bretbouchard/kicad-agent/.planning/phases/233-swift-schematic-svg-renderer/233-01-PLAN.md

---
phase: 233
plan: 01
title: Swift-native schematic SVG renderer
type: execute
wave: 1
depends_on: []
autonomous: true
files_modified:
  - macos-app/Sources/Volta/Rendering/
  - macos-app/Sources/Volta/Views/InlineRendering/SchematicPreviewView.swift
must_haves:
  - Swift SVG renderer emits valid SVG for any .kicad_sch
  - Live preview updates as user edits (no kicad-cli dependency)
  - Renders symbols, wires, labels, power symbols
---

# Plan 233-01: Swift Schematic SVG Renderer

<objective>
Replace the kicad-cli-dependent SVG export with a Swift-native renderer.
The macOS app should be able to render any schematic entirely on-device,
without shelling out to kicad-cli. Required for App Store sandbox
compatibility (gap F1 in GAP-ANALYSIS-CURRENT.md).

## Approach

1. Audit existing `macos-app/Sources/Volta/Views/InlineRendering/SwiftSVGRenderer.swift`
2. Confirm coverage: symbols, wires, labels, power symbols, hierarchy
3. Wire into `SchematicPreviewView` for live preview
4. Add regression tests for representative schematics
5. Verify no kicad-cli subprocess calls in renderer path

## Status

SwiftSVGRenderer.swift exists from Phase 238 sweep. Audit + wire-up
work is small.
