bretbouchard/kicad-agent/.planning/phases/237-safe-sync-pcb-from-schematic/237-01-PLAN.md

---
phase: 237
plan: 01
type: execute
wave: 1
depends_on: []
files_modified:
  - macos-app/Sources/Volta/Parsing/VoltaEngineRemaining.swift
  - macos-app/Sources/Volta/Parsing/PCBParser.swift
  - macos-app/Sources/Volta/State/OpJournal.swift
autonomous: true
requirements:
  - SYNC-01
  - SYNC-02
  - SYNC-03
must_haves:
  truths:
    - safe_sync_pcb_from_schematic diffs the schematic against the PCB and replays changes
    - Footprint additions, removals, moves, and value updates propagate from .kicad_sch to .kicad_pcb
    - Op journal records the sync as a single transaction with one-shot rollback
  artifacts:
    - path: macos-app/Sources/Volta/Parsing/VoltaEngineRemaining.swift
      provides: "safe_sync_pcb_from_schematic returns a real diff + replay, not a stub message"
    - path: macos-app/Sources/Volta/Parsing/SchematicPcbDiffer.swift
      provides: "Diff algorithm matching components by reference, applying net/footprint changes"
  key_links:
    - from: SchematicPcbDiffer
      to: PCBParser
      via: "reads current PCB, compares to schematic, emits mutation ops"
    - from: VoltaEngineRemaining.swift
      to: OpJournal
      via: "journals sync as a transaction so the user can undo one-shot"

<threat_model>
## Trust Boundaries
| Boundary | Description |
|---|---|
| local filesystem | KiCad files are user-owned; no trust boundary |
| LLM-emitted op sequence | Sync may be triggered by a chain of chat ops; no new attack surface |

## STRIDE Threat Register
| Threat ID | Category | Component | Disposition | Mitigation Plan |
|---|---|---|---|---|
| T-237-01 | Tampering | PCB diff emit | Mitigate | Verify footprint placement bounds before applying move |
| T-237-02 | Repudiation | sync transaction | Mitigate | Journal records before/after SHA for audit |

## Stupid-Proof Verification
- User-stupid: undo is one-shot (no partial-rollback damage)
- Magic-stupid: chat-driven sync produces a visible before/after diff
</threat_model>

<context>
## Why this exists
Gap A2 from GAP-ANALYSIS-CURRENT.md. `safe_sync_pcb_from_schematic` is currently a stub returning a placeholder message (VoltaEngineRemaining.swift:933-942). Without a working sync, the iterate loop is broken: the user can edit the schematic but the PCB stays stale. This kills the "describe → refine → ship" flow.

## Background
Phase 235 was marked Complete on 2026-07-14 but did not actually implement this op. The current op just parses the PCB and returns a message saying "full sync requires schematic+PCB pair."

## Scope (in)
- A diff algorithm that takes (schematicIR, pcbIR) and emits a sequence of atomic PCB mutations
- Mutate: footprint add/remove/move (by ref), net rename, value update
- Journal the whole sync as one transaction (one-shot undo)
- Wire into VoltaEngineRemaining.swift's safe_sync_pcb_from_schematic

## Scope (out)
- Hierarchical sheet sync (Phase 2 follow-up)
- Annotation re-numbering sync (already in `safe_annotate`)
- DRC re-validation post-sync (the user runs DRC explicitly)
</context>

<tasks>

### Task 1: SchematicPcbDiffer
**Files:**
- `macos-app/Sources/Volta/Parsing/SchematicPcbDiffer.swift` (new, ~200 LOC)

**Implementation:**
- Inputs: `SchematicIR` (components + nets) and `PCBIR` (footprints + tracks + vias)
- Match components by reference designator
- For each mismatch, emit one of:
  - `.addFootprint(ref, footprint, position, value)` if schematic has it but PCB doesn't
  - `.removeFootprint(ref)` if PCB has it but schematic doesn't
  - `.moveFootprint(ref, position)` if positions differ
  - `.updateValue(ref, value)` if values differ
  - `.updateNet(pin, net)` if pin-to-net mapping changed
- Output: `[DifferOp]`

**Tests:** Property tests with synthetic (schematic, pcb) pairs.

### Task 2: Sync executor
**Files:**
- `macos-app/Sources/Volta/Parsing/SchematicPcbSync.swift` (new, ~150 LOC)

**Implementation:**
- Open a journal transaction
- Apply each `DifferOp` via the existing op registry (`add_footprint`, `move_footprint`, etc.)
- On any failure: roll back the transaction, return the error
- On success: return the diff summary `{added, removed, moved, valueUpdated, netUpdated}`

### Task 3: Wire into safe_sync_pcb_from_schematic
**Files:**
- `macos-app/Sources/Volta/Parsing/VoltaEngineRemaining.swift:933-942`

**Implementation:**
- Replace the stub `execute` body with: read schematic + PCB, run Differ, run Sync, return summary
- Make sure the fileURL points at the PCB and params include `schematic_path` for the schematic file

### Task 4: Tests
**Files:**
- `macos-app/Tests/VoltaTests/SchematicPcbDifferTests.swift` (new)
- `macos-app/Tests/VoltaTests/SchematicPcbSyncTests.swift` (new)

**Coverage target:** 80% on the new files.
</tasks>

<verification>
## Success Criteria
1. Chat-driven op: "I changed R1 to 4.7k in the schematic" → `safe_sync_pcb_from_schematic` updates the PCB R1 footprint's value field, returns `{valueUpdated: 1}`
2. Sync is journaled as one transaction: `undo` reverts the entire sync atomically
3. Test coverage ≥80% on the new files
4. No regressions in existing op tests
</verification>
