bretbouchard/kicad-agent/.planning/phases/233-swift-schematic-svg-renderer/233-01-SUMMARY.md

# Phase 233 — Swift Schematic SVG Renderer Summary

**Date:** 2026-07-15
**Plan:** 233-01-PLAN.md
**Status:** PLANNED

## Status

Plan created. SwiftSVGRenderer.swift exists from Phase 238 sweep; needs
audit + wire-up work. Estimated 1-2 days.

## Next steps

- Audit SwiftSVGRenderer.swift for coverage
- Wire into SchematicPreviewView for live preview
- Add regression tests
- Verify no kicad-cli subprocess calls

## Resolution state

PLANNED — ADDED-AS-PHASE
