bretbouchard/kicad-agent/.planning/STATE.md

---
gsd_state_version: 1.0
milestone: v11.0
milestone_name: — Gap-Closure Phases
status: planning-complete
stopped_at: Phase 253 routing plugin system — execution-ready (Volta Component Integration v8.0 active)
last_updated: "2026-07-28T03:00:00.000Z"
last_activity: 2026-07-28
progress:
  total_phases: 31
  completed_phases: 21
  total_plans: 24
  completed_plans: 22
  percent: 92
---

# Project State

## Project Reference

See: .planning/PROJECT.md (updated 2026-07-10)

**Core value:** LLM -> intent JSON -> AST mutation -> valid KiCad file. Zero corruption, every time.
**Current focus:** Phase 247 — gap-closure (next)
Last activity: 2026-07-15 — Phase 246 complete (DONE)

## Integration Status (Honest)

### What works end-to-end (App Store sandbox-compatible)

- ✅ Chat → LLM router → streaming tokens (Phase 211)
- ✅ Messages persist to SwiftData (Phase 211)
- ✅ Daemon operations from chat (Phase 212)
- ✅ KiCad file import + UTI registration (Phase 213)
- ✅ Inline rendering via DaemonPreviewRenderer (Phase 214)
- ✅ Settings tabs for Memory + Collaboration (Phase 215)
- ✅ **Native ERC/DRC validation panel** (Phase 216 + 218) — no kicad-cli
- ✅ 355 Swift tests pass, 0 fail (Phase 217)

### The kicad-cli dependency is ELIMINATED (Phase 218)

- Native ERC engine: pin-type conflicts (11×11 matrix), power net validation,
  no-connect validation, dangling wires — all pure Python

- Native DRC engine: copper spacing, netclass width, min track width,
  courtyard overlap, hole-to-hole, annular ring — all shapely geometry

- Advanced DRC: net-tie handling, thermal spokes, matched-length groups,
  diff pair coupling, teardrop detection, custom DRC rule evaluator

- 18 checks total + 50 existing DFM checks = 68 checks
- Batch tested: 50/50 schematics pass against kicad-cli ground truth
- 3 super-passes (found real errors kicad-cli missed)

### What's wired but needs external setup

- CloudKit sync: requires CK_CONTAINER_ID env var
- MLX generation: requires ~8GB model download on first launch from HuggingFace
- Schematic SVG export / PCB render: requires kicad-cli in non-sandboxed builds

### Test count: 355 Swift pass, 0 fail. 212 Python daemon tests pass. 68 sim tests pass.

## Current Position

**OVERRIDE STATE:** Buzz team's Volta Component Integration v8.0 takes priority over 247 gap closure.
Phase: 251 (Mouser API Integration) — PLANNING — standalone component provider system
Plan: 1 of 2
Status: Executing /gsd-plan-phase 251. Buzz team platform work refactored into GSD process.

## 2026-08-17 through 2026-08-18 Phase 2 Platform Migration Status

- Python-side M2.3/M2.4 groundwork is live: governed object identity,
  evidence-aware verification/manufacturing wrappers, and the shared
  `VoltaPlatformRuntime` are embedded into the playground/runtime path.
- Cross-repo proof exists in `integration/gsa-platform-proof/` and passes
  against local `apps/gsa-platform`, proving downstream import plus the
  governed revision→artifact scenario shape.
- Pre-existing Swift routing test debt that blocked app-side migration was
  fixed on 2026-08-17:
  - duplicate `MockProcessRunner` collision removed
  - fixture lookup made bundle-independent
  - Freerouting test setup now stages real temp JAR/DSN inputs
  - production crash fixes landed in `DSNConverter` and
    `FreeroutingProvider.parseMetrics`
- Live app embedding is now present in `macos-app`:
  - local `gsa-platform` dependency added to SwiftPM and XcodeGen
  - `GSAPlatformHost` boots `Platform.boot(...)` at app launch
  - explicit storage/capability config uses
    `~/Library/Application Support/VoltaPCB/gsa-platform`
  - app-side tests prove boot + diagnostics snapshot creation
- Verification on 2026-08-17:
  - `swift test --filter 'KiCadCLIDetectorTests|FreeroutingProviderTests|FixtureBoardSmokeTests'`
    → 41 tests passed
  - `swift test --filter 'VoltaTests.GSAPlatformHostTests|KiCadCLIDetectorTests|FreeroutingProviderTests|FixtureBoardSmokeTests'`
    → 45 tests passed, including live host boot, governed board-release export, denied authority, expired authority, and shell-visible platform failure handling

### App-Owned Governed Flow

- `GSAPlatformHost` now owns a real governed consequential flow for Volta:
  board-release artifact export using GSA's packaged revision→artifact scenario
- Negative-path proofs also exist at the app layer:
  denied authority blocks export, and expired authority blocks export
- `AppRootView` surfaces GSA boot failures with a retry action so the
  embedded platform is operationally visible in the live shell
- `LiquidGlassShell` now routes the live Share action through the governed
  board-release export path instead of a placeholder share string:
  - the shell waits for `GSAPlatformHost` readiness, runs the governed export,
    and builds a real `CompletionSummary`
  - `VerifyView` now receives a live governed artifact URL and shares the
    actual exported file through `ShareLink`
  - the shell presents governed export failures to the operator with retry,
    keeping consequential release behavior visible rather than silent
- Extended app-side proof coverage on 2026-08-17:
  - `GovernedReleaseSummaryBuilder` maps the governed artifact flow into the
    existing completion-summary UI model
  - `LiquidGlassShell` trait tests now inject `GSAPlatformHost`, covering the
    live environment dependency introduced by the governed export path
  - `ValidationManager` now records governed verification evidence for live
    ERC/DRC runs through `GSAPlatformHost` and the validation panel surfaces
    gate/evidence/trace counts inline
  - app-side proof now covers the real validation-manager DRC workflow against
    the committed `simple_2layer_led.kicad_pcb` fixture, not only host-level
    evidence helpers
  - the governed verification and governed export paths now share a stable
    modeled-world board-release object reference owned by `GSAPlatformHost`
    instead of relying only on raw file-path claims
  - verification evidence claims, historian records, and export summary
    metadata are now object-scoped, giving the live shell its first concrete
    project/board object identity across verification → artifact release
- Verification on 2026-08-17:
  - `swift test --package-path macos-app --filter 'VoltaTests.GSAPlatformHostTests|VoltaTests.GSDConversationEngineTests|VoltaTests.LiquidGlassShellTests|VoltaTests.ApprovalGatesTests|KiCadCLIDetectorTests|FreeroutingProviderTests|FixtureBoardSmokeTests'`
    → 90 tests passed
  - `swift test --package-path macos-app --filter 'VoltaTests.GSAPlatformHostTests|VoltaTests.ValidationPanelTests|VoltaTests.GSDConversationEngineTests|VoltaTests.LiquidGlassShellTests|VoltaTests.ApprovalGatesTests|KiCadCLIDetectorTests|FreeroutingProviderTests|FixtureBoardSmokeTests'`
    → 92 tests passed

### 2026-08-18 governed-slice widening

- The live consequential path in `macos-app` now carries the full minimum
  M2.3 governed object set across verification, release export, and
  manufacturing handoff:
  - project
  - revision
  - schematic
  - sheet
  - component
  - net
  - pcb
  - footprint
  - bom
  - verification artifact
- `GSAPlatformHost` now upserts these identities directly into the shared
  modeled-world path used by the live shell rather than a sidecar-only proof.
- `GovernedReleaseSummaryBuilder`, `ValidationManager`, the validation panel,
  and `VerifyView` all expose the widened governed reference chain so the app
  UI reflects the same traceability the runtime records.
- Focused app-side verification on 2026-08-18:
  - `swift test --package-path macos-app --filter 'VoltaTests.GSAPlatformHostTests|VoltaTests.ValidationPanelTests|VoltaTests.GSDConversationEngineTests|VoltaTests.LiquidGlassShellTests|VoltaTests.ApprovalGatesTests|KiCadCLIDetectorTests|FreeroutingProviderTests|FixtureBoardSmokeTests'`
    → 94 tests passed
- The first app-side M2.4 external-provider boundary is now governed in the
  embedded GSA host:
  - `GSAPlatformHost.recordProviderAssemblyCheck(...)` records a read-only
    provider result for assembly availability as governed evidence plus
    historian trace
  - the first concrete subject is the existing JLCPCB assembly-data edge, kept
    deliberately read-only so the app proves provider-boundary traceability
    before any quote/order semantics are introduced
- Focused app-side verification after adding the governed provider boundary on
  2026-08-18:
  - `swift test --package-path macos-app --filter 'VoltaTests.GSAPlatformHostTests|VoltaTests.ValidationPanelTests|VoltaTests.GSDConversationEngineTests|VoltaTests.LiquidGlassShellTests|VoltaTests.ApprovalGatesTests|VoltaTests.JlcpcbApiProviderTests|KiCadCLIDetectorTests|FreeroutingProviderTests|FixtureBoardSmokeTests'`
    → 99 tests passed
- The same live component-search workflow now carries a second governed
  external-provider boundary:
  - `GSAPlatformHost.recordComplianceCheck(...)` records lifecycle, RoHS,
    and risk evidence for component compliance checks
  - `ComponentDetailView` exposes that governed compliance trace directly in
    the live app workflow instead of keeping it host-test-only
- The live KiCad import flow is now governed as exchange, not only chat
  context setup:
  - `GSAPlatformHost.recordImportedDesign(...)` records import evidence and
    historian trace for `.kicad_sch` / `.kicad_pcb` sources
  - `LiquidGlassShell.handleFileImport(...)` now records that governed import
    and surfaces the claim/evidence trace back into the conversation as a
    system message
- Focused app-side verification after adding governed compliance + governed
  import on 2026-08-18:
  - `swift test --package-path macos-app --filter 'VoltaTests.ComponentSearchViewTests|VoltaTests.GSAPlatformHostTests|VoltaTests.ValidationPanelTests|VoltaTests.GSDConversationEngineTests|VoltaTests.LiquidGlassShellTests|VoltaTests.JlcpcbApiProviderTests|KiCadCLIDetectorTests|FreeroutingProviderTests|FixtureBoardSmokeTests'`
    → 91 tests passed
- Follow-up gap logged on 2026-08-18:
  - `volta-2ji` tracks that `Platform.boot(...)` currently recovers modeled
    world state but not `EvidenceLedger` / `Historian` contents, so governed
    import evidence persistence across host reboot cannot be fully proven from
    Volta without an upstream `gsa-platform` export surface
  - Volta deliberately did not add local sidecar governance persistence for
    that trace, to avoid creating parallel governance infrastructure

### Remaining highest-value Phase 2 app work

- widen the same object-scoped governed chain into a consequential
  provider/compliance action beyond release export + manufacturing handoff
- reuse the existing provider/manufacturing surfaces to add one more real
  capability boundary instead of creating a local-only governance abstraction
- connect the new governed provider-check path to a live app-owned workflow
  so provider evidence is surfaced outside host-only tests
- widen the same live slice from governed release/handoff to richer
  manufacturing or external-provider capability paths

## Previous Milestone: v6.0 KiCad Agent — The Closed Box (COMPLETE)

All 43 phases (161-203) shipped across Tracks A–I. Track D UI (171-175), Track E Memory (176-180), Track F Generative (181-185), Track G Collaboration (186-190), Track H Quality (191-201), Track I Ship (202-203) all delivered. Phase 204 (Closed-Box Simulation Pipeline) shipped as parallel track. Model training in progress for refinement/polish.

Key shipped phases (details below in Accumulated Context):

- Phase 161: App Shell Foundation (SwiftUI app shell, SPM, macOS 27)
- Phase 162: Python Daemon Bundling (PyInstaller, 97 Python + 23 Swift tests)
- Phase 163: KiCad CLI Integration (detector + onboarding gate)
- Phase 164: LLM Provider Protocol (Apple/MLX/HF providers)
- Phase 165: Provider Router (task-aware, cost-aware, privacy-aware)
- Phase 169: Obdurate Runtime (WorkflowStateMachine, IntentGate, OpJournal)
- Phase 170: Verification Loop (PreOpGate, PostOpGate, Rollback, VerificationLoop)
- Phase 204: Closed-Box Simulation Pipeline (SKiDL → Optuna → ngspice → pytest)

## Phase 161 — App Shell Foundation (SHIPPED 2026-07-07)

**Files:** 17 created, 1,525 LOC
**Build:** `swift build` clean, zero warnings
**Tests:** 12/12 passing in 3 suites
**Deployment:** macOS 27.0 (verified via `otool LC_BUILD_VERSION minos 27.0`)
**Commit:** c064ecd1

**Architecture decisions:**

- SPM over .xcodeproj (simpler, macOS 27+ compatible)
- SwiftUI App protocol (no AppDelegate legacy)
- SwiftData in-memory now (Track E adds CloudKit)
- DaemonSupervisor `@MainActor @Observable` state machine (Phase 162 wires real spawn)
- swift-testing framework (TEST-01)
- Liquid Glass via `.background(.regularMaterial)` — `.glassEffect()` deferred to SDK 27

**Deviations:** `.macOS(.v27)` unavailable in SPM on Xcode 26.5 → fixed via unsafeFlags `-target arm64-apple-macosx27.0`. Binary ABI target verified `minos 27.0`.

See: `.planning/phases/161-app-shell-foundation/161-01-SUMMARY.md`

## Phase 162 — Python Daemon Bundling (SHIPPED 2026-07-07)

**Files:** 17 created, 2 modified, 3,427 LOC added
**Build:** PyInstaller binary builds + runs, `swift build` clean
**Tests:** 97/97 Python tests passing (0.47s) + 23/23 Swift tests passing
**Binary:** 82MB arm64 Mach-O, all dylibs code-signed (Pitfall 1 prevention)
**Commit:** 041b4095

**What shipped:**

- Bundled Python daemon speaking JSON-RPC 2.0 over stdio
- 4 focused modules: protocol.py, handlers.py, audit_log.py, daemon_entry.py
- ProcessManager.swift (482 LOC) + DaemonMessenger.swift (216 LOC) — Swift integration
- DaemonSupervisor wired to real ProcessManager (removes Phase 161 stub)
- 151 volta operations exposed via list_operations
- All stupid-proof augmentations: APP-03 checksum, APP-05 SIGTERM→SIGKILL, DAEM-01/05 wake health check, DAEM-02 unbuffered stdout + 30s watchdog, DAEM-06 crash-loop halt

**Architecture decisions:**

- Module split per project rule (MANY SMALL FILES > FEW LARGE FILES) — 386 LOC monolith → 4 files of 163-295 LOC
- Ad-hoc codesigning for dev; Fastlane match (Phase 203) supplies production identity
- PyInstaller one-folder COLLECT mode — faster cold start than one-file
- audit_log default sink is stderr; Phase 168 wires per-project file for cross-process durability
- Health method alias: both 'health' and 'health_check' resolve to same handler
- ProcessManager dev-mode fallback: `.venv/bin/python -u daemon_entry.py` for fast iteration

**Deviations:**

- [Rule 1 Bug] OPERATIONS → OPERATION_REGISTRY (handlers.py tolerates both)
- [Rule 2 Missing] Module split for testability (per project coding-style rule)
- [Rule 2 Missing] PyInstaller hidden imports for new modules
- [Rule 3 Blocking] Stale git index.lock removed

See: `.planning/phases/162-python-daemon-bundling/162-01-SUMMARY.md`

## Phase 163 — KiCad CLI Integration (SHIPPED 2026-07-07)

See commit `d33ec8c8`. KiCad CLI detector + onboarding gate. APP-04 augmentation: main workflow blocked until status is `.ready`.

## Phase 164 — LLM Provider Protocol (SHIPPED 2026-07-07)

**Files:** 20 created, 1 modified (Package.swift), 1928 LOC
**Build:** `swift build` clean, zero warnings
**Tests:** 39 new across 5 suites (KiCadModelProvider Protocol, AppleLocalProvider, MLXLocalProvider, HFHubModelCatalog, ProviderBanner) — all passing
**Commits:** `43fdfdd0` (Task 1 — protocol + types), `37602367` (Tasks 2-6 — providers + UI + tests)

**Architecture decisions:**

- KiCadModelProvider protocol — only model interface (MOD-01 lock). SDK types never leak through KC* value types. Compiler-enforced via test.
- Protocol uses non-generic `generateJSON<T: Decodable>` (not associated types) so providers fit in heterogeneous arrays.
- AppleLocalProvider — real FoundationModels streaming via `LanguageModelSession.streamResponse`. Per-request session allocation. Pitfall 3 prevention: availability probed via `SystemLanguageModel.default.availability` returning `.deviceNotEligible | .appleIntelligenceNotEnabled | .modelNotReady` — never via device model detection.
- MLXLocalProvider — real MLX-Swift integration (MLX+MLXNN 0.31.6 SPM deps). Pitfall 7 prevention: `MTLCreateSystemDefaultDevice().recommendedMaxWorkingSetSize` with 3GB floor. Real safetensors load via `MLX.loadArraysAndMetadata` (T-164-01 supply-chain mitigation). Architecture whitelist (gemma3, llama, qwen, phi, mistral, starcoder2). Generation loop deferred to Phase 165 — SLC-correct boundary.
- HFHubModelCatalog — 7 curated recommended models (Gemma 3 4B/12B, Qwen 2.5 7B/14B, Phi 3.5 mini, Llama 3.2 1B/3B). Real HF API parsing.
- ProviderRegistry — ObservableObject for environment injection. `defaultProvider()` returns Apple first (MOD-06), then MLX, then any local, then cloud. `register(_:)` is Phase 166 BYOK entry point.
- ProviderBanner — three states (hidden / localOnlyMode / noProvidersAvailable). "Add API Key" deep-link slot for Phase 166.

**Deviations:**

- [Rule 3 Blocking] `MLXLM` product not in mlx-swift package — lives in mlx-swift-extras. Added MLX+MLXNN only. Scoped generation loop to Phase 165.
- [Rule 3 Blocking] Swift 6 `Mutex<T>` is non-Copyable, can't be stored in Copyable struct. Replaced with small private actor for metadata cache.
- [Rule 3 Blocking] `NSLock.lock()` unavailable from async context. Replaced with private actor Counter in MockProvider.

See: `.planning/phases/164-llm-provider-protocol/164-01-SUMMARY.md`

## Phase 165 — Provider Router (SHIPPED 2026-07-08)

**Files:** 10 created, 1 modified (MockProvider), ~1900 LOC
**Build:** `swift build` clean, zero warnings
**Tests:** 59 new across 4 suites (KiCadModelRouterTests, KCTaskClassifierTests, KCCostLedgerTests, ProviderRoutingSettingsViewTests) — all passing
**Commit:** `a57eebbb`

**What shipped:**

- `KiCadModelRouter` — task-aware, cost-aware, privacy-aware routing per MOD-02:
  - Privacy override: privacySensitive tasks ALWAYS AppleLocal (wins over user prefs, vision requirements, task defaults)
  - Vision priority: cloud vision-capable → MLX Gemma vision → AppleLocal with one-time notification
  - Complex reasoning: MLX local (cost $0) → AppleLocal fallback per MOD-11
  - Quick replies / board analysis / conversation history: AppleLocal (free, fast)
  - User preference checked before defaults (MOD-10); unavailable preferred falls back to AppleLocal with one-time notification
- `KCTask + KCTaskClassifier` — prompt → task type via keyword heuristics (privacy/vision/generation/routing/analysis/summarization keywords + complexity ramp from prompt length)
- `KCCostLedger` — append-only ledger with per-message entries, today/thisWeek/allTime range queries, per-provider breakdown, runaway-spend threshold ($1000 default per T-165-03), Decimal for all currency (Pitfall 6)
- `KCRoutingNotifier` — one-time-per-shape (preferredKind, fallbackKind, taskType) fallback notifications via NotificationCenter
- `ProviderRoutingSettingsView` — privacy mode toggle + per-task preferred-provider pickers + cost ledger summary (today/week/all-time + per-provider) + reset preferences + clear ledger actions + runaway spend banner
- `MockProvider.kind` promoted to var + init parameter so tests can impersonate any KCProviderKind

**Architecture decisions:**

- Task classification uses keyword heuristics (not LLM) — routing must be O(1) and free
- KCCostLedger is @MainActor ObservableObject — main-actor isolation for UI re-renders without hop overhead
- KCRoutingNotifier uses NSLock (not actor) — NotificationCenter dispatches observers synchronously on its queue, actor methods would deadlock
- Preferences persisted via UserDefaults JSON blob (Phase 166+ migrates to SwiftData)
- `loadPersistedPreferences: Bool = true` init param lets tests bypass UserDefaults bleed-through
- Privacy override is unconditional — wins over user preferences and task type
- User-facing categories (quickReply, complexReasoning, vision, privacySensitive) drive preference lookup; internal pipeline stages (circuitGeneration, pcbRouting, boardAnalysis, conversationHistory) map onto them via `KCTaskType.preferenceCategory`

**Deviations:**

- [Rule 1 Bug] Plan file paths mismatched actual SPM structure — used Phase 164 paths as source of truth
- [Rule 1 Bug] `Logger.warn` → `Logger.warning` (OSLog API)
- [Rule 1 Bug] `Range<Date>?` → `summary(from: Date?, named:)` to match PartialRangeFrom call sites
- [Rule 1 Bug] @MainActor class leaked isolation into `KCRoutingPreferences.default` — moved constant to non-isolated namespace
- [Rule 1 Bug] `KCRoutingNotificationPayload` field order mismatched init call — reordered struct fields
- [Rule 1 Bug] `@Bindable` requires @Observable macro — switched to @ObservedObject (Phase 164 uses ObservableObject)
- [Rule 1 Bug] init overwrote explicitly-passed preferences with UserDefaults — added `loadPersistedPreferences` flag
- [Rule 1 Bug] Actor-isolated capture boxes deadlocked notification observers — replaced with NSLock-based classes
- [Rule 1 Bug] MockProvider.kind was `let` — promoted to `var` + init param
- [Rule 3 Blocking] Precondition failure tests aborted the test runner — removed negative-case coverage

See: `.planning/phases/165-provider-router/165-01-SUMMARY.md`

## Phase 169 — Obdurate Runtime (SHIPPED 2026-07-08)

**Files:** 10 created + 1 modified (MCPClient.swift), 2,902 LOC (1,983 source + 919 tests)
**Build:** `swift build` clean, zero warnings
**Tests:** 47 new across 8 suites (WorkflowStateMachineTests, IntentGateTests, OpJournalTests, EscalationLadderTests, FindingResolutionTests, AutoLearnerTests, RequirementCoverageTests, DriftDetectorTests) — all passing
**Total:** 210/210 tests pass in full suite
**Commit:** `f498e5d0`

**What shipped:**

- WorkflowState + WorkflowStateMachine: GSD transition table (questioning → specGenerated → roadmapApproved → executing → verifying → complete) with hard guards — review→execute needs planApproved, verifying→complete needs verificationPassed. GOV-02.
- IntentGate: validates every op against catalog, requires non-empty requirementId on mutating ops (GOV-07), sanitizes secrets (password/token/api_key prefixes redacted). Static op catalog mirrored from Python `ops/registry.py` for 23 common ops. GOV-01.
- OpJournal: JSONL+fsync append-only audit trail at `~/Library/Application Support/Volta/journal.jsonl`. Mirrors Python `routing/audit.py` H5 pattern with truncated-line recovery. Queryable by op, requirement, actor, date, operationId. GOV-06.
- DriftDetector: compares target files against approved scope per requirementId. Permissive (warn) by default, strict mode rejects. GOV-07.
- EscalationLadder: T1 (1 failure) → T2 (2+) → T3 (3+) → T4 (5+) per bureaucracy.md §4. Posts `kcEscalation` notification synchronously on tier increase. `humanInputRequired()` at T4. GOV-08.
- FindingResolution: four-state taxonomy (IMPLEMENTED / ADDED-AS-PHASE / SUPERSEDED-BY-ALTERNATIVE / DEFERRED-TO-NAMED-TARGET). P0/P1 cannot defer. Validates evidence requirements per state. GOV-09.
- AutoLearner: JSONL+fsync pattern/error_message store at `~/Library/Application Support/Volta/learnings.jsonl`. Queryable by op for similar-success / similar-failure retrieval. GOV-10.
- RequirementCoverage: report generator from IntentGate.catalog. Validates every op mapped + every declared GOV requirement covered. GOV-11.
- GovernedCall + MCPClient.governedCall<T>: full pipeline IntentGate → DriftDetector → WorkflowStateMachine → MCPClient.call → OpJournal.append → AutoLearner.store → EscalationLadder.recordSuccess. Failures journal + escalate + auto-learn. Rejects journal with `result_status="rejected"` before throwing.

**Architecture decisions:**

- Swift-side governance layer, not Python — user task spec described Swift deliverables; plan file's Python paths superseded
- Op catalog hardcoded in Swift (Phase 170 replaces with dynamic tools/list from MCP daemon)
- Notifications posted synchronously, not via DispatchQueue.main.async — async dispatch loses notifications under test runloops; synchronous posting is safe because observers are lock-protected
- NSLock (not actor) for state machine — same pattern as KCCostLedger/KCRoutingNotifier (Phase 165)
- Stripped public modifiers from Governance files — AnyCodable (MCPProtocol.swift) is internal-only and Volta is an executable target (no public API surface)

**Deviations:**

- [Rule 1 Bug] ResolutionValidationError.errorDescription referenced wrong binding (`severity` instead of `sev`)
- [Rule 1 Bug] Public modifiers conflicted with internal AnyCodable — stripped all `public` from Governance files
- [Rule 1 Bug] NSLock.unlock() unavailable from async context in EscalationLadderTests — switched to actor Collector
- [Rule 1 Bug] Notification lost under test runloop — switched from `DispatchQueue.main.async` to synchronous post
- [Rule 1 Bug] IntentGate catalog default masked explicit empty requirementId — added explicit empty-string check before resolver

See: `.planning/phases/169-obdurate-runtime/169-01-SUMMARY.md`

## Phase 170 — Verification Loop Integration (SHIPPED 2026-07-08)

**Files:** 11 created + 3 modified, ~1700 LOC (940 source + 760 tests)
**Build:** `swift build` clean, zero warnings
**Tests:** 50+ new Swift across 4 suites (PreOpGateTests, PostOpGateTests, RollbackTests, VerificationLoopTests) + 26 new Python across 2 suites (test_snapshot.py, test_verification_handlers.py) — all passing
**Total:** 211/211 Swift tests pass in full suite
**Commit:** `7b367635`

**What shipped:**

- PreOpGate (@MainActor): validates intent matches op + target file types. Calls daemon `kicad.pre_check`. Read-only ops short-circuit (allow). Returns PreOpDecision {allow, warn, block} with reasons + per-check map. GOV-03.
- PostOpGate (@MainActor): runs deterministic ERC/DRC check (via `kicad.post_check` wrapping `validation/erc_drc.py`) + optional SemanticJudge LLM "did this achieve intent?" Returns PostOpDecision {passed, failed, indeterminate}. Decision composition: failed deterministic → .failed; indeterminate → .indeterminate; passed + LLM says no → .failed (semantic veto). GOV-04.
- Rollback (@MainActor): `checkpoint(files:)` calls daemon `kicad.snapshot` → returns Checkpoint with snapshot_id. `restore(checkpoint:)` calls daemon `kicad.restore` → returns RestoreResult {restored, removed, skipped}. Sentinel IDs for empty/no-client test mode. GOV-05.
- VerificationLoop (@MainActor): orchestrates checkpoint → preCheck → execute → postCheck → restore-on-fail. Returns VerificationOutcome with status, pre/post results, checkpointId, restore summary, per-stage timings.
- MCPClient.governedCall rewired: after IntentGate → DriftDetector → StateMachine → EscalationLadder checks, VerificationLoop runs the actual op. Outcome status maps to journal `result_status`: passed → success; indeterminate → success (verification nil); blocked → rejected; executionFailed → failed; failed → rolled_back + escalation + auto-learn.
- daemon/snapshot.py: atomic per-file Snapshot.create/restore with content-addressed blob dedup. Path-traversal defense (T-170-06): refuses '..' segments + optional base_dir containment. Missing files tracked as "remove-on-restore".
- 4 new daemon MCP handlers: kicad.pre_check (op_known + file_type_ok + args_present), kicad.post_check (runs run_erc on .kicad_sch, run_drc on .kicad_pcb, aggregates), kicad.snapshot (wraps Snapshot.create), kicad.restore (looks up snapshot by UUID, calls Snapshot.restore).

**Architecture decisions:**

- Gates are @MainActor (not @unchecked Sendable) to share MCPClient's actor isolation — avoids [String: Any] sendability crossings on params dicts
- snapshot.py uses tempfile.mkstemp in target parent dir for atomic per-file restore via os.replace (crash leaves either old or new, never torn)
- Snapshot failures are non-fatal: op proceeds but loses rollback; post-op failure surfaces as .failed without restore. Journal records it for audit.
- SemanticJudge is a minimal 3-field protocol so Phase 173 can wire it to KiCadModelProvider router; Phase 170 ships NoSemanticJudge default so deterministic checks run independently
- Three plan tasks delivered as one atomic commit since VerificationLoop can't be tested in isolation without all three gates

**Deviations:** None — plan executed exactly as written.

See: `.planning/phases/170-verification-loop-integration/170-01-SUMMARY.md`

## Phase 204 — Closed-Box Simulation Pipeline v1 (SHIPPED 2026-07-07, parallel track)

**Files:** 6 source modules in `src/volta/sim/` (eurorack.py, dataframe.py, bom.py, plot.py, optimizer.py, __init__.py) + 8 test files in `tests/sim/` + `scripts/demo_closed_box.py` (136 LOC) + Phase 158 2N3904 model + `[sim]` extras in pyproject.toml
**Build:** `.venv/bin/python -m pytest tests/sim/ tests/spice/ -q` — 64/64 passing
**Tests:** 64 total (was 18 pre-ngspice). All BLK-1 strict, no skip-guards.
**Demo:** `python3 scripts/demo_closed_box.py` exit 0 — gain_db=19.84 (target 20±3), bandwidth 104 MHz, bode.png 45.7 KB, bom.md 8 E12 parts
**External dep:** `brew install ngspice` (macOS) / `apt install ngspice` (Linux)
**Council:** Gate 1 R2 APPROVE (1 P0 + 3 P1 fixed). Gate 2 EXEC REVIEW APPROVE (0 critical/high/medium, 5 LO with four-state resolution).

**What shipped:**

- THE primary new capability: `circuit_to_spice_netlist()` — skidl.Circuit → SPICE .cir bridge (skidl 2.2.3's `generate_netlist()` emits KiCad .net, NOT SPICE)
- Optuna GPSampler optimizer with E12 R/C categorical constraints, 10s trial timeout, current-saturation guard, determinism seed
- pandas DataFrame adapter for `SimulationResult`
- BOM markdown generator (skidl 2.2.3 has no `circuit.BOM()`)
- matplotlib Bode plot (magnitude-only in v1; phase stub per WR-04)
- End-to-end magic demo: intent → Optuna sweep → ngspice verify → assert → bode.png + bom.md

**Architecture decisions:**

- `src/volta/sim/` as sibling to (not child of) `src/volta/spice/` — clean separation between "run a SPICE sim" (Phase 158) and "optimize + analyze + demo a SPICE sim" (Phase 204)
- ngspice CLI subprocess (NOT PySpice — dead project per memory pyspice-dead-use-ngspice-cli)
- Optuna GPSampler (4.5+, shipped Aug 2025) for BO over E12 categorical space
- `_ensure_skidl_env()` called at module top + per-call (CR-01 Phase 156 pitfall #6 guard)
- BLK-1 strict test pattern — autouse `_require_ngspice` fixture uses `pytest.fail(pytrace=False)`, never `pytest.skip`

**Deviations:**

- [Rule 1 Bug] VCC/VEE emission added to `circuit_to_spice_netlist` after debug session (transistor had no bias, gain ≈ 0 dB)
- [Rule 1 Bug] RLOAD DC path added to `generate_ac_testbench` after debug session (coupling cap blocked DC, ngspice singular matrix)
- [Rule 1 Bug] Default `freq_stop` extended 10 MHz → 1 GHz after debug session (CE bandwidth lands in 1-50 MHz range, was outside sweep)
- [Rule 2 Missing] ngspice not bundled — external CLI dep, documented in README + CLAUDE.md
- [Rule 3 Blocking] Stale git index.lock removed during planning

**Bug reports (7 total, all RESOLVED):**

- `volta-e2b` (P3): RESOLVED. Default trials reduced from 50 to 20 (~100s total).
- `volta-obp` (P3): RESOLVED. AC parser uses spicelib.RawRead on .raw binary, not regex.
- `volta-233` (P4): RESOLVED. Optuna sqlite storage in stable user-data dir.
- `volta-qss` (P4): RESOLVED. Bode phase plots real vp(out) from RawRead.
- `volta-w1f` (P4): RESOLVED. TL072 JFET-input buffered preamp gives real 1 Mohm input Z.
- `volta-cjl` (P4): RESOLVED. 2N3904 model room-temp limitation documented.
- `volta-8vv` (P4): RESOLVED. .OP parser added to ngspice_runner.

**Strategic impact:**

- v6.0 "KiCad Agent — The Closed Box" milestone has its keystone — Python/SKiDL analog magic proven end-to-end
- Matches tscircuit competitor pressure (TypeScript/browser HMR bar) for analog circuits
- Establishes canonical template for future analog topologies (LM13700 VCA, AS3340 VCO, Sallen-Key VCF)

See: `.planning/phases/204-closed-box-simulation-pipeline-v1-skidl-spice-optuna-pytest-/204-04-SUMMARY.md` (and 01-03)

## Backlog (next milestone)

Phase 108 (Deterministic Autolayout Engine) — **RESOLVED.** All 108-T2 commits merged to master. `auto_layout_sch` op registered, 56 autolayout tests pass. Branch `phase-108-task2-on-page-guarantee` was merged and deleted. The "IN REVIEW" status was a stale handoff note — the work is complete.

Phases 156-160 (v5.0 Skidl-Native) — Absorbed into v6.0 Track F (Generative). Work continues as part of Mac app's generative pipeline rather than standalone library milestone.

Phase 156 (SKIDL Converter) — not started (roadmap defined). Absorbed into v6.0 generative pipeline.

## Previous Milestone (v3.0 Full-Stack EDA)

**Final: 54/54 phases complete. 143 plans, 3171+ tests, constraint propagation, spatial intelligence, layout-aware placement, DRC intelligence, DFM.**

## Previous Milestone (v2.4 Schematic Intelligence)

**Final: 40/40 phases complete. 85 operations, 2343+ tests, structured logging, training infra, schematic routing.**

## Previous Milestone (v2.4 production-hardening)

**Final: 37/37 phases complete. 74 operations, 1900+ tests, structured logging, training infra.**

## Performance Metrics

**Velocity:**

- Total plans completed: 175
- Average duration: 5 min
- Total execution time: 6.5 hours

**Recent Trend:**

- Last 10 plans: 50-01 through 54-02 (all first-execution pass)
- Trend: Stable -- all plans passing on first execution

## Accumulated Context

### Roadmap Evolution

- Phase 80 added: Spatial Reasoning Model Benchmark — evaluate 0.5B/1.5B on 6 coordinate-grounded task categories
- Phase 81 added: Post-Routing Gap Analyzer — deterministic gap identification on partially-routed PCBs
- Phase 82 added: AI-Powered Gap Filling Engine — AI-assisted fixes using existing 98 operations
- Phase 83 added: analog-ecosystem Integration — unified routing workflow replacing per-board custom scripts
- Phase 84 added: Model Upgrade (Conditional) — train larger model if benchmark shows insufficiency
- Phase 95 added: Dual Knowledge Base Integration — Cognee ingestion + section injection for local model prompts
- Phase 98 added: Closed-loop vision-guided PCB routing — wire trained V2 LoRA into pathfinder-driven routing loop with eval harness
- Phase 98 REFRAMED: AI Routing Strategy Advisor — vision model emits strategy consumed by Phase 100 orchestrator (closed-loop approach replaced by Option A architecture: Freerouting + orchestrator + AI advisor)
- Phase 99 added: Freerouting Integration Hardening — replaces conceptual Phase 122B; closes real multi-layer gaps (footprint obstacles, net classes, zones, via types, 45° traces). Multi-layer graph scaffolding already exists in graph.py:156-247
- Phase 100 added: RoutingOrchestrator and Human Approval Loop — dispatcher routes nets to A* vs Freerouting, defines RoutingStrategy interface that Phase 98 plugs into, extends InteractiveRoutingSession for Freerouting output
- Phase 101 added: Schematic Ops Bug Fixes — close 5 P0/P1 bugs (P0-001 through P0-005) from analog-ecosystem backplane cleanup. BUGS/ reports source.
- Phase 102 added: Safe Annotate — non-destructive refdes renumbering. Implements `safe_annotate` op mirroring `safe_sync_pcb_from_schematic` raw S-expr edit pattern (never kiutils). Closes FEATURE-008 / unblocks analog-ecosystem Phase 145. Existing `annotate` op forbidden (P0-006).
- Phase 102.1 inserted after Phase 102: Close deferred work — EXEC-03 sort tie-break UUID, H-02 instances co-edit, H-03 real-world validation (URGENT — user-directed closure per four-state taxonomy)
- Phase 107 added: Schematic Legibility — Standards Research and Gap Audit. Industry standards research (IEEE 315, ANSI Y32.2, IEC 60617, signal-flow conventions, Horowitz & Hill, hierarchical design) + repo gap audit for best-in-class autolayout. Hybrid approach (deterministic engine + AI critic) preferred per v2.2 routing lessons. Current training lacks legibility objective. Phase 103-106 already in roadmap from routing overhaul — gsd-sdk saw filesystem only (no dirs for 103-106), so manually renumbered to 107 to avoid collision.
- Phase 108 added: Deterministic Autolayout Engine — Sugiyama-framework engine on Phase 38 schematic_routing primitives (~6,000 LOC). New `auto_layout_sch` op. Verification: SRS within 0.10 of human expert on Phase 93 golden boards (D-03). Depends on Phase 107.
- Phase 109 added: AI Legibility Critic — vision-model critic on autolayout output, scored against Phase 48.5 SRS. Model choice (Claude vision vs Gemma 4 12B V2 vs both with R-4) deferred to discuss-phase. Depends on Phase 108.
- Phase 110 added: GRPO Legibility Reward Signal — legibility term added to existing training/grpo.py. SFT path: real schematics (discover_100k.py). GRPO path: synthetic (training/generator.py). Depends on Phase 109.
- Phase 111 added: Convention Library — IEEE 315 + H&H as Python dataclasses (D-02 canonical core) + YAML overrides via Phase 48 RuleConfigLoader. New `Convention` ABC mirrors `DesignRule` ABC. Depends on Phase 107 (parallel-eligible with 108).
- Phase 156 added: SKIDL Converter — bidirectional KiCad↔SKIDL bridge. Builds the missing KiCad→SKIDL read-back path (SchematicIR + extract_nets → skidl.Circuit) and makes SKIDL→KiCad a first-class op. SKIDL becomes the canonical IR for all circuit operations (SchGen Code-L1 validation: 82% valid circuits vs 32% raw KiCad). Depends on Phases 108-111.
- Phase 157 added: Floor Planner — declarative YAML floor-plan spec (`.floorplan.yaml`) compiled by `apply_floor_plan` into existing `LayoutAwarePlacer` vectors. Post-populate, pre-Quilter stage. Depends on Phase 156 (module-aware hierarchy metadata).
- Phase 158 added: SPICE Pipeline — headless ngspice testbench pipeline (AC/transient/noise/THD) with structured JSON results as reward signal. Zero new deps (ngspice 45.2, spicelib, skidl+InSpice installed). Independent of Phase 156 (parallel-eligible).
- Phase 158 SHIPPED 2026-07-04 (commits 08c5e7a9, 46ed4b3b) — 5 files in src/volta/spice/, 14/16 tests passing (2 failures are ngspice-not-installed environment only). Retroactively closed 2026-07-07 with SUMMARY.md after audit revealed phase never got directory or formal tracking.
- Phase 159 added: AI Training Data — 71K repos → SKIDL + NL SFT pairs; placement→routing quality pairs; SPICE pre/post-route delta as reward signal. Qwen text + Gemma vision adapters. Depends on Phases 156, 157, 158.
- Phase 160 added: NL Circuit Generation — fine-tuned LLM generates SKIDL from NL → ERC → SPICE → floor plan → PCB → Quilter. Full pipeline to manufacturing (SchGen/pcbGPT stop at schematic). Depends on Phase 159.
- Phase 204 added: Closed-Box Simulation Pipeline v1 — SKiDL → spicelib SimRunner → Optuna sweep → pytest assertions → pandas DataFrames, proven end-to-end on common-emitter BJT amplifier auto-sized for target gain. Closes the three broken links in the v6.0 "Closed Box" vision (SPICE execution, circuit optimization, hardware-as-code tests). Uses existing spicelib 1.5.1 (NOT PySpice — dead project) + Optuna 4.5+ GPSampler + ngspice CLI subprocess.
- Phase 245 added: Wire Volta v2 LoRA adapter into macOS app — replace MLXLocalProvider placeholder with real PEFT inference on google/gemma-4-12b-it. Adapter at `output/volta-pcb-adapter-v2-upload/adapter_model.safetensors` (524MB, SHA256 cbc121cc... verified, 656 bfloat16 tensors across 48 layers, 7 target modules). Training: step 3000/3000, loss 0.0288, accuracy 98.66%, 48.5M tokens, A100 80GB, 19.2h, zero crashes. Instance 44774137 destroyed. Eval harness + additional gap closure to follow as separate phases.
- **Phase 245 DONE 2026-07-15**: 2 commits (942dcf0 feat, ca6ddb1 docs), HF repo live at `bretbouchard/volta-pcb-adapter-v2` with 7 files, 8/8 must-haves passed, Council APPROVED with 0 P0/P1 findings. MLXLLM TODO(245) graceful-degradation noted as known limitation.
- Phase 246 added: Python eval harness for Volta v2 — load adapter via peft+transformers, measure PCB generation quality on 50-sample held-out test set (ERC pass rate, syntactic correctness, schema completeness, BLEU/ROUGE vs gold). Output report + summary. Sets quality baseline before production rollout.
- **Phase 246 DONE 2026-07-15**: 7 commits (c7622b4 + 0c5c3af + 3 fix commits + 2 docs), 10/10 must-haves passed, 32/32 tests pass (28 original + 4 security regression tests), Council APPROVED with 0 P0/P1 findings. Sandbox locked down (CR-01: `__import__` whitelisted to skidl.* only), thread-based timeout enforcement (WR-01), SHA256 verification for adapter (WR-02), typo rename (IN-01). E2E inference run pending — needs vast.ai GPU + HF auth.
- Phase 247 added: Gap closure against docs/GAP-ANALYSIS-CURRENT.md — triage all open gaps with four-state taxonomy (IMPLEMENTED / ADDED-AS-PHASE / SUPERSEDED-BY-ALTERNATIVE / DEFERRED-TO-NAMED-TARGET). Includes MLXLLM TODO(245) follow-up, iOS/vision adapter gaps, real-inference E2E test gap.

### v4.1 Stage-Safe PCB Flow (Phases 85-94)

**Goal:** Enforce a credible schematic-to-manufacturing PCB workflow where each stage has deterministic readiness gates.

Planned phases:

- Phase 85: Gate Architecture (2 plans) — DesignStage enum, GateResult, GateRunner
- Phase 86: Schematic Intent Completeness (2 plans) — Footprint/pin-map/metadata/net intent
- Phase 87: Schematic-to-PCB Transfer Contract (2 plans) — Verified symbol→footprint→pad→net
- Phase 88: Constraint Capture & Propagation (2 plans) — Electrical/mechanical/fab constraints
- Phase 89: Placement Readiness Gate (1 plan) — 6 sub-checks
- Phase 90: Routing Readiness & Quality Gate (1 plan) — Pre/post-route gates
- Phase 91: Manufacturing Readiness Gate (1 plan) — Full package validation
- Phase 92: AI Boundary & Repair Loop (1 plan) — Proposal model, audit trail
- Phase 93: Golden E2E Boards (1 plan) — 6 fixture boards proving full flow
- Phase 94: Docs & UX (1 plan) — Stage-gate documentation

Total: 14 plans across 10 phases.

Priority: Start with Phases 85-87 (gate architecture + schematic intent + transfer contract) per document recommendation.

### v5.0 Skidl-Native Design Pipeline (Phases 156-160) — CURRENT

**Goal:** Build a bidirectional KiCad↔SKIDL bridge, floor planner, SPICE simulation pipeline, and AI training data generator. SKIDL becomes the canonical IR for all circuit operations. Enables natural language → circuit → simulation → floor plan → PCB → routing → manufacturing.

Planned phases (numbering continues from analog-ecosystem cross-repo for clarity):

- Phase 156: SKIDL Converter (10 reqs: CONV-01..10) — bidirectional KiCad↔SKIDL bridge; builds missing KiCad→SKIDL read-back. Depends on Phases 108-111.
- Phase 157: Floor Planner (9 reqs: FLOOR-01..09) — YAML `.floorplan.yaml` spec → `apply_floor_plan` lowering into LayoutAwarePlacer. Depends on 156.
- Phase 158: SPICE Pipeline (11 reqs: SPICE-01..11) — headless ngspice testbench (AC/tran/noise/THD) → JSON reward signal. Independent (parallel with 156).
- Phase 159: AI Training Data (7 reqs: TRAIN-01..07) — 71K repos → SKIDL+NL pairs; SPICE delta as reward. Depends on 156, 157, 158.
- Phase 160: NL Circuit Generation (5 reqs: NLGEN-01..05) — NL → SKIDL → ERC → SPICE → PCB → Quilter. Depends on 159.

Total: 5 phases, 42 requirements. Dependency graph: 156→157; 158 parallel; 159←{156,157,158}; 160←159.

Research basis: `STACK-SKIDL.md`, `ARCHITECTURE-FLOORPLAN.md`, `STACK-SPICE.md`.

Priority: Phase 156 (SKIDL Converter) and Phase 158 (SPICE Pipeline) can start in parallel — 156 is the keystone IR, 158 is independent. 157 follows 156. 159 follows all three. 160 is the capstone.

Key decisions (from PROJECT.md): SKIDL is the IR (SchGen Code-L1); two-model architecture (Qwen text + Gemma vision); SPICE results as reward signal (analog sub-circuits only); floor planner encodes engineering knowledge; full pipeline to manufacturing.

### Decisions

Decisions are logged in PROJECT.md Key Decisions table.
Recent decisions affecting current work:

- [Phase 98-03]: M-3 (Council) — evaluate_sc2 uses "matches or beats" semantics for SC-2. Ties count as wins: `<=` for via_count and total_trace_length_mm (lower better), `>=` for completion_pct (higher better). Aligns with CONTEXT.md:50 wording and avoids ambiguity where ai.via_count == det.via_count.
- [Phase 98-03]: M-4 (Council) — --json output includes `fallback_rate` diagnostic alongside `sc1_parse_success_rate`. Distinguishes "model failed to parse JSON" (SC-1 failure) from "orchestrator invoked R-6 deterministic safety net" (fallback_rate). Both are tracked so eval consumers can diagnose whether SC-1 failures are parse errors vs full AI path failures.
- [Phase 98-03]: run_drc returns (False, -1) sentinel on any failure — kicad-cli missing, timeout, or malformed report never crashes the eval harness (T-98-03-02 best-effort).
- [Phase 98-03]: load_ai_strategy is the ONLY function that loads the 23.8 GB model — isolated so unit tests never trigger it. Integration tests opt-in via @pytest.mark.integration + importorskip("mlx_vlm") + skipif(kicad-cli/adapter missing).
- [Phase 101-03]: place_missing_units dedup moved outside `if pos is None:` block — applies to ALL position sources (_find_position_for_unit output AND fallback). Nudge by +offset_x/+offset_y. Also fixed dry_run not populating _occupied_positions (was only in non-dry_run branch).
- [Phase 101-03]: place_no_connects_from_erc pin-type lookup uses _lookup_pin_type_with_tolerance helper (per-axis abs() within SNAP_TOLERANCE=0.01mm) replacing exact round(x, 2) dict keys. Removed dead pos_to_type dict. Default "passive" preserved for backward compat.
- [Phase 101-02]: update_symbols_from_library crash fixed via sym.entryName (not sym.name) at 2 sites — repair_components.py:152 (op's lookup) + symbol_mismatch.py:141 (Rule 1: sibling bug in _get_library_pin_signature on same code path, called by op at line 79 before its own lookup)
- [Phase 101-01]: erc_auto_fix + erc_auto_fix_hierarchical DEPRECATED via OpMeta field + runtime warning (not removed) — prevents ongoing KiCad 10 data-loss while raw S-expr rewrite is deferred
- [Phase 159, 2026-07-05]: SchGen→SKIDL conversion COMPLETED — pulled MS SchGen dataset (8,420 examples), AST-converted to SKIDL SFT pairs at /Volumes/Storage/schgen/converted/schgen_skidl_sft_filtered.jsonl (8,396 after filtering 24 empties). Critical insight: union-find on (sym,pin) not sym alone.
- [Phase 159, 2026-07-05]: Architecture PIVOT — original "two adapters (Qwen text + Gemma vision)" plan replaced with ONE Gemma 4 12B multimodal adapter trained on NL→SKIDL text + schematic/PCB images via instruction-tuning. User directive: "it should know them all".
- [Phase 159, 2026-07-05]: L1 vs L2 mode correction — PLAN.md said "L2 is the training representation" but L2 emits nets as comments. Switched to L1 mode which emits real `Net("name") += Part["pin"]` code.
- [Phase 159, 2026-07-05]: Batch SKIDL corpus build RUNNING — 6,637 KiCad repos → 8,032 schematics → capped at 800. Output: /Volumes/Storage/schgen/our_corpus/. Next: build_unified_dataset.py → Vast.ai launch.
- [v4.1]: Stage-safe flow shifts from "file-safe editing" to "stage-safe design" — every design transition has a deterministic gate
- [v4.1]: Phases 85-87 prioritized — biggest current weakness is gap between safe KiCad files and real schematic-to-PCB transfer
- [v4.1]: LLM output is advisory; deterministic gates decide whether proposals can mutate files
- [v2.4]: File content snapshots for undo (not Operation objects -- re-execution produces different UUIDs)
- [v2.4]: collections.deque(maxlen=N) for bounded O(1) undo stack
- [v2.4]: Per-executor undo stack keyed by resolved file path
- [v2.4]: Standard undo/redo semantics (new operation clears redo stack)
- [v2.4]: Session-scoped undo (lost on MCP server restart, same as KiCad)
- [v2.4]: LLMProvider protocol is superset of LLMBackend -- providers satisfy both protocols
- [v2.4]: Provider selection via KICAD_LLM_PROVIDER env var (default "anthropic")
- [v2.4]: Lazy LLMClient imports in consumers to avoid hard anthropic dependency
- [v2.4]: ModifyNetClassOp uses Optional[float] fields for partial updates (None=keep existing)
- [v2.4]: write_project_settings operates on raw JSON dict to preserve unknown keys
- [v2.4]: List handlers are read-only (no serialize), returning {items, count}
- [v2.4]: Atomic write via tempfile+os.replace for .kicad_pro (Council FE-02)
- [v2.4]: erc_auto_fix meta-op chains parse_erc to violation dispatch with iteration control (GEN-03)
- [v2.4]: parse_erc imported at module level in erc_auto_fix.py for test mockability
- [v2.4]: validate_power_nets function defaults check_hierarchical=False for backward compat; schema defaults True
- [v2.4]: _check_hierarchical_power reuses sheet traversal pattern from check_sheet_pin_labels
- [v2.4]: modify_copper_zone resolves net via get_net_by_name or creates new net if not found
- [v2.4]: remove_copper_zone prefers UUID lookup, falls back to index, raises ValueError if neither provided
- [v2.4]: Council H-01 fix: 6 repair ops added to schema union -- was 68, now 74
- [v2.4]: Council H-02 fix: ModifyProjectSettingsOp.updates bounded to max_length=50
- [v2.4]: Council M-04 fix: ModifyCopperZoneOp.layer validated with pattern r"^[FB]\.Cu|In[1-9]\d*\.Cu$"
- [v2.4]: Council L-03 fix: RemoveCopperZoneOp has model_validator requiring at least one of zone_uuid/zone_index
- [v2.4-SI]: Plans build on existing schematic_routing/ module (SchematicGraph, wire_router, batch_executor, netlist_parser)
- [v2.4-SI]: Schemas in _schema_schematic_routing.py and _schema_schematic_intel.py (new files)
- [v2.4-SI]: Schematic ops extend existing @register_schematic pattern in executor.py
- [v2.4-SI]: PinResolver uses unit-aware lib symbol indexing via _build_unit_index() for multi-unit IC pin resolution
- [v2.4-SI]: Collision zones use >=2 pins threshold (not >=2 refs) -- vertical wire through IC pin column shorts all pins regardless of component count
- [v2.4-SI]: Pin overlap severity: error (different nets from netlist), warning (same net or unknown) -- defaults to warning without netlist
- [v2.4-SI]: Net labels placed at pin body_position (not wire endpoint) for visual clarity and guaranteed connectivity
- [v2.4-SI]: L-shaped wires use horizontal-first path; collision zone check covers full segment range
- [v2.4-SI]: BatchWiring uses kiutils from_file/to_file for element stripping (not raw S-expression manipulation)
- [v2.4-SI]: Auto-detection of collision zones inside batch_connect when none explicitly provided
- [v2.4-SI]: regenerate_wiring strips wires/labels/no_connects via kiutils, reconnects via NetConnector per-net
- [v2.4-SI]: Voltage pattern regex matches both +3.3V and +3V3 KiCad power naming conventions
- [v2.4-SI]: Power convention detection uses pin_name only, not lib_id -- SchematicGraph filters power symbols
- [v2.4-SI]: Passive components identified by lib_id containing Device:R, Device:C, Device:L
- [v2.4-SI]: Violation classification uses _CLASSIFICATION_RULES ordered list (match_fn, category, root_cause, confidence) -- first match wins
- [v2.5-45]: Shared types.py for NetClassification/PinRole enums prevents circular imports between topology_graph and net_classifier
- [v2.5-45]: Union-Find with path compression for net resolution -- BFS wire tracing failed on multi-hop pin chains without labels
- [v2.5-45]: Ordered list (not dict) for _LIBID_TYPE_MAP to handle prefix ordering (LED before L, Crystal before C)
- [v2.5-45]: Feedback edges reclassified from any non-POWER classification, not just SIGNAL
- [v2.5-45]: SignalIntegrity rules reuse existing _CLOCK_PATTERNS and _CONTROL_PATTERNS (no duplication)
- [v2.5-45]: NetStats.is_stub detects diode, connector, misc components as dead-ends plus non-forward-adjacency
- [v2.5-45]: NetStats.is_multi_drop requires 2+ receiver ICs (not passive components)
- [v2.5-45]: Signal integrity rules stored as class-level _si_rules for extensibility matching _rules pattern
- [v2.5-46]: BFS clustering does not traverse through ICs -- each IC forms its own subcircuit
- [v2.5-46]: PREAMP rule requires resistor_count >= 2 to distinguish from OUTPUT_STAGE
- [v2.5-46]: Feature extraction as standalone _extract_features method for Plan 46-02 reuse
- [v2.5-46]: SubcircuitFeatures has 26 fields (subcircuit_id + 25 feature fields) for ML-ready vectors
- [v2.5-46]: Features dict merges ML fields (SubcircuitFeatures.to_dict) with legacy classifier fields (_extract_features) for backward compatibility
- [v2.5-46]: ClassificationResult.feature_vector populated only for confidence < 0.5 to minimize storage while capturing ML training data
- [v2.5-46]: extract_features accepts optional input_nets/output_nets set parameters for topology-level signal counting
- [v2.5-47]: Intent rule overall_type propagated directly from matched rule, not re-derived from function name
- [v2.5-47]: Signal flow adds Input/Output context when subcircuits have input/output nets
- [v2.5-47]: Subcircuit lib_id checked from features dict first (fast), topology nodes as fallback
- [v2.5-47]: Design checks use topology edges for net connectivity (TopologyNode has no pin_nets)
- [v2.5-47]: Feedback detection uses edge signal_direction plus resistor net-sharing analysis
- [v2.5-47]: Component value check excluded from pipeline -- TopologyNode lacks value data
- [v2.5-47]: Topology indexes (net_to_nodes, node_to_nets) built once per check, passed to helpers
- [v2.5-47]: Ref index dict for O(1) component lookup in intent inference
- [v2.5-47]: Quadratic weighted mean for overall confidence (squares dominate higher-confidence subcircuits)
- [v2.5-47]: Net connectivity ordering for multi-buffer signal flow (not positional heuristic)
- [v2.5-47]: Backward-compatible match_fn dispatch (3-arg with TypeError fallback for 2-arg custom rules)
- [v2.5-48]: Design rules use topology edges exclusively (not pin_nets) for net connectivity -- TopologyNode lacks pin_nets
- [v2.5-48]: Feedback comp cap detection uses any feedback net overlap (single-net feedback common in topology graph)
- [v2.5-48]: THERMAL_01 emits INFO severity since topology lacks thermal pad data
- [v2.5-48]: Test file named test_design_rule_engine.py to avoid collision with existing test_design_rules.py (DRU parsing)
- [v2.5-48]: Shared topology_utils.py for build_net_to_nodes/build_node_to_nets (deduplicated from design_review + builtin_rules)
- [v2.5-48]: PowerFilterRule scans edges for pattern-matched power nets (not just topology.power_nets)
- [v2.5-48]: _is_resistor() excludes R_Potentiometer, R_Photoresistor, R_Thermistor, R_Variable
- [v2.5-48]: Redundant _rule_id_format validator removed (Pydantic pattern enforces it)
- [v2.5-48]: pyyaml used for YAML config parsing (already installed, not in pyproject.toml)
- [v2.5-48]: cli/ package directory created for subcommand modules, registered in existing CLI routing
- [v2.5-48]: CLI tests use real CircuitTopology instead of MagicMock to avoid Pydantic validation errors
- [v2.4-SI]: ClassifyViolationsOp in _schema_erc_smart.py (separate from _schema_repair.py per D-01)
- [v2.4-SI]: IR position data (pin/wire/label positions) distinguishes #PWR symbols from regular components
- [v2.5-51]: Arc center computed via perpendicular bisector intersection; 32-segment LineString approximation
- [v2.5-51]: 1nm snap tolerance closes floating-point gaps before polygonize (manufacturing tolerance >> 1nm)
- [v2.5-51]: Graphic item type detection by attribute presence (has start/end/mid/center), not isinstance
- [v2.5-51]: SpatialQueryEngine rebuilt lazily on access when dirty; mark_dirty invalidates cached engine
- [v3.0-52]: LayoutAwarePlacer wraps HybridPlacementEngine (composition over inheritance)
- [v3.0-52]: Zone boundaries are soft constraints (logged, not enforced) to avoid rejecting valid placements
- [v3.0-52]: ThermalProfile forward-declared as Any in LayoutAwareRequest for Plan 52-02
- [v3.0-52]: Type priority fallback when signal flow ordering is ambiguous
- [v3.0-52]: ThermalProfile is opt-in -- distance heuristic fallback with explicit logging
- [v3.0-52]: Constraint penalties use duck-typed objects (getattr) since Phase 50 types not yet defined
- [v3.0-52]: Thermal exclusion zones are soft guidance (SA can violate with penalty)
- [v3.0-52]: SA refinement at 200 iterations for layout-aware (reduced latency)
- [v3.0-54]: DfmChecker mirrors DesignRuleEngine pattern (ABC + orchestrator + report)
- [v3.0-54]: Meta-finding uses DFM_CHECKER_01 check_id to satisfy pattern validation on crashed checks
- [v3.0-54]: SolderMaskCheck uses 4x sliver proximity window for O(n) pair optimization
- [v3.0-54]: ManufacturerProfile uses yaml.safe_load for security (T-54-02, same as rule_config.py)
- [v3.0-54]: Panelization score formula: fiducials (0.3/0.15), tooling holes (0.2/0.1), orientation (0.3), edge clearance (0.2)
- [v3.0-54]: Assembly score formula: 1.0 - (warnings * 0.05) clamped to [0.0, 1.0]
- [v3.0-54]: Multi-stage pipeline runs DfmChecker with filtered check subsets per stage
- [v3.0-54]: Overall DFM score is minimum of all stage scores and panelization score
- [v3.0-54]: CLI exit codes: 0 (score >= 0.5), 1 (score < 0.5), 2 (error)
- [v3.0-54]: isinstance() type guards prevent MagicMock auto-attribute string matching
- [v2.2-100]: RoutingStrategy is a typing.Protocol (not ABC) — enables Phase 98 structural subtyping without inheritance
- [v2.2-100]: RouterBackend has exactly 2 variants (ASTAR, FREEROUTING) — MULTI_PASS removed as dead code (H1, YAGNI)
- [v2.2-100]: BoardState has no layer_count field — no dispatch case reads it (H3, YAGNI)
- [v2.2-100]: DeterministicStrategy dispatch order is first-match-wins: diff pair → power+zones → high pin (>10) → simple 2-pin (≤20 nets) → default ASTAR
- [v2.2-100]: Audit trail uses JSONL with os.fsync after each line for crash durability (H5); query_by_net skips truncated lines gracefully
- [v2.2-100]: Rollback uses PcbRawWriter.delete_segment/delete_via via UUID extraction — NOT regex on S-expressions (H2, avoids pad-definition corruption)
- [v2.2-100]: UUID extraction uses bulk extract_uuids(content, file_type) then parent_index filtering (R3-L3)
- [v2.2-100]: Per-net Freerouting completion attribution via SES parse (parse_ses), not just success flag — accurate baseline measurement
- [v2.2-100]: SC-5 baseline test asserts >= 45% (lower bound only) — orchestrator combines A* + Freerouting so should meet or exceed Freerouting-alone baseline
- [Phase 101-04]: trust_erc defaults True in remove_dangling_wires — ERC wire_dangling positions augment geometric criteria (union, not replacement), preserving Phase 123 Wave 2 success while fixing silent no-op on ERC-flagged patterns
- [Phase 101-04]: Council H-1 fix — dispatcher handlers/schematic.py now passes trust_erc=op.trust_erc (schema accepted the field but dispatcher was silently dropping it)
- [Phase 102]: Phase 102-01: H-02 Option A applied — all 5 fixtures omit (instances ...) blocks. KiCad netlist exporter reads refdes from (reference ...) inside instances; if inherited from template, Plan 02 handler would edit (property Reference ...) while leaving stale (reference ...) — silent partial-annotation identical to P0-006. Option B (handler co-edits instances) DEFERRED-TO-NAMED-TARGET — trigger: Phase 145 manual verification on analog-board.kicad_sch fails.
- [Phase 102]: Phase 102-01: Multi-sheet root fixture has ZERO placed component symbols (only 2 sheet blocks) — ensures TC-5 root sheet guard fires correctly (has children + no own components = root sheet).
- [Phase 102]: Phase 102-01: TC-6 stub documents function-scoped AST grep per Council H-01 — uses inspect.getsource(_handle_safe_annotate) mirroring tests/test_safe_sync_pcb_from_schematic.py:74-88, NOT whole-module walk that would false-positive if any future sibling handler legitimately uses to_file().
- [Phase 102]: Phase 102-02: safe_annotate registered in SELF_SERIALIZING_OPS (single_file scope) — different dispatch path from safe_sync_pcb_from_schematic which uses CROSS_FILE_OP_TYPES (multi-file scope). Both bypass serialize_schematic but via different mechanisms matching their file-scope semantics.
- [Phase 102]: Phase 102-02: UUID regex accepts both KiCad 10 unquoted (uuid abc-123) AND legacy quoted (uuid "abc-123") forms via \"?...\"? optional-quote pattern. Applied to both _extract_symbols_with_refs and SchematicRawWriter.replace_reference_property. Original plan regex assumed quoted form only — Rule 1 bug fixed during execution.
- [Phase 102]: Phase 102-02: Test invocation uses OperationExecutor(base_dir=tmp_path) + Operation.model_validate({"root": {...}}) + executor.execute(op). target_file is relative basename inside tmp_path (path confinement check rejects absolute paths). Mirrors tests/test_modify_property.py:266-282.
- [Phase 102]: Phase 102-03: Root sheet guard refined to scope-conditional — `if op.scope == "current_sheet" and has_sheet_blocks and not has_placed_components`. Was unconditional, blocked whole_project walks on roots (TC-3). Rule 1 bug.
- [Phase 102]: Phase 102-03: Reset-mode dedup detection via pre-pass Counter on original refs. Under reset=True, all refs become `<prefix>?` and enter annotation branch — bypassing non-reset dedup path. Pre-pass counts original refs; subsequent owners (after sort) marked deduped=True so stats.duplicates_resolved is correct. Rule 1 bug.
- [Phase 102]: Phase 102-03: DeprecationWarning on _handle_annotate mirrors erc_auto_fix.py:255-262 pattern — stacklevel=2, message references P0-006 + safe_annotate docs, fires BEFORE any file mutation.
- [Phase 102]: Phase 102-03: H-03 success criteria applied — "proven on minimal multi-sheet fixtures; full real-world validation deferred to Phase 145 manual verification per VALIDATION.md line 69" (Option b from Council Gate 1).
- [Phase 102.1]: Phase 102.1-01: EXEC-03 sort tie-break uses sheet_uuid (KiCad-embedded, stable across machines) NOT sheet_path (absolute, varies). Root UUID via _extract_root_sheet_uuid (anchored before first (symbol / (lib_symbols); sub-sheet UUIDs via SheetRef.uuid (requires CR-01 regex fix for unquoted KiCad 10 UUIDs).
- [Phase 102.1]: Phase 102.1-01: H-02 Option B — handler calls BOTH replace_reference_property AND replace_instances_reference per rename. Instances edit is no-op when block absent (backward compat with Phase 102 fixtures). Old reference discarded after locating; never interpolated into regex replacement (LO-05 hardening).
- [Phase 102.1]: Phase 102.1-01: H-03 acceptance criteria evolved — source analog-ecosystem repo already has 0 cross-sheet duplicates (resolved since FEATURE-008 2026-06-29). Real test is GNDA present in netlist with >0 nodes (39 nodes confirmed). Script asserts GNDA > 0 rather than GNDA increasing, because baseline is already healthy.
- [Phase 102.1]: Phase 102.1-01: H-03 validation script operates on COPY via shutil.copytree + shutil.rmtree in try/finally — NEVER git checkout/stash on source repo. Source dirty-count verified unchanged (5 before, 5 after).

### Pending Todos

- All milestones shipped. Ready for next milestone planning.
- Phase 75 added retroactively: Pre-Analysis Gate and Context Intelligence (ad-hoc work tracked post-hoc)
- **Phase 102 (proposed): Schematic Ops Bug Fixes** — 5 P0/P1 bugs from analog-ecosystem backplane cleanup (BUGS/P0-001 through P0-005). Out-of-scope for Phase 99 (freerouting) but blocking ~600 ERC violations on production backplane work. Fix priority: P0-003 deprecation (data loss) → P0-001 quick fix → P0-002+P0-004 position transforms → P0-005 criteria alignment. See `BUGS/README.md` for details.

### Quick Tasks Completed

| # | Description | Date | Commit | Directory |
|---|---|---|---|---|
| 260616-wqd | Build a validate_labels pre-flight check in volta | 2026-06-17 | ee47896 | [260616-wqd-build-a-validate-labels-pre-flight-check](./quick/260616-wqd-build-a-validate-labels-pre-flight-check/) |
| Phase 101 P04 | 5m | 2 tasks | 4 files |
| Phase 102 P02 | 9m | 3 tasks | 8 files |
| Phase 102 P03 | 3m | 2 tasks | 5 files |
| Phase 102 P01 | 5min | 2 tasks | 6 files |
| Phase 205 P01 | 23m | 6 tasks | 14 files |

### Blockers/Concerns

None.

## Deferred Items

- **CR-01** (Critical, Council Exec Review 99): **RESOLVED 2026-06-25 (Phase 100 Plan 01).** All 14 NativeBoard dataclasses converted to `@dataclass(frozen=True)`; 16 list fields converted to tuple defaults; `NativeFootprint.properties` exposed as `MappingProxyType` read-only view; all native-path mutation sites in `pcb_ir.py` (`add_net`, `remove_net`, `rename_net`, `swap_footprint`) and `pcb_native_parser.py` (every extractor) migrated to `dataclasses.replace` / construct-once pattern. 8 new immutability tests + 357 existing regression tests pass (365 total). See `.planning/phases/100-routingorchestrator-and-human-approval-loop/100-01-SUMMARY.md`. Tags: council-deferred,immutability,phase-99,cr-01,wr-07.

- **WR-07** (Medium, Council Exec Review 99): **RESOLVED 2026-06-25 (subsumed by CR-01 closure above).** `PcbIR.remove_net` now rebuilds pads via `dataclasses.replace(pad, net_name="", net_number=0)` and rebuilds the footprint and board via replace chain. Tags: council-deferred,immutability,phase-99,wr-07.

- **Out-of-scope finding (2026-06-25, surfaced during Phase 101 regression check)**: **RESOLVED 2026-06-25 (Phase 101 followup).** `generate_bom` is registered as a readonly op (`src/volta/ops/registry.py:1221`) but missing from query handler dispatch. Fix: added `_handle_generate_bom` wrapper in `schematic_query.py` that delegates to existing handler in `pcb_bom.py`. Test now passes (9/9 in `test_schematic_query_dispatch.py`). Commit: e9113fe.

- **MD-02 (Medium, Council Exec Review 101 — out-of-scope Bead)**: `tests/test_place_no_connects_power_aware.py:314, 359, 419, 467` patch `volta.ops.repair.NetPositionIndex` but `repair_erc.py:17` binds the class directly (`from volta.schematic_routing.net_extractor import NetPositionIndex`). The patch targets the wrong namespace. Tests pass only because `NetPositionIndex.from_file()` raises on minimal test schematics, hitting the `except: net_index = None` branch. If a future change makes `from_file()` succeed on minimal fixtures, the patch would silently fail. **Resolution:** Change patch target from `volta.ops.repair.NetPositionIndex` to `volta.ops.repair_erc.NetPositionIndex` at lines 314, 359, 419, 467. Pre-existing issue — NOT introduced by Phase 101. Out-of-scope per bureaucracy §7. Labels: `out-of-scope,test-reliability`. Priority: 2.

## Session Continuity

Stopped at: Executing 205-01-PLAN.md
Resume with: /gsd-plan-phase 205 (Board Metadata Foundation) or /gsd-discuss-phase 205.
Next: plan Phase 205 (Board Metadata Foundation) — title_block parse/write + BoardSpec model + sidecar JSON persistence. Foundation for versioning; unblocks Phase 207.

### Phase 100: RoutingOrchestrator and Human Approval Loop (complete)

- Plan 100-01: CR-01 NativeBoard immutability refactor (COMPLETE)
  - 14 frozen dataclasses, all native-path mutation sites migrated to dataclasses.replace
  - Foundation for Plan 02's snapshot-based rollback

- Plan 100-02: RoutingOrchestrator + audit + rollback (COMPLETE)
  - RoutingStrategy Protocol (Phase 98 integration contract — pure, serializable, validatable)
  - DeterministicStrategy with 5-case dispatch (diff pair → power+zones → high pin → simple 2-pin → default ASTAR)
  - RouterBackend enum (2 variants: ASTAR, FREEROUTING — H1: MULTI_PASS removed)
  - RoutingOrchestrator batch API (route_board single-call for full board)
  - PcbIR-based per-net rollback via PcbRawWriter UUID deletion (H2 — no regex)
  - Durable JSONL audit trail with os.fsync (H5)
  - InteractiveRoutingSession.ingest_freerouting_result (SES wires → suggestions)
  - Strategy output validation (H4 — unknown nets/invalid backends raise ValueError)
  - 66 Phase 100 tests + 357 regression tests pass (431 total, zero regressions)

---

## Volta Component Integration (v8.0) — added 2026-07-28

**New milestone layered on top of v11.0 gap-closure (complete).** Phases 251-254 track the four-protocol plugin architecture work (ComponentData, CADModel, Routing, Compliance) for the Volta PCB Swift macOS app.

### Phase 251: Mouser API Integration

- **Status:** Planning (Bret WIP, untracked)
- **Goal:** Integrate Mouser API as ComponentDataProvider
- **API Key:** Stored in macOS Keychain (`com.volta.mouser.api_key`) — Bret added 2026-07-28
- **Files:** `.planning/phases/251-mouser-api-integration/PLAN.md`
- **Companion code (untracked):** `macos-app/Sources/Volta/Providers/Local/`, `macos-app/Tests/VoltaTests/Providers/Mouser/MouserProviderTests.swift` (modified, +139/-1)

### Phase 252: Compliance Provider System

- **Status:** Planning (Bret WIP, untracked)
- **Goal:** ComplianceProvider protocol + LocalComplianceProvider + SnapMagicFileImport
- **Strategy:** Local compliance rules (offline) + SnapMagic file import (manual workflow). SiliconExpert dropped — enterprise-only access confirmed blocked for indie ISV (same dead-end pattern as SnapMagic API)
- **Files:** `.planning/phases/252-compliance-provider-system/PLAN.md`
- **Companion code (untracked):** `macos-app/Sources/Volta/Compliance/`, `macos-app/Sources/Volta/Protocols/`

### Phase 253: Routing Plugin System (migrated 2026-07-28)

- **Status:** Execution-ready (research complete, code pending Volta PCB Swift worktree)
- **Goal:** Apply the provider plugin pattern to auto-routing engines (Freerouting, KiCad native, optional DeepPCB)
- **Cloud routing verdict:** DeepPCB enterprise-only ($900/mo, no public REST docs, no self-serve) — see `.planning/research/PHASE4_DEEPPPCB_VERDICT.md`. Quilter AI removed from scope (Bret decision 2026-07-28)
- **ADs:** RoutingProvider mirrors ComponentDataProvider shape (Sendable + ProviderAvailability + registry pattern); domain isolation in adapters; vendor-neutral RoutingRules; long-running op semantics (cancellation, progress streaming); cloud routing research-gated
- **Files:** `.planning/phases/253-routing-plugin-system/PLAN.md` + `PHASE4_EXECUTION_NOTES.md`
- **Migration source:** `~/.buzz/PLANS/volta-component-integration/phases/4-routing-plugin-system/` (historical, do not edit)

### Phase 254: Compliance + File Import (migrated 2026-07-28)

- **Status:** Planning (companion to Phase 252 — covers UI/file-import side)
- **Goal:** ComplianceProvider + SnapMagic file import flow + local compliance rules UI
- **Files:** `.planning/phases/254-compliance-file-import/PLAN.md`
- **Migration source:** `~/.buzz/PLANS/volta-component-integration/phases/5-compliance-file-import/` (historical, do not edit)

### Volta Component Integration Scope (decision 2026-07-28)

- **Mouser API key**: added — MouserProvider should now be live; verify via app search on a Mouser-stocked MPN
- **Quilter AI**: dropped from Phase 253 — Bret decision (no public access)
- **SiliconExpert**: dropped from Phase 252/254 — Bret decision (enterprise-only access confirmed blocked)
- **DeepPCB**: research verdict DEFERRED — enterprise-only access; re-evaluate trigger: docs.deeppcb.ai/api becomes public OR self-serve signup opens

### GSA Phase 2 Adoption Slice (started 2026-08-17)

- **Status:** In progress in `apps/volta` against the `gsa-platform` Phase 2 support contract
- **Scope landed so far:**
  - New Python governance layer at `src/volta/governance/`
  - Governed file-level object identities for project / schematic / pcb
  - Governed logical locators for schematic subobjects: sheet / component / net / bus
  - Governed manufacturing artifact identities for bom / assembly outputs
  - Governed capability wrappers for:
    - build snapshot creation
    - manufacturing handoff export
    - verification batches
    - CAD model import source tracing
    - board metadata read identity tracing
  - Bootable runtime wrapper at `src/volta/platform_runtime.py` for project-scoped governed execution, diagnostics, feed, and export snapshots
  - Existing flows now emit governed metadata without breaking KiCad behavior:
    - `build_create`
    - `build_handoff_export`
    - `ValidationPipeline.validate_and_apply()`
    - `validate_generated()`
    - `SnapMagicImportProvider.import_models()`
    - `read_board_metadata`
    - `drc_vendor`
    - playground app boot/runtime execution path (`create_app()`, `/api/execute`, `/ws`)
    - playground diagnostics/export surfaces (`/api/diagnostics`, `/api/runtime/export`)
- **Focused verification:** governed/manufacturing/import/validation/routing regression slice passing (`112 passed` under `PYTHONPATH=src PYTEST_DISABLE_PLUGIN_AUTOLOAD=1 pytest -q -o addopts='' ...`)
- **Current verification expansion:** broader governed Phase 2 slice passing (`134 passed` under `PYTHONPATH=src PYTEST_DISABLE_PLUGIN_AUTOLOAD=1 pytest -q -o addopts='' ...`)
- **Runtime embedding verification:** platform-runtime + playground embedding slices passing (`76 passed`, then `85 passed` under `PYTHONPATH=src PYTEST_DISABLE_PLUGIN_AUTOLOAD=1 pytest -q -o addopts='' ...`)
- **Broader post-runtime verification:** governed/manufacturing/runtime regression slice passing (`136 passed` under `PYTHONPATH=src PYTEST_DISABLE_PLUGIN_AUTOLOAD=1 pytest -q -o addopts='' ...`)
- **Cross-repo proof package:** dedicated downstream SwiftPM proof added at `integration/gsa-platform-proof/`, depending on local `../../../gsa-platform` and running `AdopterIntegrationScenario.runGovernedRevisionArtifactFlow(...)` with board-release semantics
- **Cross-repo proof verification:** `swift test --package-path integration/gsa-platform-proof` passes (`1 test passed`) against the local `gsa-platform` package on 2026-08-17
- **Remaining likely M2.3/M2.4 work:**
  - Broaden governed object registration beyond current execution slices where more electronics entities get first-class runtime participation
  - Audit whether any future concrete manufacturer API adapters need approval/evidence wiring once Phase 210 vendor adapters land
  - Decide whether the live Volta app/runtime should directly embed `Platform.boot(...)` or keep the dedicated proof package as the Phase 2 cross-repo contract surface for now

### Source-of-Truth Note (2026-07-28)

- **Repo `.planning/` IS canonical** for all Volta Component Integration planning going forward. Bret decision: "i want the planning to be in the repos . that way it track from here and other tools"
- `~/.buzz/PLANS/volta-component-integration/` is now a historical mirror; do not edit. Cleanup target: Phase 1-3 mirror files (already superseded by git history of commits `0b62ac6`, `d657ab9`, `f1621d1`, `2ecb6c8`, `5572c0c`)
- Phases 1-3 (component-provider-foundation, multi-source-expansion, assembly-backup-sources) were already merged to master before this migration; their buzz-workspace mirror files (`phases/1-…`, `phases/2-…`, `phases/3-…`, plus `COVERAGE-REVIEW.md`, `API_CONTRACTS.md`, `DIGIKEY_*`) are archived, not authoritative
- 2026-08-17: Extended the app-owned GSA platform chain from governed verification + release export into a real governed manufacturing handoff. `GSAPlatformHost` now runs `runGovernedManufacturingHandoff()` on the same `electronics.board.release` object, `CompletionSummary` / `VerifyView` surface the handoff artifact and approval metadata, and `LiquidGlassShell` drives export + handoff in one live app flow. Focused Swift tests were updated to assert the shared object-scoped chain across verification, release, and manufacturing handoff.
- 2026-08-17: Widened the live governed slice toward M2.3 object identity. `GSAPlatformHost` now supports explicit project context plus a governed `electronics.project` anchor, and the shell passes real `Project` / `Conversation` identity into governed release + manufacturing-handoff execution. Completion summaries now surface both `project:` and board-release object references so the trace is no longer board-only.
- 2026-08-18: Split revision identity out of raw integer state into an explicit governed `electronics.project.revision` object. Verification evidence, release export, manufacturing handoff, and validation summaries now carry `revision:` references, making the live trace project → revision → board release rather than project → board release only.
- 2026-08-18: Added governed `electronics.bom` identity to the same live slice. Verification, release export, manufacturing handoff, and validation summaries now carry `bom:` references, widening the proven chain to project → revision → bom → board release without creating a separate migration path.
- 2026-08-18: Added governed `electronics.schematic` identity to the same live slice. Verification, release export, manufacturing handoff, and validation summaries now carry `schematic:` references, widening the proven chain to project → revision → schematic → bom → board release.
