bretbouchard/kicad-agent/.planning/VOLTA_DEEP_PLAN.md

# Volta Deep Implementation Plan

## 🎯 Current Status Assessment

**Repository**: Volta (apps/volta)  
**Current Focus**: KiCad-based PCB design and electronics workflows  
**Planning Status**: ✅ Active GSD structure exists  
**GSA Integration**: ❌ Not integrated - migration pending Phase 1 completion

## 🔄 Two-Track Strategy

**Track A: Continue Current Work** (Don't block on GSA)
- KiCad PCB design workflows
- Hardware projects (channel strip, demo boards)
- Component library management
- PCB verification and testing

**Track B: Prepare for GSA Migration** (Parallel preparation)
- Identify platform code to migrate
- Design GSA integration points
- Prepare migration infrastructure
- Document current architecture

## 📋 Immediate Work Queue (Next 2 Weeks)

### Week 1: Current Work + GSA Analysis

**Priority 1: Unblocking Work** (P0)
- Fix any critical build/verification issues
- Continue active hardware projects
- Address component library issues

**Priority 2: GSA Preparation** (P1)
- **Analyze current codebase** for platform vs. domain separation
- **Map current features** to GSA specification requirements
- **Identify migration candidates** (code that should move to GSA)
- **Document current KiCad workflow dependencies**

### Week 2: Architecture + Planning

**Priority 1: Current Work** (P0)
- Continue PCB design and verification
- Component library maintenance
- Manufacturing workflow improvements

**Priority 2: Migration Planning** (P1)
- **Create detailed migration plan** for Volta → GSA
- **Design integration architecture** for how Volta will use GSA services
- **Set up testing strategy** for migration verification
- **Identify migration risks** and mitigations

## 🏗️ Deep Implementation Plan

### Phase 1: Current Work Completion (Weeks 1-12)

#### 1.1 KiCad Workflow Enhancement (Weeks 1-6)
**Current Focus**: Electronics design and verification

**Tasks**:
- ✅ KiCad project management
- ✅ Schematic capture workflows
- ✅ PCB layout and design rules
- ⏳ BOM generation and management
- ⏳ Design rule checking (DRC/ERC)
- ⏳ Manufacturing file generation (Gerber, etc.)

**GSA Considerations**:
- Design projects with GSA-compatible object identities
- Create hooks for future GSA integration (governed changes for project state, etc.)
- Document KiCad workflow assumptions for eventual migration

**Deliverables**:
- Working KiCad-to-verification pipeline
- Stable PCB project management
- BOM generation with component tracking
- Design rule verification

**Evidence Required**:
- Integration tests showing KiCad → verification flow
- Rule check verification tests
- BOM accuracy validation
- Manufacturing file format validation

#### 1.2 Component Library System (Weeks 1-8)
**Current Focus**: Component management and supply chain

**Tasks**:
- **Component registry** implementation
- **Symbol and footprint libraries**
- **Component metadata management**
- **Supply chain tracking**
- **Alternate component management**

**GSA Considerations**:
- Design component objects with GSA-compatible identities
- Plan for governed changes to component library
- Create hooks for evidence collection (verification results, etc.)

**Deliverables**:
- Working component library system
- Symbol/footprint association
- Component metadata storage
- Supply chain status tracking

**Evidence Required**:
- Component library consistency tests
- Symbol-footprint association verification
- Supply chain data accuracy tests
- Component lookup performance tests

### Phase 2: GSA Migration Preparation (Weeks 5-12)

#### 2.1 Architecture Analysis (Weeks 5-6)
**Tasks**:
- **Inventory platform code** duplicated from GSA responsibilities:
  - Planning/scheduling logic for PCB projects
  - Policy/permission systems for design reviews
  - Object persistence models for projects
  - Event/change tracking for design state
  - Evidence collection systems for verification
- **Map electronics domain logic** that should stay in Volta:
  - Electronics ontology (schematics, PCBs, components, etc.)
  - KiCad integration and file handling
  - Design rule checking logic
  - Manufacturing workflow management
  - Supply chain tracking
- **Identify integration points** where Volta will call GSA:
  - Object lifecycle management
  - Governed change execution
  - Capability invocation (file I/O, manufacturing services, etc.)
  - Evidence verification
  - Policy checks

**Deliverables**:
- Complete codebase inventory (what belongs where)
- Dependency map between Volta and GSA
- Risk assessment for migration complexity
- Migration candidate prioritization

#### 2.2 Migration Design (Weeks 7-8)
**Tasks**:
- **Design object model migration**:
  - How current Project/Schematic/PCB objects map to GSA base objects
  - How to preserve current object identities
  - Version compatibility strategy for KiCad files
- **Design capability integration**:
  - Which operations become GSA Capabilities (manufacturing, verification, etc.)
  - How current KiCad operations route through Capabilities
  - Performance considerations for capability calls
- **Design evidence integration**:
  - What evidence needs to be collected for electronics operations
  - How to integrate verification results as evidence
  - Quality Bar definitions for electronics workflows

**Deliverables**:
- Detailed migration architecture document
- Integration API designs (Volta ↔ GSA)
- Performance impact analysis for KiCad operations
- Testing strategy for migration verification

### Phase 3: GSA Foundation Integration (Weeks 9-16)

#### 3.1 Object Model Adoption (Weeks 9-12)
**Tasks**:
- **Adopt GSA base objects** for electronics entities:
  - Project inherits from GSA GovernedObject
  - Schematic, PCB, Component inherit appropriately
  - Preserve stable IDs (migration strategy for KiCad IDs)
- **Integrate with Modeled World**:
  - Register electronics domain objects with GSA Modeled World
  - Create projections for electronics-specific views
  - Handle object lifecycle through GSA runtime
- **Maintain KiCad compatibility**:
  - Ensure current KiCad file formats still work
  - Preserve existing workflows during transition
  - Support gradual migration of projects

**Deliverables**:
- Electronics domain objects using GSA base model
- Working integration with GSA Modeled World
- Compatibility layer for existing KiCad projects
- Tests showing object identity preservation

#### 3.2 Capability Integration (Weeks 13-16)
**Tasks**:
- **Identify Capabilities to register**:
  - Manufacturing service operations (PCB fabrication, assembly, etc.)
  - Verification operations (rule checks, testing, etc.)
  - File I/O operations (KiCad file import/export, etc.)
  - Supply chain operations (component sourcing, etc.)
- **Create Capability adapters**:
  - Wrap existing operations in Capability framework
  - Maintain KiCad workflow performance during migration
  - Handle capability versioning
- **Integrate policy checks**:
  - Add Obdurate policy checks before operations
  - Handle authorization and approval flows
  - Maintain engineer experience while adding governance

**Deliverables**:
- All external operations using GSA Capabilities
- KiCad workflow performance maintained within acceptable bounds
- Policy checks integrated without breaking workflows
- Evidence collection for all electronics Capabilities

### Phase 4: Complete Migration (Weeks 17-24)

#### 4.1 Planning Integration (Weeks 17-20)
**Tasks**:
- **Migrate to GSD planning** for electronics project planning:
  - Use GSD for PCB project planning
  - Integrate existing project planning with GSD
  - Handle replanning when design requirements change
- **Evidence collection**:
  - Collect evidence for electronics operations
  - Verify quality bars for PCB features
  - Handle verification results as evidence
- **Complete traceability**:
  - Trace all electronics features to requirements
  - Maintain traceability through implementation
  - Generate evidence-based completion reports

**Deliverables**:
- Electronics planning using GSD framework
- Verification evidence collection operational
- Complete traceability for electronics features
- Quality bar enforcement working for electronics

#### 4.2 Migration Completion (Weeks 21-24)
**Tasks**:
- **Remove duplicated platform code**:
  - Delete planning logic replaced by GSD
  - Remove policy systems replaced by Obdurate
  - Clean up redundant object models
- **Performance optimization**:
  - Optimize GSA integration overhead for KiCad workflows
  - Cache frequently accessed design data
  - Minimize capability call overhead
- **Complete validation**:
  - All KiCad workflows working with GSA
  - Design verification performance maintained
  - Manufacturing workflows operational
  - Evidence collection complete

**Deliverables**:
- Clean codebase with no platform duplication
- Optimized GSA integration for electronics workflows
- Complete validation and testing
- Production-ready GSA integration for KiCad workflows

## 🎯 Flexible Execution Plan

### How to "Just Grind" - Clear Task Flow

#### Daily Workflow:
1. **Check Beads** (`bd ready`) - See what's ready to work on
2. **Pick Track A or B** based on current priority:
   - **Track A** (Current Work): Claim a KiCad or component library task
   - **Track B** (GSA Prep): Claim a migration prep task
3. **Execute** - Work the task with clear acceptance criteria
4. **Evidence** - Collect required verification/tests
5. **Complete** - Mark task done when evidence satisfied

#### Priority Decision Tree:
```
Is GSA Platform Ready (Phase 1 complete)?
├── NO → Focus on Track A (Current Work) + Track B (Migration Prep)
└── YES → Focus on Track C (GSA Integration)

Is there a P0 blocker in current work?
├── YES → Do Track A (Unblocking work)
└── NO → Can do Track A or Track B

Is migration preparation complete?
├── NO → Do Track B (Migration prep)
└── YES → Wait for GSA Platform + plan Track C
```

#### Task Categories for Easy Selection:

**🔥 P0 - Unblocking Current Work** (Always do these first)
- Critical build/verification failures
- Blocking KiCad workflow issues
- Component library blockers
- Manufacturing workflow issues

**⚡ P1 - Core Feature Work** (Main development)
- KiCad workflow improvements
- PCB design projects
- Component library enhancements
- Verification and testing features

**🔧 P1 - Migration Preparation** (Parallel to above)
- Architecture analysis
- Migration design
- Integration planning
- Risk assessment

**📊 P2 - Infrastructure** (Background work)
- Testing infrastructure
- Documentation
- Tooling improvements
- Performance analysis

### Weekly Rhythm:

**Monday**: Planning + Prioritization
- Review上周 completed PCB/electronics work
- Plan本周 objectives
- Check GSA Platform status
- Adjust Track A/B mix based on dependencies

**Tuesday-Thursday**: Execution
- Focus on selected tasks from beads
- Collect verification evidence as you go
- Update task status regularly

**Friday**: Review + Evidence
- Complete weekly objectives
- Ensure verification/tests collected
- Update beads with progress
- Plan下周 priorities

## 📊 Success Metrics

### Current Work Success (Track A):
- ✅ KiCad workflows stable and operational
- ✅ Component library system functional
- ✅ PCB projects completing successfully
- ✅ Verification pipelines working

### Migration Success (Track B):
- ✅ Complete electronics architecture analysis documented
- ✅ Migration plan designed and validated
- ✅ KiCad integration points clearly identified
- ✅ Risks assessed and mitigated

### Integration Success (Track C):
- ✅ Volta using GSA services for electronics workflows
- ✅ KiCad workflows maintained during migration
- ✅ Verification performance within acceptable bounds
- ✅ Evidence collection operational for electronics operations

## 🚨 What to Do When

### When GSA Platform Completes Phase 1:
1. **Stop Track B** (migration prep complete)
2. **Start Track C** (GSA integration)
3. **Continue Track A** (keep current KiCad work going)
4. **Re-balance** to 70% Track A, 30% Track C

### When Current Work Hits Blocker:
1. **Check if GSA-related** (would GSA help unblock?)
2. **If yes** → Accelerate Track B (migration prep may help)
3. **If no** → Focus on Track A (unblock current work)

### When Migration Prep Complete:
1. **Review migration plan** with team
2. **Validate assumptions** about GSA Platform readiness
3. **Create detailed Track C plan** (GSA integration)
4. **Wait for GSA Platform Phase 1** signal

## 🎯 Next Actions (This Week)

### Immediate (Today):
1. **Claim highest priority bead** from `bd ready` in Volta
2. **Set up weekly planning** rhythm for electronics work
3. **Update existing plan** with deep structure

### This Week:
1. **Complete at least 2 P0 tasks** (unblocking work)
2. **Make progress on P1 task** (core KiCad features)
3. **Start migration analysis** (Track B begins)

### Next Week:
1. **Review migration prep progress**
2. **Adjust Track A/B balance** based on GSA Platform status
3. **Plan for Track C** if GSA Platform progressing well

---

**Key Principle**: You can keep grinding on electronics/KiCad work while preparing for GSA migration. No need to wait - both tracks proceed in parallel until GSA Platform is ready.

**Status**: ✅ Deep plan created, ready to execute  
**Flexibility**: High - clear task priorities, easy to adjust based on dependencies  
**Next Step**: Claim first Volta task and start grinding!
