bretbouchard/kicad-agent/docs/COUNCIL-OF-RICKS-REVIEW.md

# Council of Ricks — volta Full Review

**Date:** 2025-05-24
**Reviewers:** 5 specialists (ML Pipeline, Architecture, KiCad Domain, Code Quality, User Experience)
**Total Findings:** 47 (7 CRITICAL, 14 HIGH, 26 MEDIUM/LOW)

---

## Executive Summary

volta is a well-structured Python library for AI-safe KiCad file editing with 142 source files, 92 test files, and solid transaction/rollback safety. The Council identified three systemic themes:

1. **Routing engine is disconnected** — architecturally impressive but can't write results to PCB files
2. **GRPO training is circular** — reward model = policy model, no generative LM, trains nothing
3. **CLI is for developers only** — 35 operation types but only `collect` is exposed as a subcommand

---

## CRITICAL Findings (7)

| ID | Source | Finding | File |
|----|---|---|---|
| C1 | ML Pipeline | **GRPO does not perform actual policy gradient optimization** — trains reward model via supervised learning, calls it "policy" | `grpo.py`, `pipeline.py` |
| C2 | ML Pipeline | **KL divergence hardcoded to 0.01**, never computed — `compute_kl_penalty` exists but is never called | `grpo.py:356,376` |
| C3 | ML Pipeline | **Reward model = policy model = ref model** — circular training, model chases own predictions | `pipeline.py:231-238` |
| C4 | Architecture | **Monolithic 300-line if/elif dispatch** with duplicate `add_net` branches in executor | `executor.py` |
| C5 | Architecture | **No IR abstraction** — tight coupling to kiutils internals, raw S-expression manipulation in IR layer | `pcb_ir.py:278-429` |
| C6 | Architecture | **Routing engine disconnected from IR** — computes paths but can't write track segments to PCB | `routing/`, `pcb_ir.py` |
| C7 | UX | **CLI requires raw JSON** — no human-friendly subcommands, unusable by PCB designers | `cli.py` |

### Root Cause Analysis

- **C1-C3** share one root cause: **the system lacks a generative language model**. The `RewardModel` is a 4-layer transformer encoder that outputs 3 scalar scores — it cannot generate text. `generate()` does best-of-N selection from template chains, not autoregressive generation. Fix: integrate a pre-trained causal LM or reframe as supervised reward model training.
- **C4-C5** are abstraction debt — the IR layer is a thin wrapper, not a true abstraction over kiutils.
- **C6** is an integration gap — routing operates on abstract coordinates with no bridge to the serializer.
- **C7** is a UX gap — the library is complete but inaccessible.

---

## HIGH Findings (14)

### ML Pipeline

| ID | Finding | File |
|----|---|---|
| H1 | Reward model is a classifier (encoder), not a generative model (decoder) | `reward_model.py` |
| H2 | `generate()` uses best-of-N from templates, not learned generation — action space limited to 5 fixed outputs | `reward_model.py:223-259` |
| H3 | No validation monitoring during GRPO training, no early stopping | `grpo.py`, `pipeline.py` |
| H4 | Optimizer recreated every `train_step()`, losing AdamW momentum; LR schedule computed but never applied | `grpo.py:284` |
| H5 | Real-world 213-sample dataset never flows into training — `RealBoardSample` incompatible with `MazeSample` | `real_dataset.py` |
| H6 | No data augmentation on synthetic samples (rotation, reflection, noise) | `dataset.py` |

### KiCad Domain

| ID | Finding | File |
|----|---|---|
| H7 | **No zone fill operation** — ground pours created but never validated, potential disconnected islands | `pcb_ops.py`, `schema.py` |
| H8 | **No hierarchical schematic support** — multi-sheet designs have incomplete connectivity | `schematic_parser.py` |
| H9 | **Design rules (.kicad_dru) disconnected from routing** — generic 0.25mm traces for everything | `constraints.py`, `design_rules.py` |
| H10 | **UUID re-injection is fragile** — sequential positional matching breaks if kiutils reorders | `uuid_reinjector.py` |
| H11 | **Routing graph is single-layer** — no via support, no multi-layer routing | `graph.py` |

### Architecture

| ID | Finding | File |
|----|---|---|
| H12 | No event/observer system — IR mutations don't trigger connectivity/propagation updates | Multiple |
| H13 | Training pipeline hard-coupled to maze domain — can't train for placement, routing, ERC | `pipeline.py` |
| H14 | No batch/multi-file operation support — "add bypass cap" needs 4 separate operations | `schema.py` |

### Code Quality

| ID | Finding | File |
|----|---|---|
| H15 | ReDoS-vulnerable regex `r'^(\t+\(net )'` on externally-sourced content | `pcb_parser.py:39-44` |
| H16 | 14 redundant `import re` inside helper functions | `pcb_ir.py:472-722` |
| H17 | `snap_to_node` O(n) fallback with up to 500K nodes | `graph.py:252-263` |
| H18 | Multi-net routing doesn't mark routed traces as obstacles — potential short circuits | `pathfinder.py:103-140` |
| H19 | Direct disk writes without backup/atomic write in `update_footprint_from_library` | `pcb_ir.py:409-411` |
| H20 | No token validation at API boundary for `run_pipeline(token)` | `real_dataset.py:320` |
| H21 | f-string interpolation into S-expressions without escaping quotes/backslashes | `pcb_ir.py:595-614` |

### User Experience

| ID | Finding | File |
|----|---|---|
| H22 | Bus operations (`add_bus`/`remove_bus`) are stubs — return success but do nothing | `executor.py:285-289` |
| H23 | Skill SKILL.md references `volta.executor.execute_operation` — ImportError | `skills/SKILL.md:59` |
| H24 | No undo/redo — only rollback via Transaction, no user-facing history | System-wide |
| H25 | Export, ERC/DRC, Placement not exposed as CLI commands or operations | Multiple |
| H26 | Schematic `add_wire` requires exact coordinates — no pin-to-pin routing | `operations/` |
| H27 | Routing results not written back to PCB file | `routing/` |
| H28 | Placement engine disconnected from operation pipeline | `placement/engine.py` |

---

## MEDIUM Findings (13)

| ID | Finding | File |
|----|---|---|
| M1 | Character-level fallback tokenizer destroys semantic structure | `reward_model.py:48-68` |
| M2 | Chain synthesis produces low-diversity templated text | `chains.py` |
| M3 | Reward conflates formatting keywords with reasoning quality | `reward.py` |
| M4 | Corrupted chains have easily exploitable signatures | `chains.py:219-443` |
| M5 | Evaluation only tests discrimination on one corruption type | `evaluation.py:150` |
| M6 | `run_ablation` is a no-op | `evaluation.py:206-220` |
| M7 | MPS device skips attention mask, corrupting pooling | `reward_model.py:145` |
| M8 | No text variable/field substitution support | `project_file.py` |
| M9 | No complex board outline (arcs, cutouts, slots) | `pcb_ops.py` |
| M10 | Broad `except Exception` swallows MemoryError in graph_builder | `graph_builder.py:443` |
| M11 | Global IR registry prevents concurrent execution | `ir/base.py:33` |
| M12 | `pcb_ir.py` (732 lines) and `schematic_ir.py` (734 lines) approaching 800-line limit | Both IR files |
| M13 | Error messages reference Pydantic jargon, not domain language | `handler.py` |

---

## LOW Findings (13)

| ID | Finding |
|----|---|
| L1 | Board dimensions always 0.0 for real PCBs |
| L2 | No gradient accumulation for small batches |
| L3 | Deterministic split without shuffling |
| L4 | macOS-only default library resolver paths |
| L5 | No type narrowing for IR union types |
| L6 | Duplicated `to_shapely`/`to_json` pattern in spatial primitives |
| L7 | No CLI for routing, spatial analysis, or training |
| L8 | Crawler has no persistence/resume on interruption |
| L9 | Cross-file diff has no semantic comparison |
| L10 | PyTorch not listed as dependency in pyproject.toml |
| L11 | No caching in library resolver |
| L12 | Connectivity graph rebuilt from scratch, not incremental |
| L13 | README says 19 operations, schema has 35 |

---

## Top 3 Recommendations (by impact)

### 1. Bridge routing engine to PCB writes
The routing engine (A*, differential pairs, interactive sessions) is the most architecturally sophisticated subsystem but is completely disconnected. Adding a `RoutingResult → (segment ...) → PCB file` bridge unlocks the core value proposition.

**Effort:** ~2-3 files, ~200 lines of bridge code.

### 2. Fix GRPO training pipeline
Either:
- **(A)** Integrate a pre-trained causal LM (e.g., Qwen2.5-0.5B, Phi-3-mini) as the policy model with actual autoregressive generation, or
- **(B)** Reframe honestly as **supervised reward model training** and drop the GRPO framing — the current reward model architecture is actually good for this.

**Effort:** (A) = significant (new model, generation loop, real KL); (B) = minimal (rename, remove circular references, fix optimizer).

### 3. Add human-friendly CLI subcommands
Expose the 35 operations, ERC/DRC, export, and placement as subcommands:
```
volta erc board.kicad_sch
volta drc board.kicad_pcb
volta export gerber board.kicad_pcb
volta context /path/to/project
```

**Effort:** ~1 file modification, ~100 lines of argparse additions.

---

## Individual Review Reports

Full text of each specialist review is available at:
- `/tmp/council_ml_pipeline.md` — 18 findings (3C, 6H, 7M, 3L)
- `/tmp/council_architecture.md` — 24 findings (3C, 6H, 8M, 4L) + 6 missed capabilities + 4 optimizations
- `/tmp/council_kicad_domain.md` — KiCad domain gaps (layer stackup, zone fill, hierarchical schematics, DRU integration)
- `/tmp/council_code_quality.md` — 7 HIGH + 4 MEDIUM code quality issues
- `/tmp/council_user_experience.md` — 5 CRITICAL adoption blockers + 6 HIGH UX gaps
