bretbouchard/kicad-agent/docs/index.md

# volta

AI-safe structural editing of KiCad schematic, PCB, symbol library, and footprint files.

**LLM -> JSON intent -> AST mutation -> valid KiCad file. Zero corruption, every time.**

## Key Features

- **Zero-corruption editing** -- Every mutation goes through validation gates before commit
- **19 operations** -- Add, remove, move, modify components, nets, buses, references, and footprints
- **ERC/DRC gates** -- Validation runs via kicad-cli after every edit with automatic rollback
- **4 file types** -- Schematic (.kicad_sch), PCB (.kicad_pcb), Symbol Library (.kicad_sym), Footprint (.kicad_mod)
- **CLI interface** -- Schema export, dry-run validation, verbose output
- **AI generation** -- Template board generation with LLM-driven design critique
- **LTspice integration** -- Parse .asc files, inject simulation commands, analyze waveforms
- **GRPO training** -- Reinforcement learning pipeline with neural reward model

## Quick Install

```bash
pip install volta
```

Requires Python 3.11+ and KiCad 10+ (for ERC/DRC validation).

## Quick Start

```bash
# Print the operation JSON Schema
volta --schema

# Add a component
volta '{"root": {"op_type": "add_component", "target_file": "board.kicad_sch", "library_id": "Device:R_Small_US", "position": {"x": 50.0, "y": 30.0}}}'

# Validate without executing
volta --dry-run operation.json
```

## Documentation

- [Getting Started](getting-started.md) -- Installation and first operation
- [CLI Reference](cli.md) -- Complete command-line documentation
- [API Reference](api/index.md) -- Auto-generated API docs from source
- [Examples](examples/basic-operations.md) -- Walkthroughs with complete JSON operations
- [KiCad Schematic Editor Reference](kicad_docs.md) -- Full KiCad 10.99 docs from PDF
- [KiCad Agent Reference](volta_reference.md) -- Agent-centric distilled reference for schematic editing
- [KiCad PCB Editor Agent Reference](pcb_editor_reference.md) -- Agent-centric distilled reference for PCB editing
- [KiCad GerbView Agent Reference](gerbview_reference.md) -- Agent-centric distilled reference for Gerber viewing

## Links

- [GitHub Repository](https://github.com/bretbouchard/volta)
- [PyPI Package](https://pypi.org/project/volta/)
- [Issue Tracker](https://github.com/bretbouchard/volta/issues)
