bretbouchard/kicad-agent/docs/pcb_editor_reference.md

# KiCad PCB Editor Agent Reference

**Distilled from:** KiCad 10.99 PCB Editor Reference Manual

Agent-centric reference for programmatic KiCad PCB editing. This document contains
the technical details an AI agent needs when creating, modifying, or validating KiCad
PCB files through the volta operation system. Covers board setup, layer
configuration, design rules and constraints, footprints, pads, zones, routing,
teardrops, backdrills, net classes, DRC, and manufacturing outputs.

GUI navigation, hotkeys, toolbar descriptions, mouse/keyboard shortcuts, display
settings, color themes, and viewport controls are excluded — agents interact with
KiCad files programmatically, not through the GUI.

---

## Board editor layers

Board editor layers
The Board Editor Layers page lets you rename layers, disable non-copper layers that will not be used in the
design, and add additional user-defined layers for documentation or other purposes. For example, if you will
not use a back silkscreen on the design, uncheck the box next to the B.Silkscreen layer. Some layers, like
copper layers, courtyard layers, and Edge.Cuts , are required layers and therefore cannot be disabled.

NOTE

Copper layers can be designated as signal, power plane, mixed, or jumper in the Board
Editor Layers section. This designation is intended as a guide for the user only. Tracks and
zones can be routed on any copper layer, no matter what the type is configured to in this
dialog.

You can add additional user-defined layers ( User.1 , User.2 , etc.) by clicking the Add User Defined Layer…
button in the top right. User-defined layers can’t be used for routing, but they can contain arbitrary graphics

or other information. By default, user layers are auxiliary layers, meaning that whatever information they
contain does not correspond to either the front or back of the board. User layers can instead be set to Offboard, front or Off-board, back, in which case they correspond to the selected side of the board. Items on
such layers can be flipped from front to back in the same way as objects on physical front/back layers.
Adjacent front/back layers are treated as paired: if User.2 is defined as a front layer and User.3 is defined
as a back layer, flipping an object on User.2 will move it to User.3 , and vice versa.

---

## Physical stackup

Physical stackup
The Physical Stackup page controls the board layers that are part of the PCB layer stackup: copper layers,
dielectric layers, solder mask, and silkscreen.
NOTE

Use the Board Editor Layers page to add non-physical layers, configure names for all
layers, and enable or disable optional layers.

Set the number of copper layers in the upper left corner and then enter the physical parameters of the
stackup if desired. These parameters may be left at their default values, but note that the board thickness
value will be used when exporting a 3D model of the board, and layer thicknesses will be included in net
length calculations for any nets that include vias. If you plan to use these features, it is a good idea to ensure
that the stackup thickness is correct. Dielectric, soldermask, and silkscreen layers can have colors assigned
to them, which affects the board’s appearance in the 3D viewer and in 3D model exports.

NOTE

KiCad currently only supports stackups with an even number of copper layers. To create
designs with an odd number of layers (for example, flexible printed circuits or metal-core
printed circuits), simply choose the next highest even number and ignore the extra layer.

The Board thickness from stackup value at the bottom of the page is automatically calculated based on the
stackup parameters in the table. You can automatically adjust the thickness of dielectric layers by pressing
the Adjust Dielectric Thickness button and entering an overall thickness for the PCB. The thickness of the
dielectric layers will be adjusted to meet the overall PCB thickness. Any dielectric layers that are locked (the
column is checked) will not be adjusted.

---

## Board finish

Board finish
The Board Finish section has settings for defining the copper finish and special features such as castellations
or edge plating. Note that these settings only impact the board attributes output as part of Gerber job files at
this time.

---

## Solder mask/paste

Solder mask/paste
The Solder Mask/Paste section allows global adjustment of the clearance (positive or negative) between
solder mask / solder paste shapes and the copper shapes of the parent pads. These values are global settings,
but they will be superseded by any clearance overrides set on individual footprints or pads. Positive
clearance values will result in the shape of the solder mask or paste opening being larger than the copper
shape. Negative clearance values will result in the opening being smaller than the copper shape.

WARNING

Most commercial PCB fabricators expect these values to be zero and make their own
adjustments to solder mask and paste openings as part of their CAM process. It is usually
best to leave these values at their default of zero unless you are making the PCB yourself
or have specific advice from your fabricator to use different values.

Solder mask expansion is a global setting to specify the size of a solder mask opening relative to the
parent pad size. If it is 0 , solder mask openings will be the same size as the pad. Positive values mean
solder mask openings will be larger than pads. Negative values mean solder mask openings will be
smaller than pads. This global value is overridden by expansion settings in individual footprints or pads.
Solder mask minimum web width is the minimum width of webs between solder mask openings, or in
other words, the minimum distance between solder mask openings. Any solder mask openings that are
closer than this minimum distance will be plotted as a single merged opening.
Solder mask to copper clearance is the minimum distance between a solder mask opening and copper
with a different net than the opening’s parent copper. Distances smaller than this minimum will result in
a DRC error.
Allow bridged solder mask apertures between pads within footprints controls whether a DRC
violation occurs when multiple pads in the same footprint share a single solder mask opening. This
situation can occur when multiple solder mask openings are merged due to the minimum solder mask
web width setting.
Tent vias controls whether vias are tented (covered with solder mask) on the top and bottom layers of
the board. Front and back tenting can be controlled independently. Individual vias can override this
setting in their via properties.
Solder paste clearance is a global setting to specify the solder paste shape relative to the parent pad
size (the size difference between the pad shape and the aperture shape on the F.Paste and B.Paste
layers). This can be specified as an absolute offset from the pad edge (e.g. -0.1mm ), a value relative to the
pad dimension (e.g. -5% ), or both (e.g. -0.1mm - 5% ). If it is 0 or blank, the solder paste aperture will be
the same size as the pad. Positive values mean solder paste aperture larger than the pad. Negative values

mean solder paste aperture smaller than the pad. This global value is overridden by paste clearance
settings in individual footprints or pads.

---

## Zone hatch offsets

Zone hatch offsets
The Zone Hatch Offsets page lets you configure default per-layer offsets for zone hatch patterns. X and Y
offsets can be configured separately. Per-layer hatch offsets can be used to force the hatching grid to be
offset from one layer to another, which is required in some applications. You can override these defaults for
individual zones in the Properties dialog for the zone.

---

## Configuring text and graphics

Configuring text and graphics
The Text & Graphics section contains formatting settings for text objects, graphic shapes, and dimension
objects. It also allows configuring project text variables.

Defaults

---

## Defaults

Defaults
The Defaults section of the Board Setup dialog is used to configure the properties that will be used for new
text and graphic shapes that are placed on the board.

Line thickness, text size, and text appearance can be configured for the six different categories of layers
shown in the dialog. These default settings are automatically applied to new text and graphic objects based
on the new object’s layer. These settings can be overridden on a per-object basis in that object’s properties,
however.
Additionally, the default properties for dimension objects can be configured for all layers. For more details
about dimension properties, see the dimensions section.
The Defaults page also contains default settings for new zones. The settings configured here are applied to
newly-created zones, but can be overridden on a per-zone basis in the zone’s properties.

---

## Formatting

Formatting
The Formatting section contains controls for how to format certain board items.

The Dashed Line section controls the appearance of dashed lines. Dash length controls the length of dashes,
while Gap length controls the spacing between dashes and dots. The dash and gap lengths are relative to the
line width: a gap length of 2 means twice the width of the line.
The checkboxes at the bottom of the page control how the settings from the Defaults page are automatically
applied to footprints that are added to the board.
Apply board defaults to footprint fields: if checked, default settings will be applied to footprint fields.
Apply board defaults to footprint text: if checked, default settings will be applied to footprint text
objects.
Apply board defaults to non-copper footprint shapes: if checked, default settings will be applied to
graphic shapes on non-copper layers in footprints. Graphic shapes on copper layers will not be modified.
Apply board defaults to footprint dimensions: if checked, default settings will be applied to footprint
dimensions.
Apply board defaults to footprint barcodes: if checked, default settings will be applied to footprint
barcodes.

Text variables
Project text variables can be created in the Text Variables section. KiCad will substitute the variable name
with the text string assigned to the variable. This substitution happens anywhere the variable name is used
inside the variable replacement syntax of ${VARIABLENAME} .

For example, you could create a variable named VERSION and set the text substitution to 1.0 . Now, in any
text object on the PCB, you can enter ${VERSION} and KiCad will display this as 1.0 . If you change the value
to 2.0 , every text object that includes ${VERSION} will be updated automatically. You can also mix regular
text and variables. For example, you can create a text object with the text Version: ${VERSION} which will
be displayed as Version: 1.0 .
Text variables can also be created in Schematic Setup. Text variables are project-wide; variables created in
the schematic editor are also available in the board editor, and vice versa.
There are also a number of built-in system text variables.

---

## Design rules overview

Configuring design rules
Design rules control the behavior of the interactive router, the filling of copper zones, and the design rule
checker. Design rules can be modified at any time, but we recommend that you establish all known design
rules at the beginning of the board design process.

---

## Constraints

Constraints
Basic design rules are configured in the Constraints section of the Board Setup dialog. Constraints in this
section apply to the entire board and should be set to the values recommended by your board manufacturer.
Any minimum value set here is an absolute minimum and cannot be overridden with a more specific design
rule. For example, if you need the copper clearance on part of a board to be 0.2mm and in the rest 0.3mm,
you must enter 0.2mm for the minimum copper clearance in the Constraints section and use a net class or
custom rule to set the larger 0.3mm clearance.

In addition to setting minimum clearances, a number of features can be configured here:

Setting

Description

Arc/circle approximated

In some situations, KiCad must use a series of straight line segments to

by segments

approximate round shapes such as those of arcs and circles. This setting
controls the maximum error allowed by this approximation: in other words,
the maximum distance between a point on one of these line segments and the
true shape of the arc or circle. Setting this to a lower number than the default
value of 0.005mm will result in smoother shapes, but can be very slow on
larger boards. The default value typically results in arc approximation error
that is not detectable in the manufactured board due to manufacturing
tolerances.

Allow fillets outside

Zones can have fillets (rounded corners) added in the Zone Properties dialog.

zone outline

By default, no zone copper, including fillets, is allowed outside the zone
outline. This effectively means that inside corners of the zone outline will not
be filleted even when a fillet is configured. By enabling this setting, inside
corners of the zone outline will be filleted even though this results in copper
from the zone extending outside the zone outline.

Minimum thermal relief

This sets the minimum acceptable number of thermal relief spokes connecting

spoke count

a pad to a zone. A DRC violation will be generated if this constraint is violated.

Include stackup height

By default, the length tuner uses the height of the stackup to calculate the

in track length

additional length of a track that travels through vias from one layer to

calculations

another. This calculation relies on the board stackup height being correctly
configured. In some situations, it is preferable to ignore the height of vias and
just calculate the track length assuming that vias add no length. Disabling this
setting will exclude via length from length tuner track length calculations.

Pre-defined sizes
The Pre-defined Sizes section allows you to define the track and via dimensions you want to have available

---

## Net classes

Net classes
The Net Classes section allows you to configure routing and clearance rules for different classes of nets.
More than one net class can be assigned to a net. For nets with multiple net classes assigned, an effective
aggregate net class is formed, taking any net class properties from the highest priority net class which has
that property set. Net class priority is determined by the ordering in the Schematic or Board Setup dialogs.
The Default net class is used as a fallback for any missing properties after all explicit net classes have been
considered; this means that nets may be part of the Default net class even if they have other net classes
explicitly assigned.
Net classes may be created and edited in either the Schematic or Board Setup dialogs.

The upper portion of the Net Classes section contains a table showing the net classes in the design and the
design rules that apply to each net class. Some columns in the table may be hidden or scrolled to the side.
You can show or hide columns in the table by right-clicking on the table header and checking or unchecking
columns in the menu.
Every class has values for copper clearance, track width, via sizes, and differential pair sizes. These values
will be used when creating tracks and vias unless a more specific rule overrides them (see Custom Rules

below).

NOTE

No rule may override the minimum values set in the Constraints section of Board Setup.
For example, if you set a net class clearance to 0.1 mm , but the Minimum Clearance in the
Constraints section is set to 0.2 mm , nets in that class will have a clearance of 0.2 mm .

The track widths and via sizes defined for each net class are used when the track width and via size controls
are set to "use netclass values" in the PCB editor. These widths and sizes are considered the default, or
optimal, sizes for that net class. They are not minimum or maximum values. Manually changing the track
width or via size to a different value from that defined in the Net Classes section will not result in a DRC
violation. To restrict track width or via size to specific values, use Custom Rules.
You can assign a tuning profile to a net class in the Tuning Profile column. This assigns per-layer track
geometry (track width and differential pair gap) and propagation delays for tracks and vias belonging to
that net class. Like other net class values, the interactive router uses these values for routing tracks. The
length tuner also uses the propagation delays from the tuning profile when tuning tracks in time-domain
mode. DRC violations can optionally be generated for tracks that don’t match their tuning profile’s geometry
by setting the severity of the "Tuning profile track geometries" violation to either Warning or Error.
Each net class can also have a color assigned to it using the PCB Color column. Depending on how net colors
are configured in the appearance panel, net class colors can override the default color for ratsnest lines or
copper objects. In addition to arbitrary colors for each net class, you can set all net classes to use the same
color as configured for them in the schematic editor by clicking the Import colors from schematic button.
To use a layer’s default color instead of overriding it with a custom net class color, set the net class color to
transparent.
The lower portion of the Net Classes section lists pattern-based net class assignments. Working with patternbased net class assignments is explained in the Schematic Editor documentation; pattern-based assignments
can be edited in either the Board or Schematic Setup windows.
Note that pattern-based assignments can be created directly from the PCB editing canvas by right clicking a
copper track or zone and clicking Assign netclass…. Net classes can also be assigned in the schematic using
net class directives or labels instead of pattern-based assignments.

Component classes
The Component Classes section allows you to create rules that automatically assign components to
component classes. In addition to these automatic assignments, you can manually assign component classes
in the Schematic Editor.
Component classes are named groupings of components: they are assigned to symbols in the schematic or to
footprints in the board, but however they are assigned they apply to both the symbols and the
corresponding footprints. They can be used to group symbols into channels for multichannel designs and
can also be used to group footprints in custom DRC rules. Components can have more than one class.

Enabling the Assign component class per sheet will create a component class for every sheet in the
schematic and assign each component in the sheet to that sheet’s component class.
You can add a rule for assigning a component class by clicking the Add Custom Assignment button. Enter
the name of the component class you want to assign in the Component class textbox, then add a condition
for when to assign the class by pressing the

button and selecting a type of condition from the menu that

appears.
The following types of conditions are available:
Reference: matches by footprint reference designator. More than one reference designator can be given
as a comma-separated list. The reference field support wildcards: * matches any number of any
characters, including none, and ? matches any single character. Pressing the

button uses the selected

footprints' reference designators in the condition.
Footprint: matches by footprint library and identifier. The footprint field support wildcards: * matches
any number of any characters, including none, and ? matches any single character. Pressing the
button opens a window to choose a footprint from your libraries.
Side: matches by side of the PCB (front, back, or any).
Rotation: matches by footprint rotation angle.
Footprint Field Value: matches by the value of a specified footprint field. The field name and value
support wildcards: * matches any number of any characters, including none, and ? matches any single
character.
Sheet: matches by the name of the schematic sheet containing the footprint’s linked symbol.

Custom Expression: matches by a custom DRC rule condition clause, which matches footprints that
satisfy the clause. For example, A.intersectsArea('some_area_name') matches any footprints that
intersect the named area some_area_name .
You can add multiple conditions to a single rule. If Match all is selected, the component class will be
assigned to any components that match all of the conditions. If Match any is selected, the component class
will be assigned to components that match any of the conditions.
You can test a component class rule by pressing the

button, which highlights all footprints that match the

rule in the editing canvas.
To delete a condition, press the
press the

button next to the condition. To delete a rule and all of its conditions,

button next to the component class name.

Understanding component classes
A component class is a named label attached to one or more footprints. Unlike net classes, which apply to
nets and affect electrical characteristics like clearance and track width, component classes apply to
footprints and are used for organizational and rule-scoping purposes.
Common uses for component classes include:
Defining channels in multichannel designs
Scoping custom DRC rules to specific groups of components
Organizing components by function, voltage domain, thermal requirements, or any other design-specific
criteria

Where component classes are defined
Component classes can be defined in the schematic editor or in the PCB editor’s Board Setup.
Definition Method

Editor

Description

Component Class field

Schematic

Assigns the class to all symbols within the rule

on a directive label in a

area. See Schematic Editor: Component Classes.

rule area
Component Class

Schematic

symbol field
Assignment rules in

Assigns the class directly to an individual symbol
by adding a Component Class field to its properties.

PCB

Board Setup

Assigns classes to footprints based on conditions
such as reference designator, footprint identifier,
board side, rotation, field values, sheet
membership, or custom DRC expressions. These
are configured in Board Setup → Design Rules →
Component Classes.

Automatic sheet-based
classes

PCB

When Assign component class per sheet is
enabled in Board Setup, a component class is
automatically created for each schematic sheet and
assigned to all components on that sheet.

Schematic-defined classes are carried to the PCB during Update PCB from Schematic. They persist in the
board file and do not change unless the schematic is modified and the PCB is updated from the schematic.
PCB-defined classes come from the assignment rules in Board Setup and are re-evaluated whenever the
board state changes, for example when a footprint is moved to the other side of the board.

How multiple classes combine
A footprint can belong to more than one component class. When it does, all of the footprint’s class names are
sorted alphabetically and displayed as a comma-separated list. For example, a footprint belonging to both
Power_Stage and Channel_A is shown as Channel_A, Power_Stage .

You can check a footprint’s component class by selecting it and viewing the Component Class field in the
Properties Panel or the status bar.

TIP

In custom DRC rules, use A.hasComponentClass('ClassName') to test whether a footprint
belongs to a specific named class, regardless of what other classes the footprint may also
belong to.

Schematic-defined and PCB-defined classes
Component class assignments fall into two categories:
Schematic-defined classes come from Component Class fields on symbols or directive labels in the
schematic. These assignments are transferred to the PCB during Update PCB from Schematic and
persist in the board file. They do not change unless the schematic is modified and the PCB is updated
from the schematic.
PCB-defined classes come from the assignment rules configured in Board Setup → Design Rules →
Component Classes. These rules are re-evaluated whenever the board state changes (for example, when
a footprint is moved to the other side of the board, or when the board is updated from the schematic).
PCB-defined classes are not stored per-footprint; they are computed on demand.
A footprint’s effective class is the union of all its schematic-defined and PCB-defined class assignments. For
example, if a footprint has the schematic-defined class Analog_Frontend and also matches a Board Setup
rule that assigns High_Speed , its component class will be Analog_Frontend, High_Speed .

Assignment rule details
Each assignment rule in the Component Classes panel of Board Setup consists of:

1. A component class name — the class that will be assigned to matching footprints.
2. One or more conditions — criteria that footprints must satisfy.
3. A match operator — either Match all (AND logic: all conditions must be true) or Match any (OR logic:
at least one condition must be true).
The following table summarizes the available condition types:

Condition Type

Parameters

Reference

Comma-separated list of reference designators (wildcards * and ?
supported)

Footprint

Library-qualified footprint name (wildcards supported)

Side

Front , Back , or Any

Rotation

Rotation angle in degrees, or Any

Footprint Field

Field name and value (wildcards supported for both)

Sheet

Schematic sheet name

Custom Expression

Arbitrary DRC expression

Each condition is compiled into a DRC expression that is evaluated against every footprint. If the built-in
condition types are not sufficient to capture your desired conditions, you can use the Custom Expression
type to directly specify your condition as a DRC expression. The table below lists the DRC expression
generated for each built-in condition type. You can use these expressions as a starting point for writing
custom conditions.
Condition Type

Generated DRC Expression

Reference

A.Reference == 'R1' || A.Reference == 'R2'

Footprint

A.Library_Link == 'Resistor_SMD:R_0402_1005Metric'

Side

A.Layer == 'F.Cu' or A.Layer == 'B.Cu'

Rotation

A.Orientation == 90 deg

Footprint Field

A.getField('Voltage') == '3.3V'

Sheet

A.memberOfSheet('SheetName')

When multiple conditions are combined with Match all, they are joined with && (logical AND). When
combined with Match any, they are joined with \|\| (logical OR).

Assignment rule examples
The following examples illustrate common assignment rule patterns.
Example 1: Assign by reference designator
To assign all bypass capacitors (C1, C2, C3) to a Bypass_Caps class:
Component class: Bypass_Caps
Condition: Reference = C1,C2,C3
Example 2: Assign by footprint with wildcards

To assign all 0402-sized resistors to a Small_Passives class:
Component class: Small_Passives
Condition: Footprint = Resistor_SMD:R_0402*
Example 3: Assign by board side and rotation
To create a class for all components on the back side at 90-degree rotation:
Component class: Back_Rotated
Match all (both conditions must apply)
Condition 1: Side = Back
Condition 2: Rotation = 90
Example 4: Assign by footprint field value
To group all components with a Voltage field set to 3.3V :
Component class: 3V3_Domain
Condition: Footprint Field = Field name: Voltage , Value: 3.3V
Example 5: Assign by sheet membership
To assign all components from a specific hierarchical sheet:
Component class: ADC_Channel
Condition: Sheet = /ADC
Example 6: Assign using a custom DRC expression
To assign all footprints that intersect a named rule area:
Component class: Critical_Region
Condition: Custom Expression = A.intersectsArea('high_density_zone')

How classes update
When you run Update PCB from Schematic (Tools → Update PCB from Schematic… or

F8

), component

classes are re-transferred from the schematic to the PCB. For each footprint, classes that were deleted in the
schematic are removed, and new classes from the schematic are added. Each footprint’s schematic-defined
class assignments are then combined with PCB-defined assignments from Board Setup to form the
footprint’s effective component class.

NOTE

The Component Class field that appears on footprints in the PCB editor is read-only. It
reflects the combination of schematic-defined and PCB-defined class assignments. To
change a schematic-defined class, edit the corresponding symbol in the schematic and
update the PCB.

Using component classes in custom DRC rules
Component classes can be referenced in custom design rules to scope constraints to specific groups of
components. The primary mechanism is the hasComponentClass() expression function, which returns true
if a footprint belongs to the named class. You can also use the graphical design rule editor to create rules that
reference component classes.
For example, to enforce a minimum clearance on all items belonging to footprints in the Power_Stage class:
(rule "Power component clearance"
(condition "A.hasComponentClass('Power_Stage')")
(constraint clearance (min 0.3mm))
)

To enforce courtyard clearance between two component classes:
(rule "Keep analog away from digital"
(condition "A.hasComponentClass('Analog') && B.hasComponentClass('Digital')")
(constraint courtyard_clearance (min 2mm))
)

See Custom Design Rules for the full expression language reference and additional examples.

---

## Custom rules

Custom rules
The Custom Rules section contains a text editor for creating design rules using the custom rules language.
Custom rules are used to create specific design rule checks that are not covered by the basic constraints or
net class settings.
Custom rules will only be applied if there are no errors in the custom rules definitions. Use the Check Rule
Syntax button to test the definitions and fix any problems before closing Board Setup.
See Custom Design Rules in the Advanced Topics chapter for more information on the custom rules language
as well as example rules.

Violation severity
The Violation Severity section allows you to configure the severity of each type of design rule check. Each
rule may be set to create an error marker, a warning marker, or no marker (ignored).

NOTE

Individual rule violations may be ignored in the Design Rule Checker. Setting a rule to
Ignore in the Violation Severity section will completely disable the corresponding design
rule check. Use this setting with caution.

For descriptions of each violation type, and how to ignore individual violations without disabling all
violations of that type, see the DRC documentation.

Embedding files
External files can be embedded within a board file. Embedding a file stores a copy of the file inside the board
file. The design can then refer to the embedded copy of the file instead of the external file, which makes the
project more portable as it doesn’t rely on an external file. Fonts, datasheets, drawing sheets, SPICE models,
and footprint 3D models can be embedded and used within KiCad. Other arbitrary files can also be
embedded to store them in the project for later export, but they are not used by any KiCad functionality.
Files embedded in a board necessarily increase the board’s file size, although files are compressed before
being embedded to minimize the space required.

Embedded files are managed in the Embedded Files section of Board Setup. All files embedded in a board
are shown here. To embed a file inside a board, click the

button and select the file. The file is then

embedded inside the PCB and is listed in the embedded files list along with its embedded reference. The
embedded reference is a unique identifier for the embedded file that begins with kicad-embed:// . You can
use the embedded reference elsewhere in the Board Editor to refer to the embedded file as if it were an
external file path. You can copy the embedded reference by right clicking and selecting Copy Embedded
Reference. To remove an embedded file, click the

button. Any remaining links to the removed file will

become invalid.

NOTE

3D models and drawing sheets can be embedded directly using the file browser when you
add them to a footprint (3D models) or to a board (drawing sheets) by enabling the
Embed Files option in the file browser. This is a single-step shortcut for adding the files in
Board Setup and then referring to them by their embedded reference; the result is the
same.

To embed any fonts used in a board, check the Embed fonts checkbox. All fonts used in the board design will
be embedded, so text using that font can be edited on any computer regardless of whether the font file is
installed.
You can also embed files in a footprint, either in the board copy of a footprint or in a library. Such files will
be available within the footprint instance but not within the larger board design or within other footprints.
Files embedded in a footprint are deduplicated when the footprint is added to a board: if a file is embedded
in a footprint, and multiple instances of that footprint are added to the board, only one copy of the file will
be embedded, and all of the footprint instances will refer to the same embedded file.

As an example, to embed a 3D model in a project and use it within several footprints, you could embed the
model using the Board Setup dialog, copy the internal reference, and paste the internal reference as a 3D
model path in each footprint that uses that model. Alternatively, you could embed the model within a single
footprint, either in the board or in the source footprint library. In this case, the footprint itself is portable if
you export the footprints from the board, and the model embedding is managed in the footprint’s
properties rather than Board Setup. A more convenient way to achieve the same thing, however, is to open
the footprint’s properties dialog, add a 3D model file, and enable the Embed File option in the file browser.
Again, this could be done for a footprint in the board or for a footprint in the source footprint library.

NOTE

You can embed all of your board’s footprints at once using Tools → Collect and Embed 3D
Models. This takes every external 3D model referenced by the board’s footprints and
embeds the models in the board. The 3D model references in each footprint are replaced
by references to the corresponding embedded files.

Files can also be embedded in schematics.

Importing settings
You can import part or all of the board setup from an existing board. This technique can be used to create a
"template" board that has the settings you want to use on multiple designs, and then importing these
settings from the template board into each new board rather than entering them manually.
TIP

If you are frequently importing settings from a specific board, consider making a template
project from that design.

To import settings, click the Import Settings from Another Board… button at the bottom of the Board
Setup dialog and then choose the kicad_pcb file you want to import from. Select which settings you want to
import and the current settings will be overwritten with the values from the chosen board.
The settings that are available to import are:
Board layers and physical stackup
Solder mask/paste defaults
Zone hatched fill offsets
Text and graphics default properties
Text & graphics formatting
Design rule constraints
Predefined track & via dimensions
Teardrop defaults
Length-tuning pattern defaults
Net classes
Component classes

Tuning Profiles
Custom rules
Violation severities

Editing a board

---

## Board outlines (Edge Cuts)

Board outlines (Edge Cuts)
KiCad uses graphical objects on the Edge.Cuts layer to define the board outline. The outline must be a
continuous (closed) shape, but can be made up of different types of graphical object such as lines and arcs, or
be a single object such as a rectangle or polygon. If no board outline is defined, or the board outline is
invalid, some functions such as the 3D viewer and some design rule checks will not be functional.
KiCad displays closed board outlines with a shaded interior, which is called the board area shadow. The
shadow is only drawn for closed outlines, so you can use the shadow to check that the board outline is
properly closed. It also indicates which regions are solid, as opposed to cutouts. You can adjust the color of
the board area shadow, or hide it entirely, in the Objects tab of the Appearance panel.

For the board outline to be considered valid, the endpoints of any shapes in the outline must coincide
exactly. If any endpoints are not coincident with another endpoint, the outline will not be considered closed.
Outline shapes also cannot intersect each other or overlap. In such cases, DRC will report a "Board has
malformed outline" violation that points to the problematic parts of the outline.
NOTE

You can use the grid or the snapping tools to ensure outline endpoints exactly coincide.
The Heal Shapes tool can also be used to fix small gaps between endpoints.

If there are multiple closed shapes on the Edge.Cuts layer, each shape acts as an independent board outline.
When an outline shape completely encloses another outline, the outermost shape is considered the outside
edge of the board. Any closed shapes inside the outer shape are considered interior cutouts in the board.
Each closed outline cannot intersect or overlap with other outlines.
Zones only fill when they are within the board outline. Any portion of a zone that is outside of the board
outline, including inside an interior cutout, will not be filled.

---

## Working with footprints

Working with footprints
Adding footprints to the board
Footprints are automatically added to the board when the PCB is updated from the schematic. The footprint
associated with each schematic symbol is added to the board if it is not already present, and each footprint
pad is associated with the corresponding symbol pin’s net. Symbol pins are matched to footprint pads by
pin/pad number.
When footprints are added to the board after an update from the schematic, they are clustered by schematic
sheet and by geographical location in the schematic. They are initially attached to the cursor; you can place
them by clicking in the desired location.
You can also add footprints to the board manually using the Add Footprint tool ( A or the

NOTE

button).

Footprints added in this way will not be automatically associated with a symbol or have
nets assigned to their pads, and subsequent updates from the schematic will remove these
unassociated footprints unless the footprint is locked or the Delete footprints with no
symbols option is unchecked in the Update PCB From Schematic dialog. For these
reasons, it is usually recommended to avoid manually adding footprints to the board.
Manually adding footprints is necessary for PCB-only workflows, and can also be useful
for adding logos or other footprints that do not need a corresponding schematic symbol.

Placing and moving footprints
Once footprints have been added to the board, you can reposition them in many ways.
The Move command ( M ) moves a footprint or a selection of footprints, ignoring any connected track
segments that are not selected. No DRC checking is done when moving footprints with the Move command,
although any footprint courtyards that collide with the moved footprint’s courtyard will be highlighted.
There is a reference point for the move operation, which is the point in the footprint which attaches to the
cursor and therefore the point in the footprint that snaps to the grid and to other objects. The reference
point during a move is determined by the location of the cursor when the Move command is initiated. If the
cursor is over a pad, the pad’s center will be used as the reference point. If the cursor is not over a pad, the
footprint’s anchor (coordinate origin point) will be used. To select an arbitrary snapping point, you can use

the Move With Reference command instead of the regular Move command (right click → Move with
Reference). After initiating the command, click on the desired reference point; KiCad will then begin the
move with that point as the reference.
You can also use the Drag command ( D ) to move the selected footprint using the interactive router,
maintaining all track connections to the footprint. Dragging footprints behaves like the Highlight Collisions
router mode: obstacles will not be avoided or shoved, only highlighted. Ordinarily the router will prevent
you from dragging a footprint into a position that violates DRC: when you click to commit a drag in a
position that violates DRC, the footprint will return to its original position. To force a drag to be committed
even if it violates DRC,

Ctrl

-click to commit the drag. Like the Move command, colliding courtyards are

highlighted.

NOTE

Only tracks that end at the origin of the footprint’s pads will be dragged. Tracks that
simply pass through the pad or that end on the pad at a location other than the origin will
not be dragged.

You can move a footprint to the opposite side of the board with the Flip command ( F ). Any parts of the
footprint on a front layer will be swapped to the corresponding back layer, and vice versa.
Footprints can be rotated counter-clockwise using the

R

hotkey, or clockwise using Shift + R . By default,

footprints are rotated by 90 degrees every time the rotate command is used, but you can configure the
rotation angle step in Preferences → PCB Editor → Editing Options.
You can directly set a footprint’s exact absolute position, rotation angle, and PCB side using either the
Footprint Properties dialog or the Properties panel.
To reposition a footprint relative to its current position, use the Move Exactly tool ( Shift + M or right click
→ Position → Move Exactly…). The dialog lets you specify an X and Y translation, as well as a rotation, that
will be applied to the footprint. The rotation can be performed relative to either the footprint’s anchor, the
local coordinate origin, or the drill/place origin. You can also use polar coordinates instead of Cartesian
coordinates.

To position a footprint relative to another object, you can use the Position Relative tool ( Shift + P or right
click → Position → Position Relative To…). With this tool, you select a reference point for the move and
specify an offset. The footprint is moved to the specified offset relative to the reference point. The reference
point can be one of the following:
The local origin, which is set to the cursor position when you press

Space

.

The grid origin, which is configured in the Grids dialog.
The location of an arbitrary item on the board, such as a specific pad in a footprint. After clicking the
Select Item…button, click on the desired board item in the canvas to set the reference point.
An arbitrary point in the canvas. After clicking the Select Point…button, click at the desired location to
set the reference point. You can use object snapping to select a specific point in an object, such as the end
of a graphic line.

To position a footprint such that an arbitrary point in the footprint is positioned a certain distance from
another arbitrary reference point, you can use the Interactive Offset tool (right click a footprint → Position
→ Interactive Offset Tool…).
This tool lets you interactively select two points that form the start and end of a position vector. The first
point is a reference point in the footprint, and will move along with the footprint. The second point is a fixed
reference that will remain stationary when the footprint is moved. The vector from the first point to the
second point is shown graphically in the editing canvas. You can then give new X and Y (or polar) dimensions
for the vector, which will move the footprint reference relative to the fixed reference such that the fixed
reference is the specified distance from the footprint reference point. The dialog initially contains the vector
dimensions before any move is performed, or in other words the initial distance between the footprint
reference point to the fixed reference.

You can swap the position of two selected footprints using the Swap command ( Alt + S ). The first footprint
is assigned the location, rotation, and board side of the second footprint, and vice versa. If there are more
than two footprints selected, the locations are cycled: the last footprint gets the position of the first
footprint, the first footprint gets the location of the second, and so on.

There are several convenience features that make it easier to find, select, and move specific footprints or
footprints related to another footprint.
The Get and Move Footprint command ( T ) prompts you to choose a footprint from a list or by typing a
reference designator. KiCad then attaches the chosen footprint to your cursor for a move operation.
There are two commands to select other footprints that need to be connected to the selected footprint but
don’t yet have routed connections. The Select All Unconnected Footprints command ( O ) selects all
footprints that have ratsnest lines to the currently selected footprints. The command can be executed
repeatedly to further expand the selection based on the newly selected items. The Grab Nearest
Unconnected Footprint command ( Shift + O ) selects the closest footprint with ratsnest lines to the
currently selected footprint, and additionally begins to move it. If there are multiple footprints initially
selected, the command will act like the Move Individually command described below, individually moving
the closest unconnected footprint for each of the initially selected footprints.
You can select footprints based on their schematic sheet using the right click → Select → Items in Same
Hierarchical Sheet command, which selects all other footprints that are in the same schematic sheet as the
originally selected footprint.
If you want to move multiple selected footprints in sequence, use the Move Individually command ( Ctrl +
M ). After triggering the command, KiCad will begin moving the first selected footprint. After you click to

place the footprint, KiCad will immediately start moving the next footprint, in the same order that you
selected the footprints. You can skip moving a footprint by pressing

Tab

, commit the current move and skip

any remaining moves by double-clicking, or cancel all moves (including those already completed) by
pressing

Esc

.

If you want to move a collection of footprints at once into one area, the Pack and Move Footprints command
( P ) closely packs the selected footprints together and moves them as a block.

TIP

Move Individually and Pack and Move Footprints are useful in combination with other
selection convenience features, such as cross-selection from the schematic or the
advanced footprint selection features described above. For example, you could select a
group of bypass capacitors in the Schematic Editor, switch to the PCB Editor where the
corresponding footprints are now selected, and then use Move Individually to quickly
place all of the bypass capacitor footprints close to their respective ICs. Alternatively, you
could use one of the other selection tools, such as Select All Unconnected Footprints, to
select many footprints from all over the board, then use Pack and Move Footprints to
quickly put them all into a small area.

Finally, KiCad can automatically place footprints onto the board. The auto-place function attempts to
optimally place footprints to simplify ratsnest connections to other footprints. You can auto-place the
selected footprints with Place → Auto-Place Footprints → Place Selected Footprints, or auto-place all
footprints outside of the board outline with Place → Auto-Place Footprints → Place Off-Board Footprints.

Editing Footprints
Footprints in the board can be individually edited, both in terms of their properties (fields, attributes,
clearance settings, etc.) and in terms of their physical pads and graphics. Editing a footprint in the board only
affects that particular instance of the footprint; it does not affect any other copies of that footprint in the
board, and it does not affect the library footprint.

To edit the properties of a footprint in the board, open its properties dialog ( E )

The majority of the settings in this dialog are the same as in the footprint editor. You can edit the footprint’s
fields, attributes, clearance and zone connection settings, 3D models, and embedded files, as in the footprint
editor. However, here you can also set the footprint’s position, orientation, and side. You can also update the
footprint from the library, exchange it for a different footprint, or edit the footprint itself in the footprint
editor.
To edit the footprint’s physical form, i.e. its pads and graphics, you need to use the footprint editor. There
are two buttons for opening a footprint in the editor, depending on whether you want to edit a single copy
of a footprint in the board or a footprint’s source copy in the library.
Edit Footprint… will open the specific instance of the footprint in the footprint editor. Editing this
footprint will only affect this one instance of the footprint in the board. It will not affect other instances
of the footprint in the board, and it will not affect the library copy of the footprint. You can also open a
board footprint in the footprint editor by right clicking the footprint in the board and selecting Open in
footprint editor ( Ctrl + E ).
Edit Library Footprint… will open the library copy of the footprint in the footprint editor. Editing the
library copy of the footprint will edit the footprint in the footprint library, but will not immediately
affect any instances of that footprint in the board. To update footprints in the board with changes to the

library footprint, use the Update Footprint from Library…tool. Editing the library footprint in this way
is equivalent to opening the footprint editor, opening the appropriate footprint in its library, and editing
it.
The Update Footprint from Library… button is used to update the board’s copy of the footprint to match
the copy in the library. The Change Footprint… button is used to swap the current footprint to a different
footprint in the library. These functions are described later.

Editing footprint fields
An individual symbol text field can be edited directly with the

E

hotkey (with a field selected instead of a

footprint) or by double-clicking on the field.

The options in this dialog are the same as those in the full Footprint Properties dialog, but are specific to a
single field.
Only footprint fields can be edited this way in the board editor. Unlike fields, Footprint text is a graphic
object that can only be edited or moved in the footprint editor.

NOTE

In versions of KiCad before version 8.0, footprint fields did not exist. Instead, footprint
text could be edited directly in the board editor. Since KiCad 8.0, footprint text is not
editable in the board editor and can only be edited in the footprint editor.

Updating and exchanging footprints
When a footprint is added to the board, KiCad embeds a copy of the library footprint in the board so that the
board is independent of the system libraries. Footprints that have been added to the board are not
automatically updated when the library changes. Library footprint changes are manually synced to the
board so that the board does not change unexpectedly.
NOTE

You can use the Compare Footprint with Library tool to inspect the differences between a
footprint in a board with its corresponding library footprint.

To update footprints in the board to match the corresponding library footprint, use Tools → Update
Footprints from Library…, or right click a footprint and select Update Footprint…. You can also access the

tool from the footprint properties dialog.

The top of the dialog has options to choose which footprints will be updated. You can update all footprints
on the board, update only the selected footprints, or update only the footprints that match a specific
reference designator, value, or library identifier. The reference designator and value fields support
wildcards: * matches any number of any characters, including none, and ? matches any single character.
The middle of the dialog has options to control what parts of the footprint will be updated. You can select
specific fields to update or not update, which properties of the fields to update (text content, visibility, size
and style, and position), and how to handle fields that are missing or empty in the library footprint. You can
also choose whether to update clearance overrides and footprint attributes, such as footprint type, not in
schematic, exclude from position files / bill of materials, exempt from courtyard requirement, and do
not populate.
The bottom of the dialog displays messages describing the update actions that have been performed.
To change an existing footprint to a different footprint, use Edit → Change Footprints…, or right click an
existing footprint and select Change Footprint…. This dialog is also accessible from the footprint properties

dialog.

The options for the Change Footprints dialog are very similar to the Update Footprints from Library dialog.

Match pad positions
The Match pad positions option will automatically attempt to compensate for changes in the footprint
origin and orientation in the library. This can happen, for example, if the library changes a part, or you
switch to a library with different zero-orientation conventions.
When this option is off, the update process will not adjust the position of the new footprint. This may result
in disconnected tracks if the library part has changed.
When this option is on, it will attempt to update the position and rotation for minimal impact on the layout.
If a minority of pads have changes position, the footprint will be positioned so as to keep as many
connections as possible untouched. If a majority of pads are moved, the footprint will be positioned so as to
minimise the offsets on average.

Comparing footprints between board and library
When a footprint in a board diverges from the corresponding footprint in the original footprint library, you
can use the Compare Footprint with Library tool to inspect the differences between the two versions of the
footprint. Run the tool using Inspect → Compare Footprint With Library.

The Summary tab shows the name of the footprint, including its library and board reference designator,
and provides a list of the differences between the board and library versions of the footprint.

The Visual tab shows a visual comparison of the board and library versions of the footprint. This can be
used as a visual diff tool.
By default, the comparison displays both versions of the footprint superimposed on each other. To see the
changes more easily, you can drag the slider at the bottom of the tab to the right to emphasize the library
version of the footprint in the superimposed view (making the board version of the footprint more
transparent) or drag it to the left to emphasize the board version (making the library version more
transparent). At the far right and left ends of the slider, the board and library versions of the footprint,
respectively, are fully hidden. It may be helpful to drag the slider back and forth to see the changes more
clearly.
You can press the A/B button, or use the

/

hotkey, to quickly toggle back and forth between the board and

library versions.
The Update Footprint from Library… button opens the Update Footprint from Library tool to update the
footprint to match the library.
The screenshot above shows a visual comparison with the board version of the footprint deemphasized.
Looking at pad 1 on the left, you can see a large, partially transparent pad (from the board footprint)
surrounding a fully opaque, smaller pad (from the library footprint). This indicates that the pad was
enlarged in the board version of the footprint, or shrunk in the library version of the footprint.

---

## Working with pads

Working with pads
The properties of each individual pad of a footprint can be inspected and edited after placing the footprint
on the board. In other words, it is possible to override the design of an individual footprint pad in a specific
instance of the footprint on the board, if the footprint design in the library is not appropriate. For example,
you may wish to remove the solder paste aperture for a pad that needs to remain unsoldered in a specific
design, or you may wish to move the location of a through-hole pad for an axial-lead resistor in order to fit a
specific design.

NOTE

By default, the position of all footprint pads are locked, so it is possible to edit the pad
properties but not move the pad’s location relative to the rest of the footprint. Pads may
be unlocked to allow free movement, which can be useful for certain applications (such as
through-hole footprints with varying lead positions) but is generally never recommended
for surface-mount footprints.

The pad properties dialog is opened through the context menu or default hotkey

E

when a pad is selected.

Note that KiCad assumes that if you click near a pad, you are probably trying to select the entire footprint
rather than a single pad. To select a single pad, make sure to click inside the pad area, or turn off the
Footprints setting in the selection filter (and make sure the Pads setting is turned on) to prevent accidental
selection of the entire footprint rather than a specific pad.

This dialog lets you edit the physical properties of the pad, including size and shape. You can also modify
how the pad connects to other objects on the board, including clearance properties, teardrops, and thermal
reliefs.

This dialog is the same as the pad properties dialog in the footprint editor, except that here you can also
manually assign a net to a pad using the net name selector. The remaining options are explained in the
Footprint Editor documentation.

NOTE

While you can manually assign nets to pads in the PCB editor, this is not a typical
workflow. Usually net-to-pad connections are defined by the schematic and then
transferred to the PCB editor.

---

## Working with zones

Working with zones
Copper zones, also sometimes called copper pours or fills by other EDA tools, are solid or hatched areas of
copper assigned to a particular net that automatically keep clearance from other copper objects. Zones are
commonly used to fill in all free space on a board layer (or a portion of a layer) in order to create ground and
power planes, carry high currents, or to provide shielding.
NOTE

Some EDA tools have separate tools for creating "plane layers" and for creating copper
zones on signal layers. In KiCad, the Copper Zone tool is used for both these applications.

Zones are defined by a polygonal outline that defines the maximum extent of the filled copper area. This
outline does not represent physical copper and will not appear in exported manufacturing data. The actual
copper areas of the zone must be filled each time the outline, or any objects inside the outline, are modified.
Typically all zones in a board are filled at once (default hotkey

B

), but you can also run the filling process

on individual zones (right click → Zones → Draft Fill Selected Zone(s)). Zones may be unfilled (default
hotkey Ctrl + B ) to improve performance and reduce visual clutter while editing large boards.

NOTE

By default, zone filling is a manual process rather than occurring every time an object
changes that would result in a change to the zone copper. This is because zone filling can
be a slow process on older computers or very large designs. It is important to make sure
zone fills are up-to-date before generating outputs. KiCad will check that zones have been
updated and warn you before generating outputs or running DRC when zones have not
yet been refilled. You can optionally enable automatic zone-filling in the Preferences
dialog (PCB Editor → Editing Options → Miscellaneous → Automatically refill zones).

A zone fill occupies any unused space within the zone outline, automatically maintaining a specified
clearance to board edges, holes, and copper objects on different nets. Zones do not fill outside of the board
outline or within interior cutouts.
Each zone also has a priority. Zone priority determines the order in which multiple zones on a single layer
are filled. The highest priority level zone on a given layer will be filled first. Lower-priority zones will keep
clearance to the filled areas of higher-priority zones.
The main way to set zone priorities is by adjusting the relative ordering of zones in the Zone Manager
dialog. Zones that are higher in the list have higher priority than zones lower in the list. As a shortcut, you
can adjust a zone’s priority by right clicking it and choosing the appropriate action from the Zones → Zone
Priority submenu. You can also directly set a zone’s priority by changing the Priority value in properties
panel for the zone.

Drawing zones
To draw a zone, click the Add Filled Zone tool (

) on the right toolbar, or use default hotkey Ctrl + Shift +

Z . Click to choose the first point of the zone outline. The Zone Properties dialog will appear, allowing you

to choose the zone net and other properties. These properties may be edited at any time, so it is not critical
to choose them all correctly at first. Accept the dialog and continue placing points to define the zone outline.
To finish the zone, double-click to set the last point.
NOTE

You can configure default properties for new zones on the Defaults page of Board Setup.

To modify an existing zone outline, select it, then drag its editing handles to change the shape. Moving a
handle at the corner of a zone will move that corner, displaying the angle of that corner and the two
adjacent corners. Moving a handle on the edge of a zone will move that edge in a direction perpendicular to
the edge. Normally, dragging an edge maintains the angles of the corners adjacent to the edge while allowing
the edge’s length to vary. Holding

Ctrl

instead holds the edge’s length constant and allows the adjacent

corner angles to vary.
To precisely position a corner, right click the corner’s handle and choose Shape Modification → Move
Corner To…, then enter new X and Y coordinates for the corner. You can also edit the coordinates of every
outline corner by right clicking the zone and choosing Shape Modification → Edit Corners…. This opens a
floating dialog with a table containing the coordinates of every corner. Editing the coordinates of a corner
immediately updates the zone outline.

NOTE

You can also create zones by converting an existing graphic shape to a zone. This can be
useful, for example, for creating a zone with a shape that would otherwise be difficult to
draw with the zone tool, such as a circle. To convert a shape to a zone, right click the
shape, then select Create from Selection → Create Zone from Selection….

Several other tools for editing zones are available in the Zones submenu of the right click context menu.
You can also add keyboard shortcuts to these actions in Preferences.
You can merge two zones by selecting both zones, right clicking, and choosing Zones → Merge Zones.
When zones are merged, their outlines are combined into a single outline. The merged zone’s priority is

taken from the highest priority of the zones you started with. In order to be merged, the zones must
overlap, be on the same layers, and be assigned to the same net.
You can add a cutout to a zone by selecting the zone, right clicking, and choosing Zones → Add a Zone
Cutout. You can then draw the outline of the cutout. When the zone is filled, the cutout region will
remain unfilled.
To copy a zone an existing zone, you can right click a zone and choose Zones → Duplicate Zone onto
Layer…. This creates a copy of the existing zone and allows you to change the new zone’s properties,
including its layers.

NOTE

If you want to add a layer to an existing zone without changing any other properties, you
can also achieve this by editing the existing zone’s properties and enabling the desired
layer in addition to the existing layers.

You can draw a new zone with the same settings as an existing zone by right clicking a zone and choosing
Zones → Add a Similar Zone, then drawing the outline of the new zone. The new zone’s settings will be
taken from the original zone.

NOTE

Layers

In previous versions of KiCad, zone priority (the order in which multiple zones on a single
layer are filled) was determined by a number assigned to each zone in the Zone Properties
dialog. In KiCad 10 and later, zone priority is set by the relative ordering of zones in the
Zone Manager. You can also set an explicit priority value for each zone in the properties
panel.

A single zone object can create filled copper on one or more copper layers. Check the box next to each
copper layer that this zone outline should fill on. The copper on each layer will be filled independently,
but all layers will share the same net.
Zone name
You can optionally assign a specific name to a zone. This name can be used to refer to the zone in custom
DRC rules.
Net name
Select the electrical net that the zone copper should be connected to. It is possible to create zones with no
net assignment. Zones with no net will keep clearance from any copper objects on any net.
Locked
Controls whether or not the zone outline object is locked. Locked objects may not be manipulated or
moved, and cannot be selected unless the Locked Items option is enabled in the Selection Filter panel.
Corner smoothing
Controls the behavior of the filled copper areas at corners of the outline. Corners can be smoothed by a
chamfer or fillet, or can extend all the way to the outline corner if smoothing is disabled. The chamfer or
fillet size is configurable when those modes are selected.

NOTE

By default, chamfers and fillets are not added to inside corners of the zone outline,
because this would result in filled copper extending outside the outline. If smooth inside
corners are desired, enable the Allow fillets outside zone outline option in the
Constraints section of the Board Setup dialog.

Remove islands
Controls the behavior of isolated copper areas, also called islands, after the initial zone fill. When this is
set to always, isolated areas inside the zone are removed. When set to never, isolated areas are left
alone, and will result in copper areas that are not connected to the rest of the net. When set to below area
limit, a minimum island size can be specified, and islands below this threshold will be removed.

NOTE

Regardless of the remove islands setting, islands are never removed from zones that are
electrically unconnected. In other words, islands are only removed from zones that have
at least one electrical connection.

Open Zone Manager…
Clicking this button opens the Zone Manager dialog. The Zone Manager can be used to view and edit all
zones on the board, as well as configure zone priorities.

Clearances & pad connections
Clearance
Controls the minimum clearance the filled areas of this zone will keep from other copper objects. Note
that if two clearance values are in conflict, the larger clearance value will be used. For example, if a zone is
set to use 0.2mm clearance but its netclass is set to use 0.3mm clearance, the result will be an 0.3mm
clearance.

Minimum width
Controls the minimum size of narrow necks of copper created inside the zone. Any copper areas that
would be below this minimum width are removed during the filling process.
Pad connection
Controls the way that the filled zone areas will connect to footprint pads on the same net. Solid
connections will result in the copper completely overlapping the pads. Thermal reliefs will result in
small copper spokes connecting the pad to the rest of the copper zone, increasing the thermal resistance
between the pad and the rest of the zone. This can be useful for hand soldering. Reliefs for PTH will apply
thermal reliefs to plated through-hole pads and use solid connections for surface mount pads. None will
result in the zone not connecting to any pads on the same net.
Thermal relief gap
Controls the distance maintained between any pad and the copper zone when the pad connection mode is
set to generate thermal reliefs.
Thermal spoke width
Controls the width of the "spokes", or short copper segments connecting the pad to the rest of the copper
zone.

Display overrides
Outline display
Controls how the zone outline is drawn on screen. In Line mode, only the border lines of the outline are
drawn. In Hatched mode, hatch lines are drawn on the inside of the outline border for a short distance, to
make the zone outline more apparent. In Fully Hatched mode, hatch lines are drawn across the entire
inside of the zone outline.
Outline hatch pitch
Controls the spacing between hatch lines in the Hatched and Fully Hatched outline display modes.

Hatched fill
Hatched fill
When enabled, the zone is filled with a hatched pattern instead of solid copper. A hatched fill contains less
copper than a solid fill. This can be useful for flexibile printed circuits and other specialty applications.
Orientation
Controls the angle of the hatch pattern lines. An orientation of 0 degrees will result in the hatch pattern
using horizontal and vertical lines.
Hatch width
Controls the width of each line in the hatch pattern.
Hatch gap
Controls the distance between each line in the hatch pattern.
Smoothing effort

Controls the style of smoothing applied to the hatch pattern. A value of 0 will result in no smoothing, and
a value of 3 will result in the finest smoothing. Higher values will result in longer processing time and
larger Gerber files.
Smoothing amount
A ratio that controls the size of the smoothing chamfers or fillets that are generated when smoothing
effort is set to a value other than 0. An amount of 0.0 results in no smoothing, and a value of 1.0 results in
maximum smoothing (in other words, a chamfer or fillet equal to half of the hatch gap).
Hatch offset overrides
This table allows you to configure specific hatch pattern offsets for individual layers. X and Y offsets can
be configured separately. Per-layer hatch offsets can be used to force the hatching grid to be offset from
one layer to another, which is required in some applications.

NOTE

You can configure default hatch offsets for each layer in the Zone Hatch Offsets page of
Board Setup.

Zone manager
Instead of editing a single zone with the Zone Properties dialog, you can use the Zone Manager tool to you
view, edit, and prioritize all zones in the board at once. To run the Zone Manager, click Tools → Zone
Manager.

Zone list
The left side of the dialog shows a list of all zones in the board, displaying the name (if any), net, and layers
for each zone.

The order of the zones in the list reflects the priority of each zone: higher priority zones are higher in the
list. To change the priority of a zone, drag it to a new position in the list, or use the
move it up or down in the list. Use the

and

and

buttons to

buttons to move it to the very highest or lowest priority.

To automatically assign a priority to each zone, press the

button. This tool uses an algorithm to choose an

appropriate priority for each zone. For each pair of zones that overlap each other, the tool assigns a higher
priority to the zone with more connected pads or vias in the overlap region. If the two zones in the pair
have approximately the same number of connected items in the overlapping region, the smaller zone gets a
higher priority.
You can filter the list of zones by typing into the filter box. The filter matches against the zones' name and/or
net, depending on which filter options are enabled. You can also filter the list by zone layer using the Layer
dropdown menu.

Zone preview
Selecting a zone in the list shows a preview of that zone in the bottom right. The preview can be zoomed and
panned using the same controls as the PCB Editor canvas.
TIP

You can reset the preview to show the entire zone by right clicking the preview and
choosing Zoom to Fit.

If the selected zone spans multiple layers, each layer is shown individually. You can preview each layer by
clicking the appropriate layer tab above the preview.

Zone settings
The right side of the dialog shows the settings for the selected zone, which are explained above.
You can preview the new settings by clicking the Update Displayed Zones button, which updates the zone
preview without affecting the board. Changing the properties of a zone in the Zone Manager will not update
the board until you press OK.
If the Refill zones option is enabled, all zones will be refilled when you accept the dialog. If Refill zones is
not enabled, zones will not be refilled until you manually refill them.

---
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
