bretbouchard/kicad-agent/plans/routing-overhaul-phases-103-106.md

# Routing Overhaul: Placement-Aware Diagnosis, Negotiation, and Model Repoint

**Date:** 2026-07-01
**Status:** Council Review Pending
**Authors:** Bret Bouchard + ZCode
**Phases:** 103 (Foundation), 104 (Diagnosis), 105 (Negotiation), 106 (Placement-Advisor)
**Dependency chain:** 103 → 104 → 105 (sequential); 106 ∥ 105 (parallel, data from 104)
**Predecessors:** Phase 99 (Freerouting Integration Hardening), Phase 100 (RoutingOrchestrator), Phase 98 (AI Routing Strategy Advisor — to be repointed)

---

## 1. Problem Statement

Our routing stack is a **two-backend hybrid** (Freerouting Java router + in-house grid A*) with a strategy layer on top. It works, but it is **open-loop**: failures are recorded as booleans, not diagnosed. When routing fails on a dense board, we know *that* a net failed, not *why*, not *where*, and not *what to move\*. The verifier (`kicad-cli pcb drc`) runs post-hoc as a gate; its output never drives regeneration.

Three structural gaps block improvement:

1. **No failure signal.** `route_net` returns `None` on failure — the A\* search frontier (the true "dead end") is discarded at the `networkx.astar_path` boundary. The audit trail records `{net_name, dispatch_reason}` with no coordinates, no blocker identity, no violation type.
2. **No negotiation loop.** We have per-net rollback and retry-with-coarser-grid, but no PathFinder-style rip-up-and-reroute with escalating congestion cost. The verifier's rich DRC signal is wasted.
3. **The model is pointed at the wrong task.** `AiRoutingStrategy` asks Gemma 4 12B for per-net astar-vs-freerouting dispatch JSON — a low-value decision (a hand-coded rule makes it adequately) that the model was **never trained on** (training was maze-solving coordinate chains + spatial Q&A). The model's _actual_ trained capability — coordinate-grounded spatial reasoning, obstacle identification, "which fix is correct" counterfactuals — is exactly what placement-aware blocker diagnosis needs. It is wired to the wrong task.

**The core insight:** the model's trained capability is almost exactly what placement-aware blocker diagnosis needs. The current dispatch task is _both_ low-value _and_ out-of-distribution. The repoint is a move _toward_ the training distribution, not away from it.

---

## 2. Design Principle: Reverse-Perspective Blocker Diagnosis

The connective idea across all four phases: **when routing hits a dead end, look from the dead end's perspective. Find what blocks its path. That blocker is the thing to move.**

This is **negotiation-based rip-up-and-reroute** (foundational paper: [McMurchie & Ebeling, PathFinder 1995](https://dl.acm.org/doi/pdf/10.1145/201310.201328)), enhanced with **targeted diagnosis** (closer to [SATRoute](http://www.cse.cuhk.edu.hk/~byu/papers/J166-TCAD2026-SATRoute.pdf) and [RL-based rip-up selection](https://openreview.net/pdf?id=jjdngaZiwVb)). Plain PathFinder is blind — it globally penalizes congested nodes and hopes the router wanders elsewhere. This design is **targeted**: identify the exact blocker, classify it (trace / own-trace / movable-component / fixed-component / contested), and act on _that specific_ obstacle.

The diagnostic step is the leverage point. It powers all three downstream loops:

| Loop | Without diagnosis | With diagnosis |
| --- | --- | --- |
| Close orchestrator loop | "Failed net, retry coarser" (blind) | "Failed net → diagnose blocker → rip up _that_ → reroute" (targeted) |
| DRC as reward | Binary pass/fail (weak) | "Failed _because of clearance-to-net-M_ at point P" (rich, typed) |
| Learned policy | Learn to route from scratch (huge space) | Learn _which blocker to rip up first_ (small decision space) |

A binary "it failed" teaches nothing. A typed "it failed because component U3's courtyard blocks the corridor at (x,y)" is a _training signal_ and a _negotiation decision_ at the same time. Build the diagnostic once, feed it to all three.

---

## 3. Evidence Base (all claims codebase-verified)

Every architecture decision below is grounded in verified facts about the current codebase. Council reviewers can verify each against the cited file:line.

### 3.1 Router frontier recovery is feasible

- `RoutingGraph.graph` is a public read-only property exposing the underlying networkx Graph (`src/volta/routing/graph.py:336-339`).
- `route_net` (`pathfinder.py:63-118`) catches `nx.NetworkXNoPath` at line 109 and returns `None`, discarding the search frontier. The `src_node`/`tgt_node` are in scope (lines 92-96) before the try block.
- `nx.single_source_dijkstra_path_length(graph.graph, src_node)` recovers the reachable component (DRC-weighted) after the failure — same complexity class as the failed A\* (`O(V+E)`), bounded by `max_nodes = 500_000` (`constraints.py:65`, raises `ValueError` if exceeded at `graph.py:171-176`).
- networkx's `astar_path` does **not** expose its closed set (verified). Post-failure reachable-component query is the cleanest recovery method.
- Scale check: at 0.25mm grid on 100×100mm board, ~160k nodes/layer. BFS over source's component is at most the cost of the failed search. **Not prohibitively slow.**

### 3.2 The legacy handler is the canonical production path

- `_handle_auto_route` (`src/volta/ops/handlers/pcb.py:513`) is reached via CLI (`cli.py:441`), MCP server (`mcp/edit_server.py:730,1248`), and handler dispatch (`ops/executor.py:49,64` → `__init__.py:9,22`).
- `RoutingOrchestrator.route_board` (`orchestrator.py:157`) is **only** called from `scripts/phase98_eval.py:112` and `tests/test_phase100_*.py`. **Zero production wiring.**
- The orchestrator's `_dispatch_astar` (`orchestrator.py:349-412`) is a **feature subset**: `obstacles=[]` (empty), no power-net filtering, 2-pin only (no multi-pin Steiner), no retry loop. The legacy handler has all of these.

**Implication:** Foundation work must target the legacy handler to have production effect. Borrow the orchestrator's audit-trail patterns.
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
