bretbouchard/kicad-agent/plans/stage-safe-pcb-flow-upgrade.md

# Stage-Safe PCB Flow Upgrade

Date: 2026-06-11

## Purpose

This plan captures the recommended upgrades from the volta review so another agent can expand them into the existing GSD workflow, write detailed phase plans, and run review gates.

The core shift is from "file-safe KiCad editing" to "stage-safe PCB design." Every major design transition should have a deterministic gate:

- Schematic to PCB
- PCB setup to placement
- Placement to routing
- Routing to manufacturing

LLM output should propose intent and repairs. Deterministic tool gates should decide whether a design can move forward.

## Needed Areas
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
