bretbouchard/kicad-agent/.planning/phases/207-versioned-build-system/207-01-PLAN.md

---
phase: 207
plan: 01
title: "Versioned Build System — Build record, manifest serialization, build_create/list/show ops"
wave: 0
depends_on: []
autonomous: true
requirements:
  - BUILD-01
  - BUILD-02
  - BUILD-03
  - BUILD-04
  - BUILD-05
  - BUILD-06
  - BUILD-07
  - BUILD-08
  - BUILD-09
  - BUILD-10
files_modified:
  - src/volta/validation/gates/manufacturing_manifest.py
  - src/volta/manufacturing/build.py
  - src/volta/ops/_schema_pcb.py
  - src/volta/ops/schema.py
  - src/volta/ops/registry.py
  - src/volta/ops/handlers/build.py
  - src/volta/ops/handlers/__init__.py
  - tests/test_build_system.py
  - tests/test_registry.py
  - .gitignore
---

# Phase 207 Plan 01 — Versioned Build System

<phase_goal>
User can create a versioned build that snapshots source files, records git SHA + board revision, and serializes a manifest with SHA256-hashed artifacts to disk. One plan, five tasks, ten BUILD requirements.
</phase_goal>

<phase_context>
Phase 205 shipped `NativeTitleBlock.rev` (frozen dataclass at `pcb_native_types.py:344`). Phase 206 shipped `drc_vendor`/`list_vendor_drc_profiles` as query ops. Phase 207 builds the `Build` record model, promotes `ManufacturingManifest` with serialization, and adds three query ops (`build_create`, `build_list`, `build_show`) that create side-effect artifacts in `builds/` without touching the `.kicad_pcb` source.

**Key design decisions (from 207-CONTEXT.md + 207-RESEARCH.md):**
1. All three ops are `category: "query"`, `is_readonly: True` — NOT CROSS_FILE_OP_TYPES (IP-4 deviation, CONTEXT.md:87-89). The handler creates `builds/` artifacts; `execute_query` never serializes the target `.kicad_pcb`.
2. Registry count 156 → 159 (+3 ops). `test_readonly_operations_count` asserts an exact frozenset — must add all 3 ops.
3. Handler must re-parse via `NativeParser.parse_pcb(file_path)` for `board_rev` (dual-path issue: query path has `_native_board = None`, same as Phase 205/206).
4. `ManufacturingManifest`/`ManufacturingArtifact` are frozen dataclasses — add explicit `to_json/save/load` (manifest) and `to_dict/from_dict` (artifact). `dataclasses.asdict` is one-way; load must reconstruct tuples explicitly.
5. `build_show` accepts optional `diff_build_id` for diffing — NOT a separate op (keeps registry at +3, not +4). Diff logic lives in `diff_builds()` utility.
6. Manifest serialization uses `atomic_write` (same as Phase 205 `save_board_spec`).
7. Validation is simplified for v1: `build_create` default produces `BuildStatus.DRAFT` (PCB parses check). Full `ManufacturingReadinessGate` requires context (DRC/DFM/exports) that Phase 208's handoff orchestrator provides. DRAFT status is honest (avoids Pitfall 5 false confidence).
8. Single-file on disk: `manifest.json` carries the full Build envelope (build_id, git_sha, status, source_files, build_dir + manifest fields). Success criterion #3 requires "reloading reproduces the build record exactly."
</phase_context>

<must_haves>
1. `Build` frozen dataclass in `manufacturing/build.py` with all BUILD-02 fields (build_id, board_rev, source_files, git_sha, created_at, status, artifacts, manifest_path, build_dir)
2. `BuildStatus` enum: DRAFT, VALIDATED, EXPORTED, HANDED_OFF with `transition_to` via `dataclasses.replace` (BUILD-03)
3. `ManufacturingManifest.to_json/save/load` + `ManufacturingArtifact.to_dict/from_dict` round-trip lossless (BUILD-05)
4. `build_create` op creates `builds/v{rev}_{timestamp}/` with manifest + source snapshots (BUILD-01, BUILD-06)
5. `build_create` returns error + NO build dir if PCB fails to parse (BUILD-04: no partial state)
6. `build_list` op returns all builds for a project (BUILD-07)
7. `build_show` op returns build details by build_id (BUILD-08)
8. `diff_builds()` utility comparing two Build records (BUILD-10)
9. `builds/` added to `.gitignore` (BUILD-09)
10. Registry count assertion updated 156 → 159; readonly set updated +3 ops (IP-1, IP-2)
11. Target `.kicad_pcb` byte-identical after `build_create` (defends `is_readonly: True` contract)
</must_haves>

<threat_model>
**Attack surface for Phase 207:**

1. **Build directory creation (path traversal via project_dir):** `build_create` resolves `project_dir` from `op.project_dir` (user-controlled string) and creates `builds/v{rev}_{timestamp}/` under it. If `project_dir` contains `../` sequences, an attacker could write the build dir outside the intended project root.
   - **Mitigation:** Reject `project_dir` values containing `..` path segments. The schema field `project_dir` should validate that the resolved path stays within a reasonable bound (or at minimum reject obvious traversal). The handler should use `Path.resolve()` and verify the resulting `build_dir` is within the resolved `project_dir`. Board rev used in directory name comes from `title_block.rev` (also user-controlled via the PCB file) — sanitize it to `[A-Za-z0-9._-]` only before interpolating into the path.

2. **Git SHA capture (subprocess injection via project_dir):** `subprocess.run(["git", "rev-parse", "HEAD"], cwd=str(project_dir))` passes `project_dir` as `cwd`. Since the command is a fixed argument list (NOT a shell string), shell injection is not possible. However, a malicious `project_dir` pointing to an attacker-controlled directory runs `git` in their context.
   - **Mitigation:** Use the same `project_dir` validation as build dir creation. The argument-list form (no `shell=True`) prevents command injection. Wrap in `try/except (subprocess.SubprocessError, OSError)` returning `"unknown"` — never raises.

3. **Manifest JSON serialization (injection via board name/project name):** `ManufacturingManifest` fields (`project_name`, `board_name`) come from the PCB file or project. These flow into `manifest.json` via `json.dumps`. Since `json.dumps` escapes all special characters, JSON injection is not possible. However, if these values are later rendered into a readme (Phase 208), they need HTML escaping then — NOT a Phase 207 concern.
   - **Mitigation:** `json.dumps` handles serialization safely. No additional escaping needed for Phase 207. Board rev used in directory names is sanitized (see #1).

4. **Source file snapshot (copying files outside project dir):** `shutil.copy2` copies `.kicad_pcb`, `.kicad_sch`, `.kicad_pro` with the same stem as the target file. Discovery is stem-based within `project_dir` — it cannot copy arbitrary files outside the project because the candidates are constructed as `project_dir / f"{stem}{ext}"`.
   - **Mitigation:** The stem-based discovery is inherently bounded. Validate that resolved candidate paths are within `project_dir` (defense in depth). Never follow symlinks out of the project dir.
</threat_model>

---

## Task 1: Build model + manifest serialization

**Req:** BUILD-02, BUILD-03, BUILD-05
**Wave:** 0

<read_first>
- `src/volta/validation/gates/manufacturing_manifest.py` (full file — `ManufacturingArtifact` line 19, `ManufacturingManifest` line 45, `from_file` line 30, `generate_manifest` line 60)
- `src/volta/training/manifest.py` lines 27-124 (`DataManifest` frozen dataclass with `save`/`load` round-trip + `replace` for transitions — the strongest analog)
- `src/volta/manufacturing/board_spec.py` lines 17-24, 75-83 (`SurfaceFinish(str, Enum)` pattern + `atomic_write` usage in `save_board_spec`)
- `src/volta/io/atomic_write.py` (full file — `atomic_write(file_path, content)` signature)
- `src/volta/parser/pcb_native_types.py` lines 344-356 (`NativeTitleBlock.rev` field)
- `.planning/phases/207-versioned-build-system/207-PATTERNS.md` FILE 1 + FILE 4 sections
</read_first>

<action>
**MODIFY `src/volta/validation/gates/manufacturing_manifest.py`** — add serialization to existing frozen dataclasses (no change to existing fields, constructors, `from_file`, `generate_manifest`, `validate_manifest`):

1. Add `import json` at top (after existing `import hashlib`).
2. Add `from volta.io.atomic_write import atomic_write` import.
3. Add to `ManufacturingArtifact`:
   - `to_dict(self) -> dict` — explicit field mapping (name, path, sha256, size_bytes, generated_by, timestamp). Do NOT use `dataclasses.asdict` (RESEARCH RQ1: one-way transform).
   - `@staticmethod from_dict(d: dict) -> ManufacturingArtifact` — reconstruct via `ManufacturingArtifact(**{...})` with explicit field extraction.
4. Add to `ManufacturingManifest`:
   - `to_json(self) -> str` — `json.dumps` with `indent=2`, converting `artifacts` tuple → list of dicts via `to_dict()`. JSON structure matches CONTEXT.md lines 64-75 (project_name, board_name, fab_profile, artifacts, bom_rows, total_components, generated_at).
   - `save(self, path: Path) -> None` — `path.parent.mkdir(parents=True, exist_ok=True)` then `atomic_write(path, self.to_json())`. Mirrors `board_spec.save_board_spec`.
   - `@classmethod load(cls, path: Path) -> ManufacturingManifest` — `json.loads(path.read_text(encoding="utf-8"))` then reconstruct: `artifacts = tuple(ManufacturingArtifact.from_dict(a) for a in data.get("artifacts", []))`, then `cls(project_name=..., board_name=..., fab_profile=..., artifacts=artifacts, bom_rows=data.get("bom_rows", 0), total_components=data.get("total_components", 0), generated_at=data.get("generated_at", ""))`.

**CREATE `src/volta/manufacturing/build.py`** — core build data model:

1. `BuildStatus(str, Enum)` with values: `DRAFT = "draft"`, `VALIDATED = "validated"`, `EXPORTED = "exported"`, `HANDED_OFF = "handed_off"` (mirrors `SurfaceFinish` pattern in `board_spec.py:17`).
2. `@dataclass(frozen=True) class Build` with fields (CONTEXT.md:41-53):
   - `build_id: str` (UUID4 string)
   - `board_rev: str`
   - `source_files: tuple[str, ...]` (relative paths)
   - `git_sha: str`
   - `created_at: str` (ISO 8601)
   - `status: BuildStatus`
   - `artifacts: tuple[ManufacturingArtifact, ...]`
   - `manifest_path: str` (relative path)
   - `build_dir: str` (relative path)
3. `Build.transition_to(self, new_status: BuildStatus) -> Build` — validate allowed transitions (DRAFT→VALIDATED→EXPORTED→HANDED_OFF, forward only) and return `dataclasses.replace(self, status=new_status)`. Raise `ValueError` on disallowed transitions.
4. `_ALLOWED_TRANSITIONS: dict[BuildStatus, frozenset[BuildStatus]]` mapping each status to its valid successors.
5. `Build.to_dict(self) -> dict` — serialize all fields including `status.value`, `[a.to_dict() for a in self.artifacts]`.
6. `Build.save(self, path: Path) -> None` — `atomic_write(path, json.dumps(self.to_dict(), indent=2))`.
7. `@classmethod Build.load(cls, path: Path) -> Build` — reconstruct from JSON, converting `status` string back to `BuildStatus`, artifacts list back to tuple via `ManufacturingArtifact.from_dict`.
8. `def _get_git_sha(project_dir: Path) -> str` — `subprocess.run(["git", "rev-parse", "HEAD"], cwd=str(project_dir), capture_output=True, text=True, timeout=10)`. Return `result.stdout.strip()` on `returncode == 0` and non-empty stdout. Catch `(subprocess.SubprocessError, FileNotFoundError, OSError)` and return `"unknown"`. Never raises (RESEARCH RQ5).
9. `@dataclass(frozen=True) class BuildDiff` with fields: `source_files_added: tuple[str, ...]`, `source_files_removed: tuple[str, ...]`, `artifacts_added: tuple[str, ...]`, `artifacts_removed: tuple[str, ...]`, `status_changed: bool`, `git_sha_changed: bool`, `board_rev_changed: bool`.
10. `def diff_builds(a: Build, b: Build) -> BuildDiff` — set arithmetic on `source_files` and `artifact.name` sets. Return tuples sorted for determinism (RESEARCH RQ8).

**CREATE `tests/test_build_system.py`** — first test class `TestBuildModel` covering:
- `test_build_status_transition_allowed` — `DRAFT → VALIDATED` returns new frozen Build with status=VALIDATED.
- `test_build_status_transition_disallowed` — `HANDED_OFF → DRAFT` raises ValueError.
- `test_git_sha_unknown_when_not_a_repo` — `_get_git_sha(tmp_path)` returns `"unknown"`, never raises.
- `test_git_sha_from_repo` — guarded by `pytest.mark.skipif(not shutil.which("git"))`; `git init` in tmp_path, commit, assert SHA prefix matches.
- `test_manifest_to_json_round_trip` — construct `ManufacturingManifest` with 2 artifacts, `save(tmp_path/"m.json")`, `ManufacturingManifest.load(...)`, assert `==` original.
- `test_artifact_to_from_dict` — `ManufacturingArtifact.from_dict(a.to_dict()) == a`.
- `test_manifest_load_missing_file_raises` — `load(nonexistent)` raises `FileNotFoundError`.
- `test_build_to_dict_round_trip` — `Build.save` then `Build.load` produces equal Build (status enum survives round-trip).
- `test_diff_builds_detects_changes` — two Builds differing in source_files, artifacts, status, git_sha, board_rev → correct `BuildDiff` flags.
- `test_diff_builds_identical` — same Build → all empty tuples, all `*_changed=False`.
</action>

<acceptance_criteria>
- `grep -n "def to_json" src/volta/validation/gates/manufacturing_manifest.py` returns a match
- `grep -n "def save" src/volta/validation/gates/manufacturing_manifest.py` returns a match
- `grep -n "def load" src/volta/validation/gates/manufacturing_manifest.py` returns a match
- `grep -n "def to_dict\|def from_dict" src/volta/validation/gates/manufacturing_manifest.py` returns matches for both methods on ManufacturingArtifact
- `grep -n "class BuildStatus" src/volta/manufacturing/build.py` returns a match
- `grep -n "class Build" src/volta/manufacturing/build.py` returns a match
- `grep -n "def transition_to" src/volta/manufacturing/build.py` returns a match
- `grep -n "def _get_git_sha" src/volta/manufacturing/build.py` returns a match
- `grep -n "class BuildDiff" src/volta/manufacturing/build.py` returns a match
- `grep -n "def diff_builds" src/volta/manufacturing/build.py` returns a match
- `.venv/bin/python -m pytest tests/test_build_system.py::TestBuildModel -x -q -o addopts="" -o pythonpath="src tests"` passes (0 failures)
- `.venv/bin/python -m pytest tests/test_manufacturing_gate.py -x -q -o addopts="" -o pythonpath="src tests"` passes (no regressions from manifest changes)
</acceptance_criteria>

---

## Task 2: Schema + registry + handler wiring (3 new query ops)

**Req:** BUILD-01, BUILD-06 (partial — schema/registry plumbing for all 3 ops)
**Wave:** 0
**Depends on:** Task 1

<read_first>
- `src/volta/ops/_schema_pcb.py` lines 1269-1280 (`ListVendorDrcProfilesOp` — minimal readonly op pattern with `op_type` Literal + `target_file: TargetFile`)
- `src/volta/ops/_schema_pcb.py` lines 1238-1266 (`DrcVendorOp` — readonly op with extra fields + pattern validation)
- `src/volta/ops/schema.py` lines 275-285 (import block ending), 555-568 (union ending with `ListVendorDrcProfilesOp,`), 770-785 (`__all__` ending)
- `src/volta/ops/registry.py` lines 1442-1462 (Phase 206 entries + `_RAW_CATALOG` closing `}` + `OPERATION_REGISTRY` dict comprehension)
- `src/volta/ops/handlers/__init__.py` (full file — merge pattern: `_FILL_ZONES_HANDLERS` import + `_PCB_HANDLERS.update(...)`)
- `src/volta/ops/handlers/pcb_fill_zones.py` lines 27-35 (`_FILL_ZONES_HANDLERS` dict + `register_fill_zones` decorator — the analog for `_BUILD_HANDLERS`)
- `.planning/phases/207-versioned-build-system/207-PATTERNS.md` FILE 5, FILE 6, FILE 7, FILE 8 sections
</read_first>

<action>
**MODIFY `src/volta/ops/_schema_pcb.py`** — add 3 Op classes after `ListVendorDrcProfilesOp` (line 1280) under a `# Phase 207: Build system ops` comment:

```python
class BuildCreateOp(BaseModel):
    op_type: Literal["build_create"] = "build_create"
    target_file: TargetFile
    project_dir: Optional[str] = Field(default=None, description="Project root (defaults to target_file parent)")
    skip_validation: bool = Field(default=False, description="Skip validation (for testing / quick drafts)")

class BuildListOp(BaseModel):
    op_type: Literal["build_list"] = "build_list"
    target_file: TargetFile
    project_dir: Optional[str] = Field(default=None)

class BuildShowOp(BaseModel):
    op_type: Literal["build_show"] = "build_show"
    target_file: TargetFile
    build_id: str = Field(min_length=1, max_length=64, pattern=r"^[A-Za-z0-9-]+$", description="UUID of the build to show")
    diff_build_id: Optional[str] = Field(default=None, min_length=1, max_length=64, pattern=r"^[A-Za-z0-9-]+$", description="Optional second build_id to diff against")
    project_dir: Optional[str] = Field(default=None)
```

**MODIFY `src/volta/ops/schema.py`** — 3 edits (FILES 5+6+7 must land together per PATTERNS integration order):
1. Import block (after line 284 `ListVendorDrcProfilesOp,`): add `BuildCreateOp,`, `BuildListOp,`, `BuildShowOp,` before the closing `)`.
2. Union (line 566): change `| ListVendorDrcProfilesOp,` to `| ListVendorDrcProfilesOp | BuildCreateOp | BuildListOp | BuildShowOp,` (trailing comma on last item, then `Field(discriminator="op_type"),`).
3. `__all__` (after line 781 `"ListVendorDrcProfilesOp",`): add `# Phase 207 build system ops`, `"BuildCreateOp"`, `"BuildListOp"`, `"BuildShowOp"`.

**MODIFY `src/volta/ops/registry.py`** — add 3 entries to `_RAW_CATALOG` before the closing `}` (after `list_vendor_drc_profiles` at line 1461). Each entry: `category: "query"`, `description`, `file_types: [".kicad_pcb"]`, `is_readonly: True`, `scope: "single_file"`, `requires: []`, `conflicts: []` (exact pattern of `drc_vendor` at registry.py:1444).

**CREATE `src/volta/ops/handlers/build.py`** — the handler module (handlers implemented in Task 3; this task creates the module skeleton + `_BUILD_HANDLERS` dict + `register_build` decorator so Task 8 merge works):
```python
_BUILD_HANDLERS: dict[str, Callable] = {}

def register_build(op_type: str) -> Callable:
    def decorator(fn: Callable) -> Callable:
        _BUILD_HANDLERS[op_type] = fn
        return fn
    return decorator
```
Then add the three handler stubs (full implementations in Task 3, but stubs must exist so import doesn't fail):
- `@register_build("build_create")` def `_handle_build_create(op, ir, file_path) -> dict`
- `@register_build("build_list")` def `_handle_build_list(op, ir, file_path) -> dict`
- `@register_build("build_show")` def `_handle_build_show(op, ir, file_path) -> dict`

**MODIFY `src/volta/ops/handlers/__init__.py`** — 3 edits (mirroring `_FILL_ZONES_HANDLERS` merge pattern):
1. Import (after line 18 `from .query import ...`): `from .build import _BUILD_HANDLERS, register_build`.
2. Merge (after line 31 `_PCB_HANDLERS.update(_STITCH_HANDLERS)`): `_QUERY_HANDLERS.update(_BUILD_HANDLERS)  # Phase 207 build handlers are query handlers`.
3. `__all__` (after `register_query` entry ~line 57): add `"_BUILD_HANDLERS"`, `"register_build"`.

**MODIFY `tests/test_registry.py`** — 2 edits:
1. Line 26 count: change `== 156` to `== 159`, update comment to `# Phase 207: 159 ops (was 156 after Phase 206; +3: build_create, build_list, build_show).`
2. `expected_readonly` set (lines 114-155): add `"build_create"`, `"build_list"`, `"build_show"` alphabetically (after `analyze_*` entries, before `classify_violations`).

Verify `validate_registry_completeness` passes — the 3 new ops must appear in BOTH schema union AND `_RAW_CATALOG` so they don't land in `missing_from_registry` or `extra_in_registry`.
</action>

<acceptance_criteria>
- `grep -n "class BuildCreateOp" src/volta/ops/_schema_pcb.py` returns a match
- `grep -n "class BuildListOp" src/volta/ops/_schema_pcb.py` returns a match
- `grep -n "class BuildShowOp" src/volta/ops/_schema_pcb.py` returns a match
- `grep -n "BuildCreateOp" src/volta/ops/schema.py` returns at least 3 matches (import, union, __all__)
- `grep -n '"build_create"' src/volta/ops/registry.py` returns a match
- `grep -n '"build_list"' src/volta/ops/registry.py` returns a match
- `grep -n '"build_show"' src/volta/ops/registry.py` returns a match
- `grep -n "_BUILD_HANDLERS" src/volta/ops/handlers/__init__.py` returns at least 2 matches (import + merge)
- `grep -n "_QUERY_HANDLERS.update(_BUILD_HANDLERS)" src/volta/ops/handlers/__init__.py` returns a match
- `grep -c "build_create\|build_list\|build_show" tests/test_registry.py` returns at least 3 (count assertion + readonly set)
- `.venv/bin/python -m pytest tests/test_registry.py -x -q -o addopts="" -o pythonpath="src tests"` passes with count==159 and readonly set updated
- `.venv/bin/python -c "from volta.ops.handlers import _QUERY_HANDLERS; assert 'build_create' in _QUERY_HANDLERS and 'build_list' in _QUERY_HANDLERS and 'build_show' in _QUERY_HANDLERS"` exits 0
</acceptance_criteria>

---

## Task 3: build_create handler implementation

**Req:** BUILD-01, BUILD-04, BUILD-06
**Wave:** 0
**Depends on:** Task 1, Task 2

<read_first>
- `src/volta/ops/handlers/query.py` lines 88-127 (`drc_vendor` handler — re-parses via `NativeParser.parse_pcb(file_path)`, the structural analog for `build_create`)
- `src/volta/ops/handlers/query.py` lines 17-29 (`register_query` decorator + handler signature `(op, ir, file_path) -> dict`)
- `src/volta/validation/gates/manufacturing_manifest.py` lines 30-42 (`ManufacturingArtifact.from_file` — hashes + sizes + timestamps)
- `src/volta/parser/pcb_native_parser.py` lines 259-289 (`NativeParser.parse_pcb` classmethod returning NativeBoard)
- `src/volta/ops/execution.py` lines 193-230 (`execute_query` — confirms query path does NOT write target file after handler returns; target must exist)
- `src/volta/ops/handlers/build.py` (the skeleton created in Task 2)
- `src/volta/manufacturing/build.py` (the model created in Task 1)
- `tests/test_board_metadata_ops.py` lines 12-63 (autouse `_clear_ir_registry` fixture + `_build_ir` helper + inline PCB fixture — the handler test pattern)
- `.planning/phases/207-versioned-build-system/207-PATTERNS.md` FILE 2 section (handler steps), FILE 3 section (test patterns)
</read_first>

<action>
**MODIFY `src/volta/ops/handlers/build.py`** — implement `_handle_build_create` (replace the stub from Task 2):

Use `@register_build("build_create")`. Lazy imports inside the handler body (avoids import cycles). Steps (all per CONTEXT.md:91-101 + PATTERNS FILE 2):

1. **Resolve project_dir:** `project_dir = Path(op.project_dir) if op.project_dir else Path(file_path).parent`. Validate no `..` segments in `op.project_dir` (threat model #1): `if op.project_dir and ".." in Path(op.project_dir).parts: return {"success": False, "error": "Invalid project_dir: path traversal forbidden"}`.

2. **Read board_rev (re-parse for dual-path safety):** `from volta.parser.pcb_native_parser import NativeParser`; `board = NativeParser.parse_pcb(file_path)`; `board_rev = board.title_block.rev if board.title_block and board.title_block.rev else "unknown"`. This is REQUIRED — the query-path `ir` has `_native_board = None` (CRITICAL CONTEXT #4, same as `drc_vendor`).

3. **Sanitize board_rev for directory name:** `safe_rev = re.sub(r"[^A-Za-z0-9._-]", "_", board_rev)[:64]` (threat model #1 — rev comes from PCB file, user-controlled).

4. **Capture git SHA:** `from volta.manufacturing.build import _get_git_sha`; `git_sha = _get_git_sha(project_dir)`.

5. **Generate build_id + timestamps:** `import uuid`; `build_id = str(uuid.uuid4())`; `from datetime import datetime, timezone`; `now = datetime.now(timezone.utc)`; `created_at = now.isoformat()`; `dir_timestamp = now.strftime("%Y%m%d_%H%M%S")`.

6. **Create build dir:** `build_dir_name = f"v{safe_rev}_{dir_timestamp}"`; `builds_root = project_dir / "builds"`; `build_dir = builds_root / build_dir_name`; `builds_root.mkdir(parents=True, exist_ok=True)`; `build_dir.mkdir(parents=True, exist_ok=False)`. If `FileExistsError` (sub-second collision), append short UUID: `build_dir = builds_root / f"{build_dir_name}_{build_id[:8]}"`; `build_dir.mkdir(parents=True, exist_ok=False)`.

7. **Validation (simplified v1):** The PCB parse in step 2 already validates the board parses. If `skip_validation` is False and the parse raised, return error + rmtree the partial build dir (BUILD-04: no partial state). Wrap steps 2-6 so ANY failure triggers `shutil.rmtree(build_dir, ignore_errors=True)` in the except block BEFORE returning the error dict. Status defaults to `BuildStatus.DRAFT` (CRITICAL CONTEXT #6 — full ManufacturingReadinessGate deferred to Phase 208).

8. **Snapshot source files:** Discover `.kicad_pcb`, `.kicad_sch`, `.kicad_pro` with same stem as `file_path` in `project_dir`:
   ```python
   stem = Path(file_path).stem
   source_files = []
   for ext in (".kicad_pcb", ".kicad_sch", ".kicad_pro"):
       candidate = project_dir / f"{stem}{ext}"
       if candidate.exists() and candidate.resolve().is_relative_to(project_dir.resolve()):
           rel = str(candidate.relative_to(project_dir))
           dest = build_dir / candidate.name
           shutil.copy2(candidate, dest)  # copy2 preserves metadata (RESEARCH RQ7)
           source_files.append(rel)
   ```
   Each copy becomes a `ManufacturingArtifact` via `ManufacturingArtifact.from_file(name=candidate.name, path=str(dest), generated_by="snapshot")`.

9. **Create manifest:** `from volta.validation.gates.manufacturing_manifest import ManufacturingManifest, ManufacturingArtifact`; construct `manifest = ManufacturingManifest(project_name=stem, board_name=stem, fab_profile="unknown", artifacts=tuple(artifacts), bom_rows=0, total_components=0, generated_at=created_at)`.

10. **Create Build record:** `from volta.manufacturing.build import Build, BuildStatus`; `build = Build(build_id=build_id, board_rev=board_rev, source_files=tuple(source_files), git_sha=git_sha, created_at=created_at, status=BuildStatus.DRAFT, artifacts=tuple(artifacts), manifest_path=str(build_dir / "manifest.json"), build_dir=str(build_dir))`.

11. **Serialize:** `build.save(build_dir / "build.json")` AND `manifest.save(build_dir / "manifest.json")`. Store both — `manifest.json` is the manufacturing manifest (BUILD-05), `build.json` is the full Build envelope (build_id, git_sha, status — needed for `build_show` round-trip per success criterion #3).

12. **Return:** `{"success": True, "build_id": build_id, "board_rev": board_rev, "git_sha": git_sha, "status": BuildStatus.DRAFT.value, "build_dir": str(build_dir.relative_to(project_dir)), "manifest_path": "manifest.json", "source_files": source_files, "artifacts": [a.to_dict() for a in artifacts]}`.

**ADD tests to `tests/test_build_system.py`** — class `TestBuildCreate`:
- `test_build_create_creates_directory` — `skip_validation=True`, assert `builds/v*_*/` exists with `manifest.json` + `build.json` + snapshot copy of `.kicad_pcb`. Use the `_create_pcb_with_title_block` + `_build_ir` helper pattern from `test_board_metadata_ops.py`.
- `test_build_create_reads_board_rev` — PCB with `rev "2.3"` → `result["board_rev"] == "2.3"`.
- `test_build_create_records_git_sha` — assert `result["git_sha"]` is a string (either a SHA or `"unknown"`).
- `test_build_create_skip_validation_creates_draft` — `skip_validation=True` → `result["status"] == "draft"`.
- `test_build_create_snapshots_source_files` — assert `.kicad_pcb` copied; re-hash the copy and compare to artifact `sha256`.
- `test_build_create_no_partial_state_on_parse_failure` — pass a malformed PCB path (or corrupt content that NativeParser rejects); assert `result["success"] == False` AND no `builds/` directory created. (If parse can't be easily forced to fail, test the error path by pointing target at a non-PCB file.)
- `test_build_create_target_file_unchanged` — hash the `.kicad_pcb` before and after `build_create`; assert byte-identical + check mtime unchanged (defends `is_readonly: True` contract per RESEARCH RQ3 caveat).
- `test_build_create_rejects_path_traversal` — `project_dir="../../../etc"` → `result["success"] == False` with traversal error.
- `test_build_create_generates_uuid` — assert `result["build_id"]` matches UUID4 format (36 chars with hyphens).
</action>

<acceptance_criteria>
- `grep -n "def _handle_build_create" src/volta/ops/handlers/build.py` returns a match
- `grep -n "NativeParser.parse_pcb" src/volta/ops/handlers/build.py` returns a match (board_rev re-parse)
- `grep -n "shutil.copy2" src/volta/ops/handlers/build.py` returns a match (source snapshot)
- `grep -n "_get_git_sha" src/volta/ops/handlers/build.py` returns a match
- `grep -n "BuildStatus.DRAFT" src/volta/ops/handlers/build.py` returns a match
- `grep -n 'path traversal' src/volta/ops/handlers/build.py` returns a match (threat model mitigation present)
- `.venv/bin/python -m pytest tests/test_build_system.py::TestBuildCreate -x -q -o addopts="" -o pythonpath="src tests"` passes (0 failures)
- `.venv/bin/python -c "from volta.ops.handlers import _QUERY_HANDLERS; h=_QUERY_HANDLERS['build_create']; print('ok')"` exits 0
</acceptance_criteria>

---

## Task 4: build_list + build_show handlers + diff integration

**Req:** BUILD-07, BUILD-08, BUILD-10
**Wave:** 0
**Depends on:** Task 3

<read_first>
- `src/volta/ops/handlers/build.py` (the `build_create` handler from Task 3 — reuse project_dir resolution + Build.load)
- `src/volta/manufacturing/build.py` (Task 1 — `Build.load`, `diff_builds`, `BuildDiff`)
- `src/volta/validation/gates/manufacturing_manifest.py` (Task 1 — `ManufacturingManifest.load`)
- `.planning/phases/207-versioned-build-system/207-PATTERNS.md` FILE 2 `build_list`/`build_show` sections
- `.planning/phases/207-versioned-build-system/207-RESEARCH.md` RQ8 (Build Diffing)
</read_first>

<action>
**MODIFY `src/volta/ops/handlers/build.py`** — implement `_handle_build_list` and `_handle_build_show` (replace stubs from Task 2):

**`@register_build("build_list")` `_handle_build_list(op, ir, file_path)`:**
1. Resolve `project_dir` (same as build_create, including `..` traversal check).
2. `builds_root = project_dir / "builds"`. If `not builds_root.is_dir()`: return `{"builds": [], "count": 0}`.
3. Scan `builds_root.glob("v*_*")` for subdirectories. For each subdir where `(subdir / "build.json").is_file()`:
   - Load via `Build.load(subdir / "build.json")`. Wrap in try/except — skip corrupt dirs with a warning (never crash the whole list on one bad dir, per PATTERNS FILE 2).
   - Collect build summary dict: `{"build_id", "board_rev", "git_sha", "created_at", "status": build.status.value, "build_dir": str(subdir.relative_to(project_dir))}`.
4. Sort builds by `created_at` descending (most recent first).
5. Return `{"builds": [...], "count": len(builds)}`.

**`@register_build("build_show")` `_handle_build_show(op, ir, file_path)`:**
1. Resolve `project_dir` (same traversal check).
2. Scan `builds_root.glob("v*_*")` for the build whose `build_id` matches `op.build_id`. Load each `build.json` until match found. If none: return `{"success": False, "error": f"build not found: {op.build_id}"}`.
3. Load the primary build's manifest via `ManufacturingManifest.load(build_dir / "manifest.json")` (wrap in try/except — if manifest missing/corrupt, still return build details with `manifest: None`).
4. Build response dict: `{"success": True, "build_id", "board_rev", "git_sha", "created_at", "status": build.status.value, "source_files": list(build.source_files), "build_dir": ..., "manifest": manifest.to_dict() if manifest else None, "artifacts": [a.to_dict() for a in build.artifacts]}`.
5. **Diff integration (BUILD-10):** If `op.diff_build_id` is set, find the second build by that id (same scan). Load it. Call `diff_builds(build_a, build_b)` and include `"diff": diff.__dict__` (or `dataclasses.asdict(diff)`) in the response. If diff_build_id not found: include `"diff_error": "build not found: {diff_build_id}"` but still return the primary build details.

**ADD tests to `tests/test_build_system.py`** — classes `TestBuildList` and `TestBuildShow`:
- `test_build_list_returns_builds` — create 2 builds via `build_create`, list → `count == 2`, both build_ids present.
- `test_build_list_empty_when_no_builds` — no `builds/` dir → `count == 0`, `builds == []`.
- `test_build_list_skips_corrupt_dir` — create a valid build + a dir with corrupt `build.json`; list → count==1 (corrupt skipped, no crash).
- `test_build_show_returns_details` — create a build, show by build_id → `success == True`, `status == "draft"`, artifacts present.
- `test_build_show_not_found` — unknown build_id → `success == False`, error mentions the id.
- `test_build_show_round_trip_manifest` — create then show → `manifest` is not None, `manifest["artifacts"]` length matches source file count.
- `test_build_show_with_diff` — create 2 builds (second with different board_rev if possible, or different git_sha), show build_1 with `diff_build_id=build_2` → response includes `diff` with correct change flags.
- `test_build_show_diff_not_found` — show with `diff_build_id` pointing to unknown id → primary build returned + `diff_error` present.
- `test_diff_builds_unit` — (already in Task 1, but verify here end-to-end via the handler).
</action>

<acceptance_criteria>
- `grep -n "def _handle_build_list" src/volta/ops/handlers/build.py` returns a match
- `grep -n "def _handle_build_show" src/volta/ops/handlers/build.py` returns a match
- `grep -n "glob" src/volta/ops/handlers/build.py` returns at least 2 matches (list + show scanning)
- `grep -n "diff_build_id" src/volta/ops/handlers/build.py` returns a match (BUILD-10 integration)
- `grep -n "diff_builds" src/volta/ops/handlers/build.py` returns a match
- `.venv/bin/python -m pytest tests/test_build_system.py::TestBuildList tests/test_build_system.py::TestBuildShow -x -q -o addopts="" -o pythonpath="src tests"` passes (0 failures)
- `.venv/bin/python -c "from volta.ops.handlers import _QUERY_HANDLERS; assert 'build_list' in _QUERY_HANDLERS and 'build_show' in _QUERY_HANDLERS"` exits 0
</acceptance_criteria>

---

## Task 5: .gitignore + full verification

**Req:** BUILD-09, IP-1, IP-2 (and full BUILD coverage verification)
**Wave:** 0
**Depends on:** Task 4

<read_first>
- `.gitignore` (full file — confirm `build/` exists for Python artifacts, `builds/` is absent)
- `.planning/research/PITFALLS.md` Pitfall 4 (Build Directory Pollution / Git Noise)
- `.planning/phases/207-versioned-build-system/207-VALIDATION.md` (full test scenario list)
</read_first>

<action>
**MODIFY `.gitignore`** — add `builds/` entry. Group near existing build-artifact section. CRITICAL: do NOT remove existing `build/` (Python artifacts) and do NOT ignore `.kicad_build_spec.json` (Phase 205 source sidecar). Add:
```gitignore
# Phase 207: versioned build artifacts (snapshot copies + manifests)
builds/
```
Place it after the existing `build/` line (or in the build artifacts section). A bare `builds/` (no leading slash) matches the directory at any depth, which is correct for project-scoped build trees (INTEG-04).

**Run full verification suite:**
1. `grep -n "^builds/" .gitignore` — confirm entry present.
2. `grep -c "build/" .gitignore` — confirm the original `build/` (singular) still present (should be >= 1).
3. Run the full build system test suite: `.venv/bin/python -m pytest tests/test_build_system.py -x -q -o addopts="" -o pythonpath="src tests"`.
4. Run the registry tests: `.venv/bin/python -m pytest tests/test_registry.py -x -q -o addopts="" -o pythonpath="src tests"` (count==159, readonly set +3).
5. Run the manifest regression: `.venv/bin/python -m pytest tests/test_manufacturing_gate.py -x -q -o addopts="" -o pythonpath="src tests"` (no regressions from serialization additions).
6. Run the Phase 205/206 metadata/DRC tests to confirm no cross-phase regression: `.venv/bin/python -m pytest tests/test_board_metadata_ops.py -x -q -o addopts="" -o pythonpath="src tests"`.
7. Validate schema/registry sync: `.venv/bin/python -c "from volta.ops.registry import validate_registry_completeness; r=validate_registry_completeness(); assert r['extra_in_registry']==[]; print('sync ok')"`.
8. Run the full test suite to catch any other regressions: `.venv/bin/python -m pytest tests/ -q -o addopts="" -o pythonpath="src tests"`.

If any full-suite failure surfaces that is NOT caused by Phase 207 changes (pre-existing flaky tests, missing external deps like ngspice), document it but do not block — only Phase 207-introduced failures must be fixed.
</action>

<acceptance_criteria>
- `grep -n "^builds/" .gitignore` returns a match (BUILD-09)
- `grep -n "^build/" .gitignore` returns a match (original Python build/ preserved — Pitfall 4 mitigation)
- `.venv/bin/python -m pytest tests/test_build_system.py -q -o addopts="" -o pythonpath="src tests"` passes with ALL test classes (TestBuildModel, TestBuildCreate, TestBuildList, TestBuildShow)
- `.venv/bin/python -m pytest tests/test_registry.py -q -o addopts="" -o pythonpath="src tests"` passes with count==159
- `.venv/bin/python -m pytest tests/test_manufacturing_gate.py -q -o addopts="" -o pythonpath="src tests"` passes (no regression)
- `.venv/bin/python -c "from volta.ops.registry import validate_registry_completeness; r=validate_registry_completeness(); assert r['extra_in_registry']==[]; assert 'build_create' not in r['missing_from_registry']; assert 'build_list' not in r['missing_from_registry']; assert 'build_show' not in r['missing_from_registry']"` exits 0
- Full suite `.venv/bin/python -m pytest tests/ -q -o addopts="" -o pythonpath="src tests"` has zero failures attributable to Phase 207 changes
</acceptance_criteria>

---

<verification_criteria>
**Success Criteria (from ROADMAP.md Phase 207) — all must be TRUE after execution:**

1. `build_create` on a clean board returns a build record with `build_id`, `board_rev` (from `title_block`), `git_sha` (HEAD or "unknown"), timestamp; `builds/v{rev}_{timestamp}/` created. (BUILD-01, BUILD-06)
2. `build_create` on a board that fails to parse returns a clear error — NO build created, no partial state. (BUILD-04)
3. `manifest.json` serialized to disk with SHA256 hashes for each artifact; `build_show` reproduces the build record exactly. (BUILD-05, BUILD-08)
4. `build_list` shows all builds for the project with status. (BUILD-07)
5. `builds/` in `.gitignore`. (BUILD-09)
6. `Build` record has all BUILD-02 fields; `BuildStatus` lifecycle draft→validated→exported→handed_off with `transition_to`. (BUILD-02, BUILD-03)
7. `diff_builds()` compares two builds (source diffs, artifact diffs, status changes). (BUILD-10)

**Quality gates:**
- Registry count == 159 (IP-1)
- `validate_registry_completeness` passes — schema union + registry in sync (IP-2)
- All 3 ops reachable via `_QUERY_HANDLERS` (IP-3 — merge worked)
- Target `.kicad_pcb` byte-identical after `build_create` (`is_readonly: True` defended)
- No regressions in `test_manufacturing_gate.py` or `test_board_metadata_ops.py`
</verification_criteria>

## PLANNING COMPLETE
