bretbouchard/kicad-agent/.planning/phases/208-manufacturer-handoff-package/208-01-PLAN.md

---
phase: 208
plan: 01
slug: manufacturer-handoff-package
title: "Manufacturer Handoff Package — one-call zip bundle with proof of manufacturability"
requirements: [HANDOFF-01, HANDOFF-02, HANDOFF-03, HANDOFF-04, HANDOFF-05, HANDOFF-06, HANDOFF-07, HANDOFF-08, HANDOFF-09]
depends_on: [205, 206, 207]
created: 2026-07-11
status: draft
---

# Phase 208 Plan 01 — Manufacturer Handoff Package

**Goal:** One call (`build_handoff_export`) produces a complete zip bundle with all manufacturing artifacts + readme + manifest, with a pre-handoff validation gate that blocks incomplete bundles (no zip on DRC/ERC failure). Generalizes the hard-coded JLCPCB BOM into a profile-driven formatter. Embeds DRC/ERC results in the manifest as proof of manufacturability.

**Phase source dir:** `.planning/phases/208-manufacturer-handoff-package/`

## Threat Model

| # | Attack surface | Threat | Mitigation (task) |
|---|---|---|---|
| TM-1 | `project_dir` on `BuildHandoffExportOp` | Path traversal via `..` segments writing zip outside project | Task 5: reject `".." in Path(op.project_dir).parts` before any disk write (mirror `build.py:66-71`) |
| TM-2 | `zipfile.write(filepath, arcname)` | Zip-slip via crafted `arcname` containing `../` | Task 3: arcname is always `artifact_file.name` (basename only) — never a path. Assert in tests no arcname contains a path separator |
| TM-3 | `vendor` field on `BuildHandoffExportOp` | Profile-name injection / file-path escape (`vendor="../../etc/passwd"`) | Task 5: `pattern=r"^[a-z0-9_]+$"` on the Pydantic field (same as `DrcVendorOp.vendor`); `load_profile` resolution rejects unknown keys |
| TM-4 | readme.md generation | XSS / markdown injection via board name/title/company from `title_block` (user-controlled PCB content) | Task 4: readme is plain markdown written via `atomic_write`; never rendered as HTML by this codebase. Document that the readme is data, not a trusted executable context |
| TM-5 | BOM column injection | CSV formula injection via component `Value`/`Reference` fields (=cmd, @cmd) reaching vendor CSVs | Task 2: prefix any cell starting with `=`, `+`, `-`, `@`, `\t`, `\r` with a single quote `'` when writing vendor BOM CSVs (defensive; recorders in the wild) |
| TM-6 | Export file paths | Export wrappers write into `build_dir`; symlink-following could escape | Task 3: `build_dir` created with `mkdir(parents=True, exist_ok=False)` under resolved `project_dir`; wrappers receive absolute `build_dir` paths |

## Must Haves (from phase goal)

1. `build_handoff_export` op exists and is registered (HANDOFF-01)
2. One call produces: gerbers, drill, BOM, pick-and-place, STEP (optional), netlist, schematic PDF (if sch), PCB PDF (HANDOFF-02)
3. Everything bundled into a single `handoff.zip` with manifest.json + readme.md, streamed (no memory blow-up on large STEP) (HANDOFF-03, Pitfall 7)
4. readme.md contains board name, rev, date, company, layer count, dimensions, surface finish, copper weight, mask/silk color, impedance requirements, DRC/ERC results (HANDOFF-04)
5. BOM formatting is profile-driven via `ManufacturerProfile` output fields — handoff orchestrator NEVER calls `export_jlcpcb_bom` directly (HANDOFF-05, Pitfall 3)
6. Pre-handoff validation gate: DRC fail / ERC fail / vendor DRC fail → NO zip created, clear error (HANDOFF-06, Pitfall 5)
7. STEP/render inclusion configurable via `include_step` / `include_render` (HANDOFF-07)
8. `build_handoff_export(vendor="jlcpcb")` produces JLCPCB-formatted BOM/CPL via the profile (HANDOFF-08)
9. `manifest.json` includes `drc_passed`, `erc_passed`, `vendor_drc_passed`, `drc_violation_count`, `erc_violation_count` (HANDOFF-09)

---

## Task 1 — Extend data models (ManufacturerProfile output spec + ManufacturingManifest validation fields)

**Requirements:** HANDOFF-05 (model side), HANDOFF-09 (model side)

**Why first:** Every later task depends on these fields existing on the two models. Adding them with backward-compatible defaults touches nothing at runtime.

<read_first>
- `src/volta/dfm/profiles.py` (lines 26-57 for `ManufacturerProfile`, 112-144 for `_JLCPCB_STANDARD` literals)
- `src/volta/validation/gates/manufacturing_manifest.py` (lines 1-160 for `ManufacturingManifest`, `to_json`, `save`, `load`)
- `.planning/phases/208-manufacturer-handoff-package/208-PATTERNS.md` FILE 4 (profiles.py edit) and FILE 5 (manifest edit)
- `.planning/phases/208-manufacturer-handoff-package/208-RESEARCH.md` RQ5 (profile fields) and RQ8 (manifest fields)
</read_first>

<action>
1. In `dfm/profiles.py`, add 4 fields to `ManufacturerProfile` immediately after `drc_rules_path` (after line 57). Exact field definitions:
   ```python
   bom_columns: tuple[str, ...] | None = Field(default=None, description="BOM column names for vendor-specific CSV format. None = generic default.")
   bom_filename_pattern: str | None = Field(default=None, description="BOM filename pattern with {stem} placeholder. None = generic default.")
   cpl_filename_pattern: str | None = Field(default=None, description="Pick-and-place filename pattern with {stem} placeholder.")
   include_step_by_default: bool = Field(default=True, description="Whether STEP 3D model is included in handoff by default.")
   ```
2. Set the new fields on `_JLCPCB_STANDARD`:
   `bom_columns=("Comment", "Designator", "Footprint", "LCSC")`, `bom_filename_pattern="{stem}_JLCPCB-BOM.csv"`, `cpl_filename_pattern="{stem}_JLCPCB-CPL.csv"`.
   Do NOT modify `_PCBWAY_STANDARD`, `_OSH_PARK`, `_GENERIC_CONSERVATIVE`, `_ADVANCED_CIRCITS`, or any `_AISLER_*` profile — they inherit `None` defaults (generic format).
3. In `validation/gates/manufacturing_manifest.py`, add 5 fields to `ManufacturingManifest` after `generated_at`:
   `drc_passed: Optional[bool] = None`, `erc_passed: Optional[bool] = None`, `vendor_drc_passed: Optional[bool] = None`, `drc_violation_count: int = 0`, `erc_violation_count: int = 0`.
   `Optional` is already imported (`from typing import Any, Optional` at line 17).
4. Update `to_json()` to add the 5 keys to the `data` dict (after `"generated_at"`).
5. Update `load()` classmethod to read the 5 keys with `.get(key, default)` for backward compatibility with Phase 207 manifests that lack them.
</action>

<acceptance_criteria>
- `grep -n "bom_columns: tuple" src/volta/dfm/profiles.py` returns 1 match
- `grep -n "include_step_by_default: bool" src/volta/dfm/profiles.py` returns 1 match
- `grep -n 'bom_columns=("Comment", "Designator", "Footprint", "LCSC")' src/volta/dfm/profiles.py` returns 1 match (on `_JLCPCB_STANDARD`)
- `grep -n "drc_passed: Optional\[bool\]" src/volta/validation/gates/manufacturing_manifest.py` returns 1 match
- `grep -c "drc_violation_count" src/volta/validation/gates/manufacturing_manifest.py` returns >= 3 (field decl + to_json + load)
- `.venv/bin/python -c "from volta.dfm.profiles import load_profile; p=load_profile('jlcpcb'); assert p.bom_columns==('Comment','Designator','Footprint','LCSC'); assert p.bom_filename_pattern=='{stem}_JLCPCB-BOM.csv'"` exits 0
- `.venv/bin/python -c "from volta.dfm.profiles import load_profile; p=load_profile('generic'); assert p.bom_columns is None"` exits 0 (generic unaffected)
- `.venv/bin/python -m pytest tests/test_build_system.py -q -o addopts="" -o pythonpath="src tests"` passes (Phase 207 manifest round-trip still works with new fields)
</acceptance_criteria>

---

## Task 2 — Profile-driven BOM formatter (`export_bom_profile`)

**Requirements:** HANDOFF-05 (formatter), Pitfall 3 prevention

<read_first>
- `src/volta/export/bom.py` (lines 1-50 imports + result types, 76-167 `export_bom`, 168-242 `parse_bom_csv`/`enrich_with_lcsc`, 311-375 `export_jlcpcb_bom`)
- `.planning/phases/208-manufacturer-handoff-package/208-PATTERNS.md` FILE 3 (bom.py edit with full `export_bom_profile` skeleton)
- `.planning/phases/208-manufacturer-handoff-package/208-RESEARCH.md` RQ2 (column mapping, alias table)
- `src/volta/dfm/profiles.py` (after Task 1 — `ManufacturerProfile` now has `bom_columns` etc.)
</read_first>

<action>
1. Add `export_bom_profile(sch_path: Path, output_dir: Path, profile: ManufacturerProfile | None = None) -> BomResult` to `export/bom.py`.
2. Logic:
   - If `profile is None` OR `profile.bom_columns is None` → call `export_bom(sch_path, output_path=output_dir / f"{sch_path.stem}-BOM.csv")` and return its result unchanged (generic default).
   - If `profile.bom_columns` is set: call `export_bom(sch_path, output_path=<temp>)` to get the standard CSV, parse it via `parse_bom_csv`, enrich with LCSC if any target column requires it (use `enrich_with_lcsc` when `"LCSC"` in `profile.bom_columns`), then rewrite via `csv.DictWriter` with `profile.bom_columns` as fieldnames.
   - Source-to-target column mapping (alias table, built inside the function): `Comment`←`Value` (fallback `Comment`), `Designator`←`Reference`, `Footprint`←`Footprint`, `LCSC`←`LCSC` (from enrichment). Any target column with no known source is written as empty string.
   - Apply CSV formula-injection defense (TM-5): prefix cell values starting with `=`, `+`, `-`, `@`, `\t`, `\r` with a leading `'`.
   - If `profile.bom_filename_pattern` is set, format it with `{stem=sch_path.stem}` to derive the output filename; otherwise use `f"{sch_path.stem}-BOM.csv"`.
3. Add import at top of `bom.py`: `from volta.dfm.profiles import ManufacturerProfile` (inside the function body to avoid any import-cycle risk if profiles imports from export — verify profiles.py does NOT import from export/bom.py before promoting to module top).
4. Do NOT change `export_bom` or `export_jlcpcb_bom` signatures. Optionally refactor `export_jlcpcb_bom` to delegate to `export_bom_profile(schematic_path, schematic_path.parent, load_profile("jlcpcb"))` — verify the JLCPCB test still passes before and after.
</action>

<acceptance_criteria>
- `grep -n "def export_bom_profile" src/volta/export/bom.py` returns 1 match
- `grep -n "from volta.dfm.profiles import ManufacturerProfile" src/volta/export/bom.py` returns >= 1 match
- New test `tests/test_handoff.py::test_bom_profile_generic_columns` (or a dedicated `tests/test_export_bom.py` addition) asserts: calling `export_bom_profile(sch, out_dir, profile=None)` produces a CSV with kicad-cli default columns (or with `monkeypatch` stubbing kicad-cli, produces a generic CSV with `Reference`/`Value` headers).
- New test `tests/test_handoff.py::test_bom_profile_jlcpcb_columns` asserts: calling with `load_profile("jlcpcb")` produces a CSV whose header row is exactly `Comment,Designator,Footprint,LCSC`.
- `.venv/bin/python -m pytest tests/test_export_bom.py -q -o addopts="" -o pythonpath="src tests"` passes (no regression on existing BOM tests; if kicad-cli absent, existing skip mark applies).
- `grep -rn "export_jlcpcb_bom" src/volta/manufacturing/` returns 0 matches (handoff code never calls the hard-coded function — Pitfall 3)
</acceptance_criteria>

---

## Task 3 — Handoff orchestrator (`manufacturing/handoff.py`) + `HandoffResult`/`HandoffValidation`

**Requirements:** HANDOFF-01, HANDOFF-02, HANDOFF-03, HANDOFF-06, HANDOFF-07, HANDOFF-09 (orchestrator side)

**Why after Task 1+2:** Depends on `ManufacturerProfile` output fields and `export_bom_profile`.

<read_first>
- `src/volta/ops/handlers/build.py` (lines 34-170 — `_handle_build_create` pipeline skeleton: project_dir resolution, NativeParser re-parse, build dir creation, manifest serialization, no-partial-state cleanup)
- `src/volta/ops/handlers/query.py` (lines 88-150 — `_handle_drc_vendor` defensive DRC call pattern, NativeParser re-parse for vendor DRC)
- `src/volta/validation/erc_drc.py` (lines 58-122 result classes, 171-210 `run_erc`, 322-360 `run_drc`)
- `src/volta/manufacturing/vendor_drc.py` (lines 31-53 `VendorDrcResult`, line 89 `run_vendor_drc`)
- `src/volta/export/gerber.py` (lines 30 `ExportResult`, 101 `_run_kicad_export`, 136 `export_gerber`, 206 `export_drill`)
- `src/volta/export/general.py` (lines 59 `export_position`, 122 `export_netlist`, 176 `export_step`, 241 `export_schematic_pdf`, 298 `get_board_statistics`)
- `src/volta/export/render.py` (line 296 `export_pcb_pdf`)
- `src/volta/validation/gates/manufacturing_manifest.py` (lines 33-45 `ManufacturingArtifact.from_file`)
- `src/volta/io/atomic_write.py` (lines 15-43 `atomic_write`)
- `src/volta/manufacturing/board_spec.py` (lines 67-72 `load_board_spec`)
- `.planning/phases/208-manufacturer-handoff-package/208-PATTERNS.md` FILE 1 (handoff.py skeleton), FILE 1b (streaming zip), FILE 1c (result dataclasses)
- `.planning/phases/208-manufacturer-handoff-package/208-RESEARCH.md` RQ1 (wrapper signatures + failure behavior), RQ3 (streaming zip), RQ4 (ERC/DRC tri-state), Validation Architecture section
</read_first>

<action>
1. Create `src/volta/manufacturing/handoff.py`.
2. Define two frozen dataclasses (per PATTERNS FILE 1c):
   - `HandoffValidation(drc_passed: bool|None, erc_passed: bool|None, vendor_drc_passed: bool|None, drc_violations: int, erc_violations: int, vendor_drc_violations: int)`
   - `HandoffResult(success: bool, zip_path: str, manifest: ManufacturingManifest, build: Build|None, validation: HandoffValidation, error_message: str = "")`
3. Define `export_handoff(pcb_path: Path, sch_path: Path|None, project_dir: Path, vendor: str|None=None, include_step: bool=True, include_render: bool=False, skip_validation: bool=False) -> HandoffResult`.
   Import the export wrappers it calls at module top so tests can monkeypatch them on the `handoff` module namespace (e.g. `from volta.export.gerber import export_gerber, export_drill`, `from volta.export.general import export_position, export_step, export_netlist, export_schematic_pdf, get_board_statistics`, `from volta.export.render import export_pcb_pdf`, `from volta.export.bom import export_bom_profile`).
4. Pipeline (11 steps, in order):
   - **Step 1:** Schematic discovery — if `sch_path is None`, try `pcb_path.with_suffix(".kicad_sch")`; if not a file, `sch_path = None` (PCB-only mode).
   - **Step 2:** Parse PCB via `NativeParser.parse_pcb(pcb_path)` → `NativeBoard` (needed for title_block + vendor DRC geometry; same dual-path as `build_create`). Read `title_block` (rev/title/date/company) defensively (may be None).
   - **Step 3 — Validation gate** (unless `skip_validation`): run `run_drc(pcb_path)`, `run_erc(sch_path)` (if sch), `run_vendor_drc(board, profile)` (if vendor, after `load_profile(vendor)`). For each, map tri-state via `error_message` (set → `None`/inconclusive; `not passed` with no error_message → `False` → BLOCK; `passed` → `True`). If ANY check is `False` → return `HandoffResult(success=False, zip_path="", manifest=<empty>, build=None, validation=<partial>, error_message="pre-handoff validation failed: DRC|ERC|vendor DRC")` with NO zip created (HANDOFF-06, Pitfall 5). Inconclusive (`None`) does NOT block (graceful degradation per CONTEXT.md). Build the `HandoffValidation` from these results.
   - **Step 4:** Create build dir `project_dir / "builds" / f"handoff_{datetime.now(timezone.utc).strftime('%Y%m%d_%H%M%S')}"` via `mkdir(parents=True, exist_ok=False)` (handle sub-second collision by appending a short uuid suffix, mirroring `build_create` lines 99-104).
   - **Step 5 — Run exports** into `build_dir`. Note the `output_dir` vs `output_path` divergence (RQ1): pass the correct kwarg per wrapper. Critical exports (gerbers, drill, bom-if-sch, cpl) failing blocks the handoff (return `success=False` and rmtree the build dir). Non-critical (step, render, schematic PDF if sch, PCB PDF) failures are logged and tolerated. For BOM use `export_bom_profile(sch_path, build_dir, profile)` — NEVER `export_jlcpcb_bom`. For vendor DRC, pass the loaded `profile`. Collect all produced file paths.
   - **Step 6:** Build `ManufacturingArtifact.from_file(name=<category>, path=str(f), generated_by=<command>)` for each exported file (iterate `result.files` for multi-file results; single-file for step/pdf).
   - **Step 7:** Generate readme.md (Task 4 function) and write via `atomic_write(build_dir / "readme.md", readme_content)`.
   - **Step 8:** Construct `ManufacturingManifest(project_name=stem, board_name=title, fab_profile=vendor or "generic", artifacts=tuple(artifacts), bom_rows=<count>, total_components=<count>, generated_at=<iso>, drc_passed=..., erc_passed=..., vendor_drc_passed=..., drc_violation_count=..., erc_violation_count=...)` and `manifest.save(build_dir / "manifest.json")`.
   - **Step 9 — Streaming zip** (Pitfall 7, TM-2): `zip_path = build_dir / "handoff.zip"`; `with zipfile.ZipFile(zip_path, "w", zipfile.ZIP_DEFLATED) as zf:` loop over `build_dir.iterdir()` files (excluding `handoff.zip` itself) and `zf.write(artifact_file, arcname=artifact_file.name)`. Arcname is ALWAYS the basename (never a path) — TM-2 mitigation.
   - **Step 10:** Wrap the whole pipeline in try/except; on ANY exception, `shutil.rmtree(build_dir, ignore_errors=True)` and return `HandoffResult(success=False, ...)` (no partial state — mirror `build_create:162-170`).
   - **Step 11:** Return `HandoffResult(success=True, zip_path=str(zip_path.relative_to(project_dir)), manifest=manifest, build=None, validation=validation)`.
5. Include a module docstring documenting the threat-model mitigations (TM-1 through TM-6).
</action>

<acceptance_criteria>
- `test -f src/volta/manufacturing/handoff.py` passes
- `grep -n "def export_handoff" src/volta/manufacturing/handoff.py` returns 1 match
- `grep -n "class HandoffResult\|class HandoffValidation" src/volta/manufacturing/handoff.py` returns 2 matches
- `grep -n "ZIP_DEFLATED" src/volta/manufacturing/handoff.py` returns 1 match (streaming zip, Pitfall 7)
- `grep -n "arcname=" src/volta/manufacturing/handoff.py` returns >= 1 match where the arcname expression uses `.name` (basename only — TM-2)
- `grep -n "shutil.rmtree" src/volta/manufacturing/handoff.py` returns >= 1 match (no-partial-state cleanup)
- `grep -n "export_bom_profile" src/volta/manufacturing/handoff.py` returns >= 1 match AND `grep -n "export_jlcpcb_bom" src/volta/manufacturing/handoff.py` returns 0 matches (Pitfall 3)
- `grep -n 'NativeParser.parse_pcb' src/volta/manufacturing/handoff.py` returns >= 1 match (vendor DRC needs NativeBoard)
- `tests/test_handoff.py::test_handoff_creates_zip` (stub export wrappers via monkeypatch, `skip_validation=True`) asserts: `result.success is True`, `result.zip_path` is non-empty, and the zip file exists on disk under `builds/handoff_*/handoff.zip`.
- `tests/test_handoff.py::test_handoff_blocks_on_drc_failure` asserts: with a stubbed `run_drc` returning `DrcResult(passed=False, file_path=..., error_message=None)`, `result.success is False` AND no `handoff.zip` exists anywhere under the project dir (HANDOFF-06).
- `tests/test_handoff.py::test_handoff_includes_all_artifacts` asserts the zip contains filenames matching gerber, drill, bom (when sch present), cpl, manifest.json, readme.md.
- `tests/test_handoff.py::test_handoff_step_excluded_when_flag_false` asserts: `include_step=False` → zip contains no `.step` file (HANDOFF-07).
- `tests/test_handoff.py::test_handoff_no_partial_state_on_failure` asserts: after a validation failure, no `builds/handoff_*` directory remains.
- `tests/test_handoff.py::test_handoff_arcname_no_path_separator` asserts: every name in `zipfile.ZipFile(zip_path).namelist()` contains no `/` or `\\` (TM-2).
- `tests/test_handoff.py::test_target_file_unchanged` asserts: `.kicad_pcb` bytes are identical before and after `export_handoff` (read-only guarantee).
- `.venv/bin/python -m pytest tests/test_handoff.py -q -o addopts="" -o pythonpath="src tests"` passes
</acceptance_criteria>

---

## Task 4 — readme.md generation (HANDOFF-04)

**Requirements:** HANDOFF-04

**Why part of Task 3's pipeline but separable for clarity:** The readme pulls from 4 data sources (title_block, BoardSpec, board stats, validation results). Implement it as a private function `_generate_readme(...)` in `handoff.py` called from the orchestrator.

<read_first>
- `src/volta/export/general.py` (lines 298-375 `get_board_statistics` — pure Python, no kicad-cli; returns dict with `layer_count`, `board_width_mm`, `board_height_mm`, `component_count`, `net_count`)
- `src/volta/manufacturing/board_spec.py` (lines 1-72 `BoardSpec` fields: `surface_finish`, `copper_weight_outer_oz`, `copper_weight_inner_oz`, `soldermask_color`, `silkscreen_color`, `impedance_requirements`, `load_board_spec`)
- `.planning/phases/208-manufacturer-handoff-package/208-CONTEXT.md` (lines 119-148 readme template)
- `.planning/phases/208-manufacturer-handoff-package/208-RESEARCH.md` RQ7 (full data-source map)
</read_first>

<action>
1. In `manufacturing/handoff.py`, add private function `_generate_readme(title_block, board_spec, board_stats, validation, vendor, generated_at) -> str`.
2. Build a markdown string from the CONTEXT.md template (lines 119-148) with these sections:
   - Header: `# Manufacturing Handoff: {board_name}` where board_name = `title_block.title or stem`.
   - Metadata block: Revision, Date, Company (from title_block), Generated timestamp.
   - Board Specifications: surface finish, copper weight (outer/inner oz), soldermask color, silkscreen color (from `board_spec` — handle `board_spec is None` gracefully with "not specified"), layer count + dimensions (from `board_stats`).
   - Impedance Requirements: if `board_spec.impedance_requirements` non-empty, a markdown table (net, target ohms, reference layer); else omit the section.
   - Validation Results: DRC (passed/failed/inconclusive + violation count), ERC (passed/failed/N/A), Vendor DRC (vendor name + result).
   - Artifacts: markdown table of all files in the bundle (name, size).
   - Contact: "Designed by: {company}".
3. All values are plain text interpolated into markdown. No HTML, no executable content. TM-4: document in a comment that the readme is data, not a trusted executable context.
4. Call `_generate_readme(...)` from the orchestrator (Task 3 step 7) and write via `atomic_write(build_dir / "readme.md", readme_content)`.
</action>

<acceptance_criteria>
- `grep -n "def _generate_readme" src/volta/manufacturing/handoff.py` returns 1 match
- `tests/test_handoff.py::test_readme_has_board_name` asserts the generated readme contains the board title from `title_block`.
- `tests/test_handoff.py::test_readme_has_surface_finish` asserts that when a `BoardSpec` sidecar exists with `surface_finish="ENIG"`, the readme contains "ENIG".
- `tests/test_handoff.py::test_readme_has_validation_results` asserts the readme contains "DRC" and either "passed"/"failed"/"inconclusive".
- `tests/test_handoff.py::test_readme_has_dimensions` asserts the readme contains the board width/height from `get_board_statistics`.
- `tests/test_handoff.py::test_readme_handles_missing_board_spec` asserts: no sidecar → readme still generates with "not specified" placeholders, no exception.
</acceptance_criteria>

---

## Task 5 — `build_handoff_export` op wiring (schema + registry + handler)

**Requirements:** HANDOFF-01 (op side), HANDOFF-08 (vendor param)

**Why after Task 3:** The handler delegates to `export_handoff`.

<read_first>
- `src/volta/ops/_schema_pcb.py` (lines 1284-1360 Phase 207 build op section: `BuildCreateOp`, `BuildListOp`, `BuildShowOp`; also lines 1258-1262 `DrcVendorOp.vendor` pattern)
- `src/volta/ops/schema.py` (lines 285-287 Build imports, 570-572 Operation union, 789-791 `__all__`)
- `src/volta/ops/registry.py` (lines 1462-1490 Phase 207 build `_RAW_CATALOG` entries; line 1490 is the closing `}` of `_RAW_CATALOG`)
- `src/volta/ops/handlers/build.py` (lines 34-35 `register_build` + signature pattern; lines 255-317 `_handle_build_show` for the dict-assembly pattern)
- `src/volta/ops/handlers/__init__.py` (lines 33-35 `_QUERY_HANDLERS.update(_BUILD_HANDLERS)` — already merges build handlers; NO change needed)
- `.planning/phases/208-manufacturer-handoff-package/208-PATTERNS.md` FILE 6 (schema), FILE 7 (schema.py union), FILE 8 (registry), FILE 9 (handler)
- `.planning/phases/208-manufacturer-handoff-package/208-RESEARCH.md` RQ6 (registry count 159→160, test spots)
</read_first>

<action>
1. In `ops/_schema_pcb.py`, add `BuildHandoffExportOp(BaseModel)` after `BuildShowOp` (with a `# Phase 208` section header). Fields (exact):
   - `op_type: Literal["build_handoff_export"] = "build_handoff_export"`
   - `target_file: TargetFile`
   - `project_dir: Optional[str] = Field(default=None, description="Project root (defaults to target_file parent)")`
   - `vendor: Optional[str] = Field(default=None, min_length=1, max_length=64, pattern=r"^[a-z0-9_]+$", description="Vendor key (jlcpcb, pcbway, etc.) for profile-driven output")` (TM-3)
   - `include_step: bool = Field(default=True, description="Include STEP 3D model in the bundle")`
   - `include_render: bool = Field(default=False, description="Include PCB render image (slow)")`
   - `skip_validation: bool = Field(default=False, description="Skip pre-handoff DRC/ERC validation gate")`
2. In `ops/schema.py`, three edits (mirror the `BuildShowOp` pattern exactly):
   - Add `BuildHandoffExportOp,` to the import block after `BuildShowOp,` (line ~287).
   - Add `| BuildHandoffExportOp,` to the `Operation` union after `| BuildShowOp,` (line ~572).
   - Add `"BuildHandoffExportOp",` to `__all__` after `"BuildShowOp",` (line ~791).
3. In `ops/registry.py`, add the `_RAW_CATALOG` entry after `build_show` (before the closing `}` at line 1490):
   ```python
   "build_handoff_export": {
       "category": "query",
       "description": "Export a complete manufacturer handoff zip: gerbers, drill, BOM, CPL, STEP, PDFs, readme, manifest with DRC/ERC proof",
       "file_types": [".kicad_pcb"],
       "is_readonly": True,
       "scope": "single_file",
       "requires": [],
       "conflicts": [],
   },
   ```
   Note: `scope: "single_file"` and `is_readonly: True` — same as the shipped `build_create` (NOT `CROSS_FILE_OP_TYPES`; build ops use query dispatch via `_QUERY_HANDLERS`).
4. In `ops/handlers/build.py`, add `_handle_build_handoff_export` decorated with `@register_build("build_handoff_export")` after `_handle_build_show`. The handler (per PATTERNS FILE 9):
   - Resolve `project_dir` and reject `".." in Path(op.project_dir).parts` (TM-1) — reuse `_resolve_project_dir` helper (returns Path or error dict); return the dict if traversal error.
   - Call `export_handoff(pcb_path=Path(file_path), sch_path=None, project_dir=project_dir, vendor=op.vendor, include_step=op.include_step, include_render=op.include_render, skip_validation=op.skip_validation)`.
   - Serialize `HandoffResult` to a dict: `success`, `zip_path`, `validation` (via `dataclasses.asdict`), `error_message`, `manifest` (via `result.manifest.to_json()`), `artifact_count` (`len(result.manifest.artifacts)`), plus `build_id`/`build_status` if `result.build` is not None.
5. Do NOT modify `ops/handlers/__init__.py` — the existing `_QUERY_HANDLERS.update(_BUILD_HANDLERS)` (line 35) already merges new build handlers. Do NOT add to `CROSS_FILE_OP_TYPES` in `execution.py` (build ops are single_file query ops).
</action>

<acceptance_criteria>
- `grep -n "class BuildHandoffExportOp" src/volta/ops/_schema_pcb.py` returns 1 match
- `grep -n "pattern=r\"^\[a-z0-9_\]+\$\"" src/volta/ops/_schema_pcb.py` returns >= 1 match (TM-3, vendor field)
- `grep -n "BuildHandoffExportOp" src/volta/ops/schema.py` returns 3 matches (import, union, `__all__`)
- `grep -n '"build_handoff_export"' src/volta/ops/registry.py` returns 1 match
- `grep -n '"is_readonly": True' src/volta/ops/registry.py | wc -l` is consistent with the prior count + 1 (the new entry is readonly)
- `grep -n "_handle_build_handoff_export" src/volta/ops/handlers/build.py` returns 2 matches (def + decorator) 
- `grep -n 'register_build("build_handoff_export")' src/volta/ops/handlers/build.py` returns 1 match
- `grep -n "CROSS_FILE_OP_TYPES\|build_handoff" src/volta/ops/execution.py` does NOT show build_handoff_export added to CROSS_FILE_OP_TYPES (it is single_file scope)
- `.venv/bin/python -c "from volta.ops.schema import Operation, BuildHandoffExportOp; print(BuildHandoffExportOp.__name__)"` exits 0 and prints `BuildHandoffExportOp`
- `.venv/bin/python -c "from volta.ops.registry import OPERATION_REGISTRY; m=OPERATION_REGISTRY['build_handoff_export']; assert m.is_readonly and m.category=='query' and m.scope=='single_file'"` exits 0
- `.venv/bin/python -c "from volta.ops.handlers.query import _QUERY_HANDLERS; assert 'build_handoff_export' in _QUERY_HANDLERS"` exits 0 (handler merged via `_BUILD_HANDLERS`)
</acceptance_criteria>

---

## Task 6 — Update registry test assertions + integration verification

**Requirements:** HANDOFF-01 (registry completeness), IP-1, IP-2

<read_first>
- `tests/test_registry.py` (lines 23-26 `test_registry_has_98_operations` count assertion, 107-160 `test_readonly_operations_count` expected set)
- `src/volta/ops/registry.py` (lines 1492-1500 `OPERATION_REGISTRY` construction + `VALID_CATEGORIES`)
- `.planning/phases/208-manufacturer-handoff-package/208-PATTERNS.md` FILE 10 (test edits)
- `.planning/phases/208-manufacturer-handoff-package/208-RESEARCH.md` RQ6 (count 159→160)
</read_first>

<action>
1. In `tests/test_registry.py`, update `test_registry_has_98_operations`:
   - Line 26: change `assert len(OPERATION_REGISTRY) == 159` → `== 160`.
   - Update the comment (lines 24-25) to: `# Phase 208: 160 ops (was 159 after Phase 207; +1: build_handoff_export).`
2. In `tests/test_registry.py`, update `test_readonly_operations_count`:
   - Add `"build_handoff_export",` to the `expected_readonly` set, alphabetically between `"build_create"` and `"build_list"` (after line 118).
3. Run the full registry + build + handoff test suite and confirm `validate_registry_completeness()` still passes (no schema/registry drift — IP-2).
4. Confirm `test_validate_registry_completeness_passes` `_KNOWN_PREEXISTING_MISSING` set is unchanged (the 3 pre-existing missing ops stay; build_handoff_export is NOT missing).
</action>

<acceptance_criteria>
- `grep -n "assert len(OPERATION_REGISTRY) == 160" tests/test_registry.py` returns 1 match
- `grep -n '"build_handoff_export"' tests/test_registry.py` returns 1 match (in the `expected_readonly` set)
- `.venv/bin/python -m pytest tests/test_registry.py -q -o addopts="" -o pythonpath="src tests"` passes (all registry tests green, including completeness)
- `.venv/bin/python -m pytest tests/test_build_system.py tests/test_handoff.py -q -o addopts="" -o pythonpath="src tests"` passes (no Phase 207 regression, all handoff tests green)
</acceptance_criteria>

---

## Verification (full-suite gate)

After all 6 tasks, run the full suite to confirm zero regressions across the v7.0 milestone:

<action>
`.venv/bin/python -m pytest tests/ -q -o addopts="" -o pythonpath="src tests"`
</action>

<acceptance_criteria>
- Full suite passes (expected ~3000+ tests green).
- No new skips introduced (BLK-1 strict pattern — tests must `pytest.fail(pytrace=False)` on missing kicad-cli, not skip, EXCEPT where the existing `tests/test_export_bom.py` module-level `pytestmark = pytest.mark.skipif` pattern is followed for kicad-cli-dependent export tests; handoff unit tests must use `monkeypatch` stubs, not skips, so they run in CI).
- `.venv/bin/python -c "import volta.manufacturing.handoff; import volta.ops.handlers.build; print('imports clean')"` exits 0.
</acceptance_criteria>

---

## Summary of edit deltas

| File | Action | Est. lines |
|---|---|---|
| `src/volta/manufacturing/handoff.py` | CREATE | ~300-400 |
| `src/volta/dfm/profiles.py` | MODIFY | +4 fields on class, +3 fields on `_JLCPCB_STANDARD` |
| `src/volta/validation/gates/manufacturing_manifest.py` | MODIFY | +5 fields, +5 `to_json` lines, +5 `load` lines |
| `src/volta/export/bom.py` | MODIFY | +50 (`export_bom_profile` + optional delegate) |
| `src/volta/ops/_schema_pcb.py` | MODIFY | +35 (`BuildHandoffExportOp`) |
| `src/volta/ops/schema.py` | MODIFY | +3 (import, union, `__all__`) |
| `src/volta/ops/registry.py` | MODIFY | +10 (`_RAW_CATALOG` entry) |
| `src/volta/ops/handlers/build.py` | MODIFY | +40 (`_handle_build_handoff_export`) |
| `tests/test_handoff.py` | CREATE | ~200-300 |
| `tests/test_registry.py` | MODIFY | count 159→160, +1 readonly entry |

**Files NOT modified** (verified by research): `ops/handlers/__init__.py` (merge already handles it), `ops/execution.py` (build ops are single_file, NOT CROSS_FILE).

## PLANNING COMPLETE
