bretbouchard/kicad-agent/.planning/phases/250-portable-build-setup/250-01-PLAN.md

# Phase 250: Portable build setup (adapter resolution + first-run script)

**Status:** Planned (2026-07-14)
**Priority:** P1
**Effort:** Small-medium (~4-8 hours)
**Plans:** TBD via /gsd-plan-phase 250

## Goal

Make `volta` buildable on any machine (Bret's Mac mini, a fresh CI runner, a teammate's laptop) — not just the machine that has `/Volumes/Storage` mounted with the canonical adapter at a specific path. Add a `scripts/setup_local.py` (or shell equivalent) that detects, resolves, or downloads the canonical Volta v2 adapter, then creates the symlink + verifies the build environment.

## Why

User flagged 2026-07-14: "we don't want this to just work on my computer we need this to build properly". The `volta-12b-v2` symlink is currently hard-coded to `/Volumes/Storage/models/volta/adapters/kicad-vision-v2`. This breaks on:
- Fresh CI runners (no /Volumes/Storage)
- Teammate machines (different mount point or no Storage at all)
- Bret's laptop vs Mac mini (different paths)
- Anyone running `git clone` + `make test`

## Problem Statement

Three portability issues identified during Phase 246/248 work:

1. **Adapter path is hard-coded** — `volta/volta-12b-v2` symlink points to an absolute Storage path
2. **Adapter name divergence** — Storage has `kicad-vision-v2` (legacy name), app expects `volta-pcb-adapter-v2` (HF name)
3. **Build env is implicit** — No first-run script checks Python version, kicad-cli presence, base model availability

## Requirements

- **REQ-250-01:** `scripts/setup_local.py` creates the `volta-12b-v2` symlink at repo root, pointing to whichever local copy of the adapter is resolvable
- **REQ-250-02:** Setup script searches known locations in order: `/Volumes/Storage/models/volta/adapters/kicad-vision-v2` → `~/.cache/huggingface/hub/models--bretbouchard--volta-pcb-adapter-v2/` → local fallback
- **REQ-250-03:** If no local copy found, setup script offers to download from `bretbouchard/volta-pcb-adapter-v2` on HuggingFace
- **REQ-250-04:** Setup script verifies Python 3.11+, kicad-cli 10.0.1, base model `gemma-4-12b-it` availability
- **REQ-250-05:** `.gitignore` excludes the machine-local symlink (`/volta-12b-v2`) — added 2026-07-14
- **REQ-250-06:** Setup script is idempotent
- **REQ-250-07:** Setup script exits non-zero with clear error message if prerequisites missing
- **REQ-250-08:** CLAUDE.md `## Tool Inventory` section documents `scripts/setup_local.py` as the first-run command
- **REQ-250-09:** `bootstrap-project` skill integration — `/bootstrap-project` calls `setup_local.py` as part of its workflow

## Key Work

### 1. Setup script (`scripts/setup_local.py`)

```python
# Pseudocode (TDD-first)
def main():
    # 1. Check Python version (>= 3.11)
    # 2. Search for canonical adapter in known locations
    adapter = find_local_adapter()  # Storage → HF cache → local
    if not adapter:
        if user_consents_to_download():
            adapter = download_from_hf()  # bretbouchard/volta-pcb-adapter-v2
    if not adapter:
        sys.exit("ERROR: No adapter found and download declined")
    # 3. Create / verify symlink at <repo>/volta-12b-v2
    create_symlink(target=adapter, linkpath=Path.cwd() / "volta-12b-v2")
    # 4. Verify kicad-cli 10.0.1
    check_kicad_cli()
    # 5. Verify base model (gemma-4-12b-it) available
    check_base_model()
    # 6. Print summary
    print("Build environment ready. Adapter:", adapter)
```

### 2. Tests (`scripts/test_setup_local.py`)

- `test_find_local_adapter_prefers_storage`
- `test_find_local_adapter_falls_back_to_hf_cache`
- `test_create_symlink_idempotent`
- `test_create_symlink_creates_parent_dir`
- `test_check_kicad_cli_version_10_or_higher`
- `test_check_kicad_cli_missing_exits_nonzero`
- `test_check_python_version_minimum_3_11`
- `test_full_setup_happy_path` (integration)

### 3. .gitignore (DONE 2026-07-14)

```gitignore
# Machine-local symlink to canonical Volta v2 adapter (created by setup script)
# See .planning/phases/250-portable-build-setup/ for portability phase
/volta-12b-v2
```

### 4. Documentation

- `CLAUDE.md` — Add `scripts/setup_local.py` to Tool Inventory, note as first-run command
- `README.md` — Add "First-time setup" section: clone → `python3 scripts/setup_local.py` → `swift test --no-parallel`
- `scripts/setup_local.py --help` — Self-documenting

### 5. bootstrap-project skill integration

- `.claude/skills/bootstrap-project/SKILL.md` — Add step: "Run setup_local.py to configure adapter symlink"

## Out of Scope (deferred to other phases)

- Multi-adapter support (v3, ios-4b) — add when those exist as installable
- Adapter versioning / upgrade flow — add if multiple HF releases
- Automated CI setup — separate CI/ops concern
- Storage mount helper (auto-mount /Volumes/Storage) — system admin

## Files Touched

- `scripts/setup_local.py` (new)
- `scripts/test_setup_local.py` (new)
- `.gitignore` (already updated)
- `CLAUDE.md` (add setup script to Tool Inventory)
- `README.md` (add First-time setup section)
- `.claude/skills/bootstrap-project/SKILL.md` (add setup step)

## Success Criteria

1. Fresh `git clone` on a new machine → `python3 scripts/setup_local.py` → symlink created, build environment ready
2. Running setup script twice produces no errors (idempotent)
3. Setup script refuses to proceed if Python < 3.11 with clear error
4. Setup script downloads adapter from HF when prompted, with progress feedback
5. All `scripts/test_setup_local.py` tests pass
6. `swift test --no-parallel` still passes after setup (no regression)
7. `python3 -m pytest` still passes (no regression)
8. CI workflow can call `python3 scripts/setup_local.py --ci-mode` (non-interactive)

## Risks

- **Low:** Setup script is additive (doesn't break existing builds)
- **Low:** Symlink behavior is well-understood
- **Medium:** HF download could be slow (5-10 min for 921M adapter) — show progress
- **Medium:** HuggingFace auth — need to handle token-required downloads gracefully

## Dependencies

- Phase 248 (volta-12b-v2 naming reconcile) must complete first — establishes canonical path
- `huggingface_hub` Python package (already in deps)
- `kicad-cli` 10.0.1+ (external, must be installed)

## Notes

This phase is small but high-leverage. The setup script is the foundation for:
- Phase 249 (volta → Volta rename) — can rename symlink target
- Future CI setup
- Onboarding new developers
- Running eval harness on remote GPU instances
