bretbouchard/kicad-agent/.planning/phases/203-build-and-ship-automation-fastlane/203-01-PLAN.md

# Phase 203: Build & Ship Automation (Fastlane)

**Phase Number:** 203
**Track:** H — Quality (parallel-executable from Phase 161)
**Plan:** 203-01
**Wave:** 1 (parallel with Foundation)
**Status:** Planning
**Last Updated:** 2026-07-07

## Goal

Establish Fastlane as the single build/test/sign/ship pipeline for the entire v6.0 Mac+iPhone app. Every CI workflow invokes Fastlane lanes — no bespoke xcodebuild shell scripts, no manual Xcode archives, no App Store Connect web UI clicks. Unified `build_daemon` lane orchestrates the PyInstaller binary alongside Swift builds.

## Requirements Addressed

- **TEST-13**: All build/archive/sign/test/ship via Fastlane
- **TEST-14**: Code signing via Fastlane match
- **TEST-15**: TestFlight via Fastlane pilot
- **TEST-16**: App Store submission via Fastlane deliver
- **TEST-17**: Pre-submission validation via Fastlane precheck
- **TEST-18**: PyInstaller binary via Fastlane `build_daemon` lane

## Stupid-Proof Verification

**User-stupid (guardrails):**
- Code signing failures (most common ship-blocker) eliminated — `match` syncs certs automatically
- App Store rejection risks caught in CI via `precheck`, never at submission
- Beta builds always come from main branch (no debug builds shipped)
- All submissions reproducible from git SHA — no "works on my machine"

**Magic-stupid (zero friction):**
- One command ships TestFlight: `fastlane beta`
- One command submits App Store: `fastlane release`
- Code signing invisible — no provisioning profile juggling
- Screenshots auto-generated for all device sizes + languages via `snapshot`

## Dependencies

**Depends on:**
- None — can start in parallel with Phase 161 (Foundation). Needs Phase 162 (Python Daemon Bundling) to fully wire `build_daemon` lane.

**Enables:**
- Phase 200 (CI Coverage Gates) — CI workflows invoke Fastlane lanes
- All TestFlight beta distribution
- App Store submission

## Tasks

### Task 1: Fastlane Project Setup

**Files to create:**
- `fastlane/Fastfile` — lane definitions
- `fastlane/Appfile` — app identifiers, bundle IDs
- `fastlane/Matchfile` — code signing repo config
- `fastlane/Snapfile` — screenshot automation config
- `fastlane/Deliverfile` — App Store submission metadata
- `fastlane/Pluginfile` — optional plugins
- `fastlane/metadata/` — App Store metadata (en-US, descriptions, keywords)
- `fastlane/screenshots/en-US/` — captured screenshots
- `fastlane/report.xml` (generated, gitignored)
- `fastlane/README.md` — usage documentation
- `.env` (gitignored, optional — Fastlane env vars)
- `.fastlane/` (gitignored — credentials cache)

**Appfile content:**
```ruby
app_identifier("com.bretbouchard.volta")  # macOS app
app_identifier("com.bretbouchard.volta.iphone")  # iPhone companion
apple_id(ENV["APPLE_ID"])
team_id(ENV["TEAM_ID"])
itc_team_id(ENV["ITC_TEAM_ID"])
```

**Fastfile lanes (initial):**
```ruby
default_platform(:mac)

platform :mac do
  desc "Build the macOS app (debug)"
  lane :build do
    build_mac_app(
      project: "Volta.xcodeproj",
      scheme: "Volta-macOS"
    )
  end
  
  desc "Build + run tests + check coverage"
  lane :test do
    scan(
      project: "Volta.xcodeproj",
      scheme: "Volta-macOS",
      code_coverage: true,
      output_types: "junit,xcresult",
      clean: true
    )
  end
  
  desc "Build PyInstaller daemon binary"
  lane :build_daemon do
    Dir.chdir("../daemon") do
      sh("pyinstaller --noconfirm volta-daemon.spec")
    end
  end
  
  desc "Build everything (daemon + app)"
  lane :build_all do
    build_daemon
    build
  end
  
  desc "Ship to TestFlight"
  lane :beta do
    build_all
    match(type: "appstore", platform: "macos")
    pilot(
      app_identifier: "com.bretbouchard.volta",
      skip_waiting_for_build_processing: true,
      notify_external_testers: true
    )
  end
  
  desc "Submit to App Store"
  lane :release do
    precheck
    deliver(
      app_identifier: "com.bretbouchard.volta",
      submit_for_review: true,
      automatic_release: true,
      force: true  # skip HTML report verification
    )
  end
  
  desc "Generate screenshots via snapshot"
  lane :screenshots do
    snapshot(
      project: "Volta.xcodeproj",
      scheme: "Volta-macOS-UITests",
      devices: ["Mac"]
    )
  end
end

platform :ios do
  desc "Build iPhone companion"
  lane :build_iphone do
    build_ios_app(
      project: "Volta.xcodeproj",
      scheme: "Volta-iOS"
    )
  end
  
  desc "Ship iPhone to TestFlight"
  lane :beta_iphone do
    build_iphone
    match(type: "appstore", platform: "ios")
    pilot(
      app_identifier: "com.bretbouchard.volta.iphone"
    )
  end
end
```

**Acceptance Criteria:**
- [ ] `fastlane build` produces a signed macOS .app in `~/Library/Developer/Xcode/Archives/`
- [ ] `fastlane test` runs all unit + UI tests, outputs JUnit XML
- [ ] `fastlane build_daemon` produces PyInstaller binary in `daemon/dist/`
- [ ] `fastlane build_all` runs both daemon and app builds sequentially
- [ ] `fastlane screenshots` captures all 4-variant snapshots via XCUITest
- [ ] Fastfile committed, no secrets in repo

### Task 2: Code Signing via match

**Matchfile:**
```ruby
git_url("git@github.com:bretbouchard/certificates.git")
git_branch("master")
storage_mode("git")
type("appstore")  # default, overridden per-lane
app_identifier([
  "com.bretbouchard.volta",
  "com.bretbouchard.volta.iphone"
])
username(ENV["APPLE_ID"])
```

**Setup steps:**
1. Create private GitHub repo `bretbouchard/certificates` (or use existing)
2. Run `fastlane match appstore` to generate certs + profiles (first-time only)
3. Run `fastlane match development` for dev signing
4. Add Apple ID + Team ID to `.env`:
   ```
   APPLE_ID=bret@example.com
   TEAM_ID=ABC123DEF
   ITC_TEAM_ID=987654
   ```
5. Add `MATCH_PASSWORD` to GitHub Secrets (CI uses this to decrypt cert repo)

**Fastlane match nuke (recovery option):**
- `fastlane match nuke appstore` — revoke all certs, recreate (emergency only)
- Document in README when to use

**Acceptance Criteria:**
- [ ] `match appstore` succeeds on clean machine with repo access
- [ ] `match development` succeeds on all developer Macs
- [ ] CI workflow uses `MATCH_PASSWORD` from secrets to decrypt
- [ ] No `.p12` or `.mobileprovision` files tracked in app repo
- [ ] Match repo encrypted at rest (Fastlane handles via openssl)

### Task 3: TestFlight Distribution via pilot

**pilot configuration (in Fastfile):**
```ruby
lane :beta do
  # ... build_all ...
  pilot(
    app_identifier: "com.bretbouchard.volta",
    skip_waiting_for_build_processing: true,
    notify_external_testers: true,
    distribute_external: true,
    changelog: last_git_commit_message,
    testers_file: "fastlane/TestflightTesters.csv"
  )
end
```

**TestflightTesters.csv:**
```csv
First Name,Last Name,Email
Bret,Bouchard,bret@example.com
```

**CI integration (GitHub Actions workflow):**
```yaml
# .github/workflows/testflight.yml
name: TestFlight Beta
on:
  push:
    branches: [main]
jobs:
  beta:
    runs-on: macos-latest
    steps:
      - uses: actions/checkout@v4
      - name: Setup Fastlane
        run: brew install fastlane
      - name: Cache Pods
        uses: actions/cache@v3
        with:
          path: Pods
          key: ${{ runner.os }}-pods-${{ hashFiles('**/Podfile.lock') }}
      - name: Decrypt secrets
        run: |
          echo "${{ secrets.MATCH_REPO_DEPLOY_KEY }}" > /tmp/match_key
          chmod 600 /tmp/match_key
          export GIT_SSH_COMMAND="ssh -i /tmp/match_key"
      - name: Fastlane beta
        env:
          APPLE_ID: ${{ secrets.APPLE_ID }}
          TEAM_ID: ${{ secrets.TEAM_ID }}
          FASTLANE_PASSWORD: ${{ secrets.FASTLANE_PASSWORD }}
          MATCH_PASSWORD: ${{ secrets.MATCH_PASSWORD }}
        run: fastlane beta
```

**Acceptance Criteria:**
- [ ] Every merge to main triggers TestFlight build automatically
- [ ] External testers notified via email within 30 minutes of build processing
- [ ] Build changelog auto-pulled from last git commit message
- [ ] Failed TestFlight uploads alert via Slack/email (or PR check fails)

### Task 4: App Store Submission via deliver

**Deliverfile:**
```ruby
app_identifier("com.bretbouchard.volta")
username(ENV["APPLE_ID"])
submit_for_review(true)
automatic_release(true)
force(true)  # skip HTML report
precheck_include_in_app_purchases(false)

# Metadata files in fastlane/metadata/
# - name.txt
# - subtitle.txt
# - description.txt
# - keywords.txt
# - release_notes.txt
# - support_url.txt
# - marketing_url.txt
# - privacy_url.txt
# - apple_tv_privacy_policy.txt (if applicable)
```

**Submission lane:**
```ruby
lane :release do
  precheck  # catches rejection risks
  deliver(
    app_identifier: "com.bretbouchard.volta",
    metadata_path: "fastlane/metadata",
    screenshots_path: "fastlane/screenshots",
    submit_for_review: true,
    automatic_release: true,
    phased_release: true  # rollout over 7 days
  )
end
```

**Precheck validation list (built-in):**
- ✅ No dummy text in metadata
- ✅ All required fields populated
- ✅ Screenshots meet size requirements
- ✅ App uses allowed URLs only
- ✅ No negative user reviews blockers
- ✅ No reproducible crashes in latest build

**Acceptance Criteria:**
- [ ] `fastlane release` submits the app end-to-end
- [ ] `precheck` runs first, fails fast on rejection risks
- [ ] Phased release enabled (7-day rollout by default)
- [ ] Submit status visible via `fastlane deliver --status`

### Task 5: Snapshot Automation (UI screenshots for App Store)

**Snapfile:**
```ruby
devices([
  "Mac",
  "iPhone 16 Pro",
  "iPhone 16 Pro Max",
  "iPad Pro 12.9"
])

languages([
  "en-US"
])

scheme("Volta-UITests")
output_directory("./fastlane/screenshots")
clear_previous_screenshots(true)
override_status_bar(true)
reinstall_app(true)
dark_mode(true)  # capture both light + dark

# Override screenshots per language
override_status_bar(false)  # iOS only
```

**UITest target for snapshot capture:**
```swift
// Volta-UITests/SnapshotTests.swift
import XCTest

final class SnapshotTests: XCTestCase {
  func testCaptureScreenshots() {
    let app = XCUIApplication()
    app.launchArguments += ["-uiTestMode", "screenshots"]
    app.launch()
    
    // Capture main chat view
    snapshot("01-Chat-Empty")
    
    // Simulate a design conversation
    app.textFields["message-input"].tap()
    app.textFields["message-input"].typeText("Design a distortion pedal for bass")
    app.buttons["send"].tap()
    
    // Wait for response
    let response = app.staticTexts["assistant-response"]
    XCTAssertTrue(response.waitForExistence(timeout: 15))
    
    snapshot("02-Chat-With-Schematic")
    
    // Navigate to Decision Timeline
    app.buttons["timeline-tab"].tap()
    snapshot("03-Decision-Timeline")
    
    // Family Tree
    app.buttons["family-tree-tab"].tap()
    snapshot("04-Family-Tree")
  }
}
```

**Acceptance Criteria:**
- [ ] `fastlane screenshots` generates 4-variant screenshots per device per language
- [ ] Screenshots auto-uploaded with `deliver`
- [ ] Snapshot tests are part of TEST-03 (4-variant snapshot tests per view)
- [ ] Dark + light mode both captured

### Task 6: CI Integration with Xcode Cloud (alternative)

**Xcode Cloud workflow (if using Xcode Cloud instead of GitHub Actions):**
- Connect Xcode project to Xcode Cloud
- Workflow: On push to main → build → test → archive → TestFlight
- Custom CI script (`ci_scripts/ci_post_clone.sh`):
  ```bash
  #!/bin/sh
  brew install fastlane
  cd $CI_PRIMARY_REPOSITORY_PATH
  fastlane beta
  ```

**Acceptance Criteria:**
- [ ] Xcode Cloud workflow configured OR GitHub Actions workflow committed
- [ ] CI uses Fastlane (no bespoke xcodebuild commands)
- [ ] Build artifacts (ipa/pkg) uploaded as artifacts
- [ ] Failed builds block PR merge

## Files Modified/Created

| File | Purpose |
|---|---|
| `fastlane/Fastfile` | Lane definitions (build, test, beta, release) |
| `fastlane/Appfile` | App identifiers, bundle IDs |
| `fastlane/Matchfile` | Code signing repo config |
| `fastlane/Snapfile` | Screenshot automation |
| `fastlane/Deliverfile` | App Store submission config |
| `fastlane/metadata/*.txt` | App Store metadata (name, description, keywords) |
| `fastlane/TestflightTesters.csv` | Beta tester roster |
| `fastlane/README.md` | Usage docs |
| `.env` (gitignored) | APPLE_ID, TEAM_ID, secrets |
| `.github/workflows/testflight.yml` | TestFlight CI workflow |
| `.github/workflows/release.yml` | App Store submission CI workflow |
| `Volta.xcodeproj` | UITests target for snapshot automation |
| `Volta-UITests/SnapshotTests.swift` | XCUITest capturing App Store screenshots |
| `daemon/volta-daemon.spec` (PyInstaller) | Referenced by `build_daemon` lane |

## Test Strategy

### Verification Gates

**Pre-merge (every PR):**
- `fastlane test` runs unit + UI tests
- `fastlane precheck` validates metadata
- Code coverage gate (100% per TEST-02)

**Pre-release (manual trigger):**
- `fastlane beta` ships to TestFlight
- `fastlane release` submits to App Store

### Success Criteria

1. `fastlane build` succeeds on clean machine (no manual Xcode setup)
2. `fastlane test` reports pass to JUnit + xcresult
3. `fastlane beta` uploads to TestFlight, testers notified within 30 min
4. `fastlane screenshots` produces all 4-variant images per device
5. `fastlane release` submits to App Store end-to-end
6. CI workflow runs `fastlane test` on every PR, blocks merge on failure
7. No manual Xcode Archive/Organizer clicks needed for any release
8. `match` syncs certs to any new developer Mac in under 5 minutes

## Threat Model

### Trust Boundaries

| Boundary | Description |
|---|---|
| CI Runner → Match Repo | Semi-trusted (CI has deploy key, repo is encrypted) |
| CI → App Store Connect | Trusted (API key scoped to single app) |
| CI → TestFlight | Semi-trusted (internal testers only pre-release) |
| Local Dev → Match Repo | Trusted (developers have deploy keys) |

### STRIDE Threat Register

| Threat ID | Category | Component | Disposition | Mitigation Plan |
|---|---|---|---|---|
| T-203-01 | Spoofing | Match repo compromise | mitigate | Encrypt at rest via openssl, multi-party access (2+ deployers), branch protection requires review, signed commits enforced |
| T-203-02 | Tampering | CI secret leak | mitigate | Scoped API keys (App Store Connect only, no GitHub repo perms), rotate annually via `match nuke`, GitHub Secrets with 2-person approval, audit log review |
| T-203-03 | Repudiation | Build provenance | mitigate | Git SHA embedded in app version, Fastlane logs commit hash, all builds reproducible from source |
| T-203-04 | Information Disclosure | TestFlight build leak | mitigate | Internal testers only pre-release, TestFlight CSV roster pinned per pilot, external testers require approval, changelog sanitized |
| T-203-05 | Denial of Service | Malicious PR triggers release | mitigate | Required reviews + signed commits for main branch, workflow_dispatch only (no auto-release on push), `precheck` catches rejection risks |
| T-203-06 | Elevation of Privilege | PyInstaller arbitrary code | mitigate | `build_daemon` lane verifies .spec file changes, no unchecked subprocess exec, PyInstaller binary path validated, code signature verification |
| T-203-07 | Elevation of Privilege | Fastlane credential compromise | mitigate | Least-privilege API keys (App Store Connect only), no GitHub repo write access, rotate on employee offboard, audit log monitoring |

### Adversarial Scenario

**Name:** "CI credential theft via malicious PR"

**Scenario:** Attacker submits malicious PR that:
- Modifies `.github/workflows/testflight.yml` to exfiltrate `MATCH_PASSWORD`
- Adds Fastlane lane to upload PyInstaller binary to external server
- Alters `deliver` lane to submit to TestFlight with malicious metadata

**Attack vector:** If PR merges to main, CI workflow runs with elevated credentials, exfiltrates secrets, ships malicious build.

**Mitigation:**
1. Branch protection: Main branch requires 2 reviewers + signed commits (SPOOFING)
2. Workflow audit: PR modifies `.github/workflows/` → auto-block, required admin review (EOP)
3. Secret scoping: `MATCH_PASSWORD` only available to `testflight.yml`, not other workflows (TAMPERING)
4. Binary validation: `build_daemon` lane verifies PyInstaller binary signature before upload (EOP)
5. Pre-check gate: `precheck` runs before `deliver`, catches metadata tampering (REPUDIATION)

All mitigation layers must fail before attacker succeeds. Defense-in-depth prevents single-point compromise.

## Risks & Mitigations

| Risk | Mitigation |
|---|---|
| Match repo access lost (locked out of signing) | Multiple team members have deploy keys; backup passphrase in 1Password |
| Fastlane version drift | Pin Fastlane version in Gemfile (Bundler) |
| App Store API rate limits | Use App Store Connect API key (not Apple ID login) for CI |
| PyInstaller + Fastlane mismatch | `build_daemon` lane verifies binary exists before Swift build |
| Snapshot test flakiness | Frozen time fixtures (TEST-03 augmentation), retry with backoff |
| TestFlight processing delays (Apple side) | `skip_waiting_for_build_processing: true` — testers notified when ready |

## Dependencies on Other Phases

| Phase | Why |
|---|---|
| **161** (App Shell) | Needs .xcodeproj to exist before Fastlane can build |
| **162** (Python Daemon) | Needs PyInstaller .spec file before `build_daemon` lane works |
| **192** (Snapshot Testing) | Snapshot tests via Fastlane `snapshot` command |
| **200** (CI Coverage Gates) | CI workflows invoke Fastlane lanes |

## Implementation Notes

- **Run this phase in PARALLEL with Foundation** — Fastlane setup doesn't depend on any specific feature work
- Start with Task 1 (Fastfile skeleton) as soon as Phase 161 creates the .xcodeproj
- Code signing (Task 2) can be set up before any features work
- TestFlight distribution requires a real build — initially use a "Hello World" build to verify the lane works end-to-end before features land
- App Store metadata (Task 4) can be drafted in parallel; refined as features ship

## Verification

- [ ] `fastlane --version` reports ≥ 2.225 (latest stable)
- [ ] `bundle exec fastlane test` runs all tests in CI
- [ ] `bundle exec fastlane beta` ships TestFlight build from main
- [ ] `bundle exec fastlane release` submits to App Store (sandboxed test first)
- [ ] All Apple Developer Program resources (certs, profiles, identifiers) managed via `match`
- [ ] No `.p12`, `.cer`, or `.mobileprovision` files committed to repo
- [ ] CI uses App Store Connect API key (`APP_STORE_CONNECT_API_KEY`), not Apple ID password

---

**Estimated effort:** 1 week (3 days setup, 2 days CI integration + testing)

**Critical path:** NONE — this phase runs in parallel with everything else

**Next steps:** Execute as soon as Phase 161 (App Shell) creates the .xcodeproj. Don't wait for features to land.
