bretbouchard/kicad-agent/.planning/phases/191-swift-testing-framework/191-01-PLAN.md

---
phase: 191-swift-testing-framework
plan: 01
type: execute
wave: 1
depends_on: []
files_modified: [Package.swift, .github/workflows/ci.yml, Tests/UnitTests/VoltaTests.swift, Tests/UnitTests/Coverage/XCResult.swift]
autonomous: true
requirements: [TEST-01, TEST-02]
user_setup: []
must_haves:
  truths:
    - All new Swift code uses swift-testing framework (not XCTest)
    - 100% line + branch coverage enforced in CI (build fails if below)
    - Coverage reports generated per PR with diff coverage
    - Tests cover all UI views, models, providers, daemon communication
  artifacts:
    - path: Package.swift
      provides: Swift package dependencies including swift-testing
      contains: swift-testing package reference
    - path: .github/workflows/ci.yml
      provides: CI workflow with coverage gates
      exports: coverage enforcement steps
    - path: Tests/UnitTests/VoltaTests.swift
      provides: Example swift-testing tests
      min_lines: 50
  key_links:
    - from: Tests/UnitTests
      to: swift-testing
      via: @Test import
      pattern: import Testing
    - from: .github/workflows/ci.yml
      to: coverage report
      via: coverage threshold enforcement
      pattern: coverage.*100%
---

<objective>
Establish swift-testing framework as the standard for all new Swift code with 100% line+branch coverage enforced in CI. XCTest reserved only for legacy XCUITest.

Purpose: swift-testing provides modern testing APIs (@Test macros, parameterized tests, parallel execution) replacing legacy XCTest. 100% coverage enforced via CI gate prevents code ship-ment without tests.

Output: Package.swift with swift-testing dependency, CI workflow with coverage enforcement blocking builds below 100%, example test suite demonstrating @Test usage, coverage report artifact per PR.
</objective>

<execution_context>
@$HOME/.claude/get-shit-done/workflows/execute-plan.md
@$HOME/.claude/get-shit-done/templates/summary.md
</execution_context>

<context>
@.planning/PROJECT.md
@.planning/ROADMAP.md
@.planning/STATE.md
@.planning/research/v6/STACK.md
@.planning/research/v6/ARCHITECTURE.md
</context>

<interfaces>
<!-- Swift package dependencies from STACK.md -->
From .planning/research/v6/STACK.md:
```swift
// Package.swift testing dependencies
.package(url: "https://github.com/swiftlang/swift-testing", from: "0.10.0")

// swift-testing imports
import Testing
@Test
@Suite
```
</interfaces>

<tasks>

<task type="auto">
  <name>Task 1: Add swift-testing dependency to Package.swift</name>
  <files>Package.swift</files>
  <action>Add swift-testing package to Package.swift dependencies:
```swift
dependencies: [
  .package(url: "https://github.com/swiftlang/swift-testing", from: "0.10.0")
]
```
Also add to target dependencies:
```swift
.target(
  name: "VoltaApp",
  dependencies: [
    .product(name: "Testing", package: "swift-testing")
  ]
)
```
And test target:
```swift
.testTarget(
  name: "VoltaTests",
  dependencies: [
    .target(name: "VoltaApp"),
    .product(name: "Testing", package: "swift-testing")
  ]
)
```
Per STACK.md swift-6.3.2-RELEASE research.</action>
  <verify>swift package resolve completes without errors</verify>
  <done>swift-testing package added to dependencies, test target configured with Testing product</done>
</task>

<task type="auto" tdd="true">
  <name>Task 2: Create example swift-testing suite</name>
  <files>Tests/UnitTests/VoltaTests.swift</files>
  <behavior>
    - Test 1: Example @Test macro usage with basic assertion
    - Test 2: Example @Suite with multiple tests
    - Test 3: Parameterized test example
  </behavior>
  <action>Create Tests/UnitTests/VoltaTests.swift with swift-testing examples:
```swift
import Testing
@testable import VoltaApp

@Suite("Volta Tests")
struct VoltaTests {
    @Test("example test passes")
    func exampleTest() {
        #expect(1 + 1 == 2)
    }
    
    @Test("string concatenation works")
    func stringTest() {
        let greeting = "Hello"
        #expect(greeting + " World" == "Hello World")
    }
}
```
This demonstrates swift-testing APIs per TEST-01 requirement (swift-testing, not XCTest).</action>
  <verify>swift test --parallel runs without errors, all tests pass</verify>
  <done>Example test suite created using @Test macro, swift-test command runs successfully</done>
</task>

<task type="auto">
  <name>Task 3: Configure CI coverage gate with 100% enforcement</name>
  <files>.github/workflows/ci.yml</files>
  <action>Create .github/workflows/ci.yml with swift-testing and coverage enforcement:
```yaml
name: CI
on: [push, pull_request]

jobs:
  test:
    runs-on: macos-26
    steps:
      - uses: actions/checkout@v4
      - name: Run tests with coverage
        run: swift test --enable-code-coverage
      - name: Generate coverage report
        run: xcrun llvm-cov report --instr-profile=.build/debug/codecov/*.profdata --ignore-filename-regex=Tests/.* .build/debug/VoltaApp*.swift
      - name: Enforce 100% coverage
        run: |
          COVERAGE=$(xcrun llvm-cov report --instr-profile=.build/debug/codecov/*.profdata .build/debug/VoltaApp*.swift | grep "Total" | awk '{print $NF}' | sed 's/%//')
          if (( $(echo "$COVERAGE < 100" | bc -l) )); then
            echo "Coverage $COVERAGE% is below 100%"
            exit 1
          fi
```
This enforces TEST-02 requirement (build fails if coverage below 100%). Uses macOS 26 for FoundationModels availability.</action>
  <verify>gh workflow view ci shows workflow file, coverage threshold enforced at 100%</verify>
  <done>CI workflow created with swift-testing execution, coverage generation, and 100% threshold enforcement blocking builds below threshold</done>
</task>

</tasks>

<threat_model>
## STRIDE Threat Register

| Threat ID | Category | Component | Disposition | Mitigation Plan |
|---|---|---|---|---|
| T-191-01 | T | CI coverage gate | mitigate | Use GitHub Actions hardened runner, pin workflow actions to SHAs, validate coverage calculation logic to prevent bypass via percentage manipulation |
| T-191-02 | I | Package.swift dependencies | mitigate | Pin swift-testing to exact version, verify checksums, use SPM audit mode to detect supply chain attacks |
| T-191-03 | D | Test code execution | mitigate | Run tests in sandboxed macOS 26 environment, no network access during test execution, file system writes confined to .build directory |
| T-191-04 | E | Coverage report artifacts | mitigate | Encrypt coverage reports stored as artifacts, sign with GitHub Actions key, verify integrity before parsing threshold values |
| T-191-05 | R | Test infrastructure rollback | accept | Swift Testing is Apple-first-party, minimal rollback risk. Version pinned in Package.swift. |

## Adversarial Scenario

An attacker attempts to bypass the 100% coverage gate by modifying the CI workflow to parse coverage output incorrectly (e.g., always return 100%). Mitigation: pin workflow action versions, require branch protection for CI workflow edits, add coverage report validation step that uses an independent calculation method (xcrun llvm-cov export JSON format parsed with jq). The dual-path validation makes bypass significantly harder.

</threat_model>

<verification>
1. swift package resolve completes without errors
2. swift test --parallel executes all tests successfully
3. CI workflow triggers on push/PR
4. Coverage report shows line + branch percentages
5. Build fails if coverage drops below 100%
6. Example tests demonstrate @Test and @Suite usage
</verification>

<success_criteria>
- swift-testing framework integrated into Package.swift
- CI workflow enforces 100% line+branch coverage (build fails below threshold)
- Example test suite created with swift-testing APIs (@Test, @Suite)
- Coverage reports generated per PR as CI artifacts
- All new code paths covered by tests (zero uncovered lines/branches)
</success_criteria>

<output>
After completion, create `.planning/phases/191-swift-testing-framework/191-01-SUMMARY.md`
</output>
