bretbouchard/kicad-agent/.planning/phases/198-concurrency-testing/198-01-PLAN.md

---
phase: 198-concurrency-testing
plan: 01
type: execute
wave: 1
depends_on: []
files_modified: [Tests/ConcurrencyTests/, VoltaApp/Daemon/, VoltaApp/Collaboration/]
autonomous: true
requirements: [TEST-10]
user_setup: []

must_haves:
  truths:
    - "ThreadSanitizer runs in CI for all tests (zero data races allowed)"
    - "Concurrency tests verify SwiftData thread safety (parallel reads/writes)"
    - "Concurrency tests verify daemon Process thread safety (spawn/kill/restart)"
    - "Concurrency tests verify Group Activities message ordering (no race conditions)"
    - "CI gate blocks merge if ThreadSanitizer detects any data race"
  artifacts:
    - path: "Tests/ConcurrencyTests/"
      provides: "Concurrency test suite with ThreadSanitizer integration"
      min_lines: 60
    - path: ".github/workflows/thread-sanitizer.yml"
      provides: "CI workflow running ThreadSanitizer on all tests"
      exports: ["thread_sanitizer_enabled", "fail_on_data_race"]
  key_links:
    - from: "Tests/ConcurrencyTests/"
      to: "VoltaApp/Daemon/"
      via: "ThreadSanitizer detects data races in Process lifecycle"
      pattern: "ThreadSanitizer.*data race.*DaemonMCPClient"
    - from: "Tests/ConcurrencyTests/"
      to: "VoltaApp/Collaboration/"
      via: "Group Activities message ordering verified under concurrency"
      pattern: "XCTContext.*runActivity.*concurrent.*GroupSessionMessenger"

---

<objective>
Build concurrency test suite with ThreadSanitizer integration. Verify SwiftData thread safety (parallel reads/writes), daemon Process thread safety (spawn/kill/restart), Group Activities message ordering (no race conditions). CI gate blocks merge if ThreadSanitizer detects any data race.

Purpose: Data races are silent corruption bugs. SwiftData concurrent writes cause undefined behavior. Daemon Process spawned/killed simultaneously crashes app. Group Activities message ordering scrambled under concurrency → collaborators see different conversation state. ThreadSanitizer detects races at runtime, catching bugs unit tests miss.

Output: Concurrency test suite with 20+ tests, ThreadSanitizer CI workflow, SwiftData parallel read/write tests, daemon Process race condition tests, Group Activities message ordering tests, zero data races in CI.
</objective>

<execution_context>
@$HOME/.claude/get-shit-done/workflows/execute-plan.md
@$HOME/.claude/get-shit-done/templates/summary.md
</execution_context>

<context>
@.planning/PROJECT.md
@.planning/ROADMAP.md
@.planning/research/v6/STACK.md
@.planning/research/v6/ARCHITECTURE.md
@.planning/research/v6/PITFALLS.md

# Key context for concurrency testing:
# - SwiftData uses thread-safe CloudKit sync but manual ModelContext access is not thread-safe by default
# - Process() spawning/killing requires explicit synchronization (NSConditionLock or DispatchQueue)
# - Group Activities messenger must handle out-of-order message arrival (version per message)
</context>

<tasks>

<task type="auto" tdd="true">
  <name>Task 1: Create ThreadSanitizer CI workflow and test infrastructure</name>
  <files>.github/workflows/thread-sanitizer.yml, Tests/ConcurrencyTests/ThreadSanitizerTests.swift</files>
  <behavior>
    - Test 1: ThreadSanitizer enabled in Xcode build settings
    - Test 2: CI workflow runs all tests with ThreadSanitizer
    - Test 3: Workflow fails if any data race detected
    - Test 4: ThreadSanitizer report uploaded as artifact for debugging
  </behavior>
  <action>Create thread-sanitizer.yml GitHub Actions workflow. Enable ThreadSanitizer via Xcode scheme: Thread Sanitizer = YES (build setting). Add env variable: TSAN_OPTIONS="suppressions=" (no suppressions, fail all races). Run swift test with ThreadSanitizer enabled. Upload ThreadSanitizer report (tsan_report.txt) as artifact on failure. Create ThreadSanitizerTests.swift with smoke test that spawns 2 threads accessing shared variable (verify TSan detects race).</action>
  <verify>gh workflow view thread-sanitizer && swift test --enable-thread-sanitizer --filter ThreadSanitizerTests</verify>
  <done>ThreadSanitizer CI workflow created, detects data races in smoke test, fails on any TSan report</done>
</task>

<task type="auto" tdd="true">
  <name>Task 2: Verify SwiftData thread safety with parallel read/write tests</name>
  <files>Tests/ConcurrencyTests/SwiftDataConcurrencyTests.swift</files>
  <behavior>
    - Test 1: 10 concurrent readers access same ModelContext (no crash)
    - Test 2: 10 concurrent writers insert decisions (no data corruption)
    - Test 3: Mixed read/write workload (10 readers + 10 writers) passes
    - Test 4: ThreadSanitizer detects no data races in SwiftData access
  </behavior>
  <action>Write SwiftDataConcurrencyTests.swift. Use SwiftData with main thread ModelContext. Test parallel reads: dispatch 10 concurrent tasks, each fetches Decision via FetchDescriptor, assert all succeed. Test parallel writes: dispatch 10 concurrent tasks, each inserts unique Decision, verify all 10 persisted. Test mixed workload: 10 readers + 10 writers, verify no deadlocks/crashes. Run with ThreadSanitizer enabled, assert zero data races.</action>
  <verify>swift test --enable-thread-sanitizer --filter SwiftDataConcurrencyTests</verify>
  <done>SwiftData concurrency tests pass with 10 parallel readers/writers, ThreadSanitizer zero races</done>
</task>

<task type="auto" tdd="true">
  <name>Task 3: Verify daemon Process thread safety with spawn/kill/restart tests</name>
  <files>Tests/ConcurrencyTests/DaemonProcessConcurrencyTests.swift, VoltaApp/Daemon/DaemonMCPClient.swift</files>
  <behavior>
    - Test 1: Concurrent spawn attempts (10 threads spawn same daemon) handled gracefully
    - Test 2: Concurrent kill attempts (10 threads kill same daemon) no crash
    - Test 3: Spawn-then-kill race (spawn thread races kill thread) detected
    - Test 4: ThreadSanitizer detects no data races in Process lifecycle
  </behavior>
  <action>Add NSConditionLock to DaemonMCPClient for spawn/kill synchronization. Write DaemonProcessConcurrencyTests.swift. Test concurrent spawn: dispatch 10 threads, each calls daemonClient.spawn(), verify only one daemon actually spawned (single-instance check). Test concurrent kill: spawn daemon, dispatch 10 threads to kill, verify all succeed, no crash. Test spawn-kill race: dispatch thread A to spawn, thread B to kill simultaneously, verify guard prevents use-after-free (if kill wins first, spawn waits; if spawn wins first, kill waits). Run with ThreadSanitizer.</action>
  <verify>swift test --enable-thread-sanitizer --filter DaemonProcessConcurrencyTests && lsof -p <daemon_pid> (verify single instance)</verify>
  <done>Daemon Process concurrency tests pass, NSConditionLock prevents race conditions, ThreadSanitizer zero races</done>
</task>

<task type="auto" tdd="true">
  <name>Task 4: Verify Group Activities message ordering under concurrency</name>
  <files>Tests/ConcurrencyTests/GroupActivitiesConcurrencyTests.swift, VoltaApp/Collaboration/GroupActivitiesSession.swift</files>
  <behavior>
    - Test 1: 10 concurrent messages from same participant arrive in order
    - Test 2: Messages from 4 concurrent participants interleaved correctly
    - Test 3: Out-of-order message handling (version per message) works
    - Test 4: ThreadSanitizer detects no data races in messenger
  </behavior>
  <action>Add versioning to GroupActivitiesSession messages. Write GroupActivitiesConcurrencyTests.swift. Test single-participant ordering: dispatch 10 concurrent broadcastDecision() calls from same participant, verify receiver applies in order (use incrementing counter). Test multi-participant: 4 threads each send 5 messages concurrently, verify all 20 received, order preserved per participant. Test out-of-order: send messages v3 before v2, verify messenger queues v3 until v2 processed (version queue). Run with ThreadSanitizer.</action>
  <verify>swift test --enable-thread-sanitizer --filter GroupActivitiesConcurrencyTests</verify>
  <done>Group Activities concurrency tests pass, message ordering preserved under load, ThreadSanitizer zero races</done>
</task>

<task type="auto" tdd="true">
  <name>Task 5: Add stress test with 100 concurrent operations</name>
  <files>Tests/ConcurrencyTests/ConcurrencyStressTests.swift</files>
  <behavior>
    - Test 1: 100 concurrent SwiftData reads/writes complete without crash
    - Test 2: 100 concurrent daemon spawn/kill cycles stable
    - Test 3: 100 concurrent Group Activities messages delivered correctly
    - Test 4: ThreadSanitizer zero races in stress test
  </behavior>
  <action>Write ConcurrencyStressTests.swift. Stress test SwiftData: 50 parallel reads + 50 parallel writes, assert all 100 succeed, verify data integrity (all 50 writes persisted). Stress test daemon: spawn/kill repeated 50 times concurrently, verify final state (daemon dead). Stress test Group Activities: 4 participants x 25 messages = 100 messages concurrent, verify all 100 delivered in correct order. Run with ThreadSanitizer. This is 5-minute stress test (CI timeout 10m).</action>
  <verify>swift test --enable-thread-sanitizer --filter ConcurrencyStressTests --timeout 10m</verify>
  <done>Concurrency stress test passes (100 ops), ThreadSanitizer zero races, all data integrity checks pass</done>
</task>

<task type="auto" tdd="true">
  <name>Task 6: Add ThreadSanitizer suppressions documentation (empty by default)</name>
  <files>Tests/ConcurrencyTests/THREAD_SANITIZER_SUPPRESSIONS.md</files>
  <behavior>
    - Test 1: Documentation lists why suppressions are discouraged
    - Test 2: Process for adding suppressions documented (requires security review)
    - Test 3: Current suppressions list empty (verify in CI)
    - Test 4: ThreadSanitizer report artifacts retained for 30 days
  </behavior>
  <action>Create THREAD_SANITIZER_SUPPRESSIONS.md documenting policy: suppressions discouraged (data races are bugs). If suppression absolutely required (e.g., third-party framework race), document: (1) Why race is safe (false positive), (2) Third-party library version, (3) Security review approval. Verify CI has zero suppressions: grep TSAN_OPTIONS workflow file, confirm no suppressions= entry. Configure GitHub Actions artifacts retention: 30-day retention for ThreadSanitizer reports. Document how to debug race from report artifact.</action>
  <verify>cat Tests/ConcurrencyTests/THREAD_SANITIZER_SUPPRESSIONS.md && gh api /repos/:owner/:repo/actions/artifacts | grep -i tsan</verify>
  <done>ThreadSanitizer suppressions policy documented, CI has zero suppressions, report artifacts retained 30 days</done>
</task>

</tasks>

<threat_model>
## Trust Boundaries

| Boundary | Description |
|---|---|
| Test Threads → Shared State | Concurrency tests deliberately create data races (test environment only) |
| ThreadSanitizer Report → CI Logs | Tampered report could hide races (CI integrity risk) |

## STRIDE Threat Register

| Threat ID | Category | Component | Disposition | Mitigation Plan |
|---|---|---|---|---|
| T-198-01 | T | False positive data race | mitigate | Review ThreadSanitizer report, verify race is real, fix code (no suppressions) |
| T-198-02 | R | CI workflow bypassed | mitigate | ThreadSanitizer required in main branch protection rules, bypass requires security review |
| T-198-03 | I | Suppressions file tampered | mitigate | Commit suppressions to git, PR review required for changes |
| T-198-04 | D | Test data corrupted by race | accept | Concurrency tests detect races, test data corruption is expected (test crashes) |
| T-198-05 | E | Third-party framework race | mitigate | Document suppression with third-party version, security review approves, reassess on upgrade |

## Adversarial Scenario

Name: Attacker submits PR with hidden data race disguised as optimization. Attacker adds code to DaemonMCPClient that unsafely accesses shared state without lock. Code compiles, unit tests pass (race only triggered under concurrency). PR claims "optimize daemon spawn latency" by removing lock.

Mitigation: CI thread-sanitizer.yml workflow runs all tests with ThreadSanitizer. DaemonProcessConcurrencyTests spawns 10 threads concurrently calling spawn(). ThreadSanitizer detects data race on shared state access. Workflow fails, report uploaded as artifact showing exact line. PR blocked, race visible in logs before merge.
</threat_model>

<verification>
- [ ] thread-sanitizer.yml CI workflow created
- [ ] ThreadSanitizer enabled in Xcode build settings
- [ ] ThreadSanitizerTests.swift smoke test detects intentional race
- [ ] SwiftDataConcurrencyTests.swift passes (10 parallel readers/writers)
- [ ] DaemonProcessConcurrencyTests.swift passes (spawn/kill races)
- [ ] GroupActivitiesConcurrencyTests.swift passes (message ordering)
- [ ] ConcurrencyStressTests.swift passes (100 concurrent ops)
- [ ] ThreadSanitizer zero data races in all tests
- [ ] THREAD_SANITIZER_SUPPRESSIONS.md documented, zero suppressions
- [ ] CI gate blocks merge on ThreadSanitizer failure
</verification>

<success_criteria>
- [ ] Concurrency test suite with 20+ tests
- [ ] ThreadSanitizer runs in CI on all tests (zero data race policy)
- [ ] SwiftData parallel read/write tests pass (no corruption)
- [ ] Daemon Process spawn/kill race conditions handled (NSConditionLock)
- [ ] Group Activities message ordering preserved under concurrency
- [ ] Stress test passes (100 concurrent operations)
- [ ] CI blocks merge if ThreadSanitizer detects any data race
- [ ] Zero suppressions (policy enforced)
</success_criteria>

<output>
After completion, create `.planning/phases/198-concurrency-testing/198-01-SUMMARY.md` with ThreadSanitizer report, concurrency test coverage, and CI gate configuration.
</output>
