bretbouchard/kicad-agent/.planning/phases/206-vendor-drc-profiles/206-VERIFICATION.md

---
phase: 206-vendor-drc-profiles
verified: 2026-07-10
status: passed
requirements: [DRC-01, DRC-02, DRC-03, DRC-04, DRC-05, DRC-06, DRC-07, DRC-08]
---

# Phase 206 Verification — Vendor DRC Profiles

**Phase goal:** User can run DRC against a specific vendor's manufacturing limits as a pre-flight gate, and the system ships verified `.kicad_dru` files for 5+ vendors.

**Result:** PASSED — all 8 requirements satisfied, all 10 must_haves verified, all 4 ROADMAP success criteria met, 86 phase tests green + 38 dfm_checker tests green.

## Per-Must-Have Verification

| # | Must_Have | Status | Evidence |
|---|---|---|---|
| 1 | 9 `.kicad_dru` files exist with attribution headers | ✓ | `ls src/volta/manufacturing/drc_profiles/*.kicad_dru` returns 9 files (pcbway, jlcpcb, aisler_2/4/6/8layer, oshpark, advanced_circuits, generic). Each file has `^# Source:` (count 1) and `^# Last verified:` (count 1). |
| 2 | `ManufacturerProfile` has `drc_rules_path` field | ✓ | `src/volta/dfm/profiles.py:57` — `drc_rules_path: Path \| None = Field(default=None, ...)`. Wired on all 10 profiles (9 DRU-backed + uses `get_drc_profile_path`). |
| 3 | PCBWay annular ring is 0.15mm (DRC-07) | ✓ | `load_profile('pcbway').min_annular_ring_mm == 0.15` confirmed. JLCPCB also 0.15. AISLER 0.2mm (hard limit). |
| 4 | Internal evaluator (`run_vendor_drc`) detects violations | ✓ | `manufacturing/vendor_drc.py` defines `run_vendor_drc(board, profile) -> VendorDrcResult`. Runs all 5 checks (track_width, drill_size, annular_ring, via_diameter, clearance). Silent-pass guard tests pass: `TestTrackWidthCheck::test_track_width_below_limit_violation` and `TestClearanceCheck::test_clearance_below_limit_violation` both assert `passed is False` + specific violation type. |
| 5 | `drc_vendor` op registered (count == 156) | ✓ | `len(OPERATION_REGISTRY) == 156`; `'drc_vendor' in OPERATION_REGISTRY`. |
| 6 | `list_vendor_drc_profiles` op registered | ✓ | `'list_vendor_drc_profiles' in OPERATION_REGISTRY`; both handlers in `_QUERY_HANDLERS`. |
| 7 | `validate_registry_completeness()` passes | ✓ | Returns 3 pre-existing missing ops only (`add_design_note`, `apply_floor_plan`, `place_and_wire_power_units`) — no new gaps introduced by Phase 206. |
| 8 | Handler uses `NativeParser.parse_pcb` (NOT `ir.board`) | ✓ | `src/volta/ops/handlers/query.py:107` — `board = NativeParser.parse_pcb(file_path)`. Handler comment explicitly documents the dual-path re-parse (same as Phase 205 pattern). |
| 9 | No `--custom-rules` invocation anywhere | ✓ | `grep -rn "custom-rules\|custom_rules" src/volta/` — only matches are comments/docstrings explaining the pivot (e.g. `vendor_drc.py:6` "has no `--custom-rules` flag"). Zero subprocess/cmd invocations. |
| 10 | Full test suite green for phase files | ✓ | 86 passed across `test_vendor_drc.py` + `test_drc_vendor_ops.py` + `test_drc_profiles.py` + `test_registry.py`. Plus 38 passed in modified `test_dfm_checker.py`. |

## Per-Requirement Verification

| Req ID | Requirement | Status | Evidence |
|---|---|---|---|
| DRC-01 | `drc_vendor` op runs vendor-specific DRC | ✓ | `Operation.model_validate({'op_type': 'drc_vendor', ..., 'vendor': 'pcbway'})` succeeds. Handler `_handle_drc_vendor` calls `run_vendor_drc`. `test_drc_vendor_ops.py` green. |
| DRC-02 | Ships `.kicad_dru` for PCBWay, JLCPCB, AISLER 2/4/6/8L | ✓ | All 6 files present + verified: `pcbway.kicad_dru`, `jlcpcb.kicad_dru`, `aisler_{2,4,6,8}layer.kicad_dru`. |
| DRC-03 | OSH Park + Advanced Circuits profiles authored from specs | ✓ | `oshpark.kicad_dru` + `advanced_circuits.kicad_dru` present with `# Source: Authored from published numeric specifications` headers. Both loadable via `load_profile()`. |
| DRC-04 | Generic conservative profile works | ✓ | `drc_vendor(vendor="generic")` schema-valid; `load_profile('generic')` resolves with `min_drill_mm=0.4`, `min_trace_width_mm=0.2`. |
| DRC-05 | `ManufacturerProfile.drc_rules_path` field | ✓ | Field defined at `profiles.py:57`; all 10 profiles wire it via `get_drc_profile_path(...)`. |
| DRC-06 | Attribution headers (source, license, last-verified) | ✓ | Every `.kicad_dru` has `# Source:`, `# License:`, `# Last verified:`, `# Vendor:`, `# Capabilities:` lines. Verified via grep (count 1 per file per header). |
| DRC-07 | PCBWay annular ring 0.15mm (not stale 0.25mm) | ✓ | `load_profile('pcbway').min_annular_ring_mm == 0.15`. JLCPCB also corrected to 0.15. |
| DRC-08 | `list_vendor_drc_profiles` lists profiles + capabilities | ✓ | Handler returns count=9; each entry has all capability fields (vendor, display_name, drc_rules_path, min_trace_width_mm, min_clearance_mm, min_drill_mm, min_annular_ring_mm, min_via_diameter_mm, supports_blind_vias, supports_castellated, source, last_verified). |

## ROADMAP Success Criteria

| # | Criterion | Status | Evidence |
|---|---|---|---|
| 1 | `drc_vendor(vendor="pcbway", file="board.kicad_pcb")` returns vendor-specific violations | ✓ | Op schema-valid; evaluator runs all 5 checks against PCBWay profile; `test_vendor_drc.py` proves violations detected. |
| 2 | 5+ verified vendor profiles with source attribution | ✓ | 9 profiles ship (PCBWay, JLCPCB, AISLER 2/4/6/8L, OSH Park, Advanced Circuits, generic) — each with `# Source:` + `# Last verified:` headers. |
| 3 | `drc_vendor(vendor="generic")` gives conservative results | ✓ | Schema accepts `vendor="generic"`; `load_profile("generic")` resolves conservative limits (0.2mm track, 0.4mm drill). |
| 4 | User can list profiles and see capabilities | ✓ | `list_vendor_drc_profiles` handler returns 9 profiles with full capability metadata. |

## Test Results

```
tests/test_vendor_drc.py + tests/test_drc_vendor_ops.py
  + tests/test_drc_profiles.py + tests/test_registry.py
=> 86 passed in 1.96s

tests/test_dfm_checker.py (modified by phase — annular + profile-count assertions)
=> 38 passed in 0.08s

Silent-pass guard tests (explicit re-run):
  TestTrackWidthCheck::test_track_width_below_limit_violation  PASSED
  TestClearanceCheck::test_clearance_below_limit_violation     PASSED
```

## Threat Model Verification

- **Scenario 1 (path traversal):** Blocked at two layers — schema pattern `^[a-z0-9_]+$` rejects `../../etc/passwd` with `ValidationError`; resolver `get_drc_profile_path()` re-validates pattern + checks `path.is_file()`.
- **Scenario 2 (malformed board):** Evaluator uses `getattr` + try/except per feature; `TestCleanBoardAndRobustness` tests pass (empty board + malformed geometry do not crash).

## Gaps Found

**None for Phase 206 scope.** All 8 requirements, all 10 must_haves, and all 4 success criteria verified.

### Notes (out of scope, not phase-blocking)

1. **REQUIREMENTS.md checkboxes unchecked.** All 8 DRC requirements still show `[ ]` in `REQUIREMENTS.md:19-26` despite being implemented. The SUMMARY frontmatter `requirements-completed` correctly lists all 8. This is a documentation-update gap (checkbox state), not a code gap.

2. **Pre-existing full-suite failures (92) unrelated to Phase 206.** Documented in `206-01-SUMMARY.md:145` — failures are in `test_schematic_repair`, `test_undo_stack`, `test_training_eval`, `test_spatial_renderer`, `sim/test_eurorack_circuit`, plus `test_slc_compliance::test_skill_md_operation_count_matches` (stale "149" hardcoded in `skills/SKILL.md`). Zero file overlap with Phase 206 changes.

3. **Registry/schema parity drift (pre-existing).** `validate_registry_completeness()` shows `schema_count=159` vs `registry_count=156` — 3 known pre-existing missing ops unrelated to this phase.

## Files Verified

- `src/volta/manufacturing/drc_profiles/__init__.py` (package + resolver + capabilities registry)
- `src/volta/manufacturing/drc_profiles/*.kicad_dru` (9 DRU files)
- `src/volta/manufacturing/vendor_drc.py` (internal evaluator)
- `src/volta/dfm/profiles.py` (`drc_rules_path` field + corrected annular rings + 5 new profiles)
- `src/volta/ops/_schema_pcb.py` (`DrcVendorOp`, `ListVendorDrcProfilesOp`)
- `src/volta/ops/schema.py` (union + `__all__`)
- `src/volta/ops/registry.py` (`_RAW_CATALOG` entries)
- `src/volta/ops/handlers/query.py` (`_handle_drc_vendor` uses `NativeParser.parse_pcb`; `_handle_list_vendor_drc_profiles`)
- `pyproject.toml` (`[tool.setuptools.package-data]` declares `*.kicad_dru`)
- `tests/test_vendor_drc.py`, `tests/test_drc_vendor_ops.py`, `tests/test_drc_profiles.py`, `tests/test_registry.py`, `tests/test_dfm_checker.py`
