bretbouchard/kicad-agent/.planning/phases/208-manufacturer-handoff-package/208-VERIFICATION.md

---
phase: 208
plan: 01
role: phase-goal-verifier
verifier: ZCode (phase goal verifier)
date: 2026-07-10
verdict: PASS (goal met; 1 partial success criterion)
---

# Phase 208 — Phase Goal Verification (208-VERIFICATION.md)

**Phase goal:** "One call (`build_handoff_export`) produces a complete zip bundle with all
manufacturing artifacts + readme + manifest, with pre-handoff validation preventing incomplete
bundles."

**Method:** Check the plan's 9 must_haves and the ROADMAP's 5 success criteria against the
actual codebase (not the summary). Tests executed; acceptance grep/smoke checks executed.

## A. Must Haves (from 208-01-PLAN.md)

| # | Must Have | Status | Evidence |
|---|---|---|---|
| 1 | `build_handoff_export` op exists and is registered (HANDOFF-01) | PASS | `BuildHandoffExportOp` (`_schema_pcb.py:1368`); registry entry (`registry.py:1491`); `schema.py` import/union/`__all__`; handler in `_QUERY_HANDLERS` (smoke test: `from volta.ops.handlers.query import _QUERY_HANDLERS; 'build_handoff_export' in _QUERY_HANDLERS` -> True). |
| 2 | One call produces gerbers, drill, BOM, P&P, STEP (optional), netlist, sch PDF (if sch), PCB PDF (HANDOFF-02) | PASS | `export_handoff` (`handoff.py:254`) runs all 8 export wrappers (lines 429-507). `test_handoff_includes_all_artifacts` asserts zip contains gerber/drill/bom/cpl/manifest/readme. |
| 3 | Single `handoff.zip` + manifest.json + readme.md, streamed (no memory blow-up) (HANDOFF-03, Pitfall 7) | PASS | Streaming zip `zipfile.ZipFile(zip_path, "w", zipfile.ZIP_DEFLATED)` + `zf.write(path, arcname=name)` (`handoff.py:564-568`); never loads files into memory. `manifest.save()` (line 559); `atomic_write(readme.md)` (line 541). |
| 4 | readme.md has board name, rev, date, company, layer count, dimensions, surface finish, copper weight, mask/silk color, impedance, DRC/ERC results (HANDOFF-04) | PASS | `_generate_readme` (`handoff.py:123-246`) emits all listed fields. 5 readme tests (name, surface_finish via sidecar, validation results, dimensions, missing-board-spec graceful). Impedance section present but conditional (`if board_spec.impedance_requirements`). |
| 5 | BOM formatting profile-driven via `ManufacturerProfile`; orchestrator NEVER calls `export_jlcpcb_bom` (HANDOFF-05, Pitfall 3) | PASS | `export_bom_profile` (`bom.py:328`); orchestrator calls it (`handoff.py:456`). `grep export_jlcpcb_bom src/volta/manufacturing/` -> 0 matches. |
| 6 | Pre-handoff validation gate: DRC/ERC/vendor DRC fail -> NO zip, clear error (HANDOFF-06, Pitfall 5) | PASS | Step 3 gate (`handoff.py:333-384`); hard `False` -> early return before build dir creation. `test_handoff_blocks_on_drc_failure`, `test_handoff_no_partial_state_on_failure`, `test_handoff_vendor_drc_blocks_on_failure`. |
| 7 | STEP/render configurable via `include_step` / `include_render` (HANDOFF-07) | PASS | `include_step` (default True) gates STEP export (`handoff.py:482`); `include_render` accepted (reserved). `test_handoff_step_excluded_when_flag_false`, `test_handoff_step_included_when_flag_true`. |
| 8 | `build_handoff_export(vendor="jlcpcb")` produces JLCPCB-formatted BOM/CPL via the profile (HANDOFF-08) | PARTIAL | BOM: PASS (columns + filename via `load_profile("jlcpcb")`). CPL: the profile field `cpl_filename_pattern` exists but is NOT consulted by the orchestrator; `export_position` emits a generic `{stem}-pos.csv`. BOM-side vendor formatting is fully delivered; CPL-side filename is generic. |
| 9 | `manifest.json` includes `drc_passed`, `erc_passed`, `vendor_drc_passed`, `drc_violation_count`, `erc_violation_count` (HANDOFF-09) | PASS | Fields on `ManufacturingManifest` (`manufacturing_manifest.py:89-93`); populated by orchestrator (`handoff.py:545-558`); serialized in `to_json` (lines 109-113); loaded in `load()` with defaults (lines 145-149). `test_handoff_manifest_has_validation_proof`. |

**Must-haves: 8 PASS + 1 PARTIAL (#8).**

## B. ROADMAP Success Criteria

### SC-1: zip contains Gerbers, drill, BOM, P&P, STEP (if configured), netlist, sch PDF, PCB PDF, manifest.json, readme.md
**STATUS: PASS.** Orchestrator runs all exports; zip iterates `build_dir.iterdir()` and bundles
every produced file plus manifest.json and readme.md (`handoff.py:566-568`).
`test_handoff_includes_all_artifacts` verifies gerber/drill/bom/cpl/manifest/readme presence.
STEP conditional on `include_step`. Schematic PDF conditional on sch presence. Netlist is
non-critical (tolerated if it fails). When all exports succeed, the bundle is complete per SC-1.

### SC-2: readme.md includes board name, rev, date, layer count, dimensions, surface finish, copper weight, colors, impedance, designer contact
**STATUS: PASS.** `_generate_readme` emits every listed field:
- board name (`# Manufacturing Handoff: {display_name}`, line 190)
- rev / date / company / generated timestamp (lines 192-195)
- surface finish, copper weight outer/inner, soldermask, silkscreen (lines 199-202)
- layer count, dimensions (lines 203-204)
- impedance table (conditional, lines 208-215)
- contact: "Designed by: {company}" (line 243)
Tests: `test_readme_has_board_name`, `test_readme_has_surface_finish`, `test_readme_has_dimensions`.

### SC-3: pre-handoff validation blocks incomplete bundles — if DRC, ERC, or manifest validation fails, NO zip is created
**STATUS: PARTIAL -> PASS with caveat.**
- DRC/ERC/vendor-DRC block: PASS (gate returns before build dir creation; no zip possible).
- "manifest validation fails": The `validate_manifest()` function
  (`manufacturing_manifest.py:172-188`) checks for required artifact names {gerbers, drill,
  bom, cpl}, but it is **NEVER CALLED** in the handoff path (grep confirms zero call sites
  across `src/`). Instead, manifest completeness is enforced *structurally*: critical exports
  (gerbers, drill, cpl, bom) failing triggers `_fail_with_cleanup` (rmtree + `success=False`),
  so an incomplete manifest cannot reach the zip step. The net effect satisfies SC-3's intent
  (no incomplete bundle ships), but the mechanism is "critical-export-failure-blocks" rather
  than "manifest-validation-blocks". If a critical export succeeded but produced an artifact
  with a name outside the required set, `validate_manifest` would catch it — but since the
  orchestrator controls all artifact `name=` arguments (hard-coded categories at lines 430,
  438, 446, 464), this cannot happen in practice.
- **Caveat:** the explicit `validate_manifest` call envisioned by the plan/ROADMAP is absent.
  This is a latent gap: if a future change relaxes the critical-export list or renames a
  category, no manifest-level guard would catch it. Recommend wiring `validate_manifest` as a
  final pre-zip gate in a follow-up (defense in depth). Not blocking for v1.

### SC-4: `build_handoff_export(vendor="jlcpcb")` produces JLCPCB-formatted BOM via profile-driven formatter
**STATUS: PASS.** BOM columns (`Comment,Designator,Footprint,LCSC`) and filename
(`{stem}_JLCPCB-BOM.csv`) are driven by `load_profile("jlcpcb")`. `export_jlcpcb_bom` is NOT
called in the handoff path (grep = 0). `test_bom_profile_jlcpcb_columns` confirms the header.
(The ROADMAP text also mentions "CPL file naming" — see must-have #8 PARTIAL.)

### SC-5: Bare-board orders (include_step=False) produce bundle without STEP
**STATUS: PASS.** `include_step=False` skips the `export_step` call (`handoff.py:482-488`).
`test_handoff_step_excluded_when_flag_false` asserts no `.step` file in the zip.

**Success criteria: 4 PASS + 1 PARTIAL (SC-3 caveat: intent met, explicit manifest-validation
gate not wired).**

## C. Phase Goal Verification

> "One call (`build_handoff_export`) produces a complete zip bundle with all manufacturing
> artifacts + readme + manifest, with pre-handoff validation preventing incomplete bundles."

**VERIFIED.**
- **One call:** `build_handoff_export` op -> handler -> `export_handoff()` orchestrator. A
  single op invocation runs the full 11-step pipeline. PASS.
- **Complete zip bundle:** gerbers + drill + BOM + CPL + STEP (optional) + netlist + sch-PDF
  (if sch) + PCB-PDF + readme.md + manifest.json, all streamed into `handoff.zip`. PASS.
- **Pre-handoff validation preventing incomplete bundles:** DRC/ERC/vendor-DRC hard-failure
  returns before any build dir/zip is created; critical-export failure cleans up + fails.
  No incomplete bundle ships. PASS (with SC-3 caveat re: `validate_manifest` not explicitly
  called).

## D. Test Execution

```
pytest tests/test_handoff.py tests/test_registry.py tests/test_build_system.py tests/test_export_bom.py
-> 97 passed in 1.58s
```

Phase 208 acceptance smoke tests (profiles, registry meta, handler merge, imports):
all pass.

## E. Findings Summary

1. **PARTIAL (SC-3 / must-have #6 nuance):** `validate_manifest()` is defined but never called.
   Completeness is enforced structurally (critical-export failure -> cleanup), which satisfies
   the goal's intent. Recommend wiring `validate_manifest` as a defense-in-depth pre-zip gate.
2. **PARTIAL (SC-4 / must-have #8 nuance):** `cpl_filename_pattern` on `ManufacturerProfile`
   is unused; JLCPCB bundle CPL file is generically named. BOM formatting is fully
   vendor-driven. Recommend a follow-up to honour the profile CPL pattern.
3. **INFO (pre-existing, not Phase 208 scope):** SKILL.md operation count (149) lags schema
   (160); `test_slc_compliance.py::test_skill_md_operation_count_matches` is red across v7.0.
   Phase 208 widened the gap by +1.

## Verdict

**PHASE GOAL MET — VERIFICATION PASSED.**

The phase goal is achieved: one call produces a complete zip bundle, and pre-handoff
validation prevents incomplete bundles. 8/9 must-haves fully PASS; 1 (#8) is PARTIAL on a
minor sub-aspect (CPL filename). 4/5 success criteria fully PASS; SC-3 meets its intent via
a structural mechanism rather than the explicit `validate_manifest` call. The partials are
non-blocking and tracked as follow-ups. Phase 208 is ready to proceed to Phase 209 (integration).
```
```
