bretbouchard/kicad-agent/.planning/phases/240-volta-op-registry-tests/240-01-PLAN.md

---
phase: 240
plan: 01
type: execute
wave: 1
depends_on: []
files_modified:
  - macos-app/Tests/VoltaTests/VoltaOpRegistryTests.swift
  - macos-app/Tests/VoltaTests/Fixtures/
  - macos-app/Sources/Volta/Parsing/VoltaOpRegistry.swift
autonomous: true
requirements:
  - TEST-OP-01
  - TEST-OP-02
  - TEST-OP-03
must_haves:
  truths:
    - Every one of the 268 ops has at least one test
    - Test corpus contains at least 20 real .kicad_sch fixtures
    - Property tests verify round-trip stability: apply op, parse, apply op again, get same result
    - Op registry count is asserted in a test
  artifacts:
    - path: macos-app/Tests/VoltaTests/VoltaOpRegistryTests.swift
      provides: "Coverage test that iterates every op type and asserts a test exists"
    - path: macos-app/Tests/VoltaTests/Fixtures/
      provides: "At least 20 .kicad_sch / .kicad_pcb fixtures covering common topologies"
  key_links:
    - from: VoltaOpRegistryTests
      to: VoltaOpRegistry
      via: "iterates the registry's allOpTypes and looks up a test method for each"

<threat_model>
## Trust Boundaries
| Boundary | Description |
|---|---|
| test fixtures | Schematics are public hardware designs (no sensitive data) |
| CI | Tests run sandboxed; no network |

## STRIDE Threat Register
| Threat ID | Category | Component | Disposition | Mitigation Plan |
|---|---|---|---|---|
| T-240-01 | Tampering | test fixture file | Mitigate | Pin fixture SHA256 in test code |

## Stupid-Proof Verification
- User-stupid: adding a new op without a test fails CI
- Magic-stupid: test corpus maintained by a single script
</threat_model>

<context>
## Why this exists
Gap A1 from GAP-ANALYSIS-CURRENT.md. The 268-op Volta registry has zero tests. Every op change risks silent regression. The 50/50 ERC parity test (Phase 218) was a one-shot; we need durable coverage.

## Background
Phases 191-200 set up the Swift testing framework (XCTest, snapshot, property-based, mutation, accessibility, concurrency, daemon, CI gates) but no phase shipped op-level coverage. macos-app/Tests has ~25 files; none iterate the op registry.

## Scope (in)
- Coverage test: iterate the registry, assert each op has a test method
- Property tests for read-only ops (list, count, get)
- Round-trip tests for write ops (add then remove, set then unset)
- 20+ .kicad_sch fixtures covering: LED + R, RC filter, op-amp, 555 timer, voltage regulator, MCU breakout, motor driver, USB-C, sensor breakout, hierarchical sheet, multi-unit IC, power supply, audio amp, RF filter, antenna, FPGA, BGAs, fiducials, test points
- Each fixture has a SHA256 pin in the test code

## Scope (out)
- Mutation testing (Phase 194 already covered)
- Property-based generation of schematics (start with fixtures; expand later)
</context>

<tasks>

### Task 1: OpRegistry introspection
Files: macos-app/Sources/Volta/Parsing/VoltaOpRegistry.swift (extend)

Add a static `allOpTypes: [String]` property that lists every op name. Use reflection on the three enums in VoltaEngine*.swift.

### Task 2: Coverage test
Files: macos-app/Tests/VoltaTests/VoltaOpRegistryTests.swift (new)

XCTest case that iterates `VoltaOpRegistry.allOpTypes` and for each op, looks up `test_<opName>` via reflection. Fails if any op lacks a test.

### Task 3: Test fixture corpus
Files: macos-app/Tests/VoltaTests/Fixtures/ (new)

20+ minimal .kicad_sch files covering common topologies. Each fixture has a sibling .json with SHA256 + description.

### Task 4: Per-op tests
Files: macos-app/Tests/VoltaTests/VoltaOpTests/ (new directory)

For each op, a test method. Read-only ops: assert return value matches expected. Write ops: apply, parse, assert state changed; apply reverse, assert state restored.

### Task 5: CI gate
Files: macos-app/scripts/ci_op_coverage.sh (new)

Bash script: run tests, parse xcresult, fail if coverage < 80%. Wire into existing CI workflow (Phase 200).
</tasks>

<verification>
## Success Criteria
1. VoltaOpRegistryTests passes — every op has a test
2. Per-op tests pass for all 268 ops
3. Round-trip tests pass for all write ops
4. Coverage on VoltaOpRegistry.swift >= 80%
5. CI gate blocks merge if coverage drops
</verification>
