bretbouchard/kicad-agent/.planning/phases/241-streaming-chat-e2e-test/241-01-PLAN.md

---
phase: 241
plan: 01
type: execute
wave: 1
depends_on: []
files_modified:
  - macos-app/Tests/VoltaTests/ChatPipelineE2ETests.swift
  - macos-app/Tests/VoltaTests/Fixtures/canned_echo_response.json
  - macos-app/Tests/VoltaTests/Fixtures/canned_clean_response.json
autonomous: true
requirements:
  - TEST-CHAT-01
  - TEST-CHAT-02
  - TEST-CHAT-03
must_haves:
  truths:
    - Streaming pipeline (NoopChatStream → RouterStreamProvider → ContentChunker → MessageBubbleView) is tested end-to-end
    - Echo-stripping is verified with a canned response that echoes the user prompt
    - Chunking at sentence/paragraph boundaries is verified
    - Cost callback is verified to fire with usage
  artifacts:
    - path: macos-app/Tests/VoltaTests/ChatPipelineE2ETests.swift
      provides: "XCTest cases for the full stream → render pipeline"
    - path: macos-app/Tests/VoltaTests/Fixtures/canned_echo_response.json
      provides: "Canned token stream that includes an echoed user prompt at the start"
  key_links:
    - from: ChatPipelineE2ETests
      to: NoopChatStream
      via: "uses canned canned_echo_response.json to verify echo stripping"
    - from: ChatPipelineE2ETests
      to: ContentChunker
      via: "verifies the chunker produces expected chunks from the streamed output"

<threat_model>
## Trust Boundaries
| Boundary | Description |
|---|---|
| test fixtures | Canned responses are test-only |

## STRIDE Threat Register
No threats; pure unit/integration test with canned data.

## Stupid-Proof Verification
- User-stupid: regression on echo-stripping fails CI before merge
- Magic-stupid: adding a new chunking strategy requires updating the fixture + test
</threat_model>

<context>
## Why this exists
Gap A8 from GAP-ANALYSIS-CURRENT.md. The streaming chat pipeline (router → provider → stream → chunk → bubble render) has no end-to-end test. The echo bug that started this whole conversation is exactly the kind of regression this gap allowed.

## Background
Individual pieces have tests: NoopChatStream works, ContentChunker has logic. But the integration is untested. We need a test that runs the full pipeline and asserts the final output matches expectations.

## Scope (in)
- E2E test with canned responses
- Echo-stripping verification (the bug from this session)
- Sentence/paragraph boundary chunking verification
- Cost callback verification
- Loop-collapse verification (ContentChunker dedup)

## Scope (out)
- Live provider tests (use NoopChatStream; live tests are flaky)
- SwiftUI render tests (out of scope for E2E; covered by view snapshot tests)
</context>

<tasks>

### Task 1: Canned response fixtures
Files: macos-app/Tests/VoltaTests/Fixtures/

Three JSON files:
- canned_echo_response.json: response that starts by echoing the user prompt verbatim (regression for the echo bug)
- canned_clean_response.json: well-formed response with paragraphs and sentences
- canned_loop_response.json: response that repeats a sentence 5x (regression for loop collapse)

### Task 2: NoopChatStream with canned response
Files: macos-app/Tests/VoltaTests/ChatPipelineE2ETests.swift

Extend NoopChatStream (or wrap it) to load from JSON. Stream word-by-word with a small delay so the chunker exercises boundary logic.

### Task 3: Full pipeline test
Files: macos-app/Tests/VoltaTests/ChatPipelineE2ETests.swift

For each canned fixture:
1. Build a [ChatMessage] with a user prompt
2. Run RouterStreamProvider with the canned stream
3. Collect all emitted chunks
4. Run ContentChunker.chunk on the concatenated text
5. Assert:
   - Echoed prompt is stripped from the first chunk
   - Paragraph breaks produce separate chunks
   - Sentence-end chunks fire on boundary
   - Loop is collapsed with (xN) annotation

### Task 4: Cost callback test
Files: macos-app/Tests/VoltaTests/ChatPipelineE2ETests.swift

Verify onUsage is called with a non-zero KCUsage after streaming completes.

### Task 5: CI gate
Wire the test into the existing CI coverage gate (Phase 200). Test must pass for merge.
</tasks>

<verification>
## Success Criteria
1. ChatPipelineE2ETests passes all canned scenarios
2. Echo-stripping regression is caught
3. Loop-collapse regression is caught
4. Cost callback fires correctly
5. CI gate blocks merge on failure
</verification>
