bretbouchard/kicad-agent/.planning/quick/260616-wqd-build-a-validate-labels-pre-flight-check/260616-wqd-SUMMARY.md

---
phase: quick
plan: 01
subsystem: validation
tags: [pre-analysis, global-labels, duplicate-detection, schematic-validation]

# Dependency graph
requires:
  - phase: "75"
    provides: "PreAnalysisGate infrastructure, PreAnalysisResult/PreAnalysisFinding types, executor wiring"
provides:
  - "Duplicate global label detection in PreAnalysisGate for add_label, batch_connect, regenerate_wiring, place_net_labels"
  - "_get_existing_global_label_names helper mapping label names to positions"
  - "_analyze_label_operation, _check_single_label, _check_label_list methods on PreAnalysisGate"
affects: [pre-analysis, schematic-routing, batch-operations]

# Tech tracking
tech-stack:
  added: []
  patterns: ["post-dispatch label analysis (runs after wiring analysis for batch_connect)", "helper function returning name-to-positions dict for blocker details"]

key-files:
  created: []
  modified:
    - src/volta/ops/pre_analysis.py
    - tests/test_pre_analysis.py

key-decisions:
  - "Label analysis runs as a separate post-dispatch pass, not inside the wiring branch, so batch_connect gets both wiring and label analysis"
  - "PlaceNetLabelsOp has no global_labels field (labels derived from pin_map), so pre-analysis is a no-op for it"
  - "Exact string match on label names (case-sensitive) -- no fuzzy/regex matching"
  - "Global label names must be unique regardless of position -- two globals with same name are always same net"

patterns-established:
  - "Post-dispatch analysis pattern: label check runs after the main if/elif chain so ops can accumulate multiple analyses"

requirements-completed: [QUICK-LABEL-VALIDATION]

# Metrics
started: 2026-06-17T03:38:59Z
completed: 2026-06-17T03:46:04Z
duration: 7m
duration_minutes: 7
commits: 3
files_modified: 2
---

# Quick 01: Validate Labels Pre-Flight Check Summary

**Duplicate global label detection in PreAnalysisGate blocks add_label, batch_connect, regenerate_wiring before file mutation**

## Performance

- **Duration:** 7m
- **Started:** 2026-06-17T03:38:59Z
- **Completed:** 2026-06-17T03:46:04Z
- **Tasks:** 2
- **Commits:** 3 (test RED, feat GREEN, test integration)
- **Files modified:** 2

## Accomplishments
- PreAnalysisGate returns blocker with category "duplicate_global_label" when any label-creating op would introduce a duplicate global label name
- Detection runs BEFORE Transaction/write -- file is never mutated on blocked operations (verified by integration test)
- Local and hierarchical labels are correctly excluded from duplicate checking (can legitimately repeat)
- Intra-operation duplicates detected (same name appears twice in batch_connect global_labels list)
- 13 new tests (11 unit + 2 integration), all 45 pre_analysis tests pass

## Task Commits

Each task was committed atomically:

1. **Task 1 (RED): Failing tests for duplicate global label check** - `5806888` (test)
2. **Task 1 (GREEN): Implement duplicate global label pre-flight check** - `255cd3b` (feat)
3. **Task 2: Integration test for executor label blocking** - `ee47896` (test)

**Plan metadata:** pending (orchestrator handles docs commit)

## Files Created/Modified
- `src/volta/ops/pre_analysis.py` - Added `_analyze_label_operation`, `_check_single_label`, `_check_label_list` methods; added `_get_existing_global_label_names` helper; wired label dispatch into `analyze()`
- `tests/test_pre_analysis.py` - Added 13 new tests: 11 unit tests in `TestDuplicateGlobalLabelDetection`, 2 integration tests in `TestDuplicateLabelExecutorIntegration`; added helper functions `_make_ir_with_global_labels` and `_cleanup_ir`

## Decisions Made
- Label analysis added as post-dispatch pass after the main if/elif chain, ensuring batch_connect gets both wiring analysis AND label analysis
- PlaceNetLabelsOp is included in dispatch routing but the handler is a no-op since it has no global_labels input field
- Existing global labels queried via `ir.get_label_positions()` filtered to `label_type == "global"` rather than accessing `sch.globalLabels` directly

## Deviations from Plan

None - plan executed exactly as written.

## Issues Encountered
- System Python 3.9.6 does not support `X | None` syntax; used pyenv Python 3.11.11 for test execution (pre-existing project requirement)
- `test_analysis_rules.py` has a pre-existing ImportError (imports `SchematicSpatialAnalyzer` which no longer exists) -- completely unrelated, out of scope

## User Setup Required

None - no external service configuration required.

## Next Phase Readiness
- Pre-analysis gate now covers all major label-creating operations
- Pattern established for adding new pre-flight checks (post-dispatch analysis pass)

---
*Phase: quick-01*
*Completed: 2026-06-17*

## Self-Check: PASSED

- All 3 commits verified in git log (5806888, 255cd3b, ee47896)
- pre_analysis.py exists and modified
- test_pre_analysis.py exists and modified
- SUMMARY.md exists at correct path
- No unexpected file deletions in commits
- No stubs (TODO/FIXME/placeholder) in modified source
