bretbouchard/kicad-agent/.planning/phases/192-snapshot-testing/192-01-PLAN.md

---
phase: 192-snapshot-testing
plan: 01
type: execute
wave: 2
depends_on: [191-01]
files_modified: [Package.swift, Tests/SnapshotTests/SnapshotTests.swift, Tests/SnapshotTests/FrozenTime.swift, Tests/SnapshotTests/SnapshotVariants.swift]
autonomous: true
requirements: [TEST-03, A11Y-05, A11Y-07]
user_setup: []
must_haves:
  truths:
    - Every SwiftUI view has 4 snapshot variants (light, dark, Dynamic Type XXXL, high contrast)
    - Snapshot tests use frozen time fixtures (prevent flakiness from dates)
    - Snapshot tests run 10x with zero flakes (anti-flake verification)
    - High contrast variant passes a11y audit (WCAG AA 4.5:1 minimum)
    - Dynamic Type XXXL works without clipping (scales up to .accessibilityExtraExtraExtraLarge)
  artifacts:
    - path: Package.swift
      provides: SnapshotTesting dependency
      contains: pointfreeco/swift-snapshot-testing
    - path: Tests/SnapshotTests/SnapshotTests.swift
      provides: 4-variant snapshot tests for views
      exports: snapshot test strategies
    - path: Tests/SnapshotTests/FrozenTime.swift
      provides: Frozen time fixture helper
      min_lines: 30
    - path: Tests/SnapshotTests/SnapshotVariants.swift
      provides: Snapshot strategy variants
      min_lines: 50
  key_links:
    - from: Tests/SnapshotTests
      to: SnapshotTesting package
      via: import SnapshotTesting
      pattern: assertSnapshot.*matching
    - from: SnapshotVariants
      to: all views
      via: 4-variant strategy application
      pattern: strategy.*light.*dark.*xxxl.*highContrast
---

<objective>
Implement 4-variant snapshot testing for all SwiftUI views (light, dark, Dynamic Type XXXL, high contrast) with frozen time fixtures to prevent flakiness.

Purpose: Snapshot tests catch UI regressions across appearance modes. 4 variants ensure accessibility compliance (Dynamic Type XXXL) and high contrast mode validation per A11Y-05/A11Y-07. Frozen time prevents date-based flakiness (Pitfall 11).

Output: SnapshotTesting package integrated, 4-variant snapshot strategy, frozen time helper, example snapshot tests for Liquid Glass views, anti-flake verification (10-run test).
</objective>

<execution_context>
@$HOME/.claude/get-shit-done/workflows/execute-plan.md
@$HOME/.claude/get-shit-done/templates/summary.md
</execution_context>

<context>
@.planning/PROJECT.md
@.planning/ROADMAP.md
@.planning/STATE.md
@.planning/research/v6/STACK.md
@.planning/research/v6/PITFALLS.md
@.planning/phases/191-swift-testing-framework/191-01-PLAN.md
</context>

<interfaces>
<!-- SnapshotTesting from STACK.md -->
From .planning/research/v6/STACK.md:
```swift
// SnapshotTesting package
.package(url: "https://github.com/pointfreeco/swift-snapshot-testing", from: "1.19.2")

// SnapshotTesting usage
import SnapshotTesting
assertSnapshot(matching: view, as: .image(layout: .device(config: "iPhone Pro")))
withSnapshotTesting(record: .all, diffTool: "ksdiff")
```
</interfaces>

<tasks>

<task type="auto">
  <name>Task 1: Add SnapshotTesting package dependency</name>
  <files>Package.swift</files>
  <action>Add SnapshotTesting to Package.swift dependencies (STACK.md 1.19.2):
```swift
dependencies: [
  .package(url: "https://github.com/pointfreeco/swift-snapshot-testing", from: "1.19.2")
]
```
Add to test target dependencies:
```swift
.testTarget(
  name: "VoltaSnapshotTests",
  dependencies: [
    .target(name: "VoltaApp"),
    .product(name: "SnapshotTesting", package: "swift-snapshot-testing")
  ]
)
```
Create new test target for snapshot tests (separate from unit tests).</action>
  <verify>swift package resolve shows SnapshotTesting package resolved</verify>
  <done>SnapshotTesting package added, separate VoltaSnapshotTests target created</done>
</task>

<task type="auto" tdd="true">
  <name>Task 2: Create frozen time fixture helper</name>
  <files>Tests/SnapshotTests/FrozenTime.swift</files>
  <behavior>
    - Test 1: Frozen time returns consistent Date across calls
    - Test 2: Frozen time resets after each test
    - Test 3: Frozen time isolates test threads (no cross-contamination)
  </behavior>
  <action>Create Tests/SnapshotTests/FrozenTime.swift with frozen time helper:
```swift
import Foundation

/// Frozen time fixture for snapshot tests
/// Prevents flakiness from date/time changes (Pitfall 11)
enum FrozenTime {
    private static let frozenDate = Date(timeIntervalSince1970: 1_600_000_000) // Fixed timestamp
    
    static var current: Date {
        frozenDate
    }
    
    /// Run closure with frozen time override
    static func withFrozenTime<T>(_ body: () throws -> T) rethrows -> T {
        try body()
    }
}
```
Use this in view snapshots that display dates/times. This prevents snapshot flakes from timestamps changing between runs (Pitfall 11).</action>
  <verify>swift test --filter FrozenTimeTests passes all 3 tests</verify>
  <done>FrozenTime helper created with fixed timestamp, isolated per test, cross-thread safe</done>
</task>

<task type="auto" tdd="true">
  <name>Task 3: Create 4-variant snapshot strategies</name>
  <files>Tests/SnapshotTests/SnapshotVariants.swift</files>
  <behavior>
    - Test 1: Light mode strategy renders correctly
    - Test 2: Dark mode strategy renders correctly
    - Test 3: Dynamic Type XXXL strategy scales without clipping
    - Test 4: High contrast strategy meets WCAG AA 4.5:1
  </behavior>
  <action>Create Tests/SnapshotTests/SnapshotVariants.swift with 4 snapshot strategies:
```swift
import SwiftUI
import SnapshotTesting

/// Snapshot strategies for accessibility variants per TEST-03, A11Y-05, A11Y-07
enum SnapshotVariants {
    static let light = strategy as: .image(precision: 0.99, layout: .device(config: "iPhone Pro"))
    
    static let dark = strategy as: .image(precision: 0.99, layout: .device(config: "iPhone Pro"))
    
    static let dynamicTypeXXXL = strategy as: .image(
        precision: 0.99,
        layout: .device(config: "iPhone Pro"),
        traits: .init(
            preferredContentSizeCategory: .accessibilityExtraExtraExtraLarge,
            layoutDirection: .leftToRight
        )
    )
    
    static let highContrast = strategy as: .image(
        precision: 0.99,
        layout: .device(config: "iPhone Pro"),
        traits: .init(
            accessibilityContrast: .high,
            preferredContentSizeCategory: .accessibilityExtraExtraExtraLarge
        )
    )
}
```
This implements TEST-03 requirement (4 snapshot variants) and A11Y-05 (Dynamic Type XXXL), A11Y-07 (high contrast).</action>
  <verify>swift test --filter SnapshotVariantsTests passes all 4 strategy tests</verify>
  <done>4-variant snapshot strategies created (light, dark, XXXL, high contrast), each verified with dedicated test</done>
</task>

<task type="auto" tdd="true">
  <name>Task 4: Create example snapshot tests for Liquid Glass views</name>
  <files>Tests/SnapshotTests/SnapshotTests.swift</files>
  <behavior>
    - Test 1: Liquid Glass shell snapshot in light mode
    - Test 2: Chat view snapshot in dark mode
    - Test 3: Decision timeline snapshot in Dynamic Type XXXL
    - Test 4: Approval gates snapshot in high contrast
  </behavior>
  <action>Create Tests/SnapshotTests/SnapshotTests.swift with example snapshot tests:
```swift
import SwiftUI
import Testing
import SnapshotTesting
@testable import VoltaApp

@Suite("Snapshot Tests")
struct SnapshotTests {
    @Test("Liquid Glass shell - all 4 variants")
    func liquidGlassShell() {
        let view = LiquidGlassShell()
        assertSnapshot(matching: view, as: SnapshotVariants.light, named: "light")
        assertSnapshot(matching: view, as: SnapshotVariants.dark, named: "dark")
        assertSnapshot(matching: view, as: SnapshotVariants.dynamicTypeXXXL, named: "xxxl")
        assertSnapshot(matching: view, as: SnapshotVariants.highContrast, named: "high-contrast")
    }
    
    @Test("Chat view - all 4 variants")
    func chatView() {
        let view = ChatView()
        assertSnapshot(matching: view, as: SnapshotVariants.light, named: "light")
        assertSnapshot(matching: view, as: SnapshotVariants.dark, named: "dark")
        assertSnapshot(matching: view, as: SnapshotVariants.dynamicTypeXXXL, named: "xxxl")
        assertSnapshot(matching: view, as: SnapshotVariants.highContrast, named: "high-contrast")
    }
}
```
Run with recording mode first: `swift test --enable-code-coverage --snapshot-testing=record` to generate fixtures.</action>
  <verify>swift test --filter SnapshotTests runs all snapshot tests, 4 variants per view, all pass</verify>
  <done>Example snapshot tests created for Liquid Glass + Chat views, 4 variants each, fixtures generated</done>
</task>

</tasks>

<threat_model>
## STRIDE Threat Register

| Threat ID | Category | Component | Disposition | Mitigation Plan |
|---|---|---|---|---|
| T-192-01 | I | SnapshotTesting package | mitigate | Pin to exact version 1.19.2, verify checksum via SPM audit, check repository authenticity (PointFree official) |
| T-192-02 | D | Snapshot fixtures (images) | mitigate | Store fixtures in git LFS if large, validate image integrity on load, prevent arbitrary file write via path traversal checks |
| T-192-03 | E | Snapshot comparison algorithm | mitigate | Use precision threshold 0.99, hash fixtures with SHA256, verify no steganography/payload injection in fixture images |
| T-192-04 | T | Frozen time fixture | accept | Fixed timestamp is deterministic, no external dependency, minimal spoofing risk (timestamps not security-critical) |
| T-192-05 | R | Snapshot test rollback | mitigate | Keep fixtures in version control, tag releases with fixture SHA256s, rollback to previous commit if regression detected |

## Adversarial Scenario

An attacker modifies snapshot fixtures to hide UI regressions (e.g., malicious button now invisible to users but matches snapshot). Mitigation: Store fixtures as reference in CI (read-only), require branch approval for fixture changes, add pixel-diff threshold alarms (>1% difference triggers alert), run snapshot tests with anti-tampering mode that computes SHA256 of rendered output and compares against fixture manifest. The dual-path verification (visual comparison + hash verification) makes malicious substitution detectable.

</threat_model>

<verification>
1. SnapshotTesting package resolved successfully
2. Frozen time helper prevents date-based flakes (10-run verification: zero variance)
3. 4-variant snapshot strategies render correctly
4. Example snapshot tests run for Liquid Glass + Chat views
5. Dynamic Type XXXL variant scales without clipping
6. High contrast variant meets WCAG AA 4.5:1 contrast ratio
7. Snapshot fixtures stored in __snapshots__/ directory
8. Anti-flake verification: run snapshot tests 10x, all identical output
</verification>

<success_criteria>
- SnapshotTesting integrated into Package.swift
- 4 snapshot variants (light, dark, XXXL, high contrast) for all SwiftUI views
- Frozen time fixture prevents date-based flakes
- Dynamic Type XXXL variant works without clipping (A11Y-05)
- High contrast variant passes WCAG AA audit (A11Y-07)
- Anti-flake verification passes (10-run test, zero variance)
- Retroactively apply to existing views from phases 161-190
</success_criteria>

<output>
After completion, create `.planning/phases/192-snapshot-testing/192-01-SUMMARY.md`
</output>
