bretbouchard/kicad-agent/.planning/phases/193-property-based-testing/193-01-PLAN.md

---
phase: 193-property-based-testing
plan: 01
type: tdd
wave: 3
depends_on: [192-01]
files_modified: [Package.swift, Tests/PropertyTests/StateMachineTests.swift, Tests/PropertyTests/EventSourcingTests.swift, Tests/PropertyTests/HashStabilityTests.swift]
autonomous: true
requirements: [TEST-04]
user_setup: []
must_haves:
  truths:
    - Property-based tests verify state machine invariants (GSD transitions never invalid)
    - SwiftCheck fuzzer tests op journal encoding (all valid ops encode/decode correctly)
    - Property tests verify event sourcing invariants (replay produces same state)
    - Fuzzer tests verify hash stability (same inputs always produce same hash)
    - Property tests verify CloudKit sync invariants (LWW resolution never loses data)
  artifacts:
    - path: Package.swift
      provides: SwiftCheck dependency
      contains: typelift/SwiftCheck
    - path: Tests/PropertyTests/StateMachineTests.swift
      provides: Property tests for GSD state machine
      min_lines: 60
    - path: Tests/PropertyTests/EventSourcingTests.swift
      provides: Property tests for event sourcing
      min_lines: 80
    - path: Tests/PropertyTests/HashStabilityTests.swift
      provides: Property tests for hash stability
      min_lines: 50
  key_links:
    - from: Tests/PropertyTests
      to: SwiftCheck
      via: import SwiftCheck
      pattern: forAll.*property
    - from: StateMachineTests
      to: Governance/StateMachine.swift
      via: state transition validation
      pattern: GSDPhase.*transition
    - from: EventSourcingTests
      to: Models/Decision.swift
      via: event replay verification
      pattern: replayEvents.*sameState
---

<objective>
Implement property-based testing via SwiftCheck to verify invariants: state machine transitions, op journal encoding, event sourcing replay, hash stability, CloudKit LWW resolution.

Purpose: Property-based testing catches edge cases unit tests miss by fuzzing inputs with random generators. SwiftCheck shrinks counterexamples to minimal cases. Verifies critical invariants (state machine never invalid, replay produces same state, hash stability).

Output: SwiftCheck package integrated, property tests for GSD state machine, event sourcing, hash stability, CloudKit sync invariants, shrinking on failure.
</objective>

<execution_context>
@$HOME/.claude/get-shit-done/workflows/execute-plan.md
@$HOME/.claude/get-shit-done/templates/summary.md
</execution_context>

<context>
@.planning/PROJECT.md
@.planning/ROADMAP.md
@.planning/STATE.md
@.planning/research/v6/STACK.md
@.planning/research/v6/ARCHITECTURE.md
@.planning/phases/192-snapshot-testing/192-01-PLAN.md
</context>

<interfaces>
<!-- SwiftCheck from STACK.md -->
From .planning/research/v6/STACK.md:
```swift
// SwiftCheck package
.package(url: "https://github.com/typelift/SwiftCheck", from: "0.12.0")

// SwiftCheck usage
import SwiftCheck
forAll { (x: Int) in
    property(x + x == 2 * x)
}
```
</interfaces>

<tasks>

<task type="auto">
  <name>Task 0: Write SwiftCheck property test contracts</name>
  <files>Tests/PropertyTests/StateMachineTests.swift, Tests/PropertyTests/EventSourcingTests.swift, Tests/PropertyTests/HashStabilityTests.swift</files>
  <action>Create property test interface contracts (define what invariants each property test verifies):
1. StateMachineTests.swift: GSD phase transition invariants
2. EventSourcingTests.swift: Event replay determinism
3. HashStabilityTests.swift: Hash stability under fuzzing
These are the contracts — implementation comes in later tasks.</action>
  <verify>Files exist with exported Gen generators and property signatures</verify>
  <done>Property test interface contracts committed, generators defined</done>
</task>

<task type="auto" tdd="true">
  <name>Task 1: Add SwiftCheck package dependency</name>
  <files>Package.swift</files>
  <behavior>
    - Test 1: SwiftCheck package resolves
    - Test 2: Gen generators for custom types
  </behavior>
  <action>Add SwiftCheck to Package.swift (STACK.md 0.12.0):
```swift
dependencies: [
  .package(url: "https://github.com/typelift/SwiftCheck", from: "0.12.0")
]
```
Add to test target:
```swift
.testTarget(
  name: "VoltaPropertyTests",
  dependencies: [
    .target(name: "VoltaApp"),
    .product(name: "SwiftCheck", package: "SwiftCheck")
  ]
)
```
Create VoltaPropertyTests target separate from unit/snapshot tests.</action>
  <verify>swift package resolve shows SwiftCheck resolved, swift test --filter PropertyTests runs (even if empty)</verify>
  <done>SwiftCheck package added, VoltaPropertyTests target created</done>
</task>

<task type="auto" tdd="true">
  <name>Task 2: Implement state machine property tests</name>
  <files>Tests/PropertyTests/StateMachineTests.swift</files>
  <behavior>
    - Test 1: All GSD phase transitions are valid (no invalid jumps)
    - Test 2: Circular transitions detect loops
    - Test 3: State machine rejects undefined transitions
  </behavior>
  <action>Implement Tests/PropertyTests/StateMachineTests.swift:
```swift
import SwiftCheck
import Testing
@testable import VoltaApp

extension GSDPhase: Arbitrary {
    static var arbitrary: Gen<GSDPhase> {
        Gen.fromElements(in: [
            .questioning, .research, .planning, .review,
            .execute, .verification, .complete
        ])!
    }
}

@Suite("State Machine Property Tests")
struct StateMachineTests {
    @Test("state transitions never produce invalid states")
    func transitionsValid() {
        property <- forAll { (phase: GSDPhase) in
            let machine = GSDStateMachine(currentPhase: phase)
            // All valid transitions from this phase should succeed
            for transition in GSDStateTransition.allCases {
                if machine.canTransition(transition) {
                    var mutated = machine
                    try? mutated.transition(transition)
                    #expect(mutated.currentPhase != .invalid)
                }
            }
        }
    }
}
```
This verifies TEST-04 state machine invariants (GSD transitions never invalid).</action>
  <verify>swift test --filter StateMachineTests runs 100 iterations, all pass, shrinking reduces counterexample to minimal case on failure</verify>
  <done>State machine property tests implemented, all GSD transitions verified valid, shrinking works on failure</done>
</task>

<task type="auto" tdd="true">
  <name>Task 3: Implement event sourcing property tests</name>
  <files>Tests/PropertyTests/EventSourcingTests.swift</files>
  <behavior>
    - Test 1: Replaying events produces same state
    - Test 2: Event compaction preserves state
    - Test 3: Out-of-order events rejected or reordered
  </behavior>
  <action>Implement Tests/PropertyTests/EventSourcingTests.swift:
```swift
import SwiftCheck
import Testing
@testable import VoltaApp

extension Decision: Arbitrary {
    static var arbitrary: Gen<Decision> {
        Gen.zip(
            Gen<Int>.positive(),
            Gen<UUID>.arbitrary,
            Gen<String>.arbitrary,
            Gen<Date>.arbitrary
        ).map { id, conversationId, eventData, timestamp in
            Decision(
                id: id,
                conversationId: conversationId,
                eventType: .componentAdded,
                timestamp: timestamp,
                eventData: eventData.data(using: .utf8) ?? Data()
            )
        }
    }
}

@Suite("Event Sourcing Property Tests")
struct EventSourcingTests {
    @Test("replaying events produces same state")
    func replayDeterminism() {
        property <- forAll { (events: [Decision]) in
            let engine = TimeTravelEngine()
            let originalState = try? engine.replayEvents(events)
            let replayedState = try? engine.replayEvents(events)
            #expect(originalState == replayedState)
        }
    }
}
```
This verifies TEST-04 event sourcing invariants (replay produces same state).</action>
  <verify>swift test --filter EventSourcingTests runs 100 iterations, replay produces identical state each time</verify>
  <done>Event sourcing property tests implemented, replay determinism verified, shrinking finds minimal violating event sequence</done>
</task>

<task type="auto" tdd="true">
  <name>Task 4: Implement hash stability property tests</name>
  <files>Tests/PropertyTests/HashStabilityTests.swift</files>
  <behavior>
    - Test 1: Same inputs always produce same hash
    - Test 2: Hash excludes non-deterministic fields (timestamps, UUIDs)
    - Test 3: Hash canonical form (sorted keys) is stable
  </behavior>
  <action>Implement Tests/PropertyTests/HashStabilityTests.swift:
```swift
import SwiftCheck
import Testing
@testable import VoltaApp

@Suite("Hash Stability Property Tests")
struct HashStabilityTests {
    @Test("same inputs always produce same hash")
    func hashStability() {
        property <- forAll { (conversation: Conversation) in
            let hash1 = conversation.computeStateHash()
            let hash2 = conversation.computeStateHash()
            #expect(hash1 == hash2)
        }
    }
    
    @Test("hash excludes timestamps and UUIDs")
    func hashExcludesNonDeterministic() {
        property <- forAll { (conversation: Conversation) in
            let originalHash = conversation.computeStateHash()
            
            // Modify timestamp
            var modified = conversation
            modified.updatedAt = Date(timeIntervalSince1970: 9999999999)
            
            let modifiedHash = modified.computeStateHash()
            #expect(originalHash == modifiedHash)
        }
    }
}
```
This verifies TEST-04 hash stability (same inputs always produce same hash, per Pitfall 5).</action>
  <verify>swift test --filter HashStabilityTests runs 1000 iterations, all hashes identical for same inputs, timestamp changes don't affect hash</verify>
  <done>Hash stability property tests implemented, determinism verified, non-deterministic fields excluded from hash</done>
</task>

</tasks>

<threat_model>
## STRIDE Threat Register

| Threat ID | Category | Component | Disposition | Mitigation Plan |
|---|---|---|---|---|
| T-193-01 | I | SwiftCheck package | mitigate | Pin to exact version 0.12.0, verify via SPM audit, check Typelift repository authenticity |
| T-193-02 | D | Random generator seed | accept | SwiftCheck uses deterministic seed per run, flakiness acceptable for property tests (rerun with different seed) |
| T-193-03 | E | Arbitrary generators | mitigate | Limit generator size (max 100 elements), enforce memory limits, prevent infinite recursion via depth bounds |
| T-193-04 | T | Hash collision spoofing | mitigate | Use SHA256 for hashing, verify no collision attacks via property test (distinct inputs → distinct hashes with high probability) |
| T-193-05 | R | Property test rollback | mitigate | Keep property tests in version control, tag releases with property test SHA256s, rollback if regression detected |

## Adversarial Scenario

An attacker submits a PR that introduces a state machine bypass (e.g., skipping verification gate) but masks it by only fuzzing non-critical transitions. Mitigation: Property tests fuzz ALL transitions uniformly, use `forAll` with `Arbitrary` generator covering full state space, add invariant that every phase transition requires verification pass before complete. The uniform coverage ensures bypass attempts fail property test invariants.

</threat_model>

<verification>
1. SwiftCheck package resolved successfully
2. State machine property tests verify all GSD transitions are valid
3. Event sourcing property tests verify replay determinism
4. Hash stability property tests verify deterministic hashing
5. Shrinking reduces counterexamples to minimal cases
6. Property tests run 100+ iterations per property
7. All invariants hold under random fuzzing
</verification>

<success_criteria>
- SwiftCheck integrated for property-based testing
- State machine invariants verified (GSD transitions never invalid)
- Op journal encoding fuzzed (all valid ops encode/decode correctly)
- Event sourcing invariants verified (replay produces same state)
- Hash stability verified (same inputs → same hash, non-deterministic fields excluded)
- CloudKit LWW invariants verified (resolution never loses data)
- Retroactively apply to existing governance models (phases 169-170)
</success_criteria>

<output>
After completion, create `.planning/phases/193-property-based-testing/193-01-SUMMARY.md`
</output>
