bretbouchard/kicad-agent/.planning/phases/199-python-daemon-testing/199-01-PLAN.md

---
phase: 199-python-daemon-testing
plan: 01
type: execute
wave: 1
depends_on: []
files_modified: [PythonDaemon/tests/, PythonDaemon/volta/daemon/mcp_server.py]
autonomous: true
requirements: [TEST-11]
user_setup: []

must_haves:
  truths:
    - "Python daemon has pytest tests with 100% coverage enforced"
    - "Mutation testing on Python daemon (mutmut or similar) with >90% score"
    - "stdio MCP tests verify buffering prevention (100 rapid RPC calls, Pitfall 2 prevention)"
    - "Python tests cover all 142 ops (executor, MCP server, verification gates)"
    - "Mutation score trends tracked (detect Python quality regression)"
  artifacts:
    - path: "PythonDaemon/tests/"
      provides: "pytest test suite for Python daemon"
      min_lines: 100
    - path: "PythonDaemon/.pytest_cache/"
      provides: "Coverage report (100% enforced)"
      exports: ["coverage_report.html", "mutation_score.html"]
  key_links:
    - from: "PythonDaemon/tests/"
      to: "PythonDaemon/volta/"
      via: "pytest imports all daemon modules for coverage"
      pattern: "from volta.daemon.*import.*"
    - from: "PythonDaemon/tests/"
      to: "src/volta/"
      via: "Daemon tests reuse existing 142 op tests from tests/"
      pattern: "tests.test_.*Operation.*Executor"

---

<objective>
Build pytest test suite for Python daemon with 100% coverage enforcement, mutation testing (mutmut) with >90% score, stdio MCP buffering tests (100 rapid RPC calls to prevent Pitfall 2 deadlock), coverage of all 142 ops (executor, MCP server, verification gates), and mutation score trend tracking.

Purpose: Python daemon is the bridge between Swift app and KiCad operations. Bugs here corrupt KiCad files silently. 100% coverage ensures all code paths tested. Mutation testing catches logic gaps coverage misses (e.g., `if op is None:` is "covered" but buggy if `if not op:` was intended). stdio MCP buffering tests prevent Pitfall 2 (deadlock from Python stdout buffering).

Output: pytest suite with 200+ tests, 100% coverage report, mutmut mutation testing with >90% score, stdio MCP stress test (100 rapid RPC calls), all 142 ops covered, mutation score tracked in CI.
</objective>

<execution_context>
@$HOME/.claude/get-shit-done/workflows/execute-plan.md
@$HOME/.claude/get-shit-done/templates/summary.md
</execution_context>

<context>
@.planning/PROJECT.md
@.planning/ROADMAP.md
@.planning/research/v6/STACK.md
@.planning/research/v6/ARCHITECTURE.md
@.planning/research/v6/PITFALLS.md
@tests/  (existing Python tests, 6000+ tests to integrate with)

# Key context from existing tests/:
# - tests/ has 6000+ tests covering 142 ops (executor, validation gates)
# - conftest.py fixtures pattern (reuse for daemon tests)
# - Daemon tests should extend existing op tests, not duplicate
# - PythonDaemon/ is bundled PyInstaller binary, separate from src/volta/
</context>

<tasks>

<task type="auto" tdd="true">
  <name>Task 1: Create pytest infrastructure for Python daemon</name>
  <files>PythonDaemon/tests/conftest.py, PythonDaemon/tests/test_mcp_server.py</files>
  <behavior>
    - Test 1: pytest discovers daemon tests (pytest --collect-only)
    - Test 2: MCP server fixture starts/stops cleanly
    - Test 3: Test imports all daemon modules without error
    - Test 4: Coverage baseline measured (target 100%)
  </behavior>
  <action>Create pytest infrastructure in PythonDaemon/tests/. Add conftest.py with fixtures: mcp_server (starts MCP server with stdio transport), daemon_process (spawns Python daemon subprocess), tmp_kicad_project (temporary .kicad_sch/.kicad_pcb files). Write test_mcp_server.py with smoke tests: test_server_starts, test_server_lists_tools, test_server_handles_shutdown. Run pytest --cov=PythonDaemon/volta --cov-report=html to establish coverage baseline. Aim for 100% from start.</action>
  <verify>pytest PythonDaemon/tests/ --collect-only && pytest --cov --cov-report=term-missing</verify>
  <done>pytest infrastructure created with MCP server fixture, coverage baseline measured</done>
</task>

<task type="auto" tdd="true">
  <name>Task 2: Write stdio MCP buffering stress test (Pitfall 2 prevention)</name>
  <files>PythonDaemon/tests/test_stdio_buffering.py</files>
  <behavior>
    - Test 1: 100 rapid JSON-RPC calls succeed (no deadlock)
    - Test 2: Python stdout forced to line buffering (PYTHONUNBUFFERED=1)
    - Test 3: Watchdog timer kills daemon if no response in 30 seconds
    - Test 4: All 100 calls return correct response IDs (no mixing)
  </behavior>
  <action>Write test_stdio_buffering.py. Test stress: spawn daemon with PYTHONUNBUFFERED=1 env var. Loop 100 times: send JSON-RPC request with unique ID, wait for response with matching ID. Assert all 100 responses received, IDs match, no mixing. Measure total time, assert <10 seconds (100ms avg per RPC). If deadlock: watchdog kills daemon, test fails with timeout. Test verifies Pitfall 2 prevention (stdio buffering causes deadlock). Use asyncio.gather for concurrent requests.</action>
  <verify>pytest PythonDaemon/tests/test_stdio_buffering.py -v --timeout 30</verify>
  <done>stdio MCP stress test passes (100 rapid RPC calls), buffering prevention verified, watchdog works</done>
</task>

<task type="auto" tdd="true">
  <name>Task 3: Cover all 142 ops via daemon MCP server tests</name>
  <files>PythonDaemon/tests/test_mcp_ops.py</files>
  <behavior>
    - Test 1: MCP server lists all 142 ops via list_tools
    - Test 2: Every op has valid JSON Schema inputSchema
    - Test 3: Every op callable via call_tool with minimal args
    - Test 4: Coverage includes all op execution paths
  </behavior>
  <action>Write test_mcp_ops.py. Fetch ops from volta.ops.registry.get_all_operations(). Assert count == 142. For each op: (1) Verify MCP server lists tool, (2) Verify inputSchema is valid JSON Schema, (3) Call tool with minimal args (use test fixture project), (4) Assert response structure correct. Use pytest.mark.parametrize to generate test per op: @pytest.mark.parametrize("op", get_all_operations()) def test_mcp_op_callable(op):. This generates 142 tests, one per op. Coverage now includes executor + MCP layer.</action>
  <verify>pytest PythonDaemon/tests/test_mcp_ops.py -v --cov --cov-report=term | grep "142 passed"</verify>
  <done>All 142 ops covered via MCP server tests, parametrized tests generate 142 test cases</done>
</task>

<task type="auto" tdd="true">
  <name>Task 4: Add mutation testing via mutmut with >90% score enforcement</name>
  <files>PythonDaemon/tests/mutation_test_config.yaml, .github/workflows/python-mutation.yml</files>
  <behavior>
    - Test 1: mutmut runs on all PythonDaemon/ code
    - Test 2: Mutation score >90% enforced (CI fails if below)
    - Test 3: Killed mutants reported per PR (what tests killed what bugs)
    - Test 4: Mutation score tracked over time (trend detection)
  </behavior>
  <action>Install mutmut (pip install mutmut). Create mutation_test_config.yaml: mutmut runs on PythonDaemon/volta/, exclude tests/ (only mutate source). Add .github/workflows/python-mutation.yml CI job: run mutmut generate, mutmut run, upload mutation score as artifact. Configure threshold: score >90% (blocks merge if below). Add PR comment reporting killed mutants (e.g., "5 mutants killed by test_op_executor"). Track score in history file (mutation_score_history.txt) for trend detection.</action>
  <verify>mutmut run --help && gh workflow view python-mutation</verify>
  <done>Mutation testing configured with mutmut, CI enforces >90% score, mutants reported in PR</done>
</task>

<task type="auto" tdd="true">
  <name>Task 5: Enforce 100% coverage via pytest-cov gate</name>
  <files>.github/workflows/python-coverage.yml, PythonDaemon/tests/.coveragerc</files>
  <behavior>
    - Test 1: pytest --cov fails if coverage <100%
    - Test 2: Coverage report includes line + branch coverage
    - Test 3: Uncovered lines reported in CI log
    - Test 4: Coverage badge updated on README (if below 100%, build fails)
  </behavior>
  <action>Add .coveragerc: [run] branch = yes (track branch coverage), fail_under = 100.0 (CI gate). Add .github/workflows/python-coverage.yml: run pytest --cov=PythonDaemon/volta --cov-report=xml --cov-report=html, upload coverage/ to Codecov (or artifact). Fail if coverage.xml shows <100%. Configure pytest to exit 1 if coverage below fail_under. Add branch coverage check (must be 100% too, not just line).</action>
  <verify>pytest --cov --cov-report=term-missing && cat .coveragerc && grep -i "fail_under" .github/workflows/python-coverage.yml</verify>
  <done>100% coverage enforced via pytest-cov fail_under=100, CI gate blocks merge on <100%</done>
</task>

<task type="auto" tdd="true">
  <name>Task 6: Integrate with existing tests/ directory (reuse 6000+ tests)</name>
  <files>PythonDaemon/tests/test_existing_ops.py</files>
  <behavior>
    - Test 1: Daemon tests import from tests/ (reuse existing op tests)
    - Test 2: Existing 6000+ tests run against daemon MCP layer
    - Test 3: No test duplication (daemon tests wrap, not replace)
    - Test 4: Coverage includes existing tests + new daemon tests
  </behavior>
  <action>Write test_existing_ops.py that imports existing tests from tests/. Example: `from tests.test_add_component import TestAddComponent`. Add wrapper test that calls existing test via MCP server: `def test_add_component_via_mcp(test_add_component):`. Use pytest fixture dependency: MCP server provides environment, existing test provides assertions. This ensures all 6000+ existing tests run against daemon MCP layer without duplication. Coverage now includes daemon + existing ops.</action>
  <verify>pytest PythonDaemon/tests/test_existing_ops.py -v --cov --cov-report=term | tail -20</verify>
  <done>Existing 6000+ tests integrated with daemon tests, coverage includes both layers, no duplication</done>
</task>

<task type="auto" tdd="true">
  <name>Task 7: Add verification gates tests (ERC/DRC/OpJournal)</name>
  <files>PythonDaemon/tests/test_verification_gates.py</files>
  <behavior>
    - Test 1: Verification gates run on op execution
    - Test 2: ERC gate fails on invalid schematic (op rejected)
    - Test 3: DRC gate fails on invalid PCB (op rejected)
    - Test 4: OpJournal records all ops with fsync durability
  </behavior>
  <action>Write test_verification_gates.py. Test verification gate execution: call tool with invalid schematic (intentionally broken .kicad_sch), assert ERC failure returned, verify OpJournal logs failure. Test DRC gate: call tool with invalid PCB, assert DRC failure, journal entry. Test OpJournal: call 10 tools, verify journal has 10 entries, check fsync durability (read journal file, verify entries persisted). Ensure verification gates are tested (coverage includes Obdurate Runtime integration).</action>
  <verify>pytest PythonDaemon/tests/test_verification_gates.py -v --cov | grep -i "verification"</verify>
  <done>Verification gates tests pass (ERC/DRC/OpJournal), coverage includes Obdurate Runtime</done>
</task>

<task type="checkpoint:human-verify" gate="blocking">
  <what-built>Python daemon pytest suite with 200+ tests, 100% coverage enforced, mutation testing >90%, stdio MCP stress test (100 rapid RPC), all 142 ops covered, verification gates tested, existing 6000+ tests integrated.</what-built>
  <how-to-verify>
    1. Run `pytest PythonDaemon/tests/ -v --cov --cov-report=html`
    2. Open coverage_report.html, verify 100% line + branch coverage
    3. Run `mutmut run` (locally or via CI), verify >90% mutation score
    4. Run `pytest PythonDaemon/tests/test_stdio_buffering.py -v` (100 rapid RPC calls)
    5. Check CI logs: all tests pass, coverage badge shows 100%, mutation score >90%
  </how-to-verify>
  <resume-signal>Type "approved" to commit Python daemon test suite, or describe coverage gaps</resume-signal>
</task>

</tasks>

<threat_model>
## Trust Boundaries

| Boundary | Description |
|---|---|
| Python Daemon → Swift App | stdio MCP bridge (untrusted input from Swift) |
| Python Daemon → KiCad Files | File I/O (untrusted file paths from ops) |

## STRIDE Threat Register

| Threat ID | Category | Component | Disposition | Mitigation Plan |
|---|---|---|---|---|
| T-199-01 | I | MCP tool call arguments | mitigate | Pydantic schema validation before execution, reject malformed input |
| T-199-02 | I | stdio MCP input (RPC injection) | mitigate | JSON-RPC schema validation, reject non-JSON-RPC messages |
| T-199-03 | D | OpJournal file corruption | mitigate | fsync durability, atomic append writes, crash recovery on malformed lines |
| T-199-04 | E | Mutation testing false positives | mitigate | Human review required for surviving mutants, document why mutant is equivalent |
| T-199-05 | T | Coverage gaps (untested code paths) | mitigate | 100% line + branch enforced, mutation testing catches logic gaps |

## Adversarial Scenario

Name: Attacker crafts malicious MCP tool call that bypasses Pydantic validation. Attacker sends JSON-RPC with Python pickle payload in arguments field, attempts deserialization in daemon. Pydantic schema fails validation, daemon rejects request. But attacker finds schema loophole (unicode normalization bypass) and injects `__import__('os').system('rm -rf /')` in op arguments.

Mitigation: Pydantic schema uses strict mode (extra=forbid). Unicode normalization handled by Python json module ( rejects non-canonical unicode). All op arguments go through strict Pydantic BaseModel validation. Coverage test ensures every validation path is tested (100% enforcement). Mutation testing validates validation logic (mutants that bypass validation are killed).
</threat_model>

<verification>
- [ ] pytest infrastructure created with MCP server fixture
- [ ] test_stdio_buffering.py passes (100 rapid RPC calls, Pitfall 2 prevention)
- [ ] test_mcp_ops.py covers all 142 ops (parametrized tests)
- [ ] Mutation testing configured (mutmut, >90% score)
- [ ] 100% coverage enforced (pytest-cov fail_under=100)
- [ ] Existing 6000+ tests integrated (no duplication)
- [ ] Verification gates tests pass (ERC/DRC/OpJournal)
- [ ] CI workflow enforces 100% coverage + >90% mutation score
- [ ] Coverage report shows 100% line + branch
- [ ] Mutation score tracked in history file
</verification>

<success_criteria>
- [ ] Python daemon pytest suite with 200+ tests
- [ ] 100% line + branch coverage enforced (CI fails if below)
- [ ] Mutation testing >90% score (CI fails if below)
- [ ] stdio MCP stress test passes (100 rapid RPC, no deadlock)
- [ ] All 142 ops covered via MCP server tests
- [ ] Verification gates tested (ERC/DRC/OpJournal)
- [ ] Existing 6000+ tests integrated (coverage includes both)
- [ ] CI enforces quality gates (coverage + mutation)
- [ ] Mutation score trend tracked (detect regression)
</success_criteria>

<output>
After completion, create `.planning/phases/199-python-daemon-testing/199-01-SUMMARY.md` with test count, coverage report, mutation score, and CI gate configuration.
</output>
