bretbouchard/kicad-agent/.planning/phases/209-crossfile-mcp-integration/209-VERIFICATION.md

---
phase: 209-crossfile-mcp-integration
plan: 01
role: phase-goal-verifier
verified: 2026-07-10
verdict: PASS
---

# Phase 209 Phase Goal Verification

**Reviewer:** ZCode (phase-goal-verifier role)
**Verdict: PASS** — the phase goal is fully met.

## Phase Goal (from 209-01-PLAN.md + ROADMAP)

> **"All new operations are callable via MCP and CLI; builds are project-scoped; `ManufacturerClient` ABC is defined for future API adapters"**

This decomposes into 3 goal clauses, each verified below against the actual codebase.

## Goal Clause 1: "All new operations are callable via MCP and CLI"

### MCP — VERIFIED

All 9 v7.0 operations are auto-exposed as MCP tools via `_generate_operation_tools()` (which reads the `Operation` discriminated union). Verified live:

```
$ .venv/bin/python -c "...req={'read_board_metadata','set_board_metadata','set_board_revision',
   'drc_vendor','list_vendor_drc_profiles','build_create','build_list','build_show',
   'build_handoff_export'}; assert req <= tools..."
mcp-exposure-ok 163 tools total
```

All 9 op_types present in the generated tool set (163 total = 160 registered + 3 schema-only union variants). `mcp/edit_server.py` was **not edited** (`git diff` for that file is empty). `tests/test_mcp_tools.py` locks this as a regression guard.

### CLI — VERIFIED

All 9 operations are callable via 4 CLI subcommands. Mapping verified by dispatch tests in `tests/test_cli_integration.py`:

| Subcommand | Action | op_type dispatched | Test |
|---|---|---|---|
| `build` | `create` | `build_create` | `test_build_create_dispatches` |
| `build` | `list` | `build_list` | `test_build_list_dispatches` |
| `build` | `show` | `build_show` | `test_build_show_dispatches` |
| `handoff` | (flat) | `build_handoff_export` | `test_handoff_constructs_op_and_dispatches` |
| `drc-vendor` | `run` | `drc_vendor` | `test_drc_vendor_run_dispatches` |
| `drc-vendor` | `list` | `list_vendor_drc_profiles` | `test_drc_vendor_list_dispatches` |
| `board-metadata` | `read` | `read_board_metadata` | `test_read_dispatches` |
| `board-metadata` | `set-rev` | `set_board_revision` | `test_set_rev_dispatches` |
| `board-metadata` | `set` | `set_board_metadata` | `test_set_dispatches` |

**9/9 operations covered.** Each dispatch test asserts the captured op dict's `op_type` and key fields. All 4 subcommand names registered (`subcommands-ok`).

## Goal Clause 2: "builds are project-scoped"

### VERIFIED

Two independent mechanisms enforce project scoping:

1. **`ProjectContext.builds_dir`** (`crossfile/project_context.py:54`) resolves to `resolved_root / "builds"` — a **direct child of the resolved project root only**. No upward walk is performed (TM-3). The class docstring (lines 41-43) explicitly states *"No upward walk is performed."*

2. **CLI handlers** derive `project_dir` from `args.pcb.parent` and pass it into each op dict and to `handle_operation(project_dir=...)`. The op executor resolves build paths relative to that project dir. A PCB in project A cannot reach project B's `builds/`.

`fields-ok` confirms `build_spec_files` and `builds_dir` are real `ProjectContext` fields. The discovery glob `**/*.kicad_build_spec.json` is rooted at `resolved_root` (project-scoped).

## Goal Clause 3: "ManufacturerClient ABC is defined for future API adapters"

### VERIFIED

`src/volta/manufacturing/manufacturer_client.py` defines:
- **`ManufacturerClient(ABC)`** with 3 `@abstractmethod`s: `quote()`, `place_order()`, `get_status()` — exact signatures from the plan's CONTEXT spec.
- **3 frozen dataclasses** (`Quote`, `OrderResult`, `OrderStatus`) with the documented fields and defaults.
- **Interface-only:** method bodies are docstrings; no implementation. No concrete subclass in `src/`.
- **No network dependencies:** imports only `abc`, `dataclasses`, `typing`. `abstract-ok`, `frozen-ok`, and the `sys.modules`-delta purity test all pass.
- **Pitfall 8 scope guard** in the class docstring (quote-only-first when activated).
- This is the contract Phase 210 (DEFERRED to v7.1) adapters will implement.

## Must-Haves Checklist (from 209-01-PLAN.md)

| # | Must-have | Status | Evidence |
|---|---|---|---|
| 1 | All 9 new ops appear as MCP tools via `_generate_operation_tools()` — verified, no code change (INTEG-01) | PASS | `mcp-exposure-ok 163`; 0 edit_server.py edits |
| 2 | 4 CLI subcommands exist and route: build, handoff, drc-vendor, board-metadata (INTEG-02) | PASS | `subcommands-ok`; 4 handlers + routing + 13 dispatch tests |
| 3 | ProjectContext exposes build_spec_files and builds_dir; discover_project() populates them (INTEG-03) | PASS | `fields-ok`; glob discovery; 2 tests in test_crossfile_submodules.py |
| 4 | builds_dir resolves to project root's builds/ child (project-scoped) (INTEG-04) | PASS | direct-child resolution, no upward walk |
| 5 | ManufacturerClient ABC importable with no network deps; 3 abstractmethods + 3 frozen dataclasses (INTEG-05, Pitfall 8) | PASS | abstract-ok, frozen-ok, 0 network imports, Pitfall 8 docstring |
| 6 | len(OPERATION_REGISTRY) == 160 and validate_registry_completeness() pass — no new ops (INTEG-06) | PASS | `registry-ok`; count 160; 3 known-missing only |
| 7 | Backward compat: existing ProjectContext(...) callers and existing CLI subcommands unchanged | PASS | defaulted new fields; 12 existing CLI tests pass; 45 crossfile tests pass |

**7/7 must-haves met.**

## Success Criteria (from ROADMAP Phase 209)

| # | Criterion | Status |
|---|---|---|
| 1 | All new operations callable via MCP tools and CLI subcommands | PASS — 9/9 ops on both surfaces |
| 2 | ProjectContext discovers builds/ and .kicad_build_spec.json sidecars | PASS — both fields populated by discover_project() |
| 3 | ManufacturerClient ABC defined with quote(), place_order(), get_status() — no network libs | PASS — 3 abstractmethods, pure stdlib |
| 4 | Registry count assertion and validate_registry_completeness() pass | PASS — 160 ops, completeness green |

**4/4 success criteria met.**

## Test Gate Results

```
$ .venv/bin/python -m pytest tests/test_manufacturer_client.py tests/test_cli_integration.py \
    tests/test_mcp_tools.py -q --tb=short -o addopts="" -o pythonpath="src tests" \
    -W "ignore::pytest.PytestUnraisableExceptionWarning"
............................... [100%]
31 passed in 1.37s

$ .venv/bin/python -m pytest tests/test_crossfile_submodules.py tests/test_registry.py ...
............................................. [100%]
45 passed in 0.10s

$ .venv/bin/python -m pytest tests/test_cli.py ...
............ [100%]
12 passed in 4.43s
```

**88 tests pass across the Phase 209 + regression surface.** Zero failures.

## Scope Integrity (no scope creep)

`git diff 65d90e9..HEAD --stat` for the guarded files returns **empty**:
- `src/volta/ops/registry.py` — unchanged
- `src/volta/ops/schema.py` — unchanged
- `src/volta/ops/handlers/` — unchanged
- `src/volta/mcp/edit_server.py` — unchanged

Phase 209 added exactly: 1 new module (ManufacturerClient ABC), 4 CLI handlers, 2 ProjectContext fields, 4 test files. Zero new ops, zero new handlers, zero schema changes. The integration-only mandate is honored.

## Verdict

**PASS.** The phase goal — *"All new operations callable via MCP and CLI; builds project-scoped; ManufacturerClient ABC defined for future API adapters"* — is fully and verifiably met. All 7 must-haves and all 4 ROADMAP success criteria are satisfied with a green 88-test gate. The v7.0 milestone is functionally complete.
