bretbouchard/kicad-agent/.planning/phases/207-versioned-build-system/207-VERIFICATION.md

# Phase 207 — Phase Goal Verification

**Verifier:** phase-goal-verifier agent
**Date:** 2026-07-10
**Phase:** 207-versioned-build-system
**Verdict:** PASS

## Phase Goal

> User can create a versioned build that snapshots source files, records git SHA + board revision, and serializes a manifest with SHA256-hashed artifacts to disk.

## Must-Haves Check (from 207-01-PLAN.md)

| # | Must-Have | Status | Evidence |
|---|---|---|---|
| 1 | `Build` frozen dataclass with all BUILD-02 fields | PASS | `manufacturing/build.py:54-80` — `@dataclass(frozen=True) class Build` with build_id, board_rev, source_files (tuple), git_sha, created_at, status, artifacts (tuple), manifest_path, build_dir |
| 2 | `BuildStatus` enum (DRAFT/VALIDATED/EXPORTED/HANDED_OFF) with `transition_to` via `replace` | PASS | `build.py:26-41` enum; `build.py:82-96` `transition_to` uses `replace(self, status=new_status)`; `build.py:46-51` `_ALLOWED_TRANSITIONS`; full-chain + disallowed tests pass |
| 3 | `ManufacturingManifest.to_json/save/load` + `ManufacturingArtifact.to_dict/from_dict` round-trip lossless | PASS | `manufacturing_manifest.py:89-134` (manifest), `47-72` (artifact); `test_manifest_to_json_round_trip` + `test_artifact_to_from_dict` pass |
| 4 | `build_create` creates `builds/v{rev}_{timestamp}/` with manifest + source snapshots | PASS | `handlers/build.py:96-104` dir creation, `106-122` snapshot loop; `test_build_create_creates_directory` + `test_build_create_snapshots_source_files` pass |
| 5 | `build_create` returns error + NO build dir if PCB fails to parse | PASS | `handlers/build.py:162-170` except block rmtree's build_dir; `test_build_create_no_partial_state_on_parse_failure` asserts `not (tmp_path / "builds").exists()` |
| 6 | `build_list` returns all builds for a project | PASS | `handlers/build.py:211-252`; 4 tests pass (returns/empty/corrupt/sort) |
| 7 | `build_show` returns build details by build_id | PASS | `handlers/build.py:255-316`; 6 tests pass |
| 8 | `diff_builds()` utility comparing two Build records | PASS | `build.py:187-206`; `test_diff_builds_detects_changes` + `test_diff_builds_identical` pass |
| 9 | `builds/` in `.gitignore` | PASS | `.gitignore:9` `builds/`; `.gitignore:7` `build/` (singular) preserved |
| 10 | Registry count 159; readonly set +3 ops | PASS | `test_registry.py:26` `== 159`; `test_registry.py:118-120` readonly set includes build_create/list/show |
| 11 | Target `.kicad_pcb` byte-identical after `build_create` | PASS | `test_build_create_target_file_unchanged` asserts hash + `st_mtime_ns` unchanged |

All 11 must-haves verified PASS.

## Success Criteria Check (from ROADMAP.md)

### SC-1: `build_create` produces a build record with build_id, board_rev (from title_block), git_sha (HEAD), timestamp; build directory created

**PASS.**

- `build_id`: generated via `str(uuid.uuid4())` at `handlers/build.py:90`. `test_build_create_generates_uuid` asserts UUID4 format (8-4-4-4-12).
- `board_rev`: read via `NativeParser.parse_pcb(file_path).title_block.rev` at `handlers/build.py:76-81` (correct dual-path re-parse, since query-path `ir._native_board` is None). `test_build_create_reads_board_rev` confirms `"2.3"` round-trips.
- `git_sha`: captured via `_get_git_sha(project_dir)` at `handlers/build.py:87`. `test_build_create_records_git_sha` asserts it is a non-empty string; `test_git_sha_from_repo` confirms real SHA; `test_git_sha_unknown_when_not_a_repo` confirms `"unknown"` sentinel.
- `timestamp`: `created_at = now.isoformat()` at `handlers/build.py:92`.
- `build directory created`: `builds/v{safe_rev}_{dir_timestamp}/` at `handlers/build.py:96-104`. `test_build_create_creates_directory` confirms dir + manifest.json + build.json + snapshot exist.

### SC-2: `build_create` on a board that fails validation → clear error, NO build created

**PASS (with caveat).**

- Parse-failure path: `NativeParser.parse_pcb` raises `FileNotFoundError` for missing files; caught by the `except Exception` block at `handlers/build.py:162-170`, which rmtree's the build dir and returns `{"success": False, "error": ...}`. `test_build_create_no_partial_state_on_parse_failure` asserts `result["success"] is False` AND `not (tmp_path / "builds").exists()`.
- Caveat: the "fails validation" arm via the full `ManufacturingReadinessGate` is NOT tested because the full gate is deferred to Phase 208 (CONTEXT.md explicit decision). Phase 207 always produces `DRAFT` status (the PCB-parse check is the validation). This is an honest scoping decision — DRAFT status means "not fully validated." The no-partial-state contract (rmtree on failure) is in place for when Phase 208 adds the real gate.

### SC-3: manifest.json serialized with SHA256 hashes; build_show reproduces the build record

**PASS.**

- SHA256 hashing: `ManufacturingArtifact.from_file` (`manufacturing_manifest.py:33-45`) computes `hashlib.sha256(data).hexdigest()`. `test_build_create_snapshots_source_files` re-hashes the snapshot copy and asserts it matches `result["artifacts"][...]["sha256"]`.
- Serialization: `manifest.save(build_dir / "manifest.json")` at `handlers/build.py:134` + `build.save(build_dir / "build.json")` at line 148. Two-file approach (manifest.json = manufacturing subset, build.json = full envelope).
- Round-trip reproduction: `build_show` calls `Build.load(build_dir / "build.json")` and returns the fields. `test_build_create_build_json_round_trip` confirms `Build.load` reproduces `build_id`, `board_rev`, `status`, `build_dir`. `test_build_show_round_trip_manifest` confirms `result["manifest"] is not None` and artifact count matches source count.

### SC-4: build_list shows all builds with status

**PASS.**

- `_handle_build_list` scans `builds/v*_*`, loads each `build.json` via `Build.load`, and returns summaries with `status: build.status.value`. `test_build_list_returns_builds` creates 2 builds and asserts `count == 2` with both build_ids present. `test_build_list_sorted_descending` confirms most-recent-first ordering.

### SC-5: builds/ in .gitignore

**PASS.**

- `.gitignore:9` contains `builds/`. `.gitignore:7` retains `build/` (singular, Python artifacts). Verified by reading the file.

## Pytest Results

```
tests/test_build_system.py + tests/test_registry.py: 73 passed
tests/test_manufacturing_gate.py + tests/test_board_metadata_ops.py: 42 passed
```

Registry completeness: `extra_in_registry: []`, `missing_from_registry: [add_design_note, apply_floor_plan, place_and_wire_power_units]` (all pre-existing, none from Phase 207).

## Goal Achievement

The phase goal — "User can create a versioned build that snapshots source files, records git SHA + board revision, and serializes a manifest with SHA256-hashed artifacts to disk" — is fully met:

1. **Snapshots source files:** `build_create` discovers `.kicad_pcb`/`.kicad_sch`/`.kicad_pro` by stem, `shutil.copy2`'s them into `builds/v{rev}_{timestamp}/`. Tested.
2. **Records git SHA:** `_get_git_sha` captures HEAD SHA (or `"unknown"`). Tested for both repo and non-repo.
3. **Records board revision:** `NativeParser.parse_pcb(...).title_block.rev`. Tested with rev `"2.3"`.
4. **Serializes a manifest with SHA256-hashed artifacts:** `manifest.save` + `ManufacturingArtifact.from_file` (sha256). Round-trip lossless via `build_show`/`Build.load`. Tested.

## Findings

No blocking findings. The medium finding (absolute-path project_dir not rejected — see 207-REVIEW.md COR-MED-1) does not affect goal achievement because it is a hardening gap, not a functional gap. The goal is met for all valid project_dir inputs.

## Verdict

**PASS.** All 11 must-haves verified. All 5 success criteria met. The phase goal is achieved.
