bretbouchard/kicad-agent/.planning/phases/194-mutation-testing/194-01-PLAN.md

---
phase: 194-mutation-testing
plan: 01
type: execute
wave: 4
depends_on: [193-01]
files_modified: [.github/workflows/mutation.yml, scripts/mutation-runner.sh, Tests/MutationTests/MutationConfig.swift]
autonomous: true
requirements: [TEST-05]
user_setup:
  - service: mull-xcode
    why: "Mutation testing requires Mull installation"
    env_vars:
      - name: MULL_XCODE_PATH
        source: "brew install mull"
    dashboard_config:
      - task: "Install Mull mutation testing framework"
        location: "brew install mull"
---

<objective>
Implement mutation testing via mull-xcode with >90% score enforced in CI. Mutations test critical paths (daemon communication, state machine, verification gates).

Purpose: Mutation testing catches logic gaps coverage misses. Mull mutates source code (e.g., `==` → `!=`), runs tests, and reports killed mutants. Score >90% required to merge ensures tests effectively validate code behavior.

Output: Mull installed via brew, CI mutation workflow, >90% score enforced, killed mutants reported per PR, mutation score trends tracked.
</objective>

<execution_context>
@$HOME/.claude/get-shit-done/workflows/execute-plan.md
@$HOME/.claude/get-shit-done/templates/summary.md
</execution_context>

<context>
@.planning/PROJECT.md
@.planning/ROADMAP.md
@.planning/STATE.md
@.planning/research/v6/STACK.md
@.planning/research/v6/ARCHITECTURE.md
@.planning/phases/193-property-based-testing/193-01-PLAN.md
</context>

<interfaces>
<!-- Mull from STACK.md -->
From .planning/research/v6/STACK.md:
```bash
# mull-xcode installation
brew install mull

# mull-xcode usage
mull-cxx -test-framework=SwiftTesting --coverage-info=coverage.info

# Mutation score >90% enforced in CI
```
</interfaces>

<tasks>

<task type="checkpoint:human-action" gate="blocking">
  <what-built>Mull mutation testing framework installation and CI configuration</what-built>
  <how-to-verify>
1. Install Mull via Homebrew: `brew install mull`
2. Verify installation: `mull-cxx --version` (should show Mull version)
3. Test basic mutation run: `mull-cxx -test-framework=SwiftTesting --help`
4. Check PATH: `which mull-cxx` (should return /usr/local/bin/mull-cxx)
5. If brew install fails (e.g., no Homebrew), install from source: https://github.com/mull-project/moll
  </how-to-verify>
  <resume-signal>Type "mull-installed" to continue with CI workflow setup</resume-signal>
</task>

<task type="auto">
  <name>Task 1: Create mutation testing CI workflow</name>
  <files>.github/workflows/mutation.yml</files>
  <action>Create .github/workflows/mutation.yml with mutation testing pipeline:
```yaml
name: Mutation Testing
on: [pull_request]

jobs:
  mutation:
    runs-on: macos-26
    steps:
      - uses: actions/checkout@v4
      
      - name: Install Mull
        run: brew install mull
      
      - name: Generate coverage info
        run: swift test --enable-code-coverage
      
      - name: Run mutation tests
        run: |
          mull-cxx \
            -test-framework=SwiftTesting \
            --coverage-info=.build/debug/codecov/*.profdata \
            --mutate-killed-threshold=90 \
            --mutate-score-threshold=90 \
            --reporters=IDE,JSON \
            --output=mutation-results.json
      
      - name: Enforce 90% mutation score
        run: |
          SCORE=$(jq -r '.mutation_score' mutation-results.json)
          if (( $(echo "$SCORE < 90" | bc -l) )); then
            echo "Mutation score $SCORE% is below 90%"
            jq '.killed_mutants' mutation-results.json
            exit 1
          fi
      
      - name: Upload mutation results
        uses: actions/upload-artifact@v4
        with:
          name: mutation-results
          path: mutation-results.json
```
This enforces TEST-05 requirement (>90% mutation score required to merge).</action>
  <verify>gh workflow view mutation shows workflow file, YAML syntax valid, mull-cxx command references correct flags</verify>
  <done>Mutation CI workflow created with 90% threshold enforcement, results artifact uploaded per PR</done>
</task>

<task type="auto">
  <name>Task 2: Create mutation runner script</name>
  <files>scripts/mutation-runner.sh</files>
  <action>Create scripts/mutation-runner.sh as local development helper:
```bash
#!/usr/bin/env bash
# Mutation testing runner for local development

set -euo pipefail

echo "=== Running mutation tests with mull-xcode ==="

# Generate coverage first (required for mutation targeting)
swift test --enable-code-coverage

# Run mutation tests
mull-cxx \
  -test-framework=SwiftTesting \
  --coverage-info=.build/debug/codecov/*.profdata \
  --mutate-killed-threshold=90 \
  --mutate-score-threshold=90 \
  --reporters=IDE,JSON,HTML \
  --output=mutation-results.json \
  --output-dir=mutation-report

# Check score
SCORE=$(jq -r '.mutation_score' mutation-results.json)
echo "Mutation score: $SCORE%"

if (( $(echo "$SCORE < 90" | bc -l) )); then
  echo "❌ Mutation score $SCORE% is below 90%"
  echo "Killed mutants:"
  jq '.killed_mutants | .[] | select(.status == "survived")' mutation-results.json
  exit 1
else
  echo "✅ Mutation score $SCORE% meets 90% threshold"
fi

echo "=== Mutation report: mutation-report/index.html ==="
```
Make executable: `chmod +x scripts/mutation-runner.sh`</action>
  <verify>./scripts/mutation-runner.sh runs locally, generates HTML report, exits with correct code on score threshold</verify>
  <done>Mutation runner script created, executable permission set, local development workflow validated</done>
</task>

<task type="auto">
  <name>Task 3: Create mutation configuration for critical paths</name>
  <files>Tests/MutationTests/MutationConfig.swift</files>
  <action>Create Tests/MutationTests/MutationConfig.swift to configure which code gets mutated:
```swift
import Foundation

/// Mutation testing configuration per TEST-05
/// Focuses on critical paths: daemon communication, state machine, verification gates
enum MutationConfig {
    /// Files to mutate (critical paths only)
    static let targetFiles = [
        "Daemon/DaemonMCPClient.swift",
        "Governance/StateMachine.swift",
        "Governance/VerificationGates.swift",
        "Governance/GateRunner.swift",
        "Generative/PipelineOrchestrator.swift"
    ]
    
    /// Mutators to enable (avoid over-mutating constants)
    static let mutators = [
        "cxx_eq_to_ne",      // == → !=
        "cxx_ne_to_eq",      // != → ==
        "cxx_lt_to_le",      // < → ≤
        "cxx_gt_to_ge",      // > → ≥
        "cxx_logical_and_to_or",  // && → ||
        "cxx_logical_or_to_and",   // || → &&
        "math_mul_to_div",   // * → /
        "math_add_to_sub",   // + → -
        "remove_void_call"   // Remove function calls with no return value
    ]
    
    /// Minimum score threshold (enforced in CI)
    static let minimumScore = 90.0
    
    /// Killed mutants reported per PR
    static func reportKilledMutants(from resultsFile: String) {
        // Load mutation-results.json, extract killed mutants
        // Format for PR comment: which mutants killed by which tests
    }
}
```
This focuses mutation testing on critical paths (daemon, state machine, gates) per TEST-05.</action>
  <verify>swift build compiles MutationConfig.swift, targetFiles list references existing files from ARCHITECTURE.md</verify>
  <done>Mutation configuration created, targets critical paths, mutators defined to avoid over-mutating constants</done>
</task>

<task type="auto">
  <name>Task 4: Add mutation score trend tracking</name>
  <files>.github/workflows/mutation.yml, scripts/mutation-runner.sh</files>
  <action>Update .github/workflows/mutation.yml to track score trends:
```yaml
- name: Track mutation score trend
  run: |
    SCORE=$(jq -r '.mutation_score' mutation-results.json)
    echo "MUTATION_SCORE=$SCORE" >> $GITHUB_ENV
    
    # Store in history (append to trends file)
    echo "{\"date\":\"$(date -u +%Y-%m-%dT%H:%M:%SZ)\",\"score\":$SCORE,\"sha\":\"${{ github.sha }}\"}" >> mutation-trends.jsonl
    
    # Comment on PR with trend
    gh pr comment ${{ github.event.pull_request.number }} --body "Mutation score: $SCORE% (threshold: 90%)"
```
And add to scripts/mutation-runner.sh:
```bash
# Append to local trend history
echo "{\"date\":\"$(date -u +%Y-%m-%dT%H:%M:%SZ)\",\"score\":$SCORE,\"sha\":\"$(git rev-parse HEAD)\"}" >> mutation-trends.jsonl
```
This tracks mutation scores over time to detect quality regressions (TEST-05).</action>
  <verify>Mutation trend file created/updated on each run, PR comments include mutation score, JSONL format valid</verify>
  <done>Mutation score trend tracking implemented, PR comments include scores, JSONL history maintained for regression detection</done>
</task>

</tasks>

<threat_model>
## STRIDE Threat Register

| Threat ID | Category | Component | Disposition | Mitigation Plan |
|---|---|---|---|---|
| T-194-01 | I | mull-xcode installation | mitigate | Install via Homebrew (verified source), check SHA256 of binary, use official Mull repository |
| T-194-02 | D | Mutation engine code generation | mitigate | Run mutations in sandboxed environment, limit runtime (5min timeout), restrict file system writes to .build directory |
| T-194-03 | E | Mutated binary execution | mitigate | Execute in containerized macOS runner, network disabled during mutation runs, validate syscall patterns |
| T-194-04 | T | Score threshold bypass | mitigate | Use bc for floating-point comparison (not string), double-check threshold in CI + script, require branch protection for workflow edits |
| T-194-05 | R | Mutation test rollback | mitigate | Keep mutation results in git history, tag releases with mutation score, rollback if score drops >5% |

## Adversarial Scenario

An attacker submits malicious code that passes tests but introduces a vulnerability when mutated (e.g., authentication check that passes unit tests but fails when `==` → `!=`). Mitigation: Mutation testing fuzzes ALL comparison operators, so the vulnerable auth check would be mutated to `!=` and tests would fail (killing the mutant). The 90% threshold ensures high-quality tests catch such mutations before merge. Score trend tracking detects gradual degradation (attacks that sneak in via multiple small PRs).

</threat_model>

<verification>
1. Mull installed successfully (mull-cxx --version shows version)
2. Mutation workflow triggers on PR
3. Coverage info generated before mutation run
4. Mutation tests run with 90% threshold
5. Build fails if mutation score below 90%
6. Killed mutants reported per PR
7. Mutation score trend tracked over time
8. Local mutation runner script works
9. HTML report generated for debugging
</verification>

<success_criteria>
- mull-xcode installed via brew
- CI mutation workflow enforces >90% score
- Killed mutants reported per PR with test attribution
- Mutation score trends tracked (detect quality regression)
- Critical paths covered (daemon, state machine, verification gates)
- Retroactively apply to existing governance code (phases 169-170)
- HTML mutation report generated for debugging
</success_criteria>

<output>
After completion, create `.planning/phases/194-mutation-testing/194-01-SUMMARY.md`
</output>
