bretbouchard/kicad-agent/tests/fixtures/ltspice/basic_rc.asc

C1: cap; 100n
R1: res; 1k
V1: voltage; 5
Named nets: 0
.tran 0 1ms 0 1u
