bretbouchard/kicad-agent/src/volta/ops/schema.py

"""Pydantic v2 operation schema -- the JSON contract the LLM uses to express edit intents.

Design decisions (from CONTEXT.md):
  D-01: One Pydantic model per operation type (not a generic dict).
  D-02: Atomic operations -- one mutation per operation, no compound ops.
  D-03: Single file per operation via ``target_file`` field.
  D-04: Export full JSON Schema via ``model_json_schema()`` for LLM consumption.

Security mitigations (Council review):
  H-01: TargetFile type rejects path traversal (``..``), absolute paths,
        null bytes, and non-KiCad extensions.
  M-04: All string fields enforce min_length / max_length to prevent abuse.

Usage::

    from volta.ops import Operation

    op = Operation.model_validate({
        "root": {
            "op_type": "add_component",
            "target_file": "motor-driver.kicad_sch",
            "library_id": "Device:R_Small_US",
            "position": {"x": 50.0, "y": 30.0},
        }
    })

    # Export schema for LLM tool contract
    schema = op.model_json_schema()
"""

from pathlib import Path
from typing import Annotated, Literal, Optional
import re

from pydantic import BaseModel, BeforeValidator, Field, field_validator


# ---------------------------------------------------------------------------
# Shared validators (Council H-1, H-2: S-expression safety constraints)
# ---------------------------------------------------------------------------

# Safe characters for KiCad identifiers: alphanumeric, underscore, dash, colon, dot, hash
_SAFE_ID_PATTERN = r'^[A-Za-z0-9_\-:.#+/]+$'


def _validate_safe_identifier(v: str, field_name: str) -> str:
    """Reject strings containing characters unsafe for S-expression output."""
    if not re.match(_SAFE_ID_PATTERN, v):
        raise ValueError(
            f"{field_name} contains unsafe characters. "
            f"Allowed: alphanumeric, underscore, dash, colon, dot, hash, forward slash."
        )
    return v


_UNSAFE_SEXPR_CHARS = re.compile(r'[\(\)\"\n]')


def _validate_sexpr_safe_string(v: str) -> str:
    """Reject strings containing characters that break S-expression parsing."""
    if _UNSAFE_SEXPR_CHARS.search(v):
        raise ValueError(
            "Value contains unsafe S-expression characters "
            "(parentheses, quotes, or newlines)"
        )
    return v


# ---------------------------------------------------------------------------
# Shared field types
# ---------------------------------------------------------------------------


class PositionSpec(BaseModel):
    """Position specification for place operations.

    Attributes:
        x: X coordinate in mm.
        y: Y coordinate in mm.
        angle: Rotation angle in degrees (default 0).
    """

    x: float
    y: float
    angle: float = 0.0

    @field_validator("x", "y", "angle")
    @classmethod
    def _reject_non_finite(cls, v: float) -> float:
        import math
        if math.isnan(v) or math.isinf(v):
            raise ValueError("Coordinate values must be finite (not NaN or Infinity)")
        return v


class PropertySpec(BaseModel):
    """A named property with a string value.

    Attributes:
        name: Property key (e.g. ``"Value"``, ``"Footprint"``).
        value: Property value string.
    """

    name: str = Field(min_length=1, max_length=128)
    value: str = Field(max_length=1024)


class PinSpec(BaseModel):
    """Pin definition for symbol creation.

    Attributes:
        number: Pin number (e.g. ``"1"``, ``"A1"``).
        name: Pin name (e.g. ``"VCC"``, ``"DOUT"``).
        electrical_type: KiCad pin electrical type.
        position: Pin position relative to symbol origin.
        length: Pin length in mm (default 2.54).
        graphical_style: Pin graphical style.
        hide: Whether the pin is hidden.
    """

    number: str = Field(min_length=1, max_length=32, description="Pin number")
    name: str = Field(min_length=1, max_length=128, description="Pin name")
    electrical_type: Literal[
        "input", "output", "bidirectional", "tri_state", "passive",
        "free", "unspecified", "power_in", "power_out",
        "open_collector", "open_emitter", "no_connect",
    ] = Field(default="passive", description="Pin electrical type")
    position: PositionSpec
    length: float = Field(default=2.54, gt=0, le=50, description="Pin length in mm")
    graphical_style: Literal[
        "line", "inverted", "clock", "inverted_clock",
        "input_low", "clock_low", "output_low", "edge_clock_high",
        "non_logic",
    ] = Field(default="line", description="Pin graphical style")
    hide: bool = Field(default=False, description="Whether pin is hidden")


# ---------------------------------------------------------------------------
# TargetFile -- path-safe type (Council H-01)
# ---------------------------------------------------------------------------


def _validate_target_file(v: str) -> str:
    """Reject path traversal, absolute paths, null bytes, and non-KiCad extensions."""
    if "\x00" in v:
        raise ValueError("target_file contains null bytes")
    if v.startswith("/"):
        raise ValueError("target_file must be a relative path")
    parts = Path(v).parts
    if ".." in parts:
        raise ValueError("target_file must not contain '..' path traversal")
    valid_extensions = (
        ".kicad_sch", ".kicad_pcb", ".kicad_sym", ".kicad_mod",
        ".kicad_dru", ".kicad_pro",
    )
    valid_names = ("sym-lib-table", "fp-lib-table")
    if not v.endswith(valid_extensions) and Path(v).name not in valid_names:
        raise ValueError("target_file must be a KiCad file type")
    return v


TargetFile = Annotated[
    str,
    Field(min_length=1, max_length=512),
    BeforeValidator(_validate_target_file),
]


# ---------------------------------------------------------------------------
# Re-export Op classes from sub-modules
# ---------------------------------------------------------------------------

from volta.ops._schema_component import (  # noqa: E402
    AddComponentOp,
    RemoveComponentOp,
    MoveComponentOp,
    SnapComponentsToGridOp,
    ModifyPropertyOp,
    DuplicateComponentOp,
    ArrayReplicateOp,
    SwapSymbolOp,
)
from volta.ops._schema_net import (  # noqa: E402
    AddNetOp,
    RemoveNetOp,
    RenameNetOp,
)
from volta.ops._schema_reference import (  # noqa: E402
    RenumberRefsOp,
    ValidateRefsOp,
    AnnotateOp,
    SafeAnnotateOp,
    CrossRefCheckOp,
)
from volta.ops._schema_footprint import (  # noqa: E402
    AssignFootprintOp,
    SwapFootprintOp,
    ValidateFootprintOp,
    VerifyPinMapOp,
    UpdateFootprintFromLibraryOp,
)
from volta.ops._schema_wire import (  # noqa: E402
    AddWireOp,
    AddLabelOp,
    AddPowerOp,
    AddNoConnectOp,
    AddJunctionOp,
    AddPowerFlagOp,
    RenameNetLabelOp,
)
from volta.ops._schema_annotation import (  # noqa: E402
    AddDesignNoteOp,
)
from volta.ops._schema_floorplan import (  # noqa: E402
    ApplyFloorPlanOp,
)
from volta.ops._schema_remove import (  # noqa: E402
    RemoveWireOp,
    RemoveLabelOp,
    RemoveLabelsOp,
    RemoveJunctionOp,
    RemoveNoConnectOp,
)
from volta.ops._schema_autolayout import (  # noqa: E402
    PlaceComponentsSchOp,
    RouteWiresSchOp,
    ApplyLabelsSchOp,
    AutoLayoutSchOp,
)
from volta.ops._schema_query import (  # noqa: E402
    QueryConnectivityOp,
)
from volta.ops._schema_library import (  # noqa: E402
    AddLibEntryOp,
    RemoveLibEntryOp,
    ListLibEntriesOp,
    UpdateSymbolsFromLibraryOp,
)
from volta.ops._schema_pcb import (  # noqa: E402
    AddNetClassOp,
    AddDesignRuleOp,
    AddCopperZoneOp,
    SetBoardOutlineOp,
    AssignNetClassOp,
    AutoRouteOp,
    ModifyNetClassOp,
    RemoveNetClassOp,
    ListNetClassesOp,
    ModifyDesignRuleOp,
    RemoveDesignRuleOp,
    ListDesignRulesOp,
    ModifyProjectSettingsOp,
    ModifyCopperZoneOp,
    RemoveCopperZoneOp,
    DeleteCopperZoneOp,
    RefillCopperZoneOp,
    ModifyZonePolygonOp,
    AddKeepoutAreaOp,
    AddZoneKeepoutOp,
    RemoveKeepoutAreaOp,
    MoveFootprintOp,
    BatchExpandFootprintsOp,
    RouteDiffPairOp,
    MatchLengthsOp,
    AnalyzeSplitPlaneOp,
    FixSilkscreenOverCopperOp,
    ImportSesOp,
    AutoRouteManhattanOp,
    AddTrackOp,
    AddArcTrackOp,
    AddViaOp,
    DeleteTrackOp,
    DeleteViaOp,
    MoveTrackEndpointOp,
    LockTrackOp,
    LockViaOp,
    AddStitchingViaPatternOp,
    StitchPowerNetsOp,
    PlaceComponentOp,
    ReadBoardMetadataOp,
    SetBoardMetadataOp,
    SetBoardRevisionOp,
    DrcVendorOp,
    ListVendorDrcProfilesOp,
    BuildCreateOp,
    BuildListOp,
    BuildShowOp,
    BuildHandoffExportOp,
)
from volta.ops._schema_placement import (  # noqa: E402
    AutoPlaceOp,
    ExportPositionsOp,
    ImportPositionsOp,
    AutoPlaceZonedOp,
    ZoneDefinition,
)
from volta.ops._schema_validation import (  # noqa: E402
    ValidatePowerNetsOp,
    ValidateSchematicOp,
    PrePcbSchematicGateOp,
    ParseErcOp,
    ExtractViolationPositionsOp,
    ValidateHlabelsOp,
)
from volta.ops._schema_gate import (  # noqa: E402
    RunGateCheckOp,
    GateStatusOp,
)
from volta.ops._schema_circuit_ir import ConvertToSkidlOp, ConvertFromSkidlOp  # noqa: E402
from volta.ops._schema_create import (  # noqa: E402
    CreateSchematicOp,
    CreatePcbOp,
    CreateProjectOp,
    CreateSymbolOp,
    ImportSymbolOp,
    EmbedSymbolOp,
    CreateFootprintOp,
    FootprintPadSpec,
    ConvertKicad6To10Op,
)
from volta.ops._schema_repair import (  # noqa: E402
    RepairSchematicOp,
    SnapToGridOp,
    FixShortedNetsOp,
    FixPinTypeMismatchesOp,
    PlaceMissingUnitsOp,
    PlaceAndWirePowerUnitsOp,
    RemoveDanglingWiresOp,
    BreakWireShortsOp,
    ResolveShortedNetsOp,
    FixNetShortOp,
)
# ErcAutoFixOp migrated to _schema_erc_smart.py (Council H-02: atomic schema migration)
from volta.ops._schema_sheet import (  # noqa: E402
    AddSheetOp,
    AddSheetPinOp,
    NavigateSheetsOp,
    RebuildRootSheetOp,
)
from volta.ops._schema_crossfile import (  # noqa: E402
    PropagateSymbolChangeOp,
    UpdatePcbFromSchematicOp,
    RepopulatePcbFromSchematicOp,
    SafeSyncPcbFromSchematicOp,
    RebuildPcbNetsOp,
)
from volta.ops._schema_schematic_routing import (  # noqa: E402
    BatchConnectOp,
    ConnectPinsOp,
    DetectPinOverlapsOp,
    DetectRoutingCollisionsOp,
    GlobalLabelSpec,
    NetDef,
    PinRef,
    CollisionZone,
    RegenerateWiringOp,
    ResolvePinPositionsOp,
    PlaceNetLabelsOp,
)
from volta.ops._schema_schematic_intel import (  # noqa: E402
    ExtractNetsOp,
    DetectNetConflictsOp,
    DetectNetShortsOp,
    SuggestNetNamesOp,
    InferConnectivityOp,
    AnalyzeGroundTopologyOp,
    TraceNetFromLabelOp,
)
from volta.ops._schema_erc_smart import (  # noqa: E402
    ClassifyViolationsOp,
    DiagnoseViolationsOp,
    ErcAutoFixHierarchicalOp,
    ErcAutoFixOp,
)
from volta.ops._schema_readability import (  # noqa: E402
    ReviewSchematicOp,
)
from volta.ops._schema_critique import (  # noqa: E402
    CritiqueSchOp,
)
from volta.ops._schema_gap import (  # noqa: E402
    AnalyzeGapsOp,
    FillGapsOp,
    FillZonesOp,
    StripShortsOp,
    RemoveDanglingTracksOp,
    AutoRouteFreeroutingOp,
    GenerateBomOp,
)
from volta.ops.handlers.pcb_transfer import (  # noqa: E402
    UpdateFromSchematicOp,
)
from volta.ops.handlers.constraint_handlers import (  # noqa: E402
    SetConstraintsOp,
    GetConstraintsOp,
)


# ---------------------------------------------------------------------------
# Discriminated union (D-01, D-02, D-03)
# ---------------------------------------------------------------------------


class Operation(BaseModel):
    """Discriminated union of all operation types.

    Per D-02: each operation is atomic (one mutation).
    Per D-03: each operation targets one file via ``target_file``.
    Per D-04: export full JSON Schema via ``model_json_schema()``.
    """

    root: Annotated[
        AddComponentOp
        | RemoveComponentOp
        | MoveComponentOp
        | SnapComponentsToGridOp
        | ModifyPropertyOp
        | DuplicateComponentOp
        | ArrayReplicateOp
        | AddNetOp
        | RemoveNetOp
        | RenameNetOp
        | RenumberRefsOp
        | ValidateRefsOp
        | AnnotateOp
        | SafeAnnotateOp
        | CrossRefCheckOp
        | AssignFootprintOp
        | SwapFootprintOp
        | ValidateFootprintOp
        | VerifyPinMapOp
        | UpdateFootprintFromLibraryOp
        | AddWireOp
        | AddLabelOp
        | AddPowerOp
        | AddNoConnectOp
        | AddJunctionOp
        | AddDesignNoteOp
        | ApplyFloorPlanOp
        | AddLibEntryOp
        | RemoveLibEntryOp
        | AddNetClassOp
        | AddDesignRuleOp
        | RepairSchematicOp
        | ValidatePowerNetsOp
        | ValidateSchematicOp
        | PrePcbSchematicGateOp
        | ParseErcOp
        | ExtractViolationPositionsOp
        | ValidateHlabelsOp
        | ConvertKicad6To10Op
        | ConvertToSkidlOp
        | ConvertFromSkidlOp
        | SnapToGridOp
        | AddPowerFlagOp
        | RebuildRootSheetOp
        | AddCopperZoneOp
        | SetBoardOutlineOp
        | AssignNetClassOp
        | AutoRouteOp
        | CreateSchematicOp
        | CreatePcbOp
        | CreateProjectOp
        | CreateSymbolOp
        | ImportSymbolOp
        | EmbedSymbolOp
        | SwapSymbolOp
        | RemoveWireOp
        | RemoveLabelOp
        | RemoveLabelsOp
        | RemoveJunctionOp
        | RemoveNoConnectOp
        | RenameNetLabelOp
        | AddSheetOp
        | AddSheetPinOp
        | NavigateSheetsOp
        | QueryConnectivityOp
        | CreateFootprintOp
        | PropagateSymbolChangeOp
        | ListLibEntriesOp
        | ModifyNetClassOp
        | RemoveNetClassOp
        | ListNetClassesOp
        | ModifyDesignRuleOp
        | RemoveDesignRuleOp
        | ListDesignRulesOp
        | ModifyProjectSettingsOp
        | UpdateSymbolsFromLibraryOp
        | FixShortedNetsOp
        | FixPinTypeMismatchesOp
        | FixNetShortOp
        | PlaceMissingUnitsOp
        | PlaceAndWirePowerUnitsOp
        | RemoveDanglingWiresOp
        | BreakWireShortsOp
        | ResolveShortedNetsOp
        | PlaceNetLabelsOp
        | ErcAutoFixOp
        | ErcAutoFixHierarchicalOp
        | ModifyCopperZoneOp
        | RemoveCopperZoneOp
        | DeleteCopperZoneOp
        | RefillCopperZoneOp
        | ModifyZonePolygonOp
        | AddKeepoutAreaOp
        | AddZoneKeepoutOp
        | RemoveKeepoutAreaOp
        | MoveFootprintOp
        | ResolvePinPositionsOp
        | DetectRoutingCollisionsOp
        | DetectPinOverlapsOp
        | ConnectPinsOp
        | BatchConnectOp
        | RegenerateWiringOp
        | ExtractNetsOp
        | DetectNetConflictsOp
        | DetectNetShortsOp
        | SuggestNetNamesOp
        | InferConnectivityOp
        | AnalyzeGroundTopologyOp
        | TraceNetFromLabelOp
        | ClassifyViolationsOp
        | DiagnoseViolationsOp
        | ReviewSchematicOp
        | CritiqueSchOp
        | UpdatePcbFromSchematicOp
        | RepopulatePcbFromSchematicOp
        | SafeSyncPcbFromSchematicOp
        | RebuildPcbNetsOp
        | RouteDiffPairOp
        | MatchLengthsOp
        | AnalyzeSplitPlaneOp
        | FixSilkscreenOverCopperOp
        | BatchExpandFootprintsOp
        | AutoPlaceOp
        | ExportPositionsOp
        | ImportPositionsOp
        | AutoPlaceZonedOp
        | ImportSesOp
        | AutoRouteManhattanOp
        | AddTrackOp
        | AddArcTrackOp
        | AddViaOp
        | DeleteTrackOp
        | DeleteViaOp
        | MoveTrackEndpointOp
        | LockTrackOp
        | LockViaOp
        | AddStitchingViaPatternOp
        | StitchPowerNetsOp
        | PlaceComponentOp
        | AnalyzeGapsOp
        | FillGapsOp
        | FillZonesOp
        | StripShortsOp
        | RemoveDanglingTracksOp
        | AutoRouteFreeroutingOp
        | GenerateBomOp
        | RunGateCheckOp
        | GateStatusOp
        | UpdateFromSchematicOp
        | SetConstraintsOp
        | GetConstraintsOp
        | PlaceComponentsSchOp
        | RouteWiresSchOp
        | ApplyLabelsSchOp
        | AutoLayoutSchOp
        | ReadBoardMetadataOp
        | SetBoardMetadataOp
        | SetBoardRevisionOp
        | DrcVendorOp
        | ListVendorDrcProfilesOp
        | BuildCreateOp
        | BuildListOp
        | BuildShowOp
        | BuildHandoffExportOp,
        Field(discriminator="op_type"),
    ]


# ---------------------------------------------------------------------------
# Schema export helper (D-04)
# ---------------------------------------------------------------------------


def get_operation_schema() -> dict:
    """Export the full JSON Schema for LLM consumption (D-04)."""
    return Operation.model_json_schema()


__all__ = [
    # Shared types
    "PositionSpec",
    "PropertySpec",
    "PinSpec",
    "TargetFile",
    # Validators
    "_SAFE_ID_PATTERN",
    "_UNSAFE_SEXPR_CHARS",
    "_validate_safe_identifier",
    "_validate_sexpr_safe_string",
    # Component ops
    "AddComponentOp",
    "RemoveComponentOp",
    "MoveComponentOp",
    "SnapComponentsToGridOp",
    "ModifyPropertyOp",
    "DuplicateComponentOp",
    "ArrayReplicateOp",
    # Net ops
    "AddNetOp",
    "RemoveNetOp",
    "RenameNetOp",
    # Reference ops
    "RenumberRefsOp",
    "ValidateRefsOp",
    "AnnotateOp",
    "SafeAnnotateOp",
    "CrossRefCheckOp",
    # Footprint ops
    "AssignFootprintOp",
    "SwapFootprintOp",
    "ValidateFootprintOp",
    "VerifyPinMapOp",
    "UpdateFootprintFromLibraryOp",
    # Wire ops
    "AddWireOp",
    "AddLabelOp",
    "AddPowerOp",
    "AddNoConnectOp",
    "AddJunctionOp",
    "AddDesignNoteOp",
    "ApplyFloorPlanOp",
    # Remove ops
    "RemoveWireOp",
    "RemoveLabelOp",
    "RemoveLabelsOp",
    "RemoveJunctionOp",
    "RemoveNoConnectOp",
    "RenameNetLabelOp",
    # Library ops
    "AddLibEntryOp",
    "RemoveLibEntryOp",
    "ListLibEntriesOp",
    # PCB ops
    "AddNetClassOp",
    "AddDesignRuleOp",
    "AddCopperZoneOp",
    "SetBoardOutlineOp",
    "AssignNetClassOp",
    "AutoRouteOp",
    "ImportSesOp",
    "AutoRouteManhattanOp",
    "AddTrackOp",
    "AddArcTrackOp",
    "AddViaOp",
    "DeleteTrackOp",
    "DeleteViaOp",
    "MoveTrackEndpointOp",
    "LockTrackOp",
    "LockViaOp",
    "AddStitchingViaPatternOp",
    "StitchPowerNetsOp",
    "PlaceComponentOp",
    "ModifyNetClassOp",
    "RemoveNetClassOp",
    "ListNetClassesOp",
    "ModifyDesignRuleOp",
    "RemoveDesignRuleOp",
    "ListDesignRulesOp",
    "ModifyProjectSettingsOp",
    "ModifyCopperZoneOp",
    "RemoveCopperZoneOp",
    "DeleteCopperZoneOp",
    "RefillCopperZoneOp",
    "ModifyZonePolygonOp",
    "AddKeepoutAreaOp",
    "AddZoneKeepoutOp",
    "RemoveKeepoutAreaOp",
    "MoveFootprintOp",
    "RouteDiffPairOp",
    "MatchLengthsOp",
    "NetLengthPair",
    "AnalyzeSplitPlaneOp",
    "FixSilkscreenOverCopperOp",
    # Placement ops
    "AutoPlaceOp",
    "ExportPositionsOp",
    "ImportPositionsOp",
    "AutoPlaceZonedOp",
    "ZoneDefinition",
    # Validation ops
    "ValidatePowerNetsOp",
    "ValidateSchematicOp",
    "PrePcbSchematicGateOp",
    "RunGateCheckOp",
    "GateStatusOp",
    "ParseErcOp",
    "ExtractViolationPositionsOp",
    "ValidateHlabelsOp",
    # Create ops
    "CreateSchematicOp",
    "CreatePcbOp",
    "CreateProjectOp",
    "CreateSymbolOp",
    "EmbedSymbolOp",
    "CreateFootprintOp",
    "FootprintPadSpec",
    # Repair ops
    "RepairSchematicOp",
    "ConvertKicad6To10Op",
    "ConvertToSkidlOp",
    "ConvertFromSkidlOp",
    "SnapToGridOp",
    "AddPowerFlagOp",
    "RebuildRootSheetOp",
    "SwapSymbolOp",
    "UpdateSymbolsFromLibraryOp",
    "FixShortedNetsOp",
    "FixPinTypeMismatchesOp",
    "FixNetShortOp",
    "PlaceMissingUnitsOp",
    "PlaceAndWirePowerUnitsOp",
    "RemoveDanglingWiresOp",
    "BreakWireShortsOp",
    "ResolveShortedNetsOp",
    "PlaceNetLabelsOp",
    "ErcAutoFixOp",
    "ErcAutoFixHierarchicalOp",
    # Sheet ops
    "AddSheetOp",
    "AddSheetPinOp",
    "NavigateSheetsOp",
    # Query ops
    "QueryConnectivityOp",
    # Cross-file ops
    "PropagateSymbolChangeOp",
    "UpdatePcbFromSchematicOp",
    "RepopulatePcbFromSchematicOp",
    "SafeSyncPcbFromSchematicOp",
    "RebuildPcbNetsOp",
    # Schematic routing ops
    "ResolvePinPositionsOp",
    "DetectRoutingCollisionsOp",
    "DetectPinOverlapsOp",
    "ConnectPinsOp",
    "BatchConnectOp",
    "RegenerateWiringOp",
    "PinRef",
    "CollisionZone",
    "NetDef",
    "GlobalLabelSpec",
    # Schematic intelligence ops
    "ExtractNetsOp",
    "DetectNetConflictsOp",
    "DetectNetShortsOp",
    "SuggestNetNamesOp",
    "InferConnectivityOp",
    "AnalyzeGroundTopologyOp",
    "TraceNetFromLabelOp",
    # ERC smart ops
    "ClassifyViolationsOp",
    "DiagnoseViolationsOp",
    # Readability ops
    "ReviewSchematicOp",
    "CritiqueSchOp",
    # Gap analysis ops
    "AnalyzeGapsOp",
    "FillGapsOp",
    "FillZonesOp",
    "StripShortsOp",
    "RemoveDanglingTracksOp",
    "AutoRouteFreeroutingOp",
    "GenerateBomOp",
    # PCB transfer ops
    "UpdateFromSchematicOp",
    # Constraint ops
    "SetConstraintsOp",
    "GetConstraintsOp",
    # Phase 108 autolayout ops (D-04)
    "PlaceComponentsSchOp",
    "RouteWiresSchOp",
    "ApplyLabelsSchOp",
    "AutoLayoutSchOp",
    # Phase 205 board metadata ops (META-01, META-02, META-03)
    "ReadBoardMetadataOp",
    "SetBoardMetadataOp",
    "SetBoardRevisionOp",
    # Phase 206 vendor DRC ops (DRC-01, DRC-08)
    "DrcVendorOp",
    "ListVendorDrcProfilesOp",
    # Phase 207 build system ops (BUILD-01, BUILD-07, BUILD-08)
    "BuildCreateOp",
    "BuildListOp",
    "BuildShowOp",
    # Phase 208 manufacturer handoff ops (HANDOFF-01, HANDOFF-08)
    "BuildHandoffExportOp",
    # Union and helpers
    "Operation",
    "get_operation_schema",
]
