bretbouchard/kicad-agent/src/volta/circuit_ir/skidl_circuit.py

"""Phase 156 Wave 1: KiCad→SKIDL read-back — build_circuit core.

Composes SchematicIR + extract_nets into a live skdl.Circuit with
pin-name-based wiring (Code-L1 representation). This is the foundational
new capability — the one direction that did not exist.

Pipeline:
  1. Parse the .kicad_sch via the native parser (for component metadata).
  2. Extract net topology via extract_nets (the proven connectivity path).
  3. Build skidl.Part objects for each non-power component.
  4. Build skidl.Net objects and wire pins via the += operator.
  5. Return (circuit, circuit_ir) where circuit_ir is the immutable IR.
"""

from __future__ import annotations

import logging
from pathlib import Path

from volta.circuit_ir.types import (
    CircuitIR,
    NetDescriptor,
    PartDescriptor,
    PinRef,
)

logger = logging.getLogger(__name__)

# Power symbol detection: lib_id prefix or reference pattern.
_POWER_PREFIX = "power:"
_POWER_REF_PREFIXES = ("#PWR", "#FLG")


def build_circuit(
    sch_path: Path | str,
    *,
    symbol_dir: str | None = None,
) -> tuple[object, CircuitIR]:
    """Build a skidl.Circuit from a KiCad schematic file.

    This is the KiCad→SKIDL read-back path. It reads components and nets
    from a .kicad_sch and constructs a live skidl.Circuit with pin-name-
    based wiring.

    Args:
        sch_path: Path to the .kicad_sch file.
        symbol_dir: Optional KICAD_SYMBOL_DIR override.

    Returns:
        Tuple of (skidl.Circuit, CircuitIR). The Circuit is a live skidl
        object that can generate netlists, run ERC, etc. The CircuitIR is
        the immutable intermediate representation for downstream phases.

    Raises:
        FileNotFoundError: If the schematic doesn't exist.
        RuntimeError: If KICAD_SYMBOL_DIR can't be resolved.
    """
    from volta.circuit_ir import _ensure_skidl_env
    _ensure_skidl_env(symbol_dir)

    import skidl
    from volta.parser.pcb_native_parser import NativeParser
    from volta.schematic_routing.net_extractor import extract_nets

    sch_path = Path(sch_path)
    if not sch_path.exists():
        raise FileNotFoundError(f"Schematic not found: {sch_path}")

    # Step 1: Extract net topology using the proven extract_nets path.
    nets_result = extract_nets(sch_path, include_positions=False)
    nets_data: dict[str, list[dict]] = nets_result.get("nets", {})

    # Step 2: Extract components from the raw schematic content.
    content = sch_path.read_text(encoding="utf-8")
    components = _extract_components(content)

    diagnostics: list[str] = []

    # Step 3: Separate power symbols from real components.
    power_nets: set[str] = set()
    real_parts: list[PartDescriptor] = []

    for comp in components:
        if comp.is_power:
            power_nets.add(comp.value)
        else:
            real_parts.append(comp)

    # Step 4: Build the skidl.Circuit.
    circuit = skidl.Circuit()
    circuit.name = sch_path.stem

    # Use the circuit context so all Part/Net creations are scoped.
    with circuit:
        # Create Part objects.
        part_objects: dict[str, object] = {}
        for pd in real_parts:
            try:
                lib, name = pd.lib_id.split(":", 1) if ":" in pd.lib_id else ("Device", pd.lib_id)
                kwargs = {"value": pd.value}
                if pd.footprint:
                    kwargs["footprint"] = pd.footprint
                p = skidl.Part(lib, name, **kwargs)
                # Set the reference explicitly.
                p.ref = pd.reference
                part_objects[pd.reference] = p
            except Exception as e:
                diagnostics.append(
                    f"Failed to create Part for {pd.reference} ({pd.lib_id}): {e}"
                )
                # Fallback: create a generic connector.
                try:
                    p = skidl.Part("Connector_Generic", "Conn_01x02",
                                   value=pd.value, footprint=pd.footprint or "")
                    p.ref = pd.reference
                    part_objects[pd.reference] = p
                    diagnostics.append(
                        f"Fallback: {pd.reference} → Conn_01x02"
                    )
                except Exception:
                    diagnostics.append(
                        f"Complete failure for {pd.reference} — omitted from circuit"
                    )

        # Create Net objects and wire pins.
        net_descriptors: list[NetDescriptor] = []
        for net_name, pins in nets_data.items():
            is_power = net_name in power_nets or _is_power_net_name(net_name)

            # Create the net.
            net = skidl.Net(net_name)

            # Wire each pin.
            pin_refs: list[PinRef] = []
            for pin_info in pins:
                ref = pin_info.get("ref", "")
                pin_num = str(pin_info.get("pin_number", ""))
                pin_name = pin_info.get("pin_name", pin_num)
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
